Docredstein/TIPE_TMD/DM.pdf

# DM TIPE

BOCQUILLON No´e,FRAMBOURT Mate¨ıs

27 septembre 2022

Titre du TIPE : Mod´elisation et Simulation d’un amortisseur harmonique dans le cadre de la pr´evention sismique

## 1 Objectif du TIPE

Le but de ce TIPE est de mod´eliser un immeuble puis de concevoir un amortisseur harmonique pour limiter

1
