Docredstein/TIPE_TMD/Analyse finale basse amplitude/Image/coup_de_vent.pdf

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

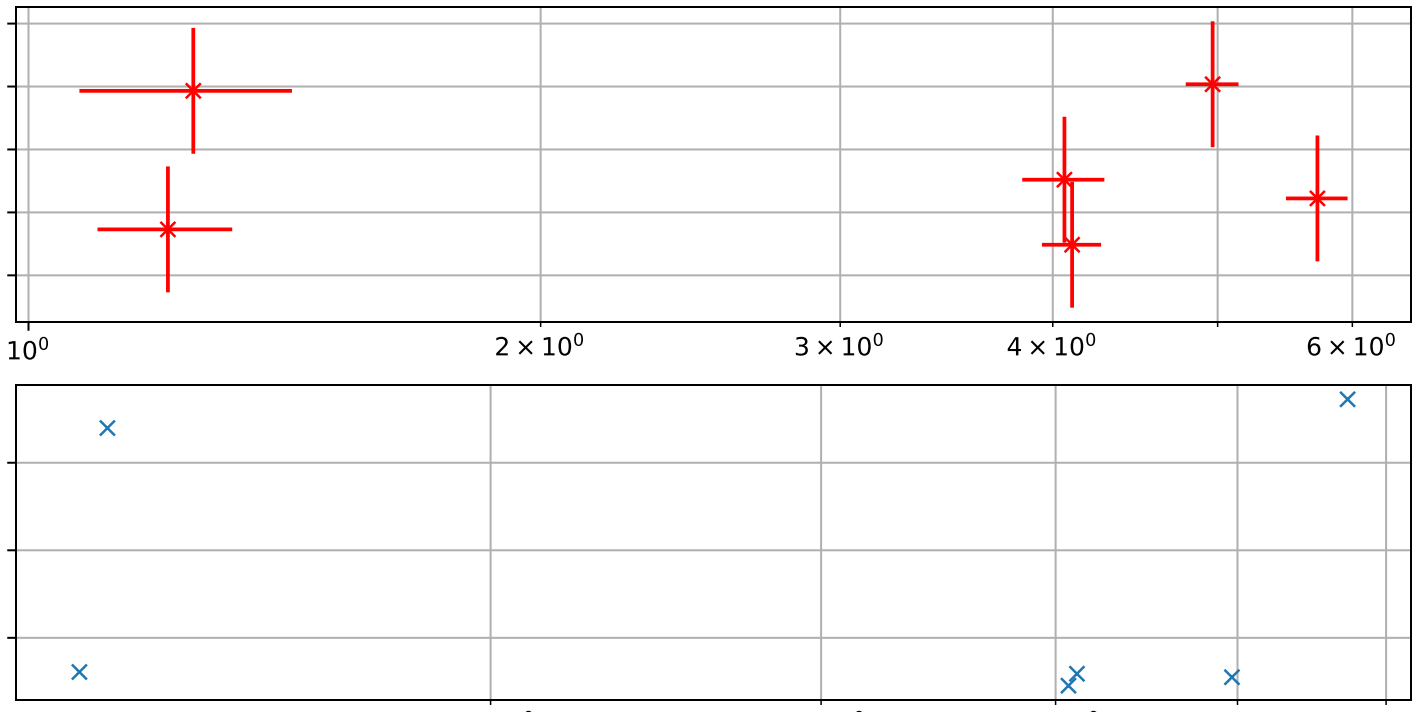
[picture p38: figure]
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
