Docredstein/TIPE_TMD/Analyse finale basse amplitude/Image/masse_en_bas_(9.4gcm)_de__100g.pdf

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

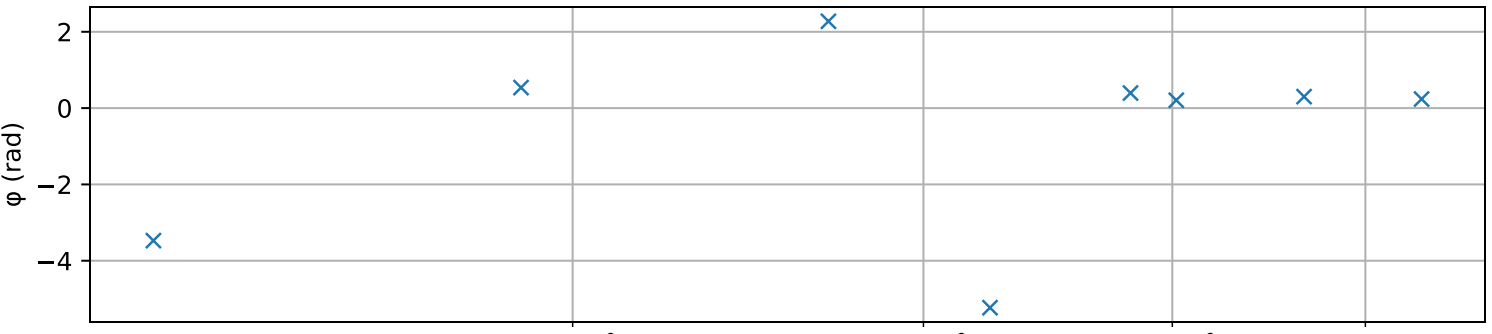
[picture p39: figure]
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
