Docredstein/TIPE_TMD/Analyse finale basse amplitude/Image/masse_à_3_cm_de_l'axe_de_100g.pdf

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

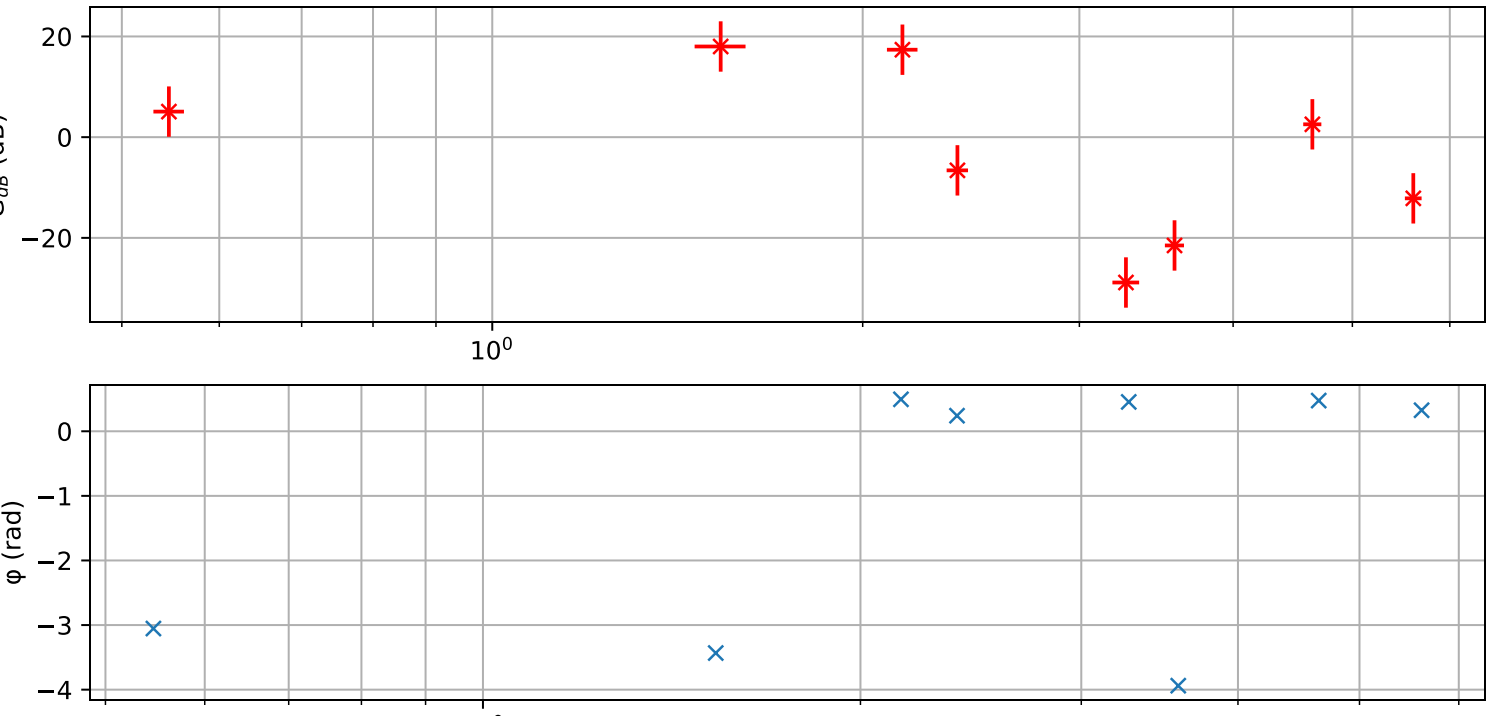
[picture p40: figure]
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
