Docredstein/TIPE_TMD/Analyse finale basse amplitude/Image/masse_à_5,5_cm_de_l'axe_de_73,3_g.pdf

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

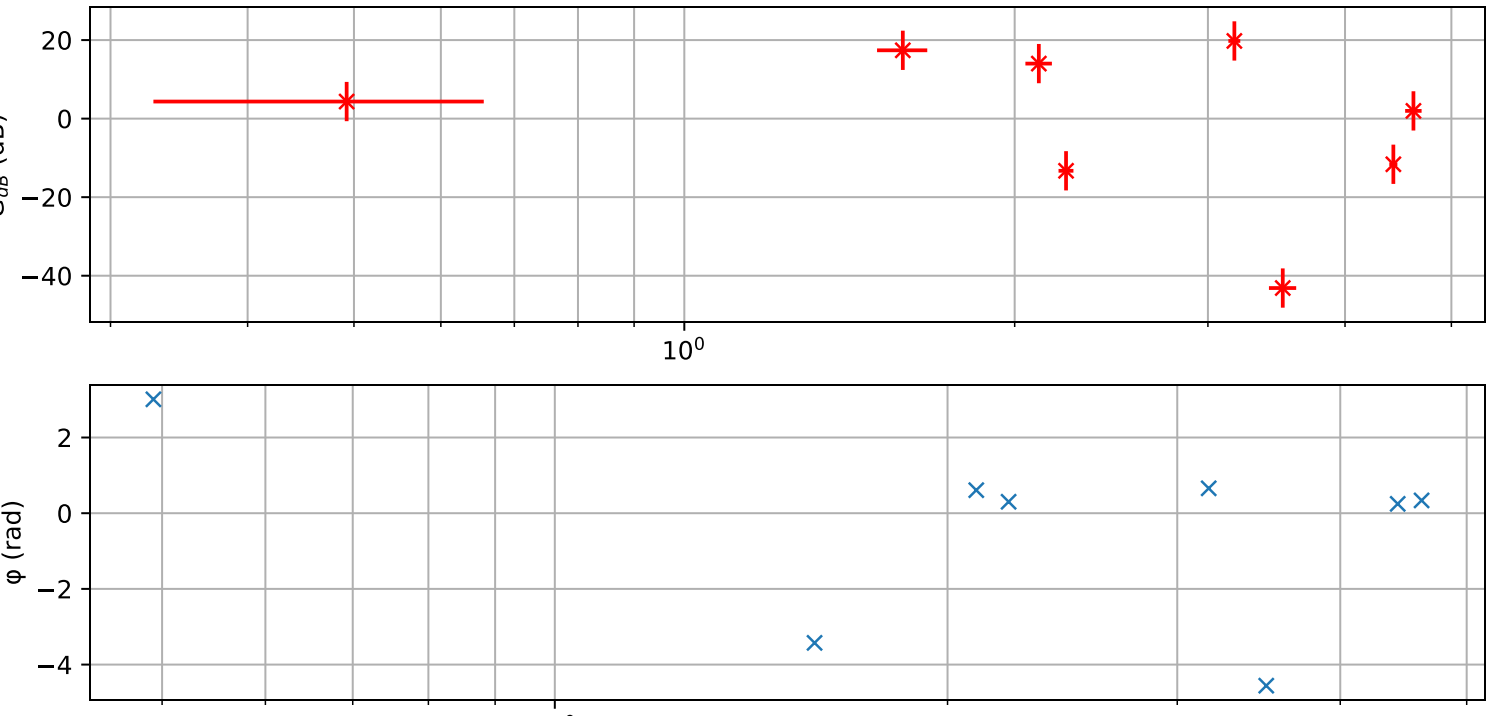
[picture p41: figure]
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
