Docredstein/TIPE_TMD/Analyse finale basse amplitude/Image/masse_à_8cm_de_73,3_g.pdf

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

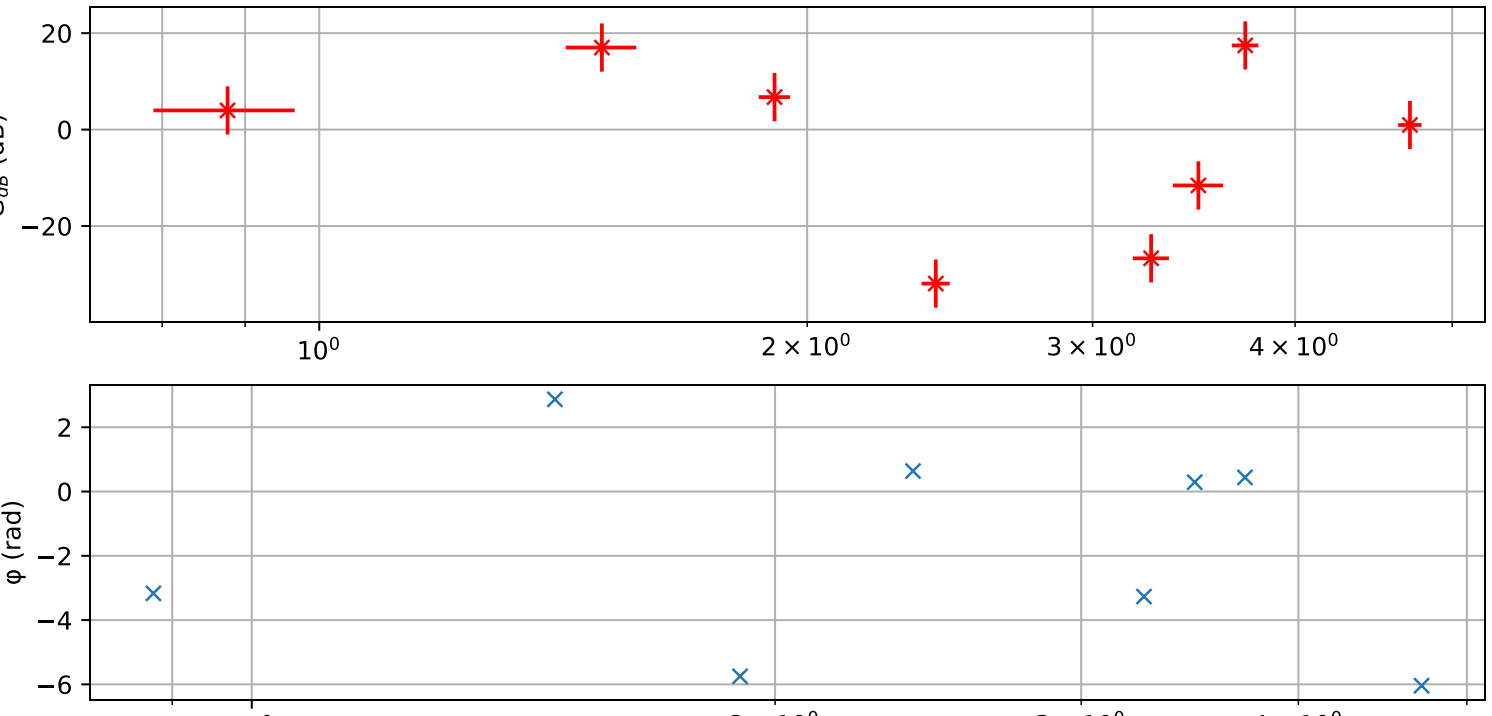
[picture p42: figure]
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
