Docredstein/TIPE_TMD/Analyse finale basse amplitude/Image/masse_à_9.4_cm_de_73,3g_de_l'axe.pdf

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

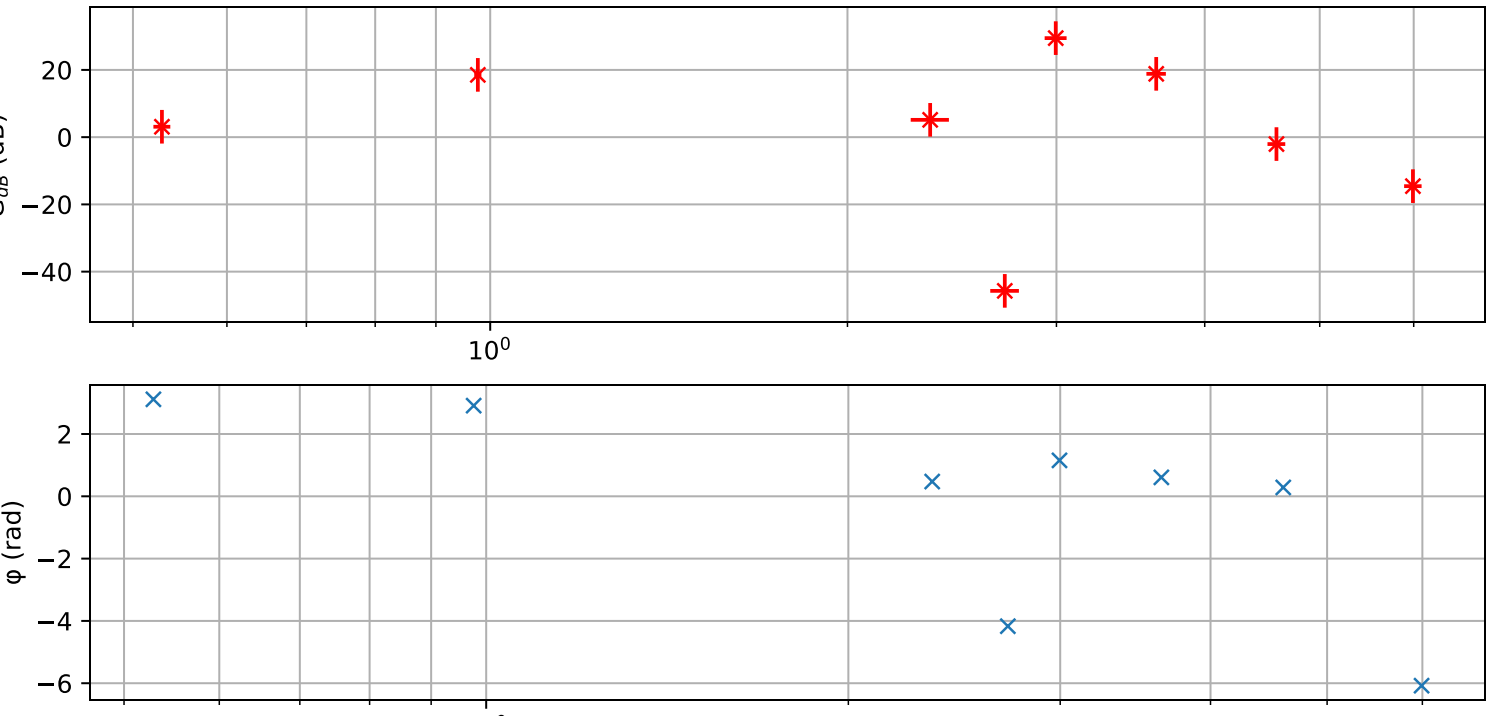
[picture p43: figure]
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
