Docredstein/TIPE_TMD/Analyse finale basse amplitude/Image/sans_pendule.pdf

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

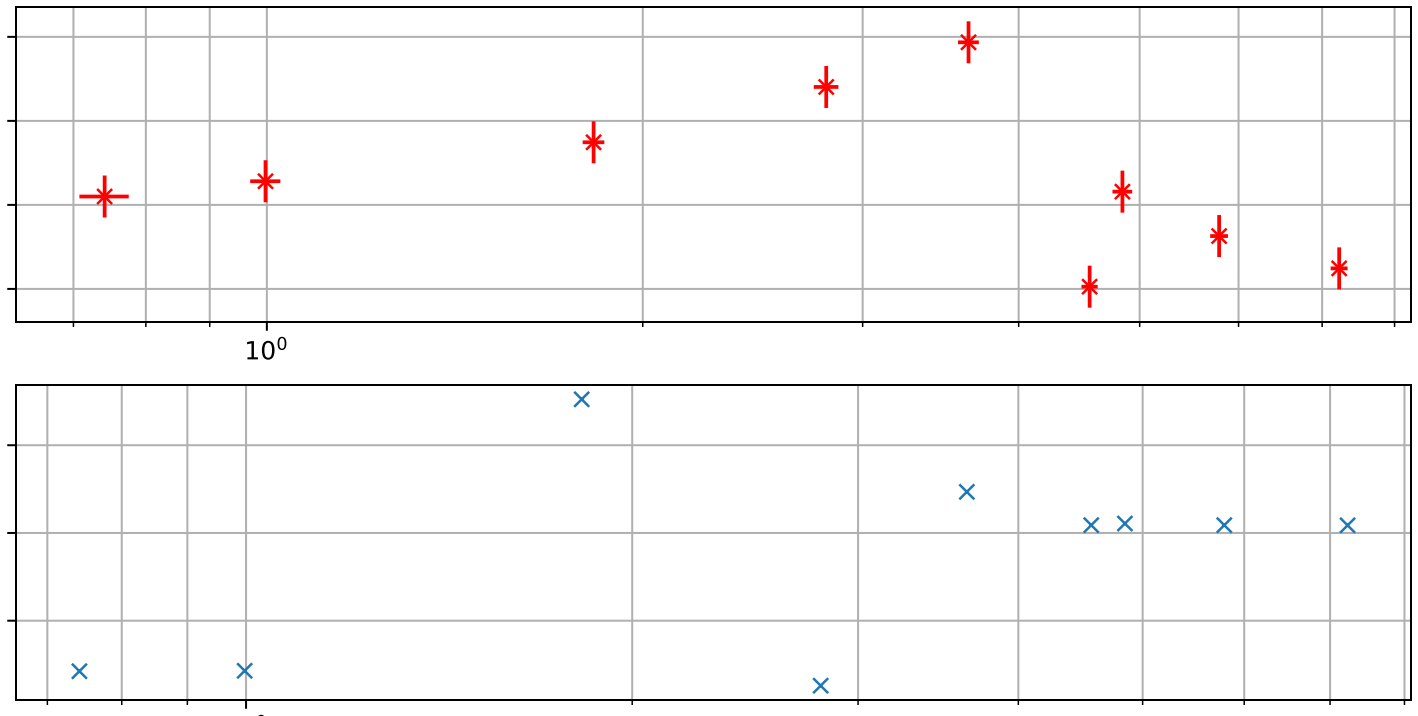
[picture p45: figure]
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
