Docredstein/TIPE_TMD/Beamer/Image/masse_à_8cm_de_73,3_g.pdf

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

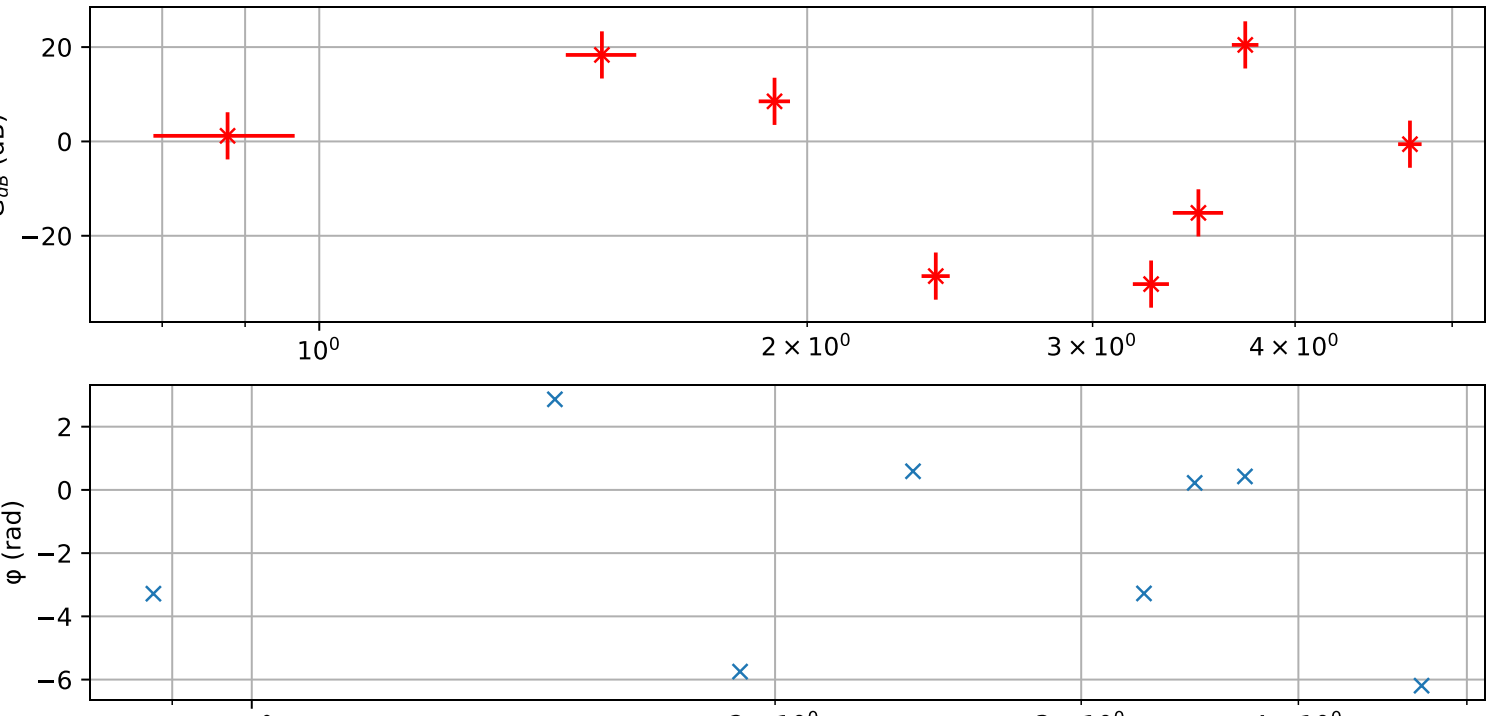
[picture p47: figure]
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
