Docredstein/TIPE_TMD/Beamer/Image/pendule_à_5_cm_de_l'axe_,_100g.pdf

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

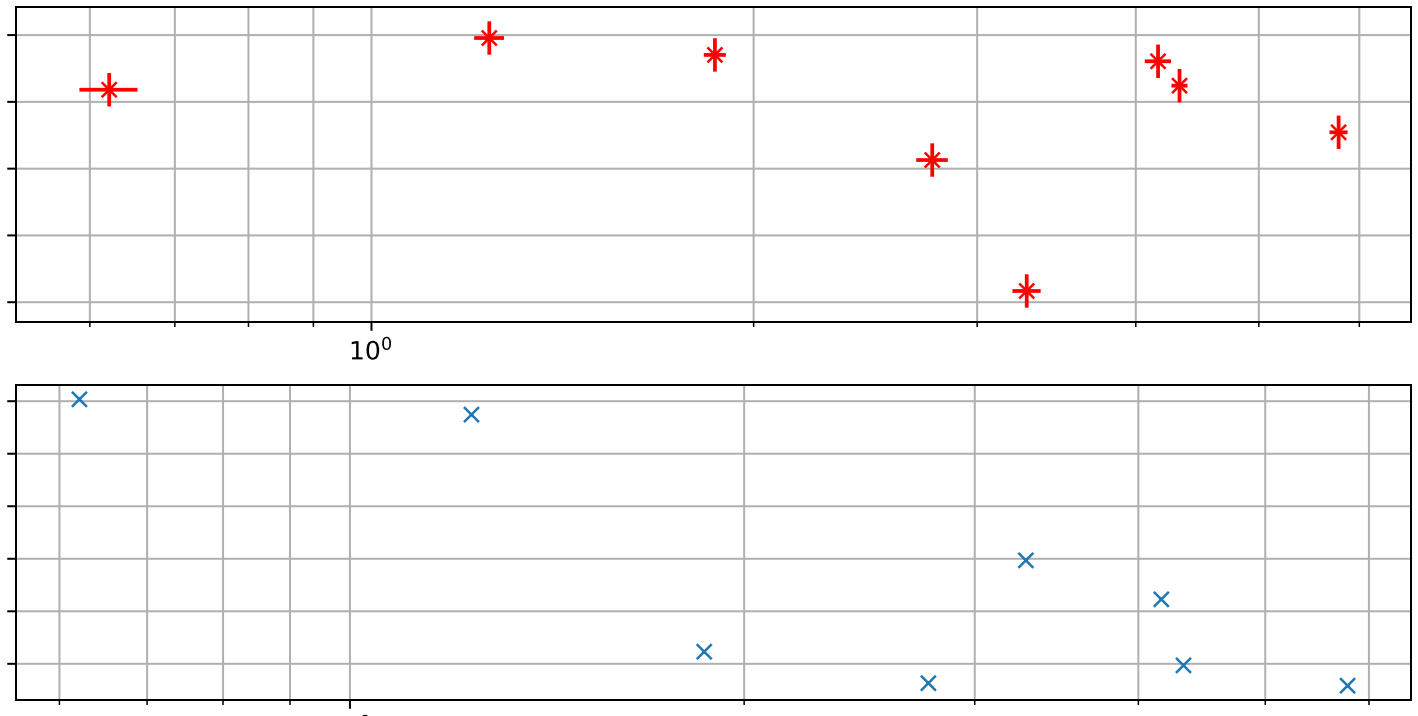
[picture p48: figure]
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
