Docredstein/TIPE_TMD/Analyse/Image/pendule_1_masse_au_plus_bas.pdf

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

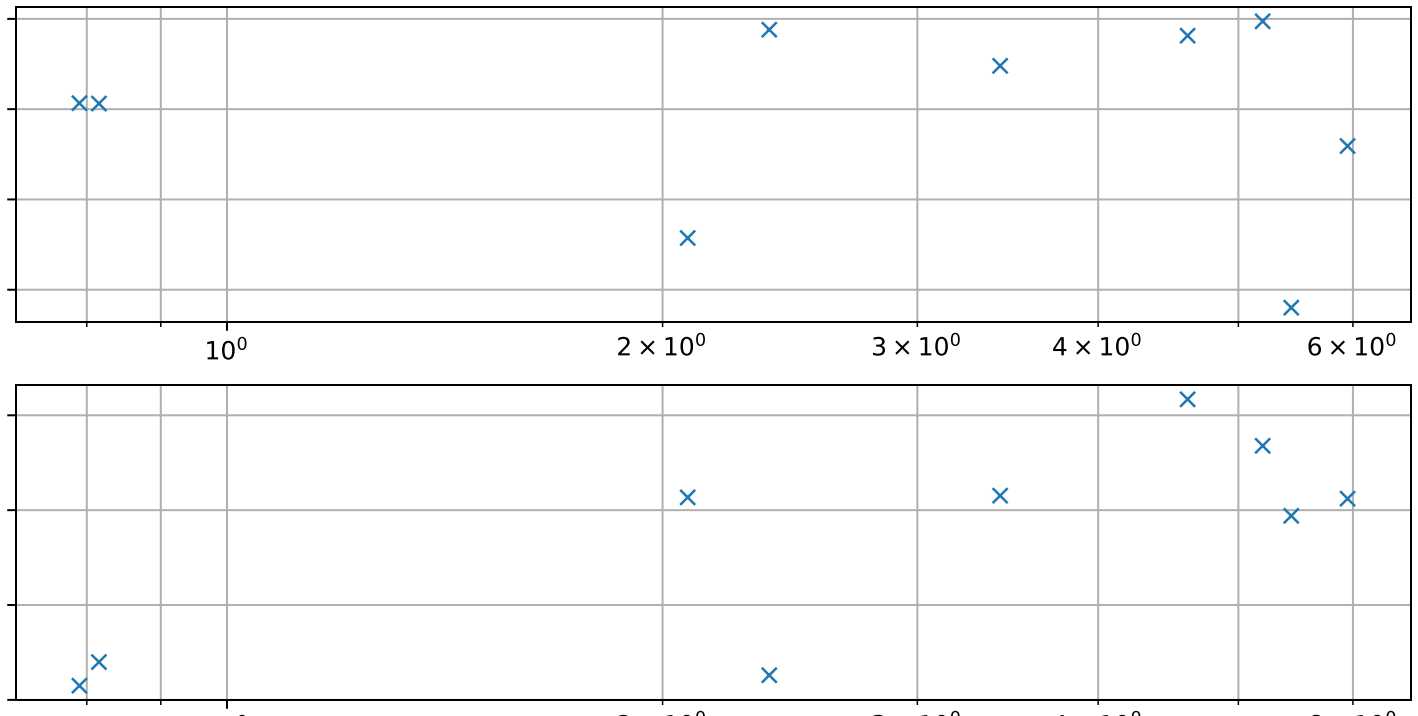
[picture p50: figure]
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
