Docredstein/TIPE_TMD/Analyse/Image/pendule_7_mm_faible_amplitude.pdf

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

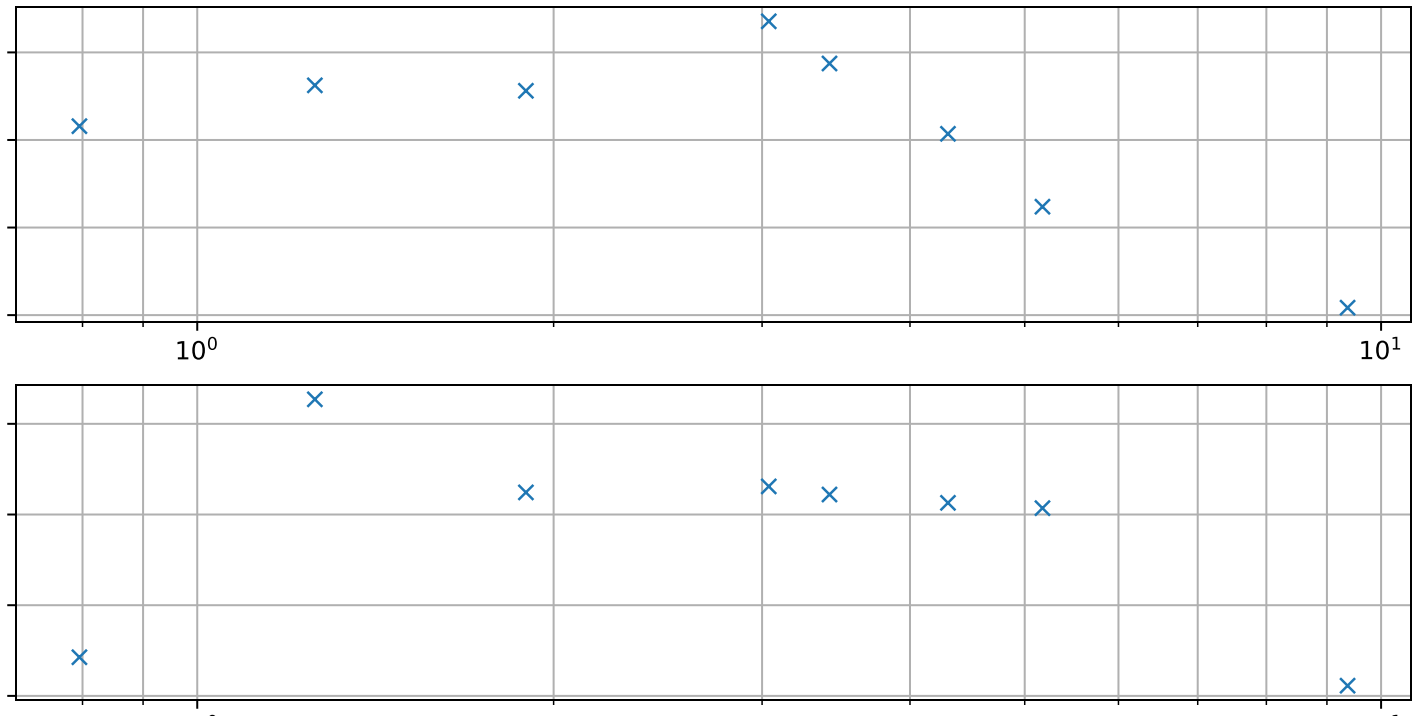
[picture p52: figure]
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
