Docredstein/TIPE_TMD/Analyse/Image/pendule_au_plus_bas_faible_amplitude.pdf

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

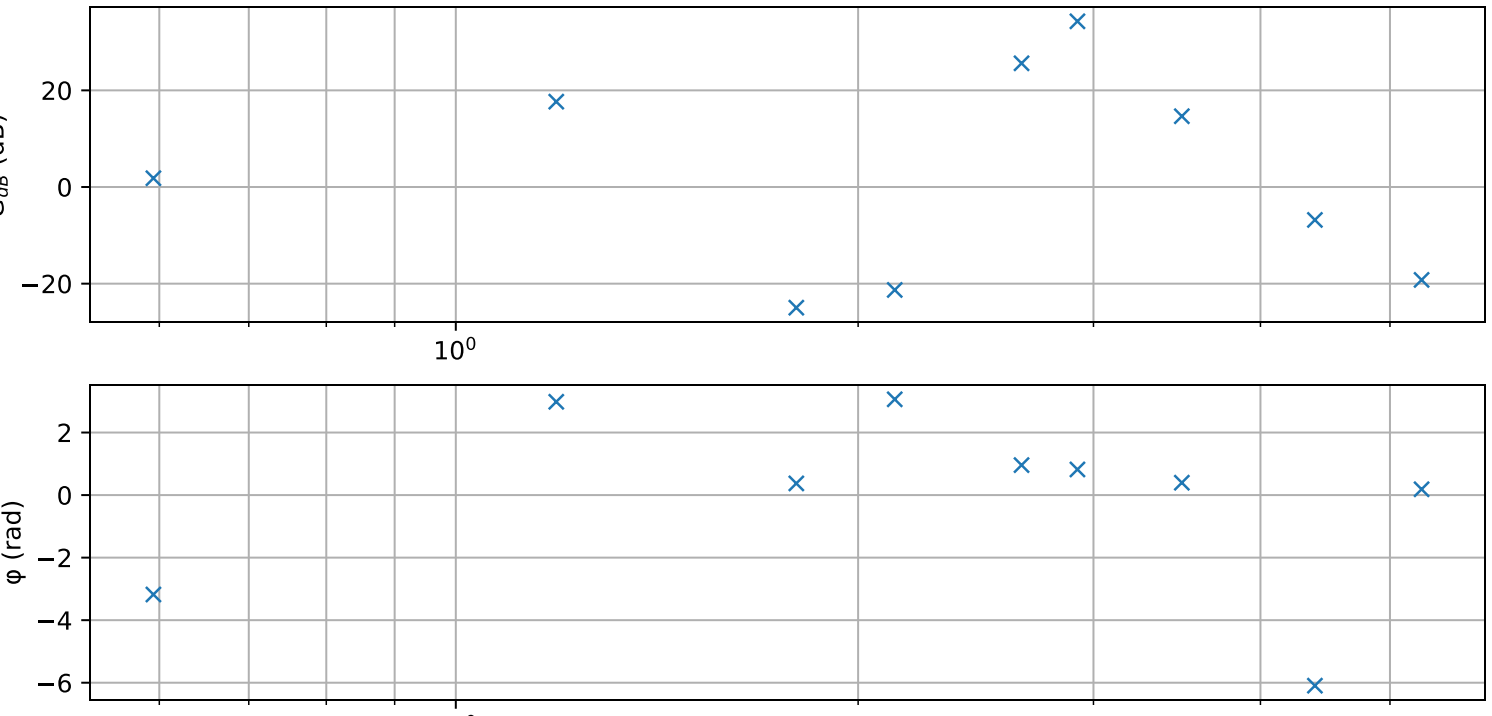
[picture p53: figure]
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
