Docredstein/TIPE_TMD/Analyse/Image/penduleb_7mm_sans_pendule_faible_amplitude.pdf

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

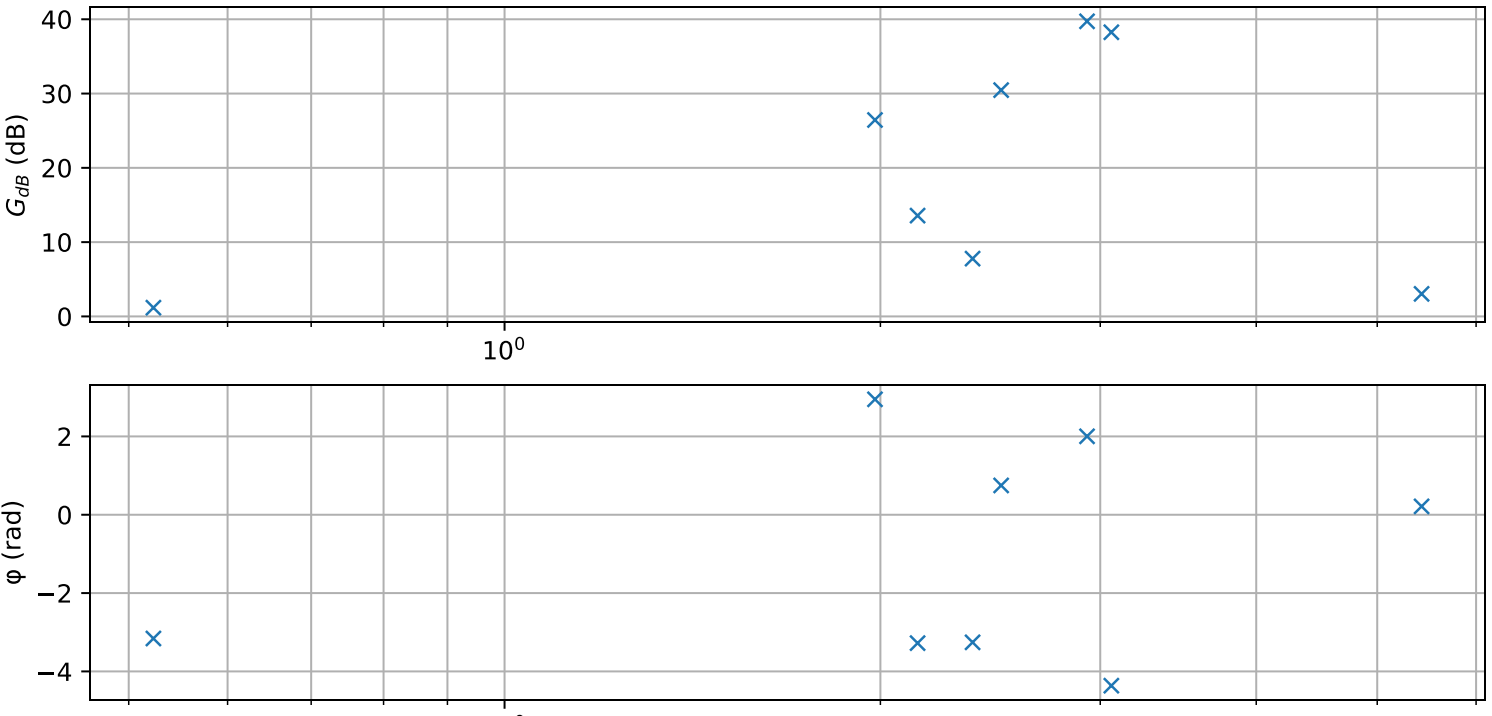
[picture p54: figure]
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
