Docredstein/TIPE_TMD/Analyse/Image/Sans_masse,_tige_seule_faible_amplitude.pdf

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

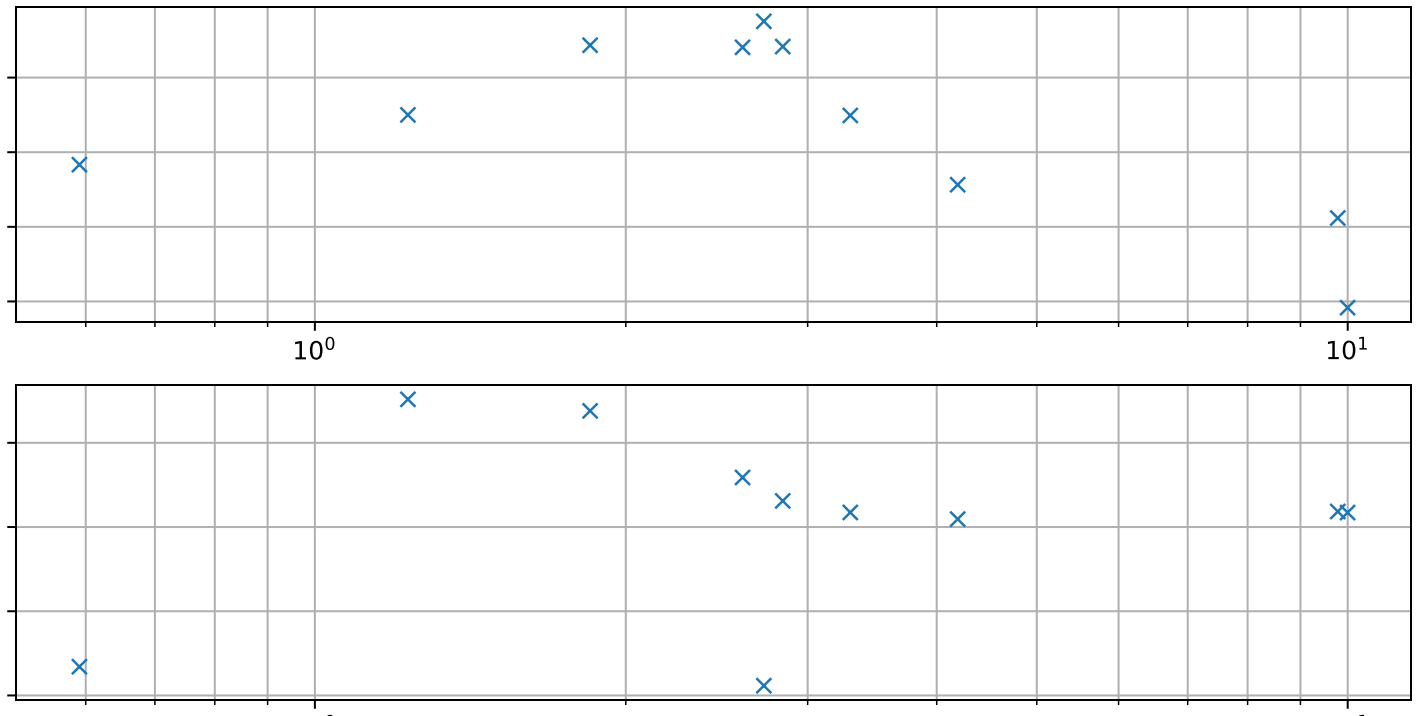
[picture p55: figure]
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
