Docredstein/TIPE_TMD/Analyse/Image/masse_en_haut_faible_amplitude_norme.pdf

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

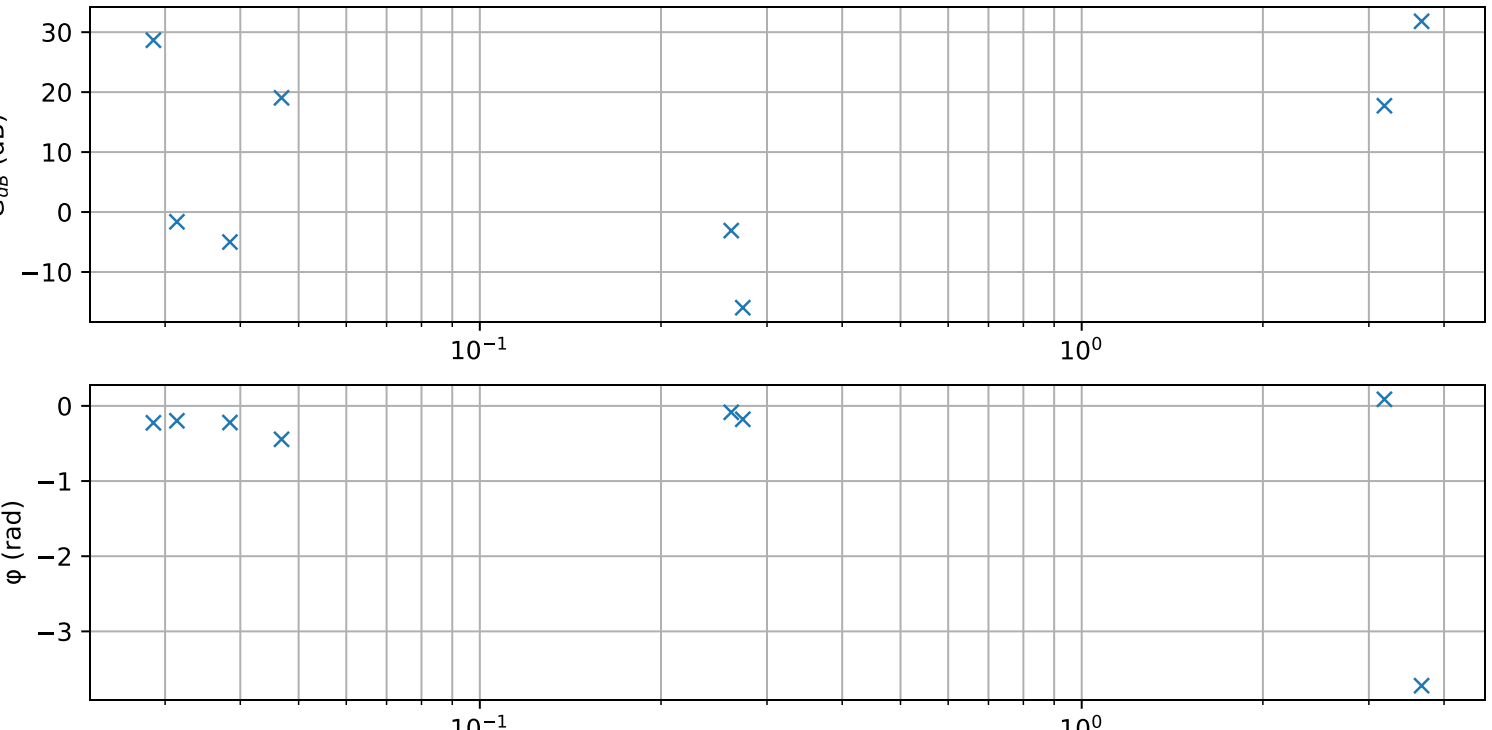
[picture p56: figure]
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
