Docredstein/TIPE_TMD/Analyse/Image/pendule_7_cm_du_haut_pendule_fixe_axe_norme.pdf

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

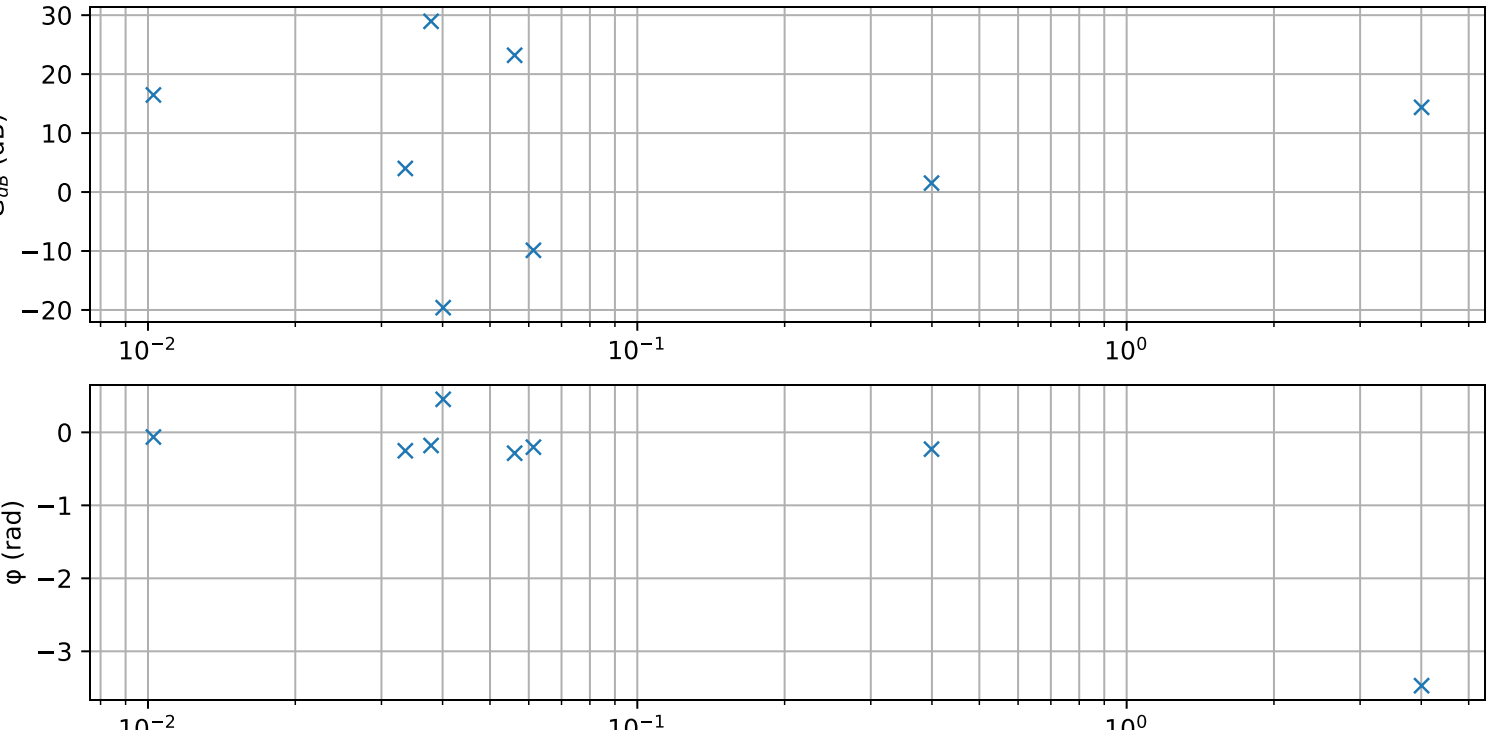
[picture p58: figure]
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
