Docredstein/TIPE_TMD/Analyse/Image/pendule_au_plus_bas_faible_amplitude_norme.pdf

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

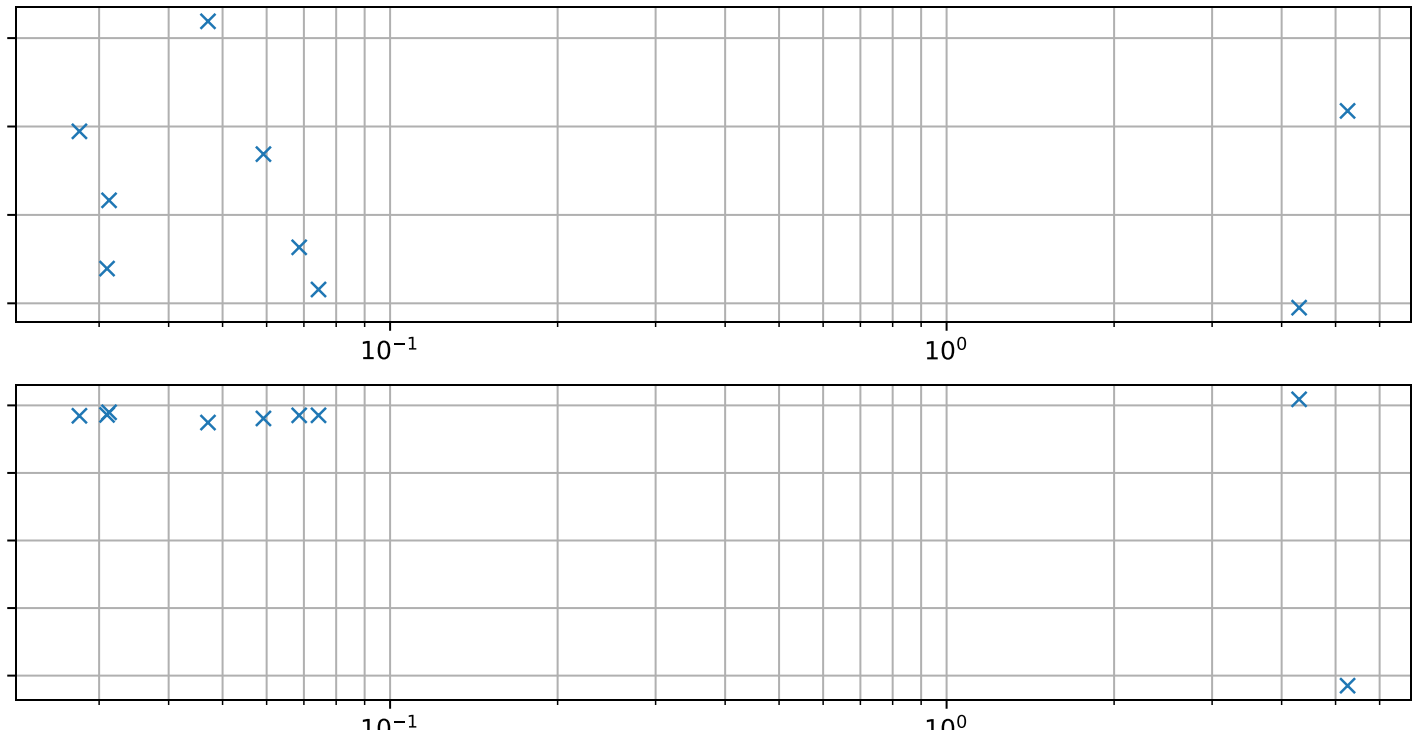
[picture p60: figure]
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
