Docredstein/TIPE_TMD/Analyse/Image/penduleb_7mm_sans_pendule_faible_amplitude_norme.pdf

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

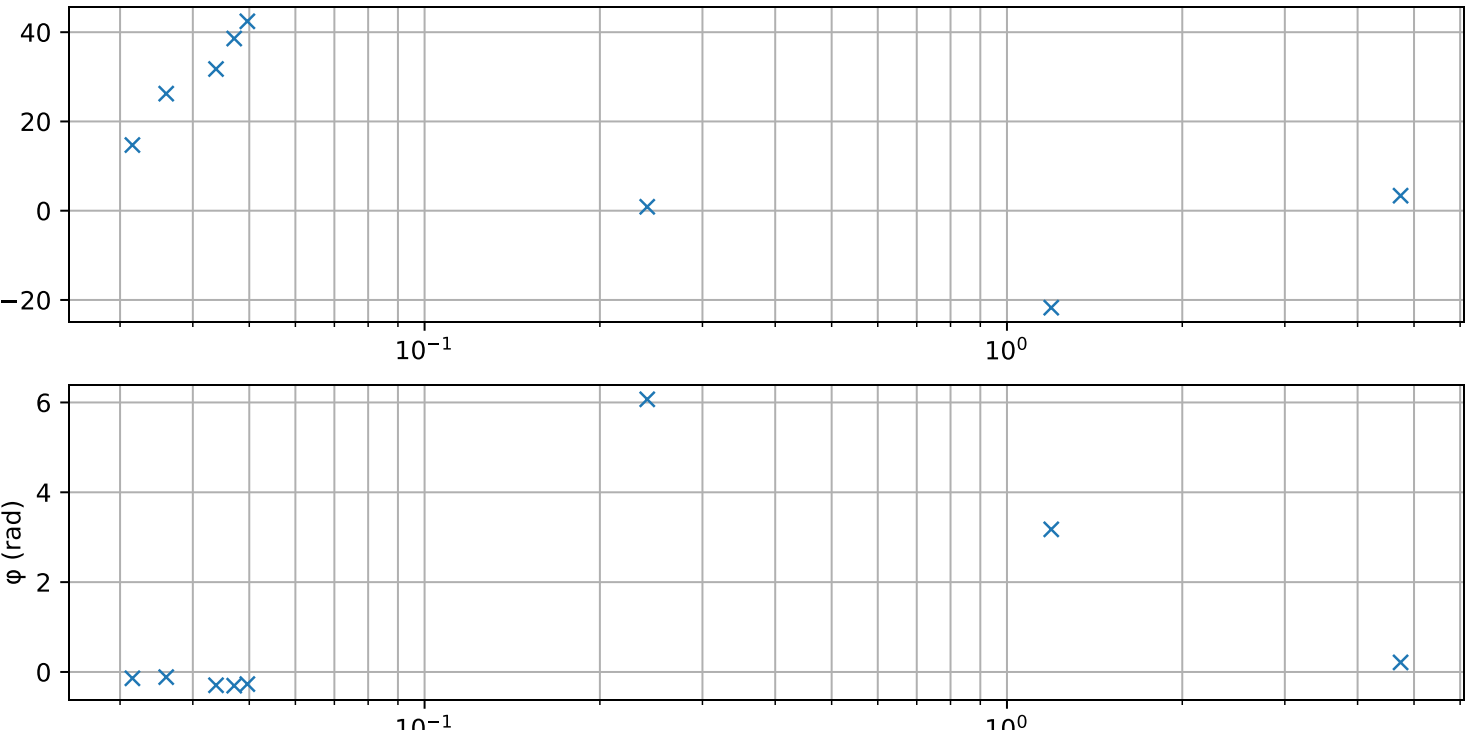
[picture p61: figure]
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
