Docredstein/TIPE_TMD/Analyse/Image/Sans_masse,_tige_seule_faible_amplitude_norme.pdf

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

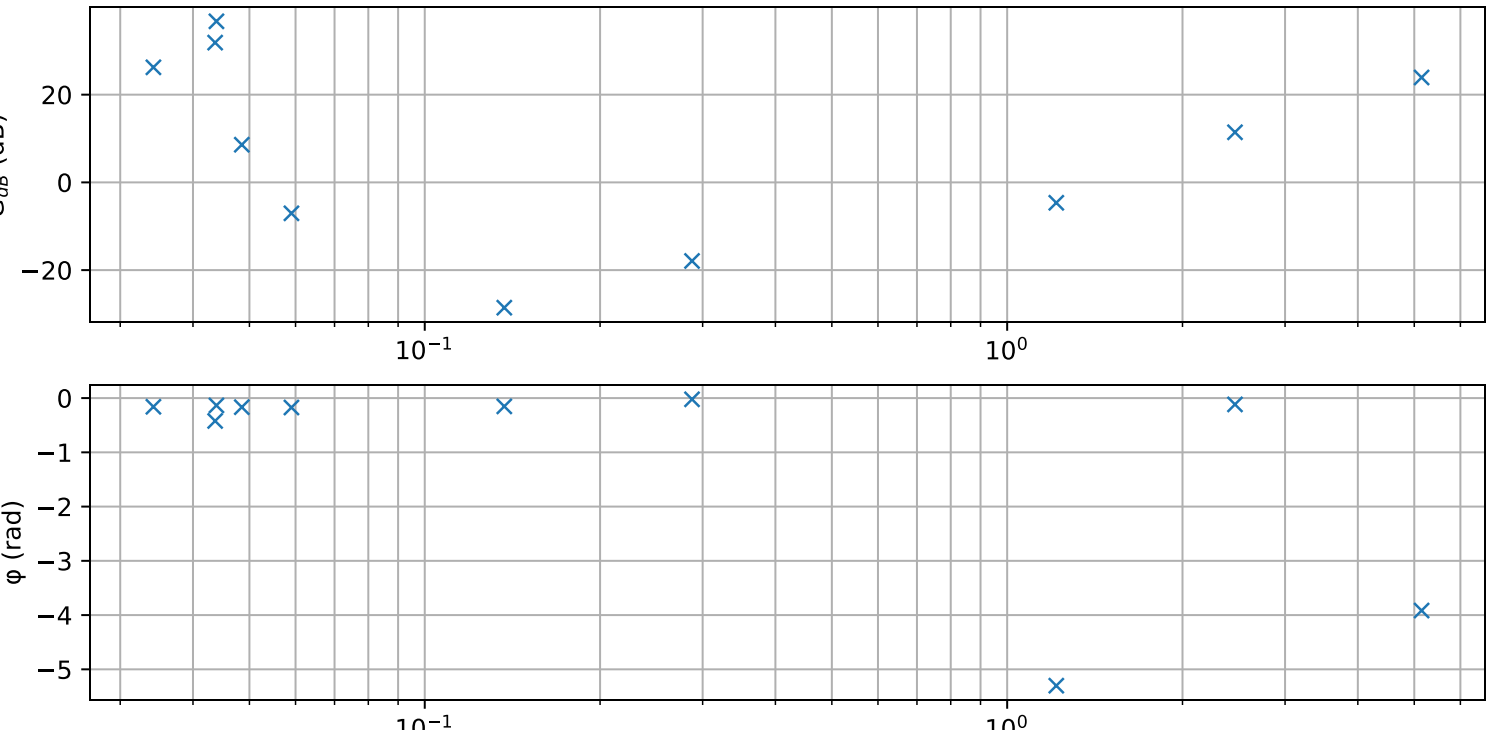
[picture p62: figure]
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
