Docredstein/TIPE_TMD/Analyse/Image/Bode a Vide/0.3Hz.png

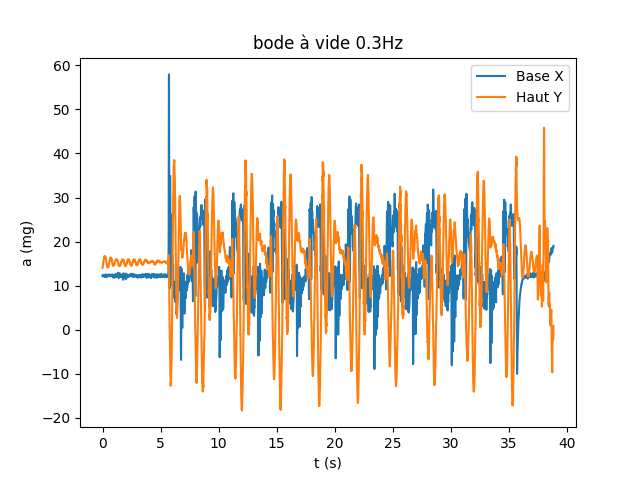
Analyse/Image/Bode a Vide/0.3Hz.png
