Docredstein/TIPE_TMD/Analyse/Image/Bode a Vide/0.5Hz.png

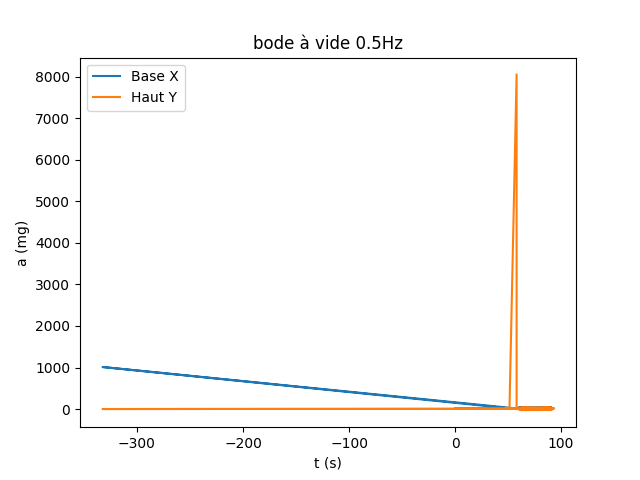
Analyse/Image/Bode a Vide/0.5Hz.png
