Docredstein/TIPE_TMD/Analyse/Image/Bode a Vide/1.5Hz.png

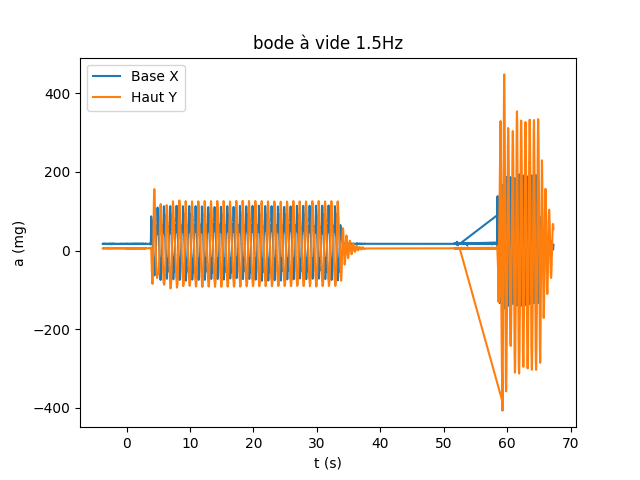
Analyse/Image/Bode a Vide/1.5Hz.png
