Docredstein/TIPE_TMD/Analyse/Image/Bode a Vide/1.6Hz.png

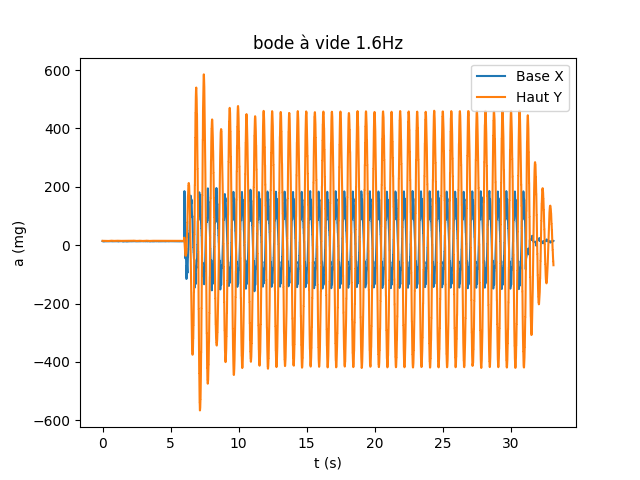
Analyse/Image/Bode a Vide/1.6Hz.png
