Docredstein/TIPE_TMD/Analyse/Image/Bode a Vide/1.7Hz.png

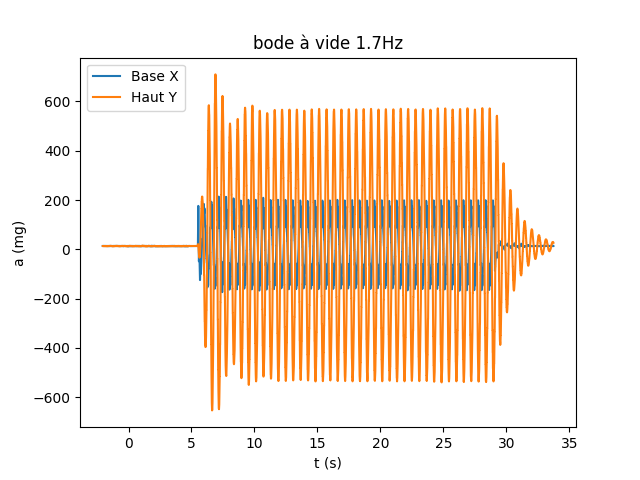
Analyse/Image/Bode a Vide/1.7Hz.png
