Docredstein/TIPE_TMD/Analyse/Image/Bode a Vide/2.5Hz.png

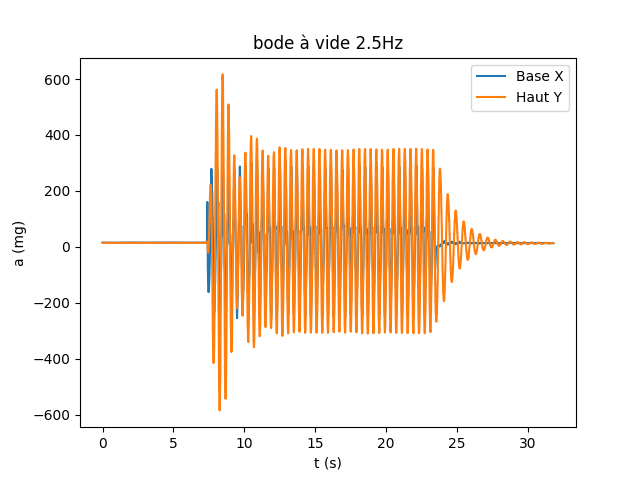
Analyse/Image/Bode a Vide/2.5Hz.png
