Docredstein/TIPE_TMD/Analyse/Image/Bode a Vide/3.5Hz.png

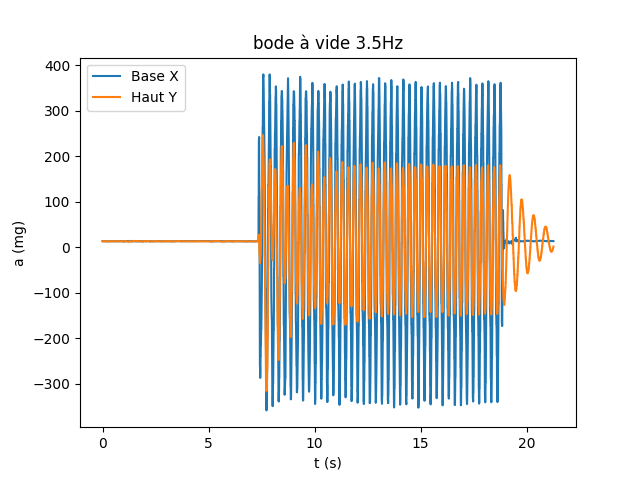
Analyse/Image/Bode a Vide/3.5Hz.png
