Docredstein/TIPE_TMD/Analyse/Image/Bode a Vide/4Hz.png

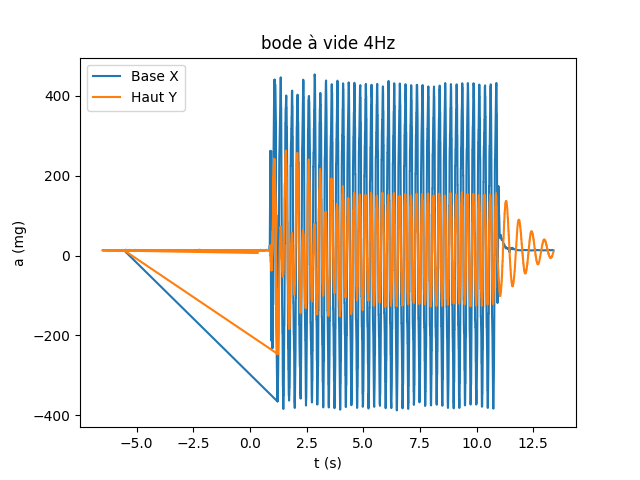
Analyse/Image/Bode a Vide/4Hz.png
