Docredstein/TIPE_TMD/Analyse/Image/Bode_a_vide.png

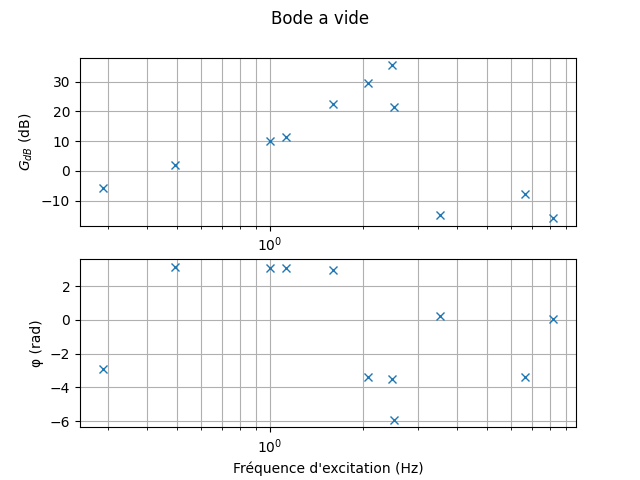
Analyse/Image/Bode_a_vide.png
