Docredstein/TIPE_TMD/Analyse/Image/masse en haut faible amplitude/0.5Hz.png

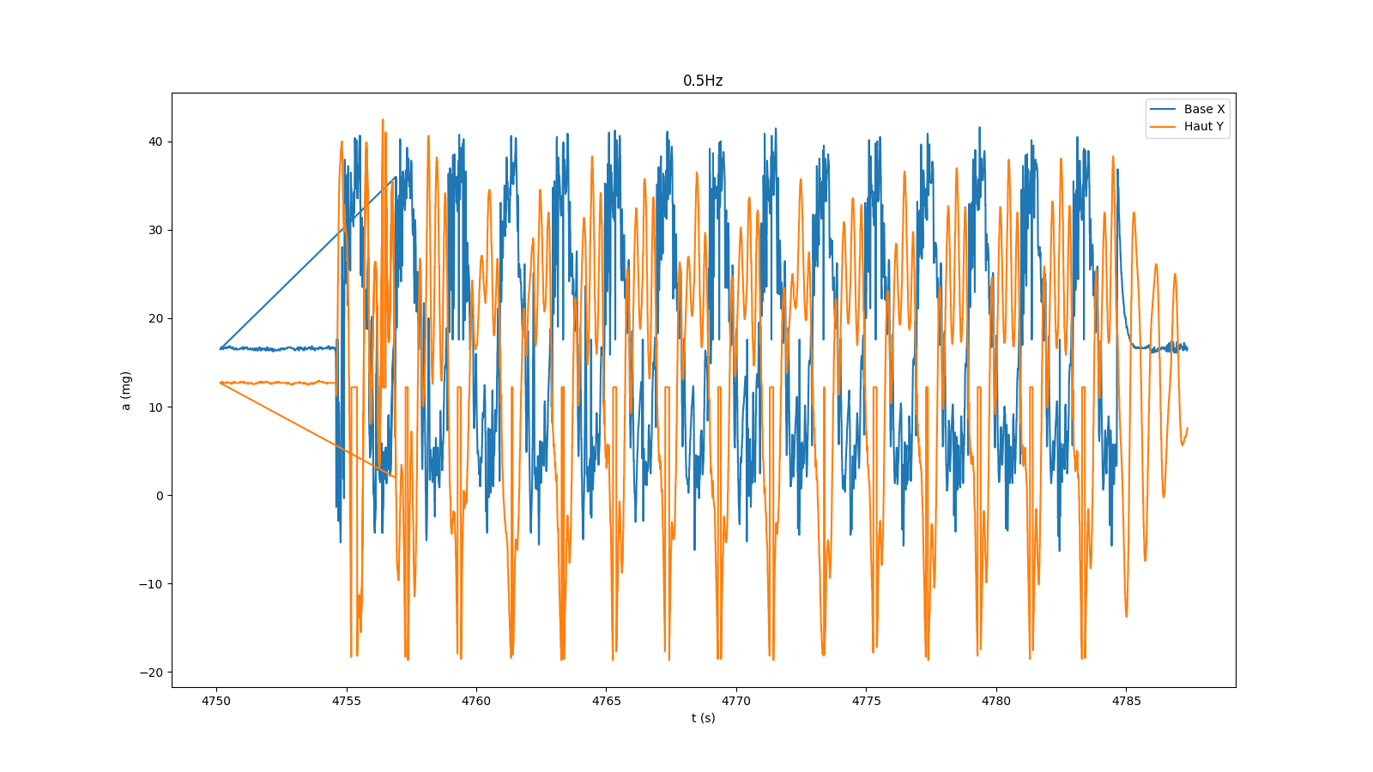
Analyse/Image/masse en haut faible amplitude/0.5Hz.png
