Docredstein/TIPE_TMD/Analyse/Image/masse en haut faible amplitude/1 hz.png

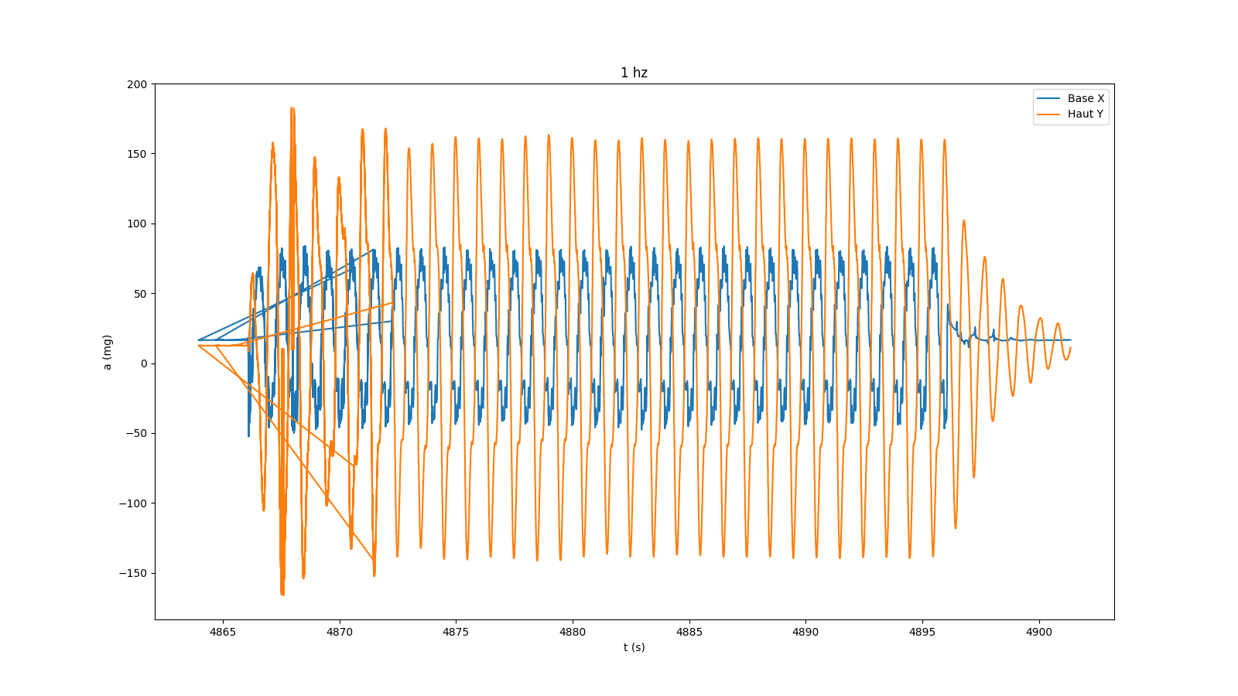
Analyse/Image/masse en haut faible amplitude/1 hz.png
