Docredstein/TIPE_TMD/Analyse/Image/masse en haut faible amplitude/1.3 hz.png

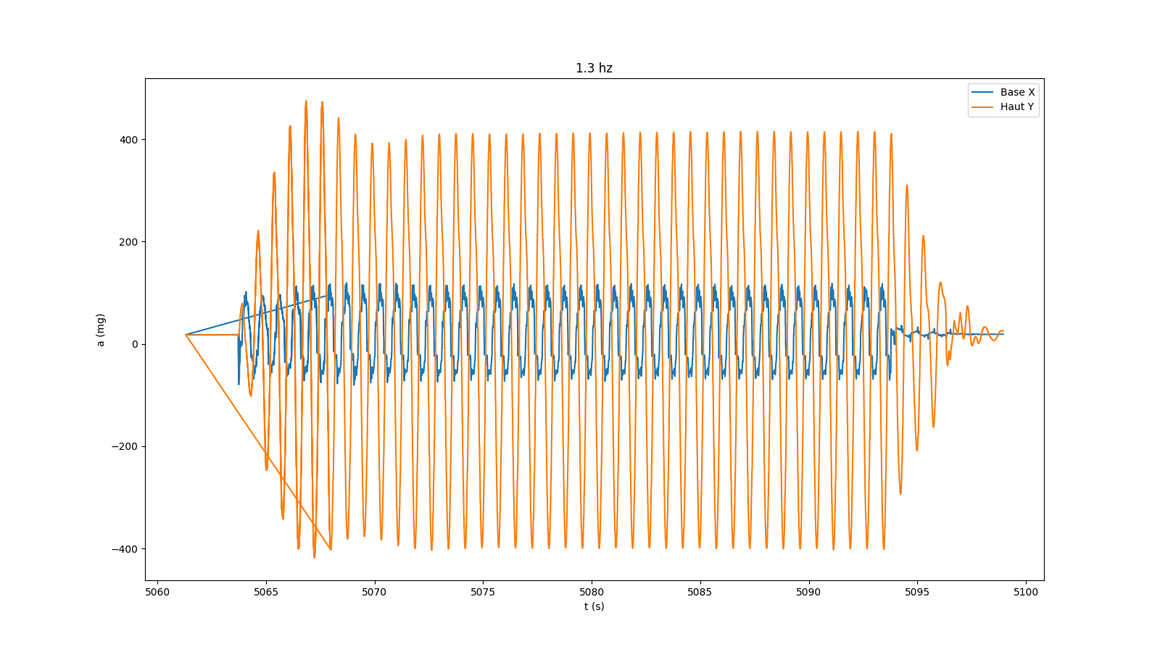
Analyse/Image/masse en haut faible amplitude/1.3 hz.png
