Docredstein/TIPE_TMD/Analyse/Image/masse en haut faible amplitude/1.5 hz (décalage).png

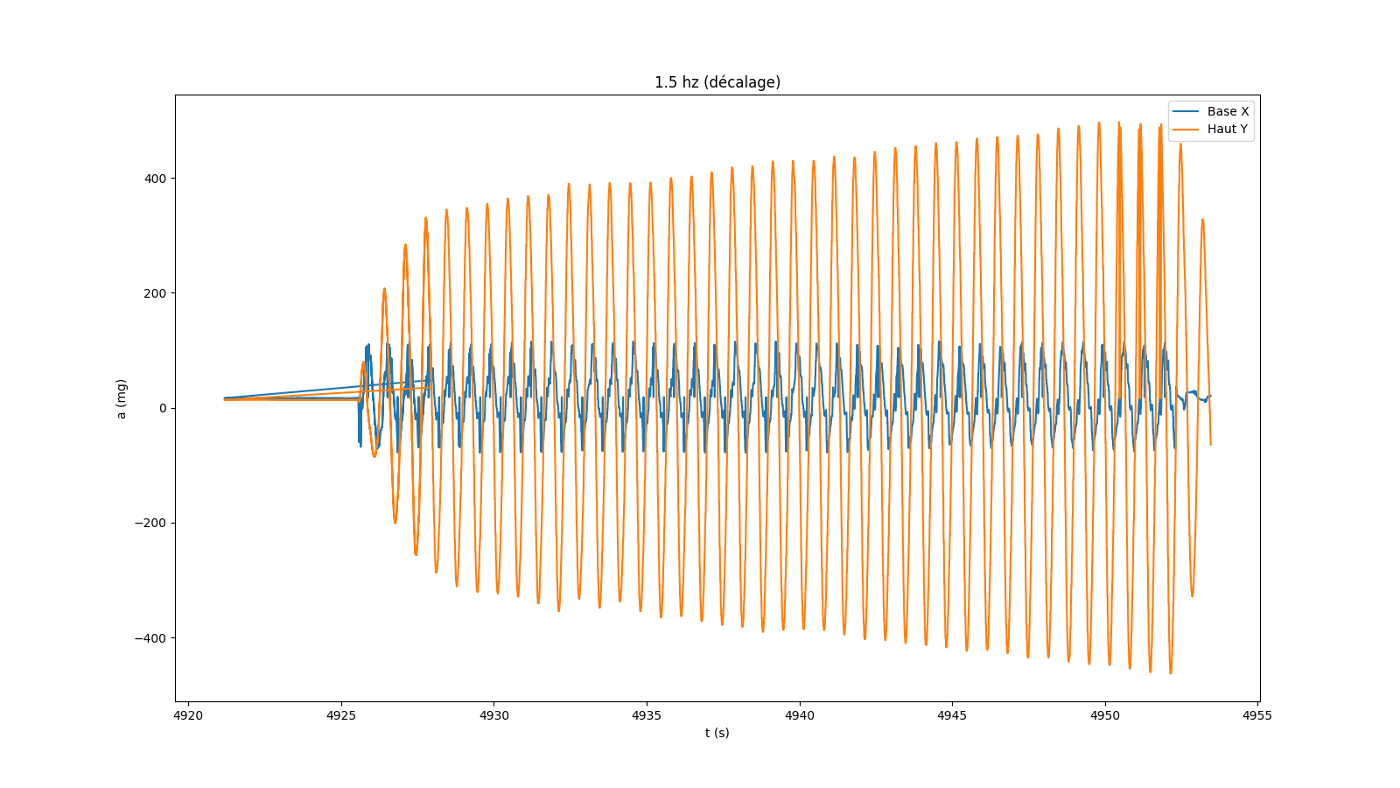
Analyse/Image/masse en haut faible amplitude/1.5 hz (décalage).png
