Docredstein/TIPE_TMD/Analyse/Image/masse en haut faible amplitude/2.5 hz.png

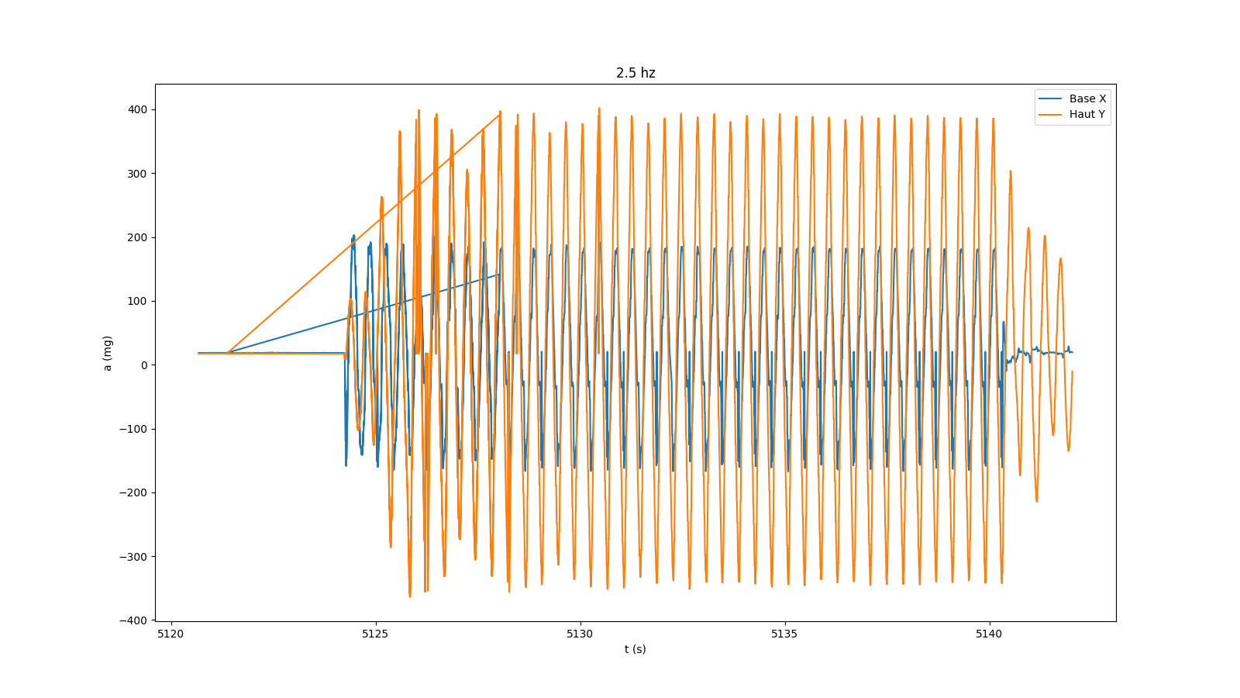
Analyse/Image/masse en haut faible amplitude/2.5 hz.png
