Docredstein/TIPE_TMD/Analyse/Image/masse en haut faible amplitude/3.5 hz.png

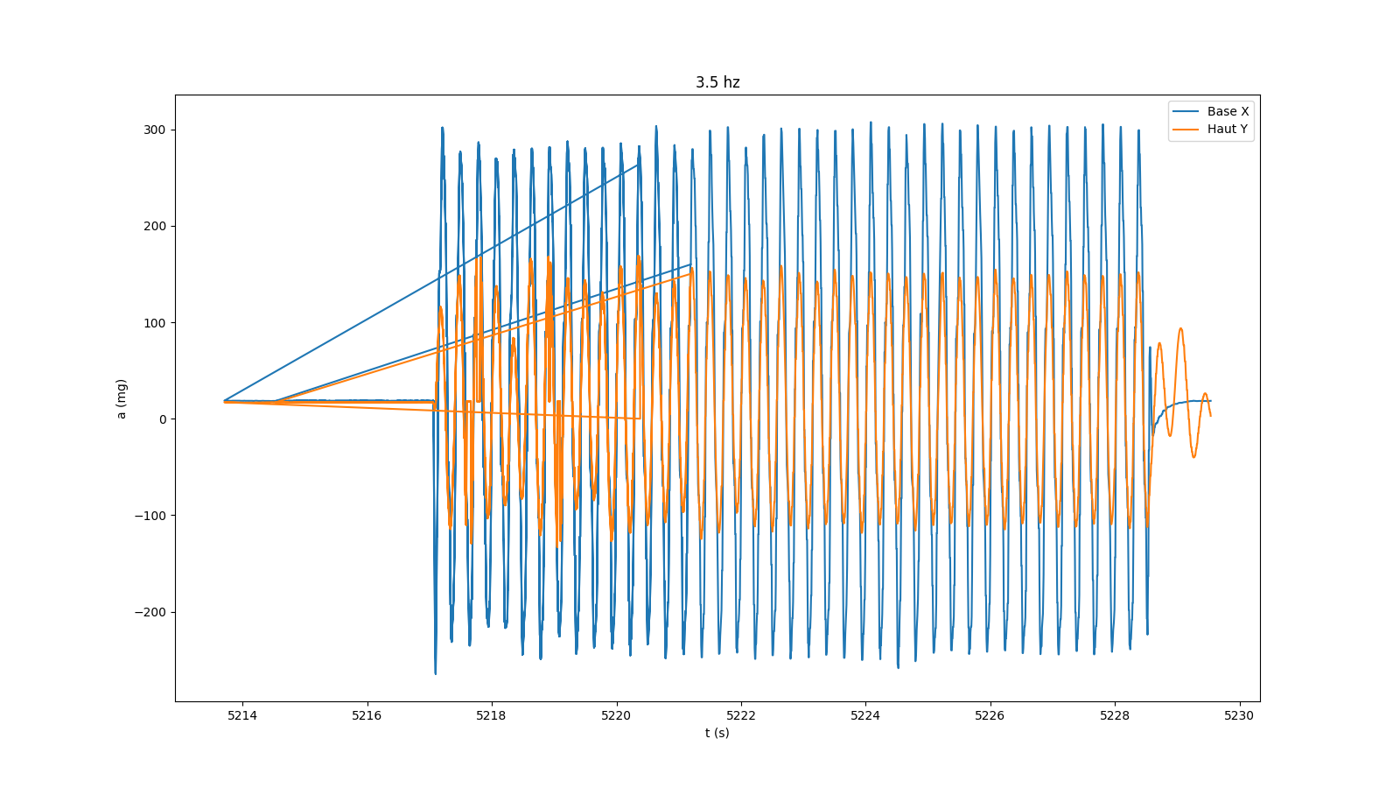
Analyse/Image/masse en haut faible amplitude/3.5 hz.png
