Docredstein/TIPE_TMD/Analyse/Image/masse_en_haut_faible_amplitude.png

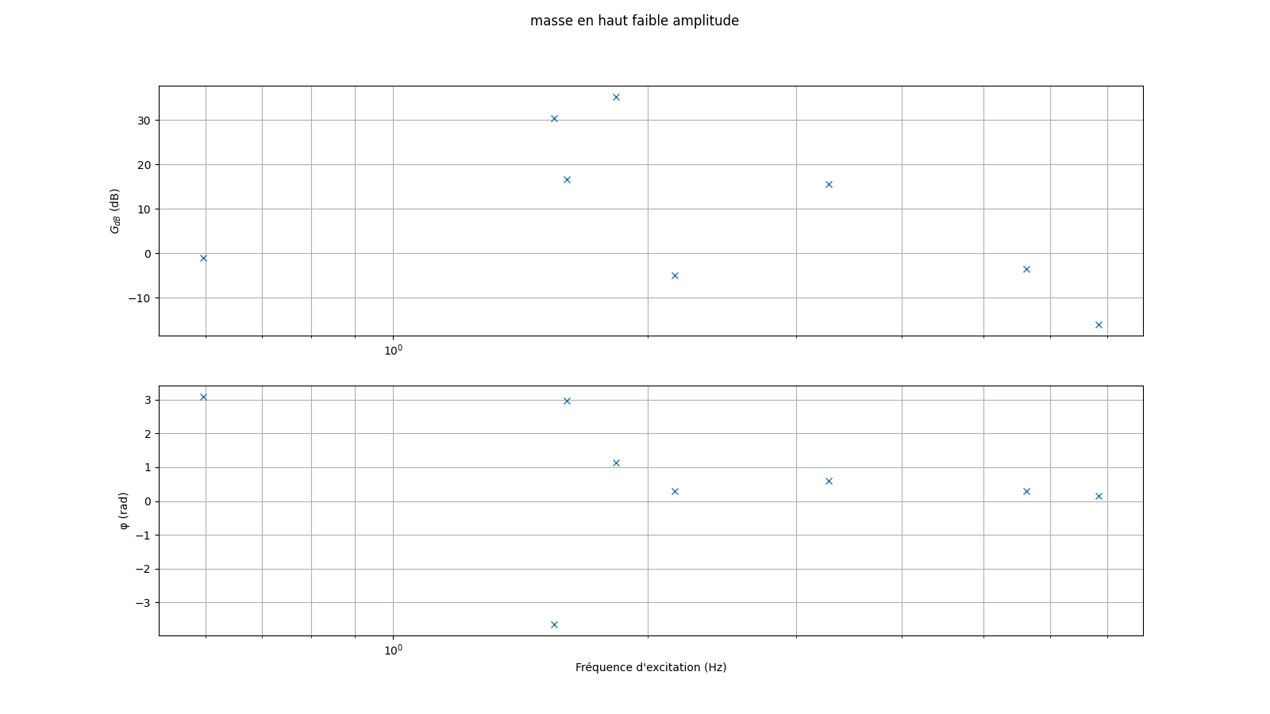
Analyse/Image/masse_en_haut_faible_amplitude.png
