Docredstein/TIPE_TMD/Analyse/Image/pendule 1 masse au plus bas/0.5 hz.png

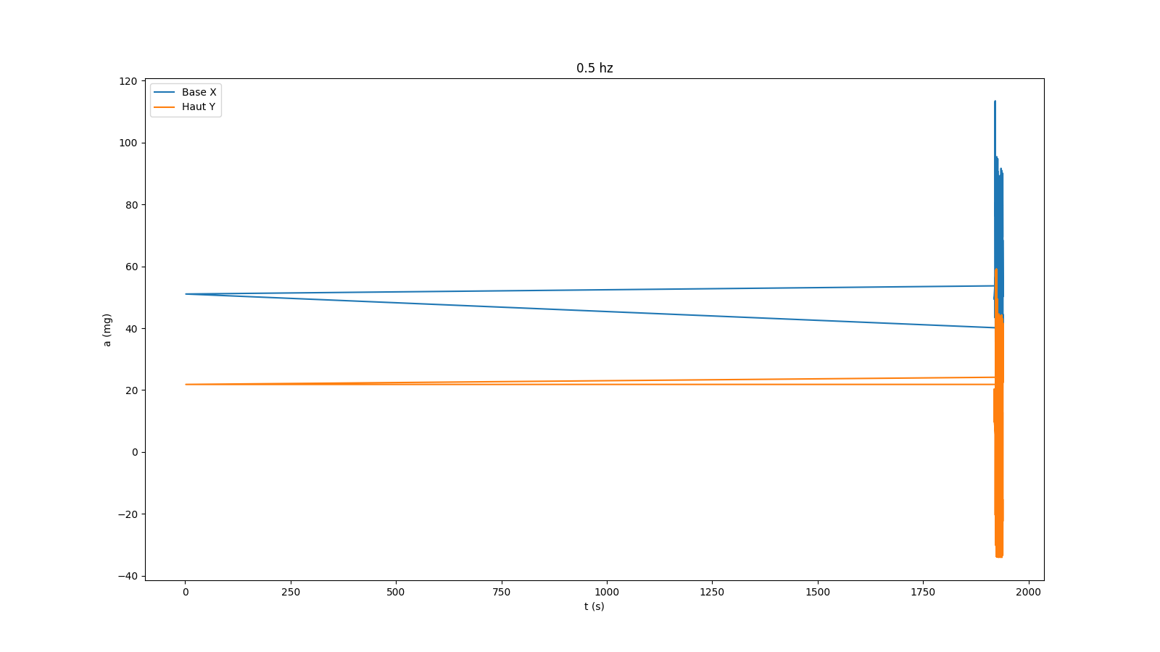
Analyse/Image/pendule 1 masse au plus bas/0.5 hz.png
