Docredstein/TIPE_TMD/Analyse/Image/pendule 1 masse au plus bas/1.5Hz.png

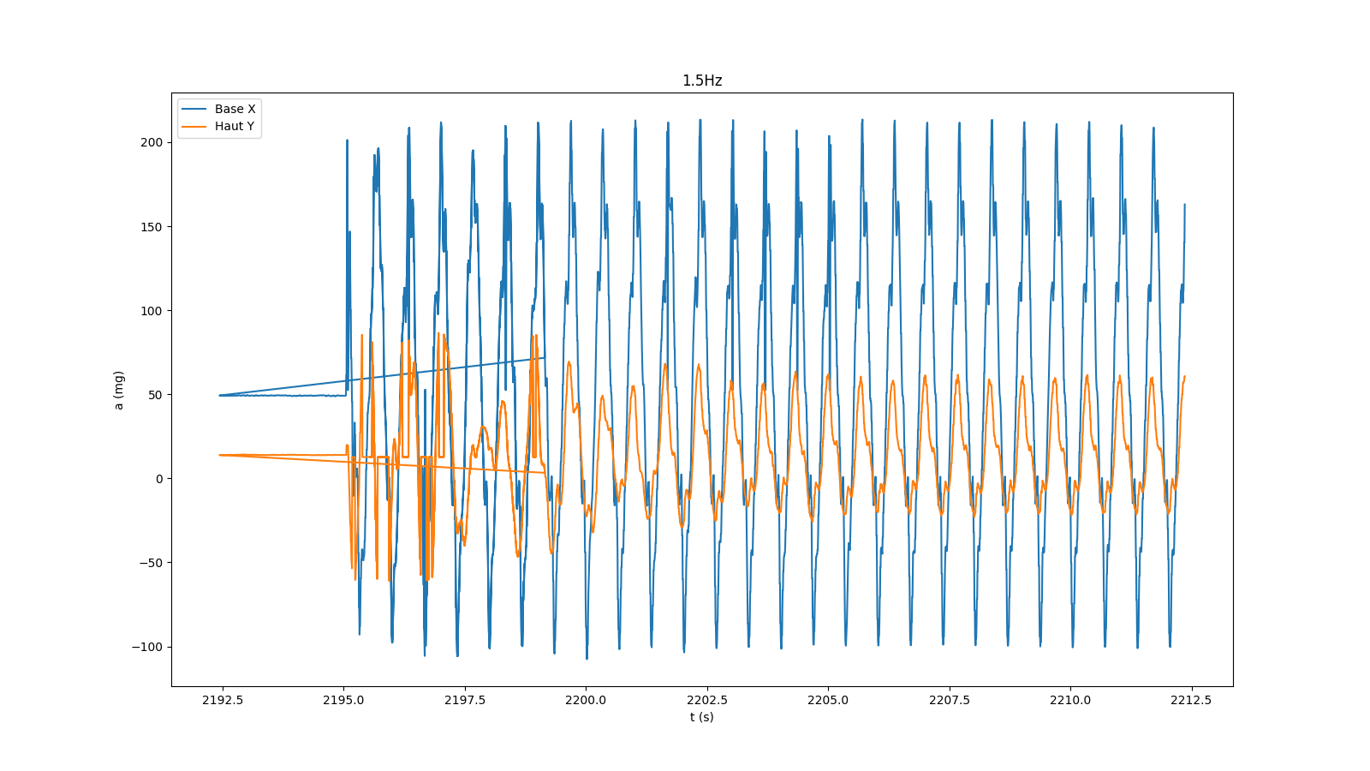
Analyse/Image/pendule 1 masse au plus bas/1.5Hz.png
