Docredstein/TIPE_TMD/Analyse/Image/pendule 1 masse au plus bas/1.7 hz.png

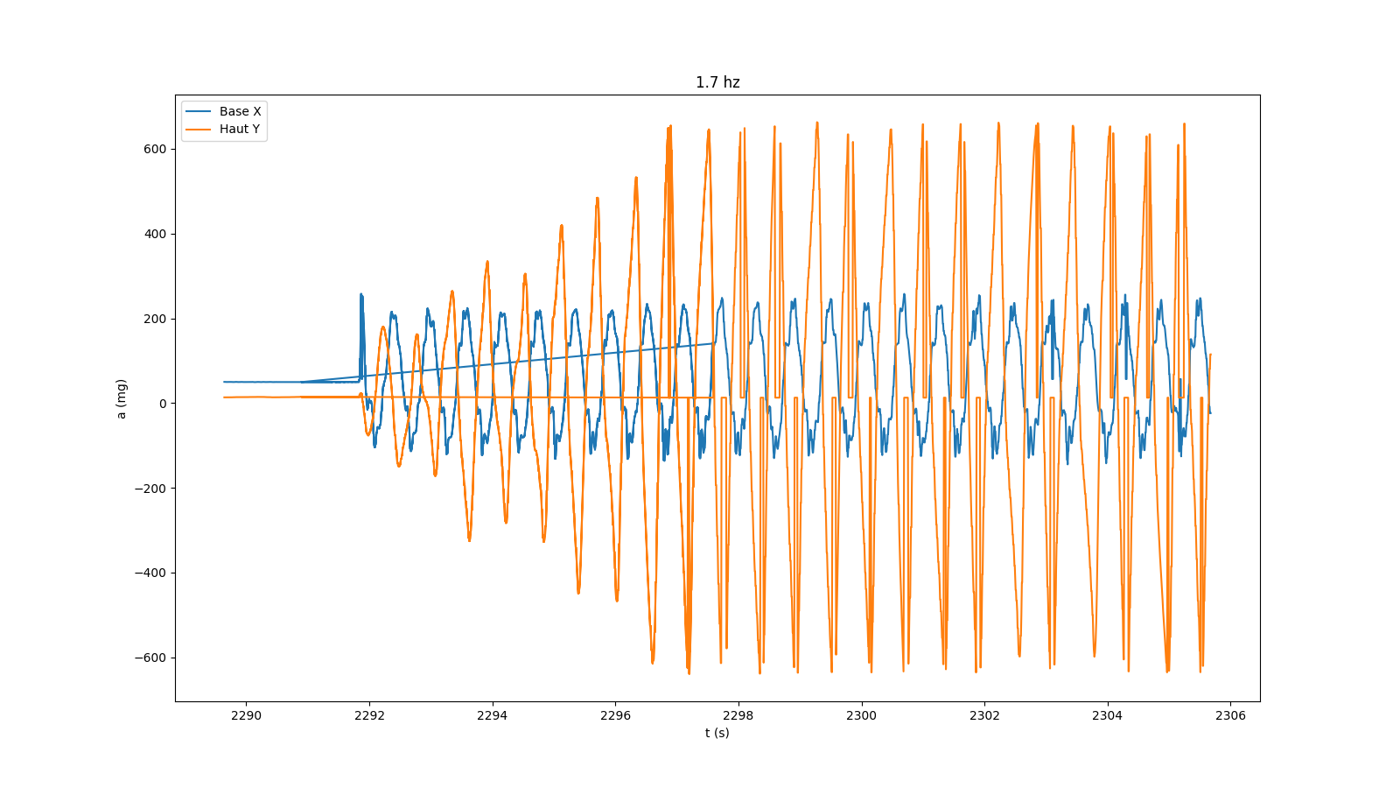
Analyse/Image/pendule 1 masse au plus bas/1.7 hz.png
