Docredstein/TIPE_TMD/Analyse/Image/pendule 1 masse au plus bas/2hz.png

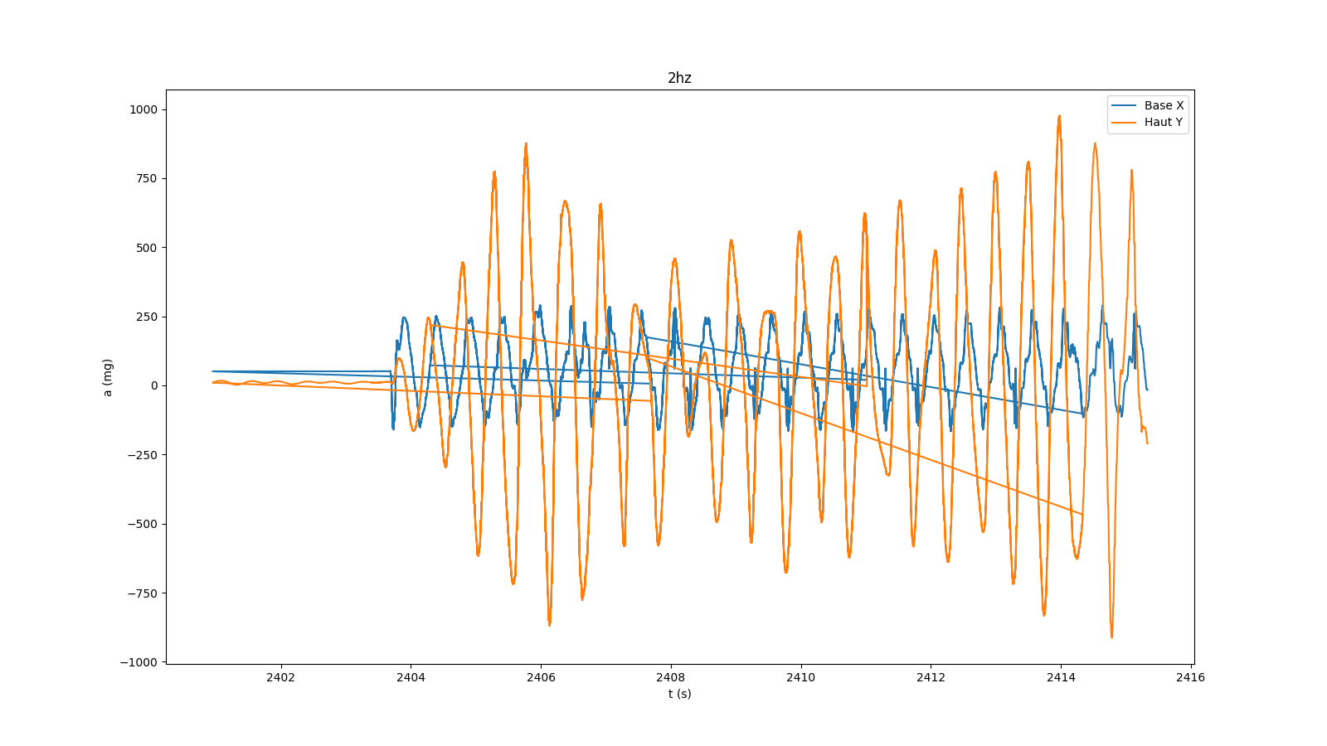
Analyse/Image/pendule 1 masse au plus bas/2hz.png
