Docredstein/TIPE_TMD/Analyse/Image/pendule 1 masse au plus bas/3.5hz.png

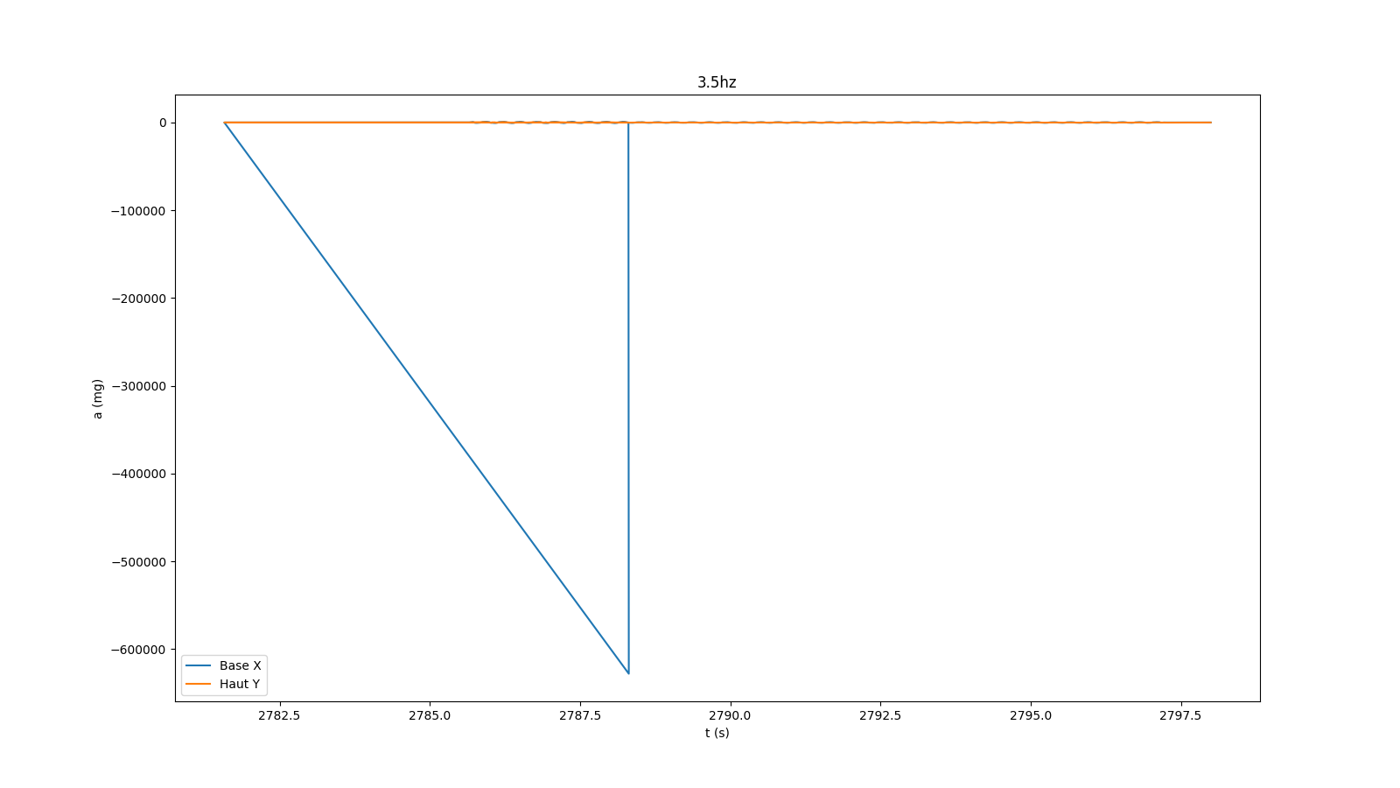
Analyse/Image/pendule 1 masse au plus bas/3.5hz.png
