Docredstein/TIPE_TMD/Analyse/Image/pendule 1 masse au plus bas/3hz.png

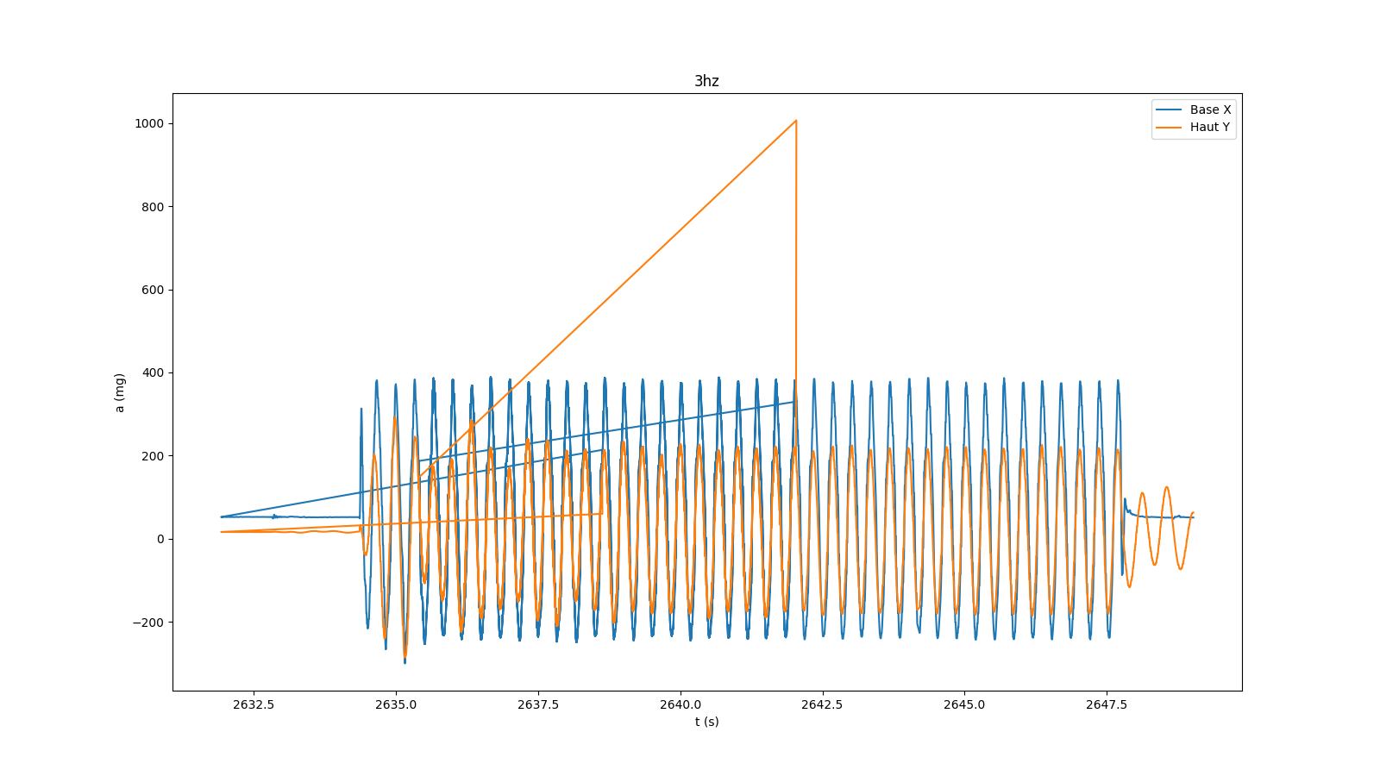
Analyse/Image/pendule 1 masse au plus bas/3hz.png
