Docredstein/TIPE_TMD/Analyse/Image/Pendule 1 masse à 3cm de la barre/0.5 hz.png

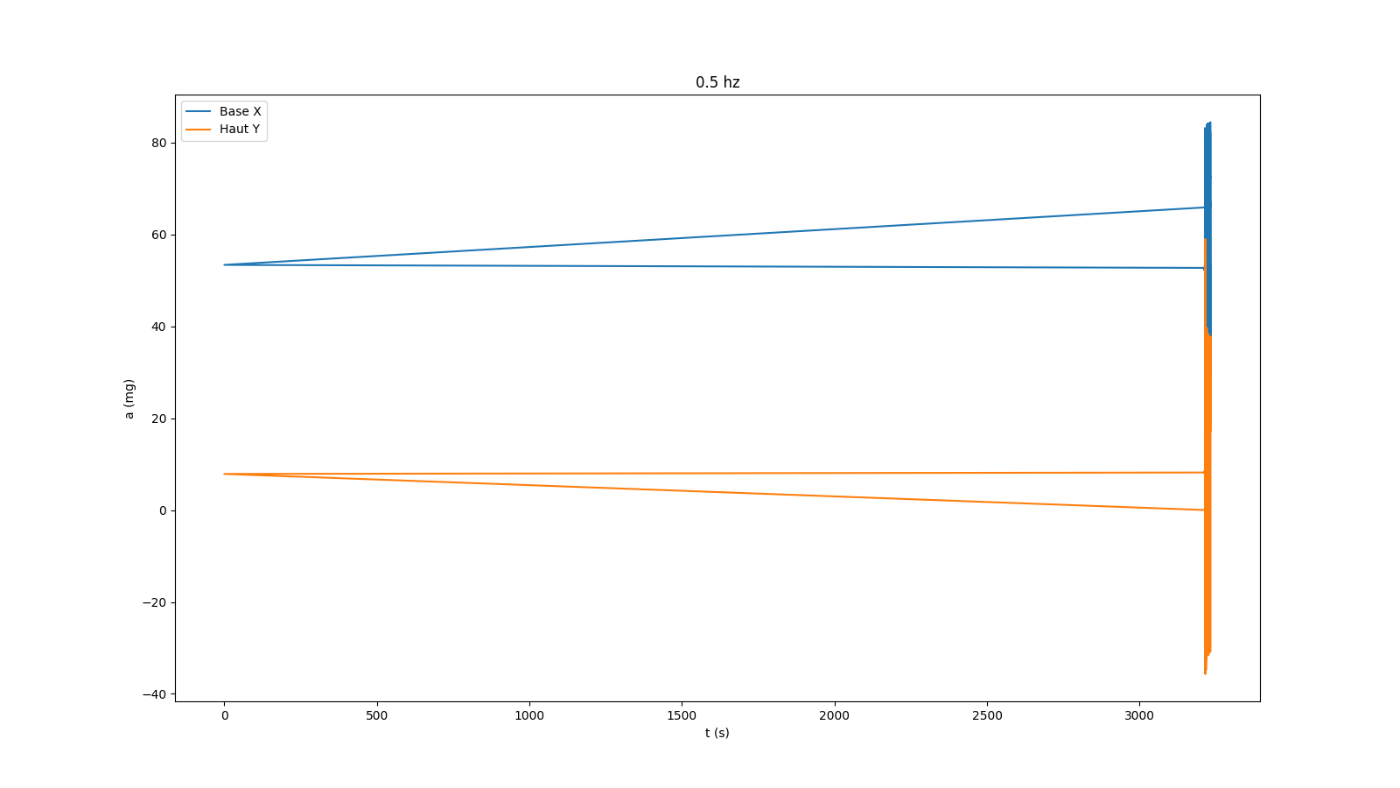
Analyse/Image/Pendule 1 masse à 3cm de la barre/0.5 hz.png
