Docredstein/TIPE_TMD/Analyse/Image/pendule 7 cm du haut pendule fixe axe/0.5Hz.png

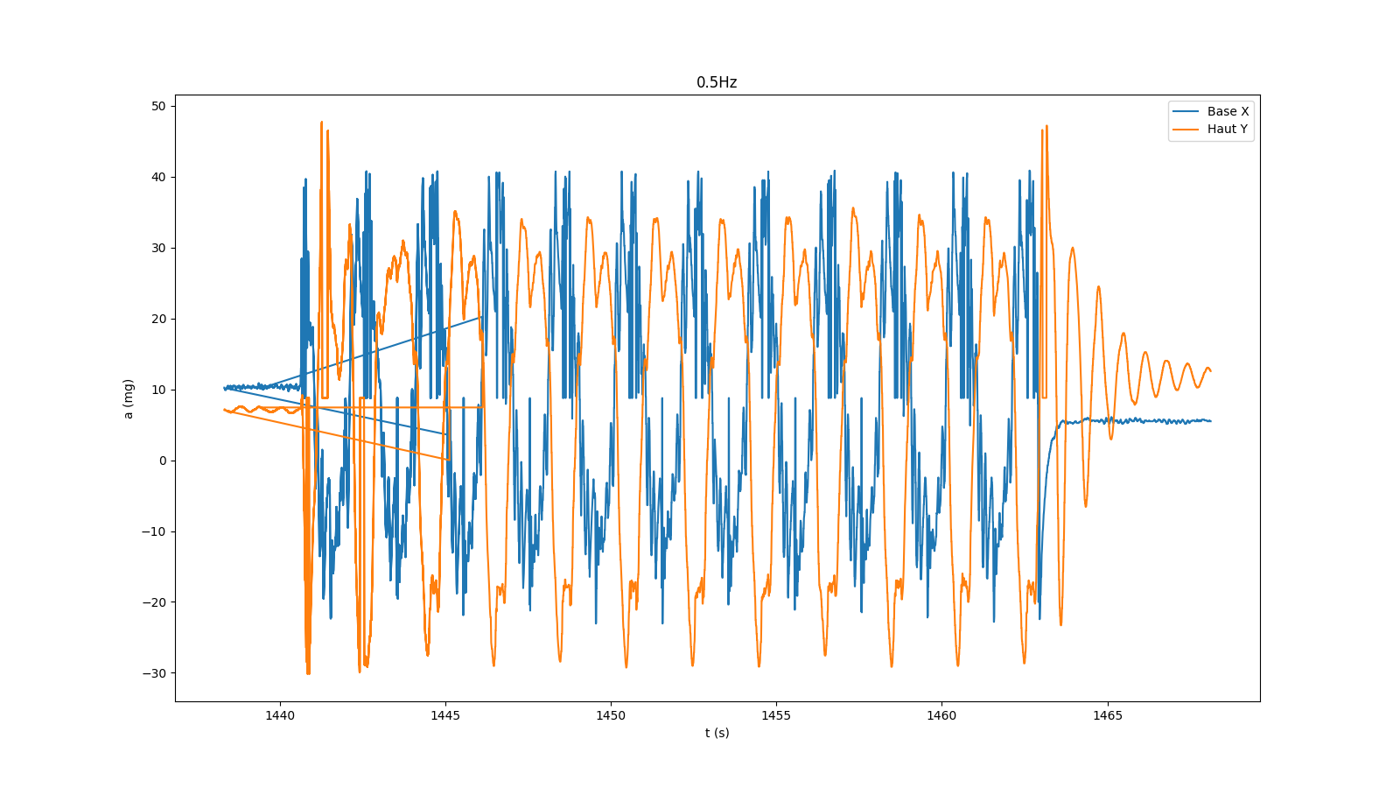
Analyse/Image/pendule 7 cm du haut pendule fixe axe/0.5Hz.png
