Docredstein/TIPE_TMD/Analyse/Image/pendule 7 cm du haut pendule fixe axe/1.5Hz.png

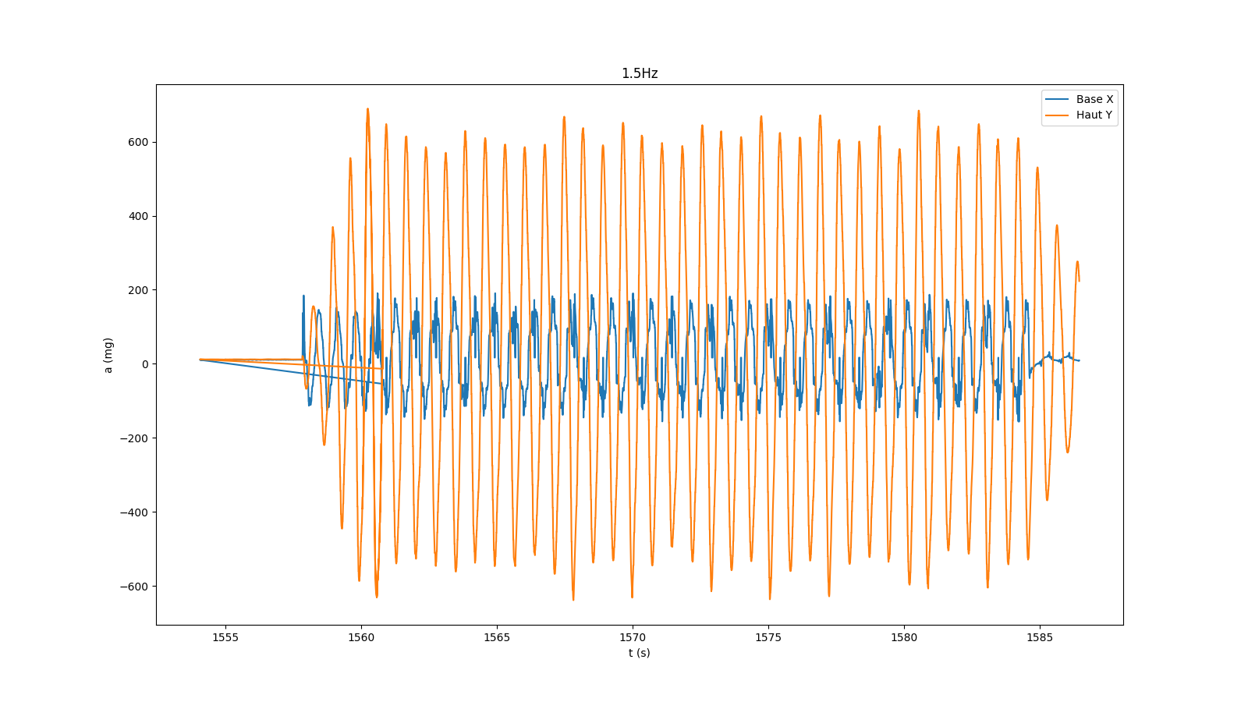
Analyse/Image/pendule 7 cm du haut pendule fixe axe/1.5Hz.png
