Docredstein/TIPE_TMD/Analyse/Image/pendule 7 cm du haut pendule fixe axe/2 HZ.png

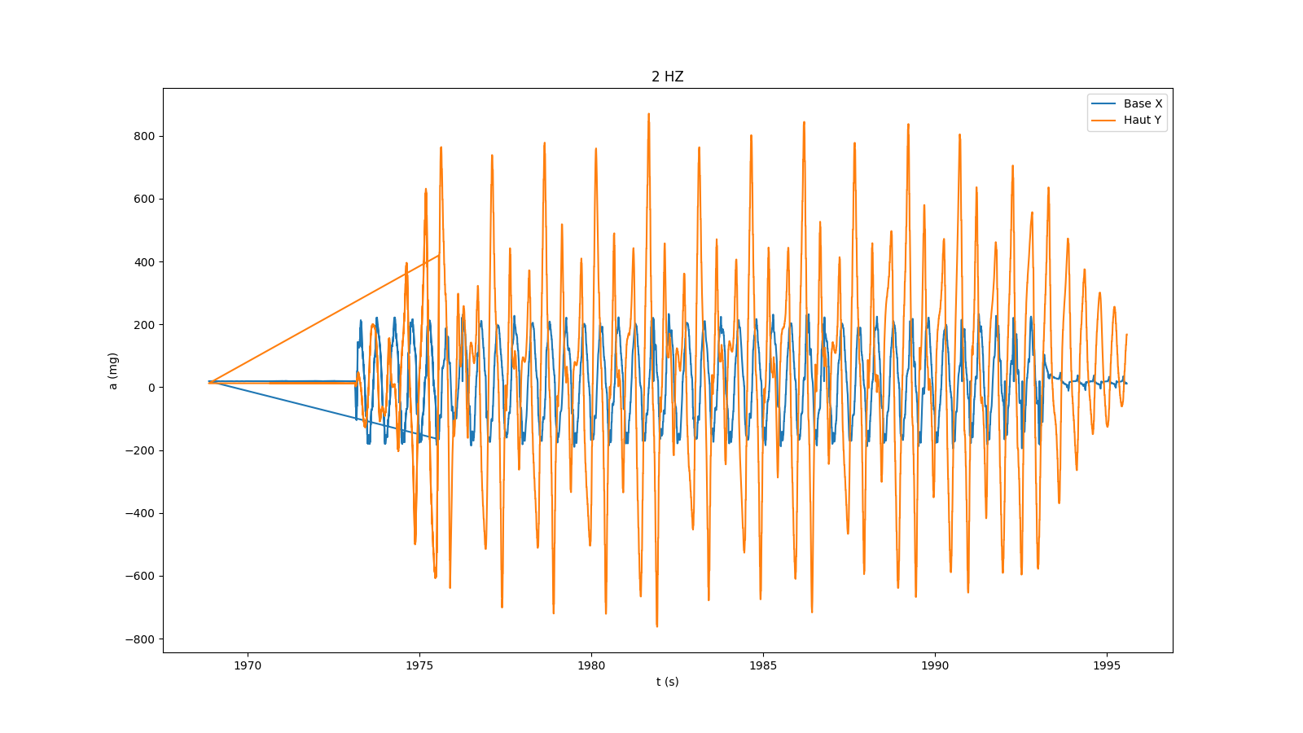
Analyse/Image/pendule 7 cm du haut pendule fixe axe/2 HZ.png
