Docredstein/TIPE_TMD/Analyse/Image/pendule 7 cm du haut pendule fixe axe/2hz vdirty.png

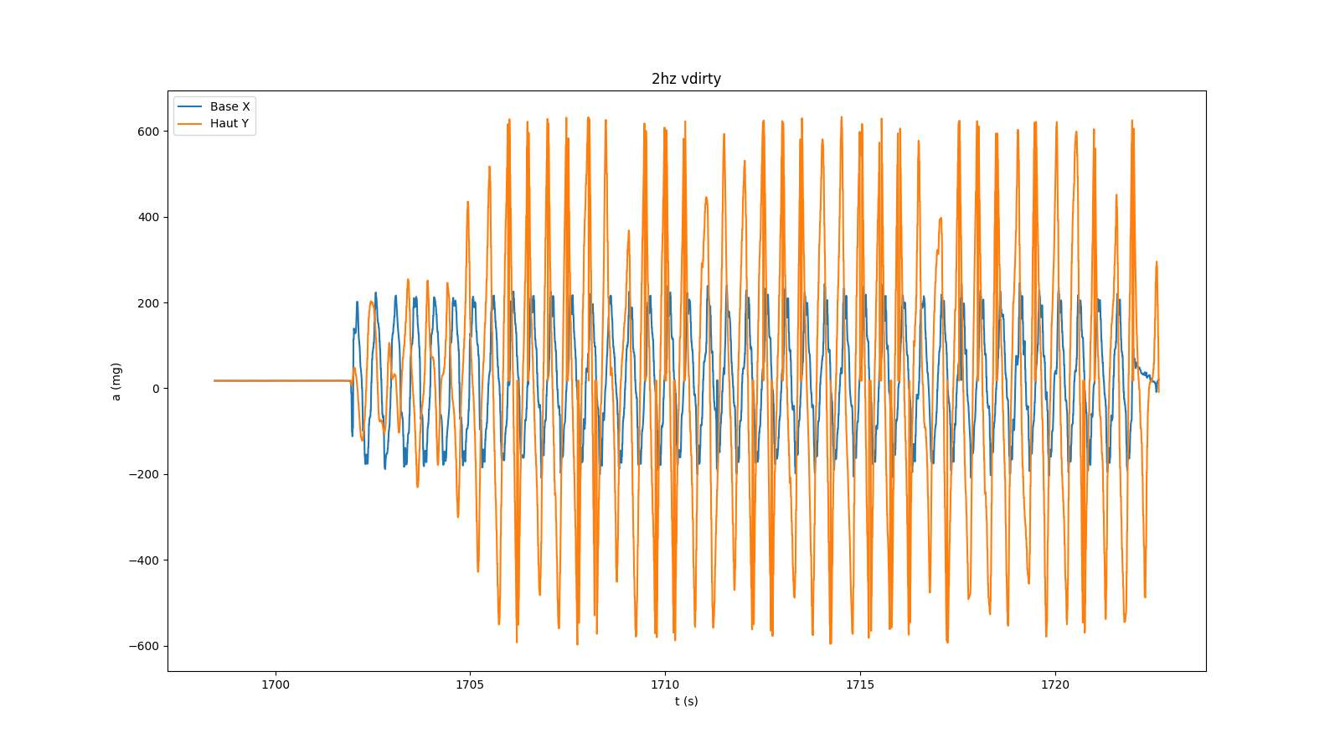
Analyse/Image/pendule 7 cm du haut pendule fixe axe/2hz vdirty.png
