Docredstein/TIPE_TMD/Analyse/Image/pendule 7 cm du haut pendule fixe axe/3.5 hz.png

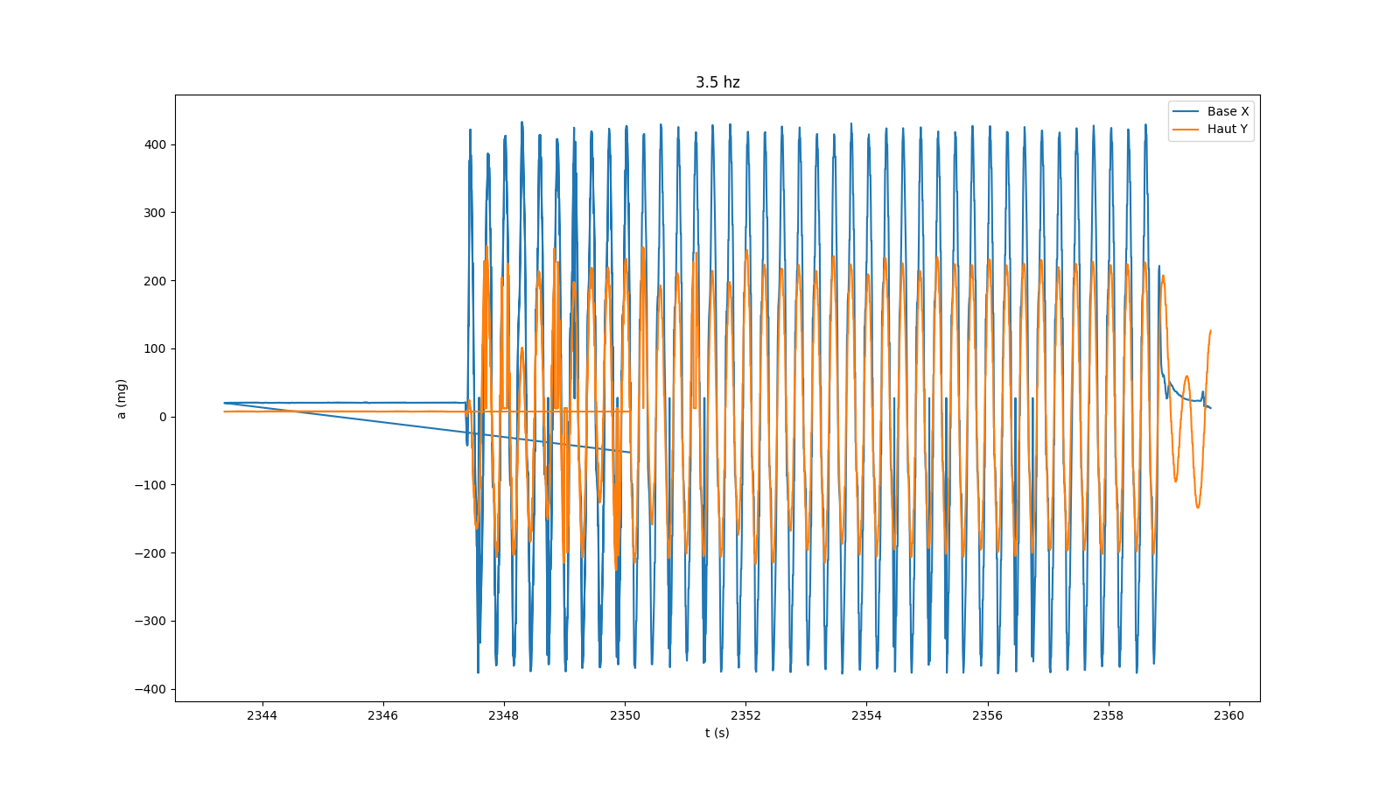
Analyse/Image/pendule 7 cm du haut pendule fixe axe/3.5 hz.png
