Docredstein/TIPE_TMD/Analyse/Image/pendule 7 mm faible amplitude/0.5Hz.png

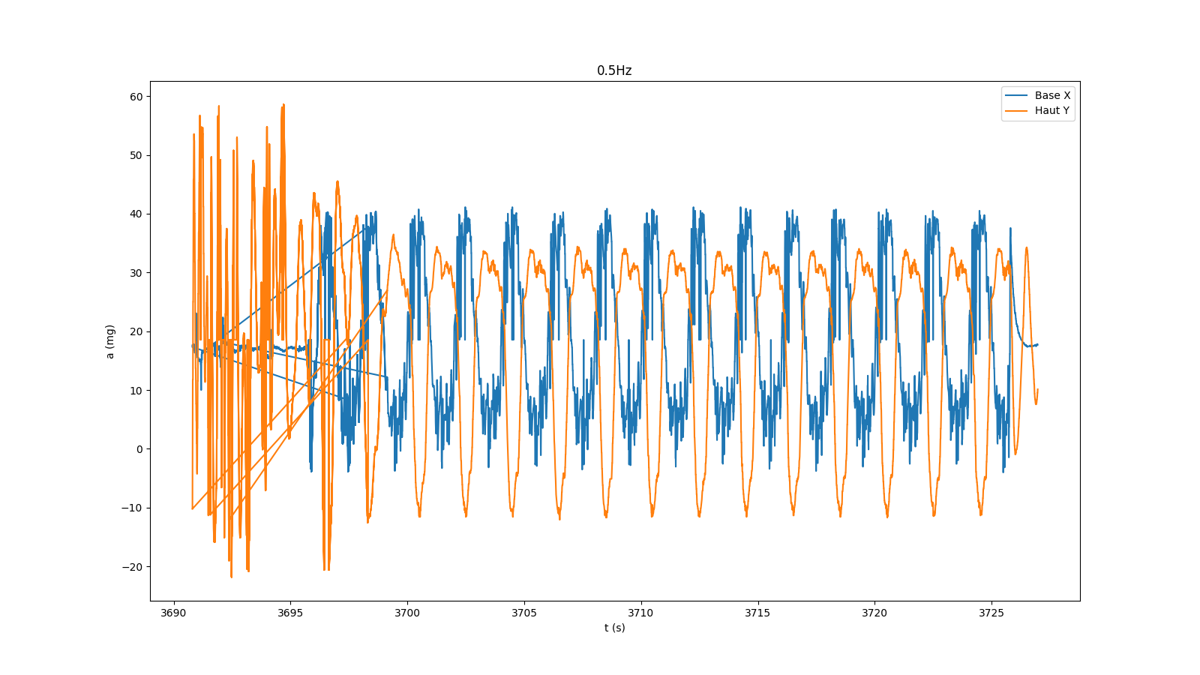
Analyse/Image/pendule 7 mm faible amplitude/0.5Hz.png
