Docredstein/TIPE_TMD/Analyse/Image/pendule 7 mm faible amplitude/1.5Hz.png

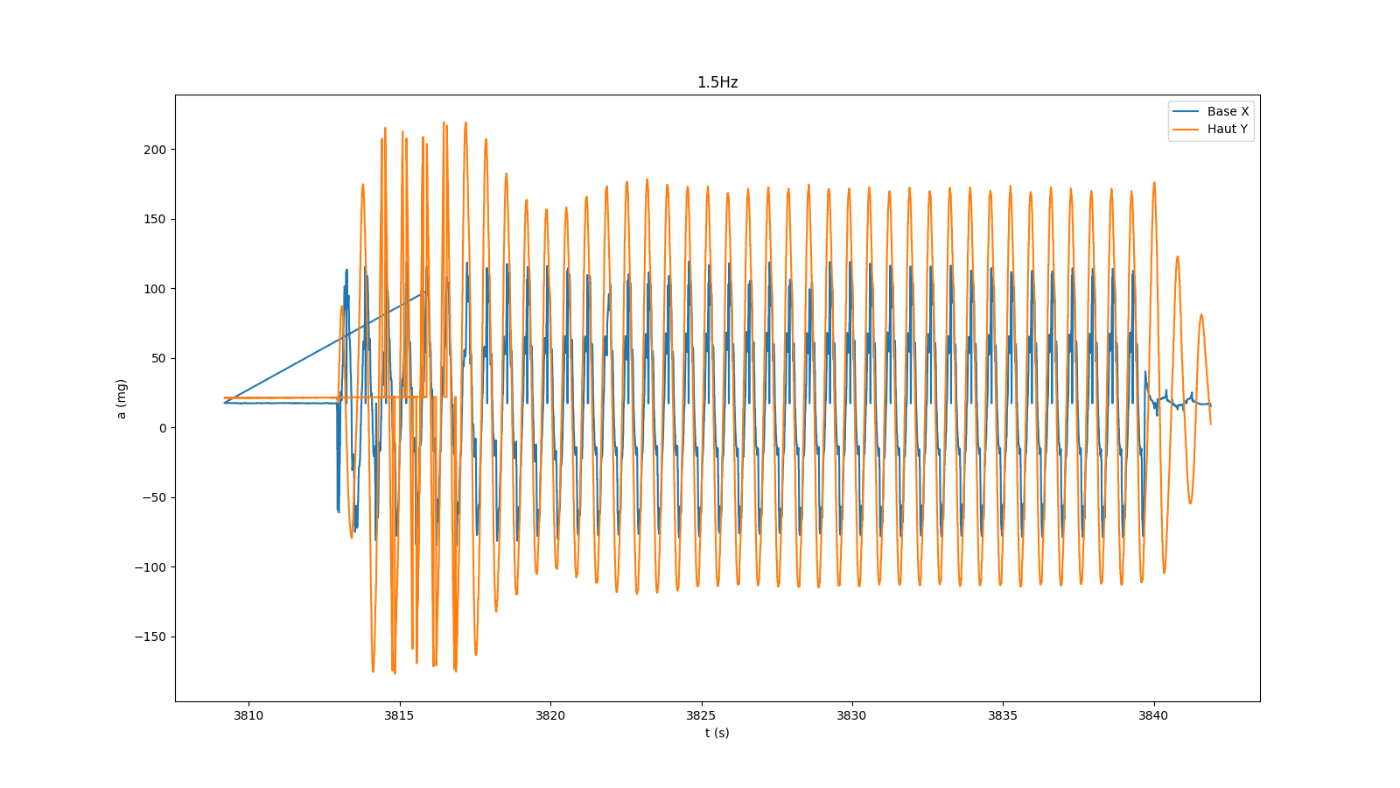
Analyse/Image/pendule 7 mm faible amplitude/1.5Hz.png
