Docredstein/TIPE_TMD/Analyse/Image/pendule 7 mm faible amplitude/2Hz.png

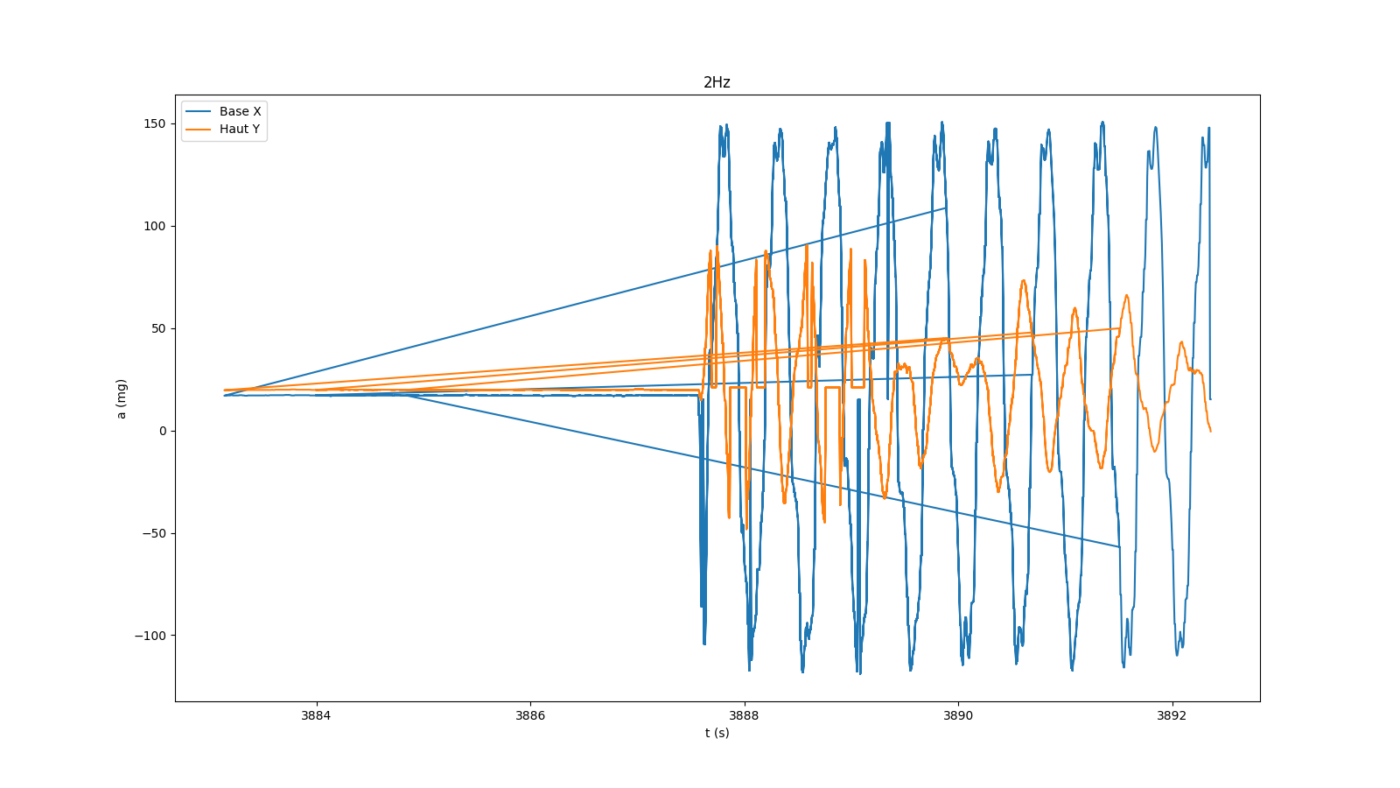
Analyse/Image/pendule 7 mm faible amplitude/2Hz.png
