Docredstein/TIPE_TMD/Analyse/Image/pendule 7 mm faible amplitude/3.5hz.png

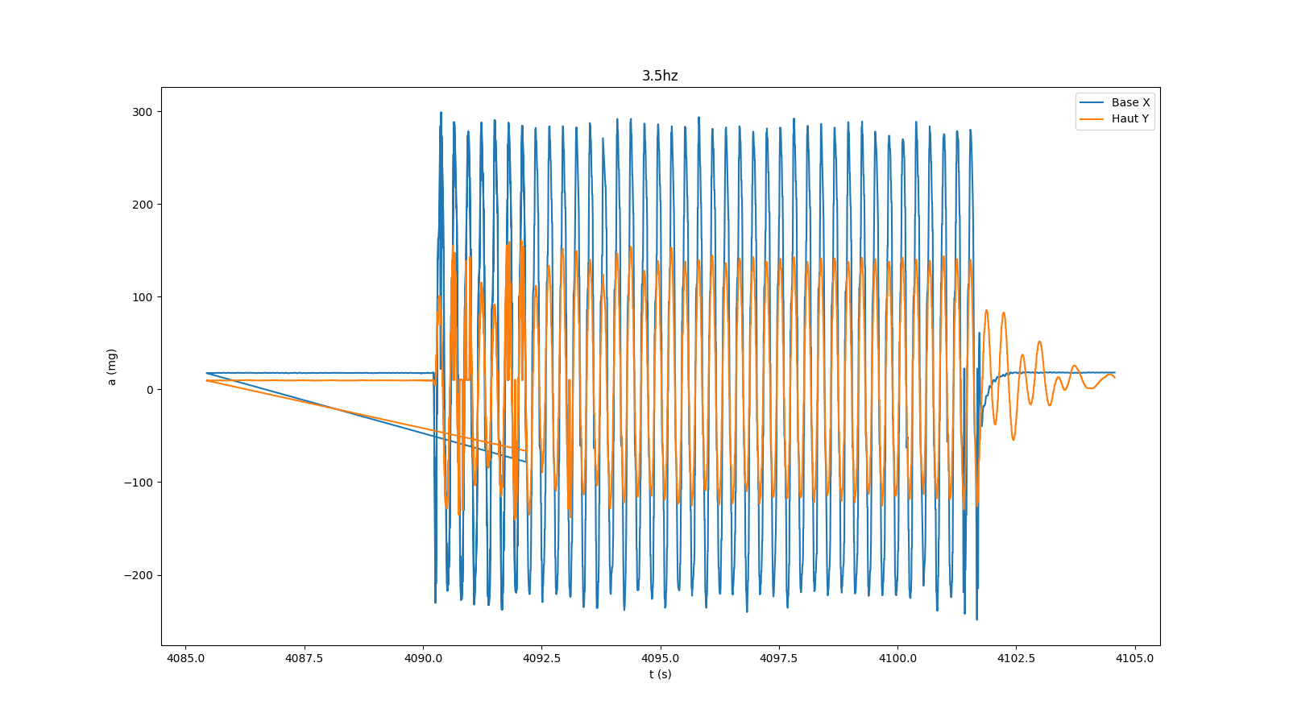
Analyse/Image/pendule 7 mm faible amplitude/3.5hz.png
