Docredstein/TIPE_TMD/Analyse/Image/pendule 7 mm faible amplitude/3Hz.png

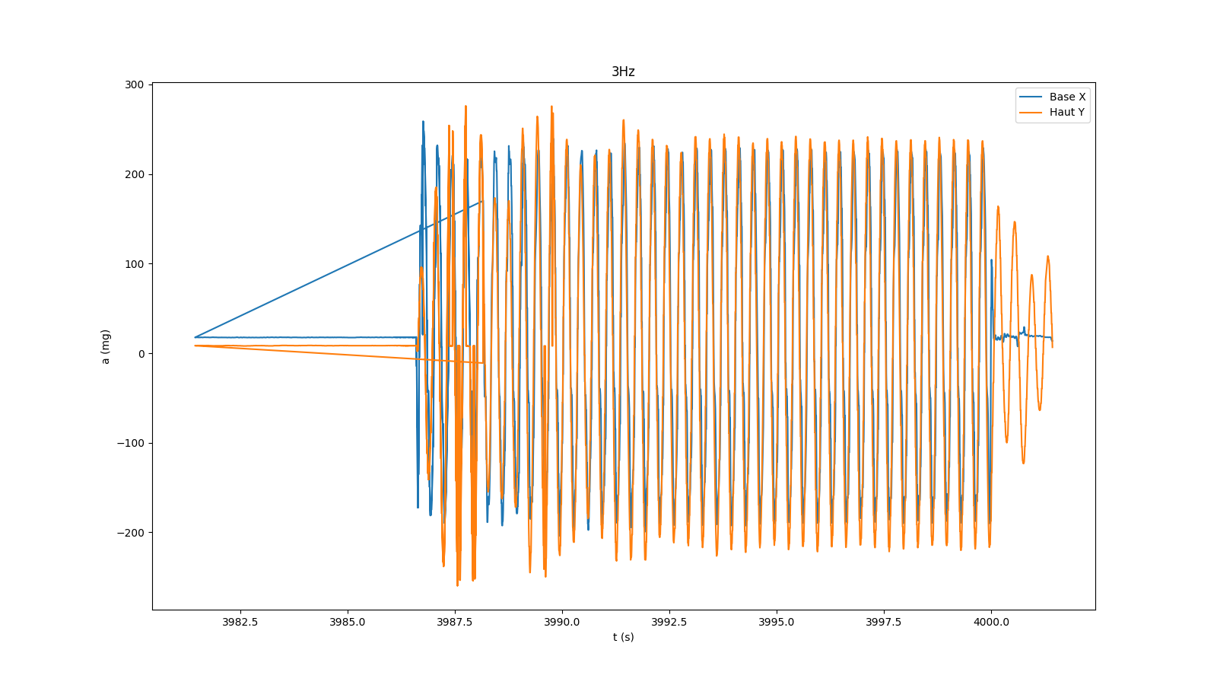
Analyse/Image/pendule 7 mm faible amplitude/3Hz.png
