Docredstein/TIPE_TMD/Analyse/Image/pendule au plus bas faible amplitude/0.5Hz.png

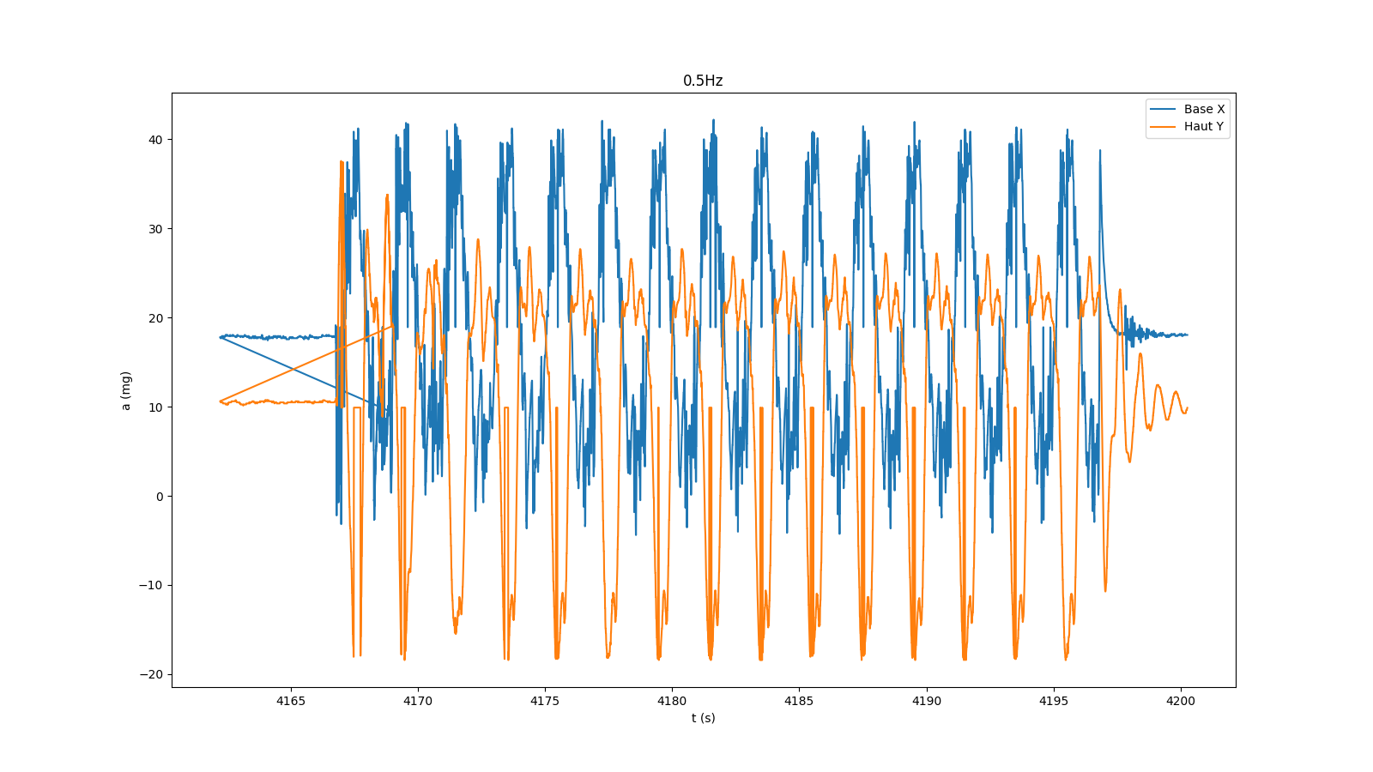
Analyse/Image/pendule au plus bas faible amplitude/0.5Hz.png
