Docredstein/TIPE_TMD/Analyse/Image/pendule au plus bas faible amplitude/1.7 hz.png

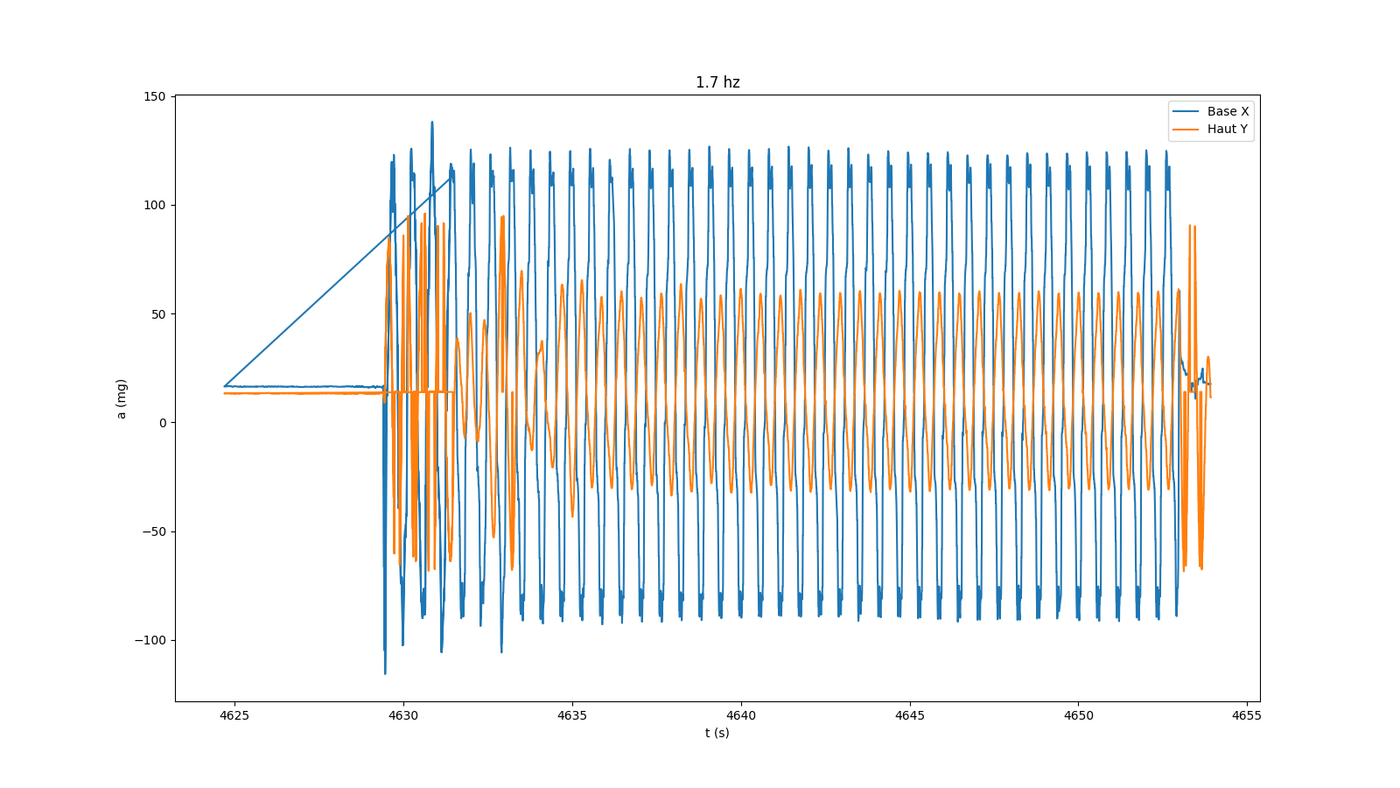
Analyse/Image/pendule au plus bas faible amplitude/1.7 hz.png
