Docredstein/TIPE_TMD/Analyse/Image/pendule au plus bas faible amplitude/2.2 hz.png

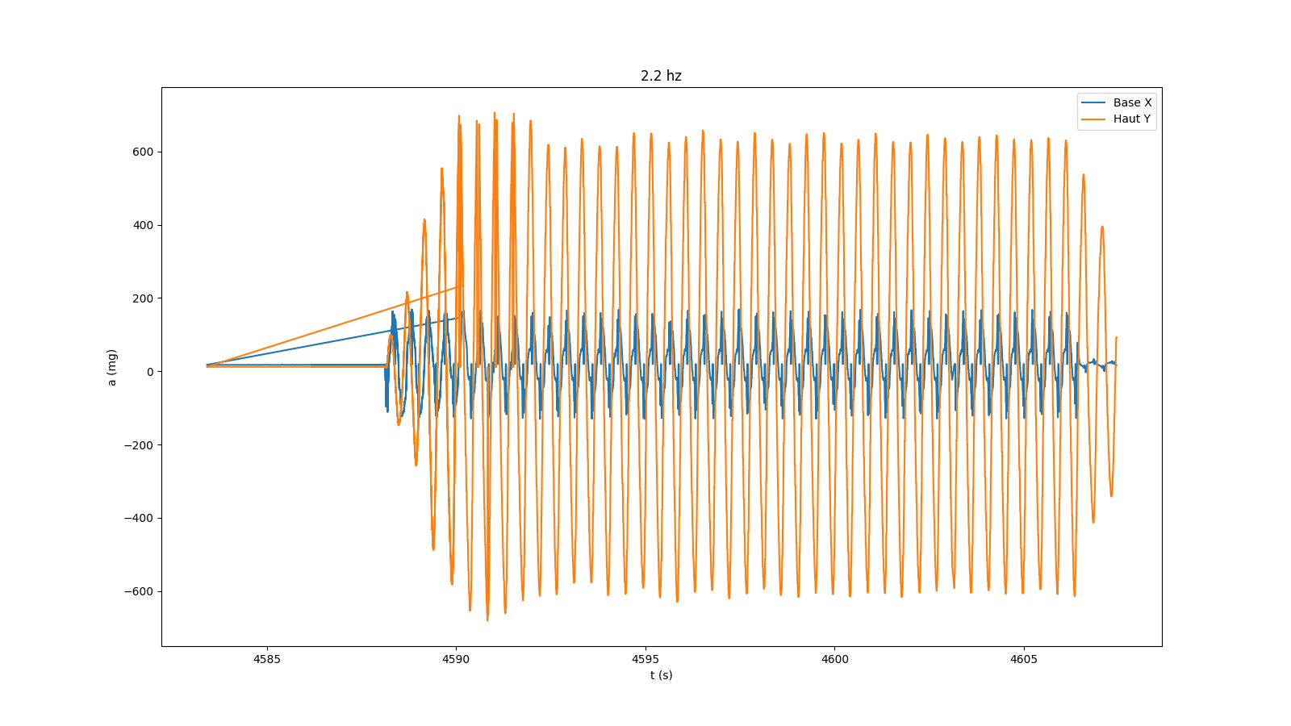
Analyse/Image/pendule au plus bas faible amplitude/2.2 hz.png
