Docredstein/TIPE_TMD/Analyse/Image/pendule au plus bas faible amplitude/3 hz.png

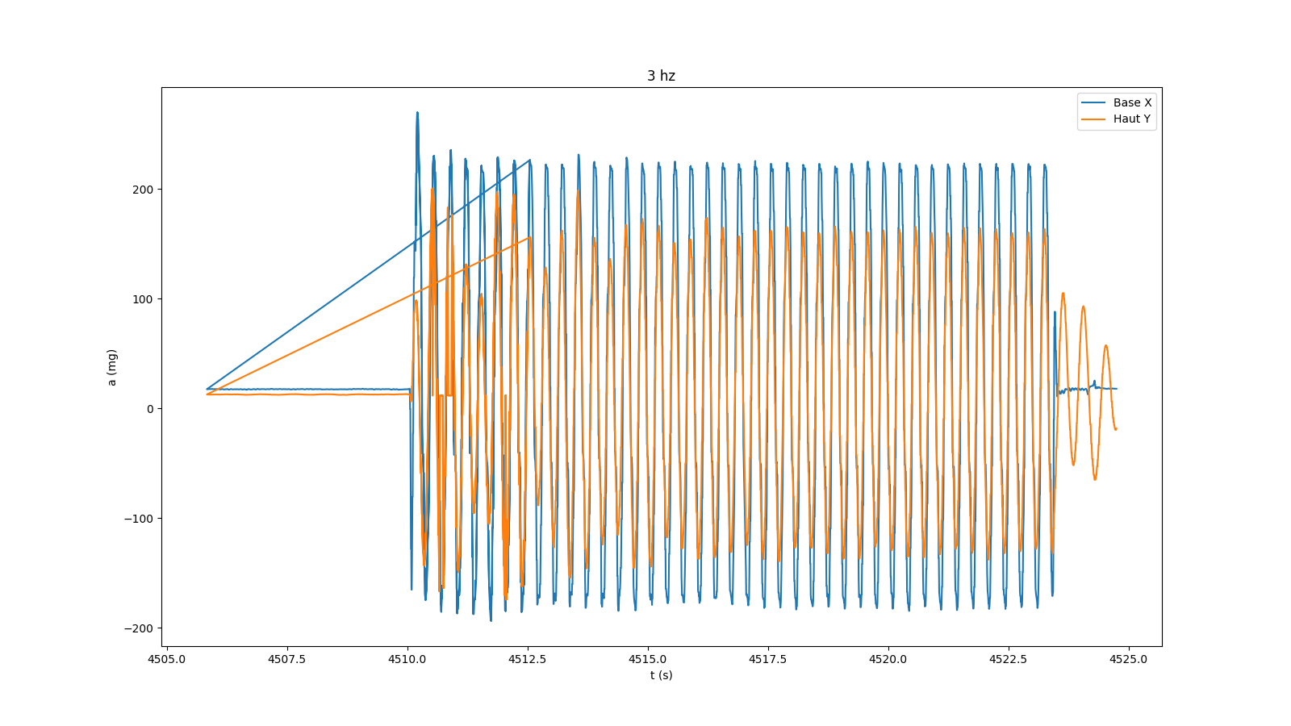
Analyse/Image/pendule au plus bas faible amplitude/3 hz.png
