Docredstein/TIPE_TMD/Analyse/Image/pendule_1_masse_au_plus_bas.png

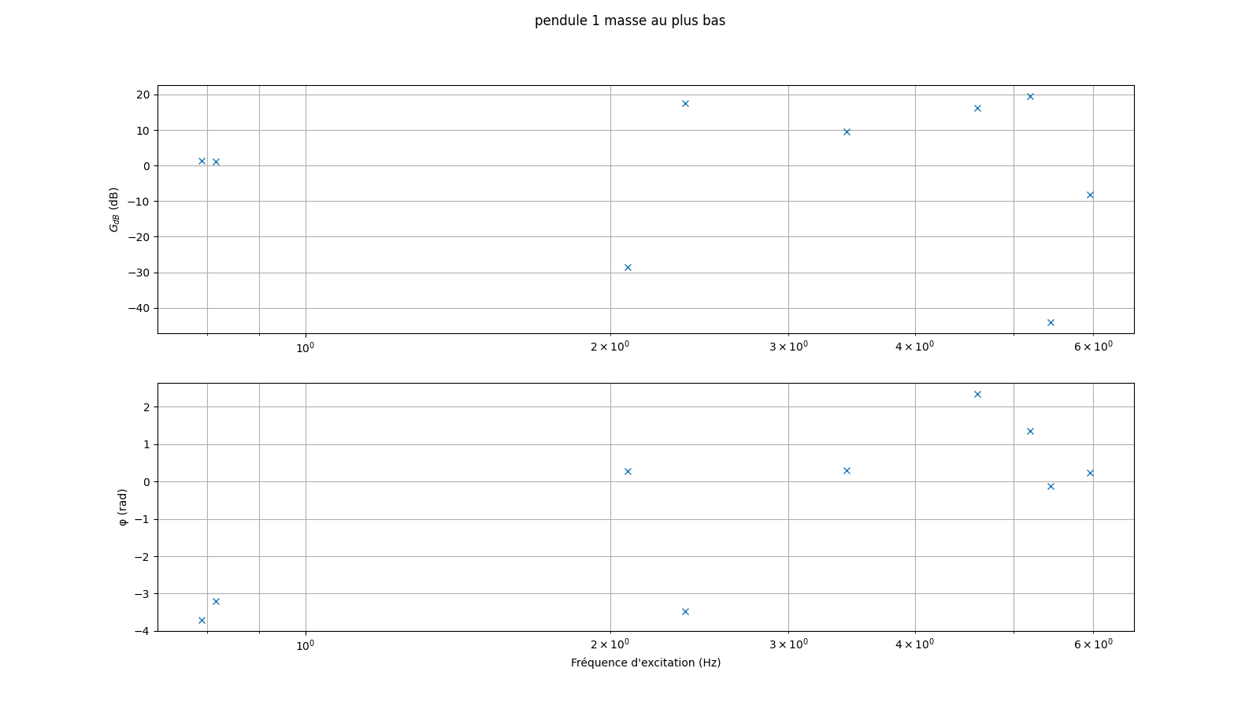
Analyse/Image/pendule_1_masse_au_plus_bas.png
