Docredstein/TIPE_TMD/Analyse/Image/Pendule_1_masse_à_3cm_de_la_barre.png

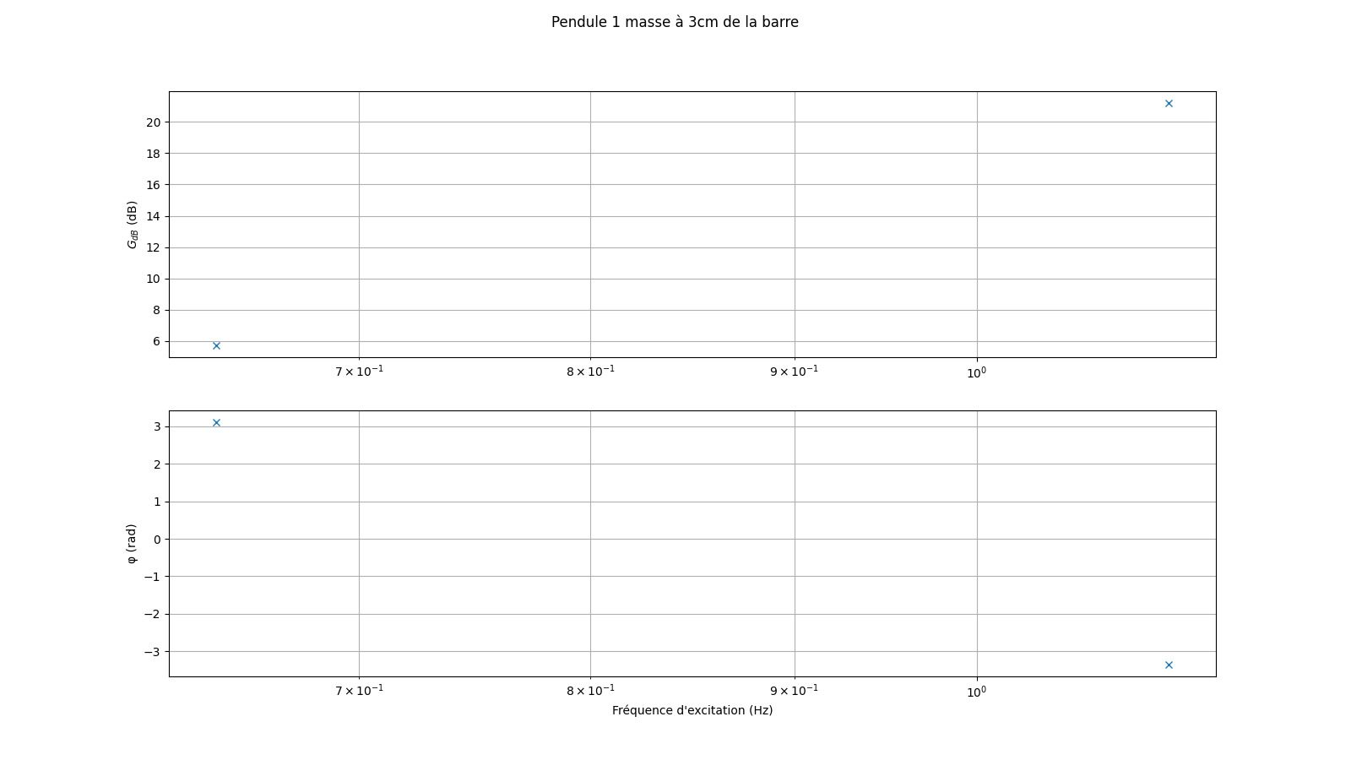
Analyse/Image/Pendule_1_masse_à_3cm_de_la_barre.png
