Docredstein/TIPE_TMD/Analyse/Image/pendule_7_mm_faible_amplitude.png

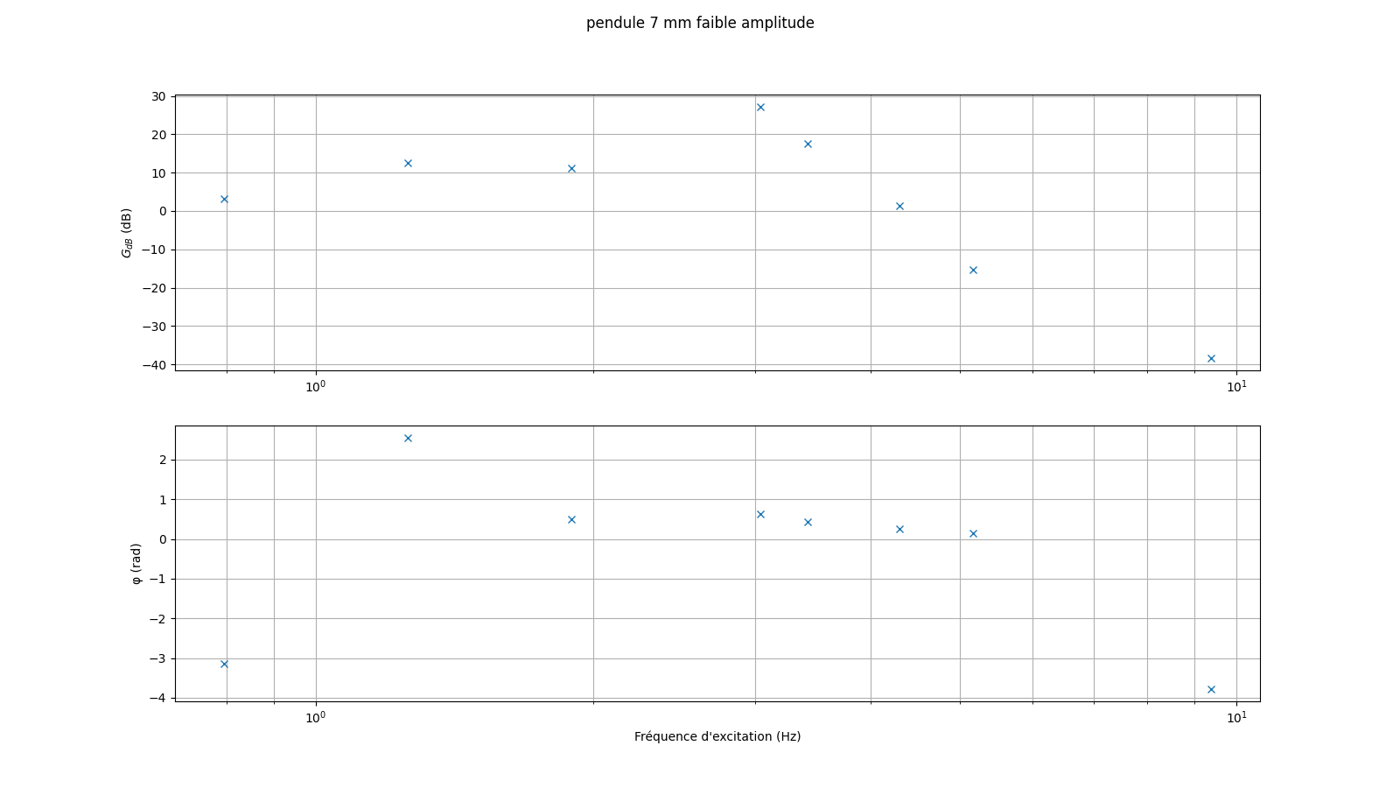
Analyse/Image/pendule_7_mm_faible_amplitude.png
