Docredstein/TIPE_TMD/Analyse/Image/pendule_au_plus_bas_faible_amplitude.png

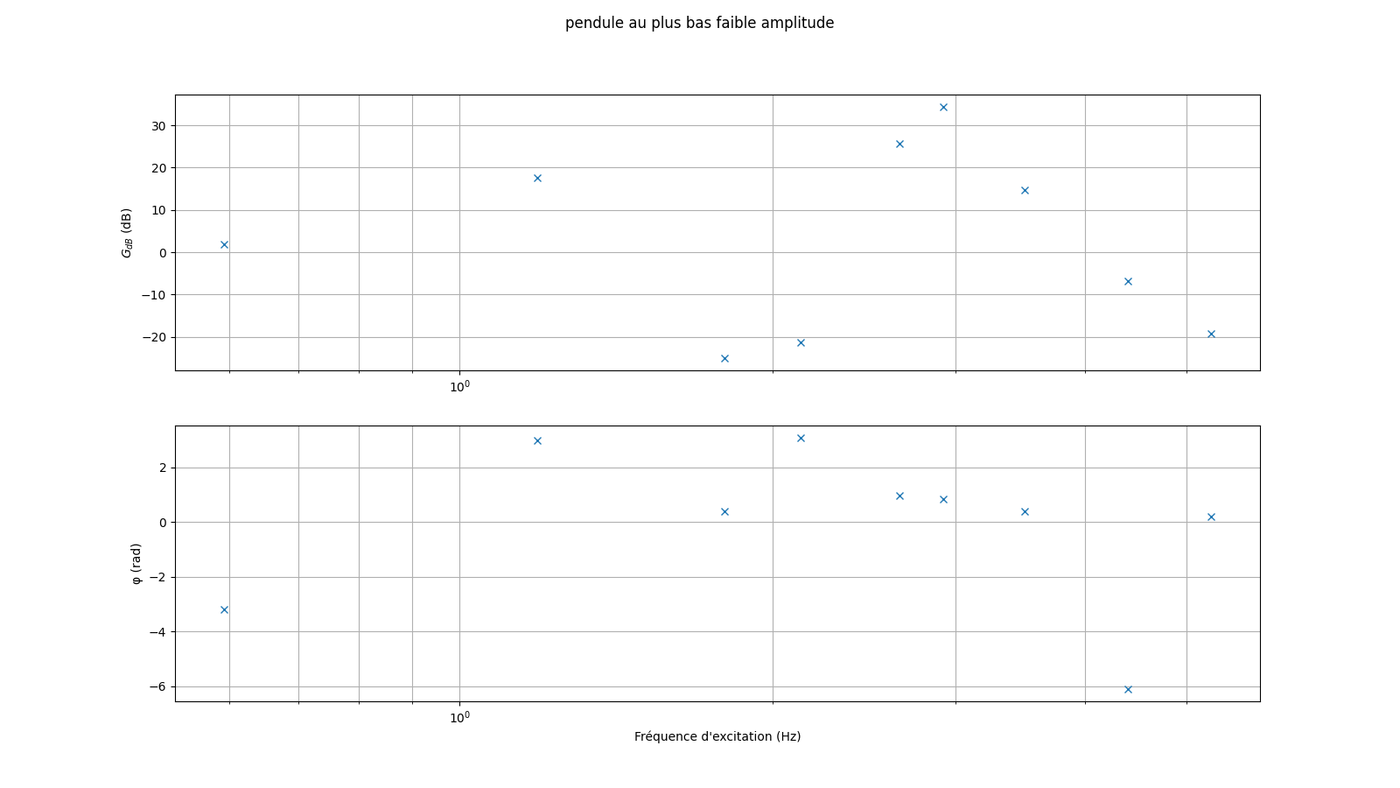
Analyse/Image/pendule_au_plus_bas_faible_amplitude.png
