Docredstein/TIPE_TMD/Analyse/Image/penduleb 7mm sans pendule faible amplitude/0.5 Hz.png

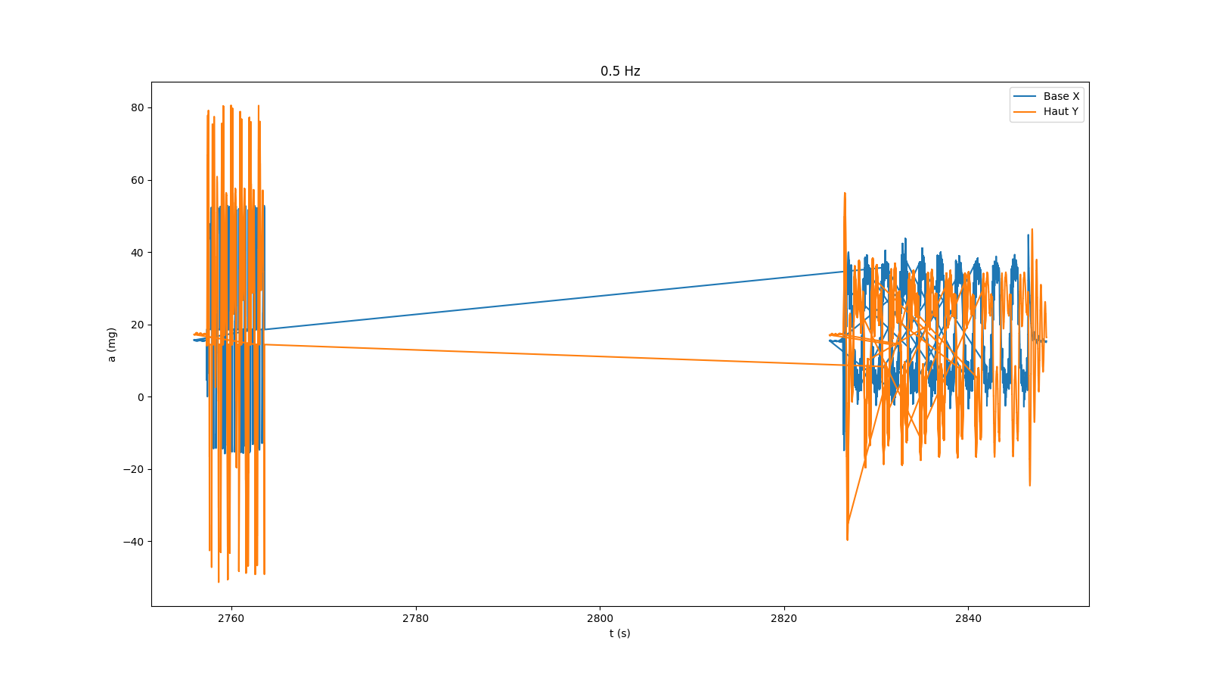
Analyse/Image/penduleb 7mm sans pendule faible amplitude/0.5 Hz.png
