Docredstein/TIPE_TMD/Analyse/Image/penduleb 7mm sans pendule faible amplitude/2.2 hz.png

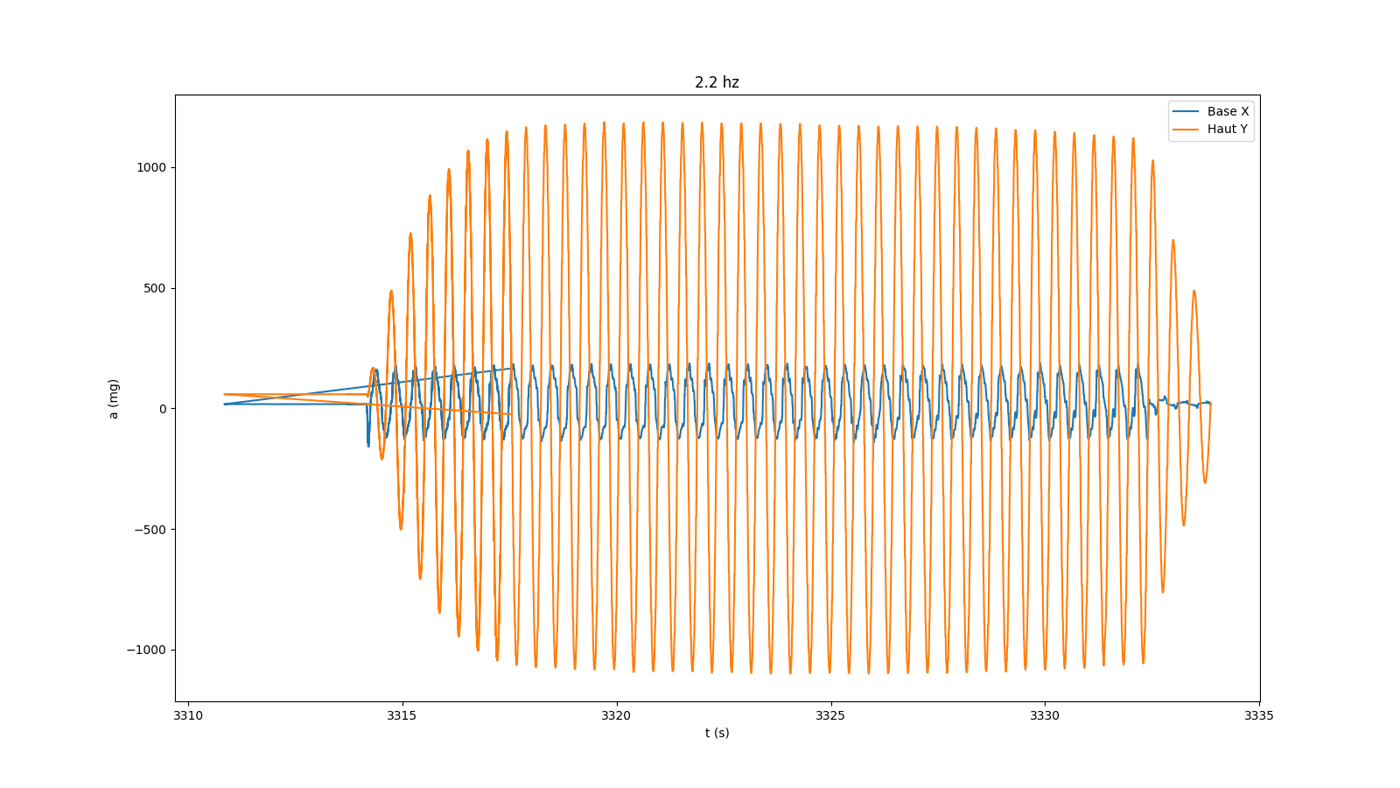
Analyse/Image/penduleb 7mm sans pendule faible amplitude/2.2 hz.png
