Docredstein/TIPE_TMD/Analyse/Image/penduleb 7mm sans pendule faible amplitude/2.5Hz.png

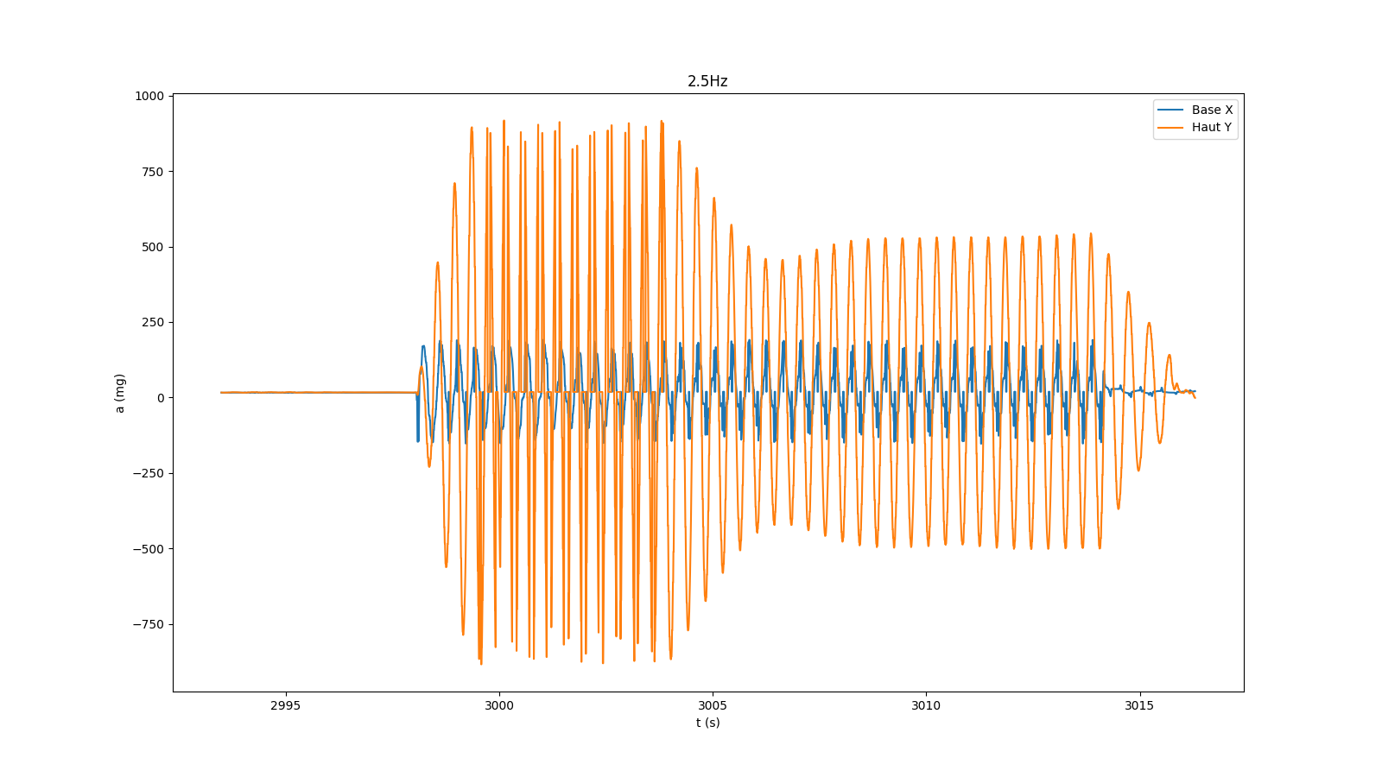
Analyse/Image/penduleb 7mm sans pendule faible amplitude/2.5Hz.png
