Docredstein/TIPE_TMD/Analyse/Image/penduleb_7mm_sans_pendule_faible_amplitude.png

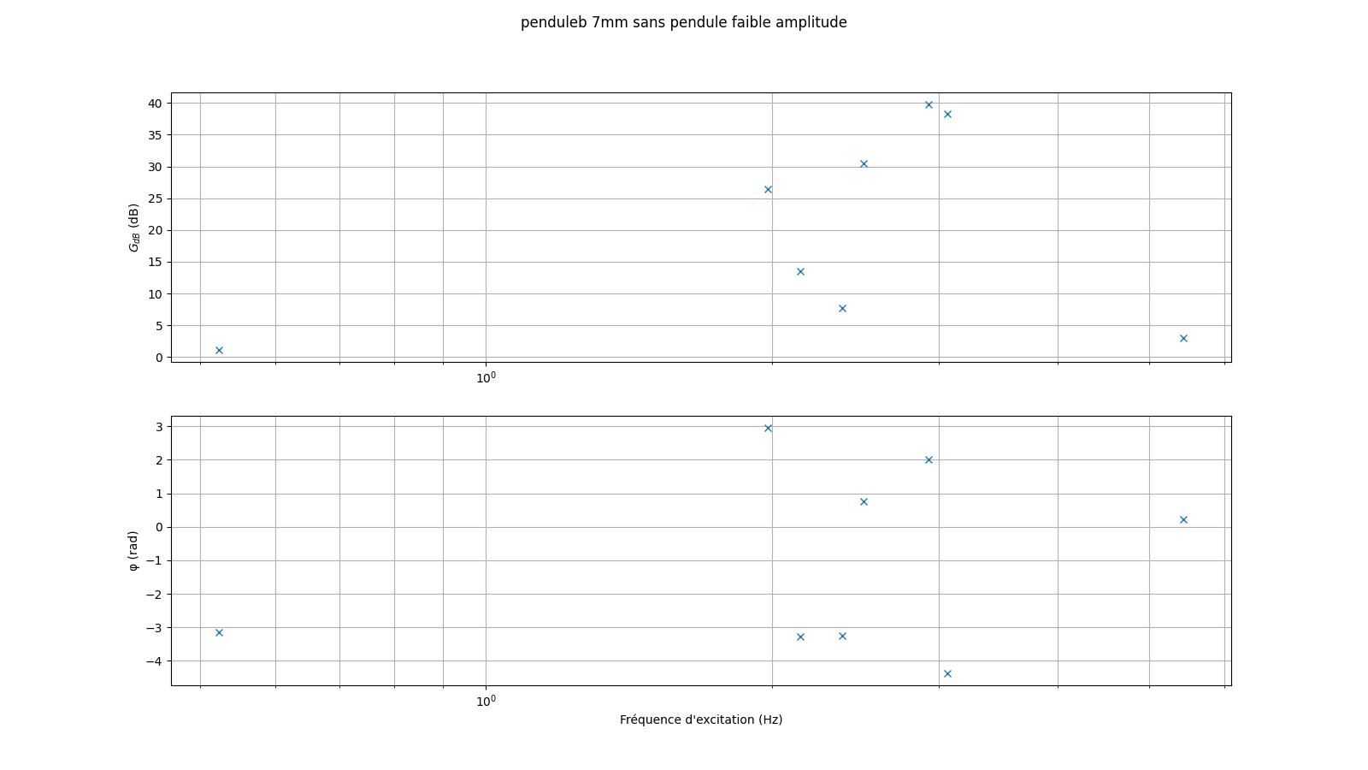
Analyse/Image/penduleb_7mm_sans_pendule_faible_amplitude.png
