Docredstein/TIPE_TMD/Analyse/Image/Sans masse, tige seule faible amplitude/0.5 hz.png

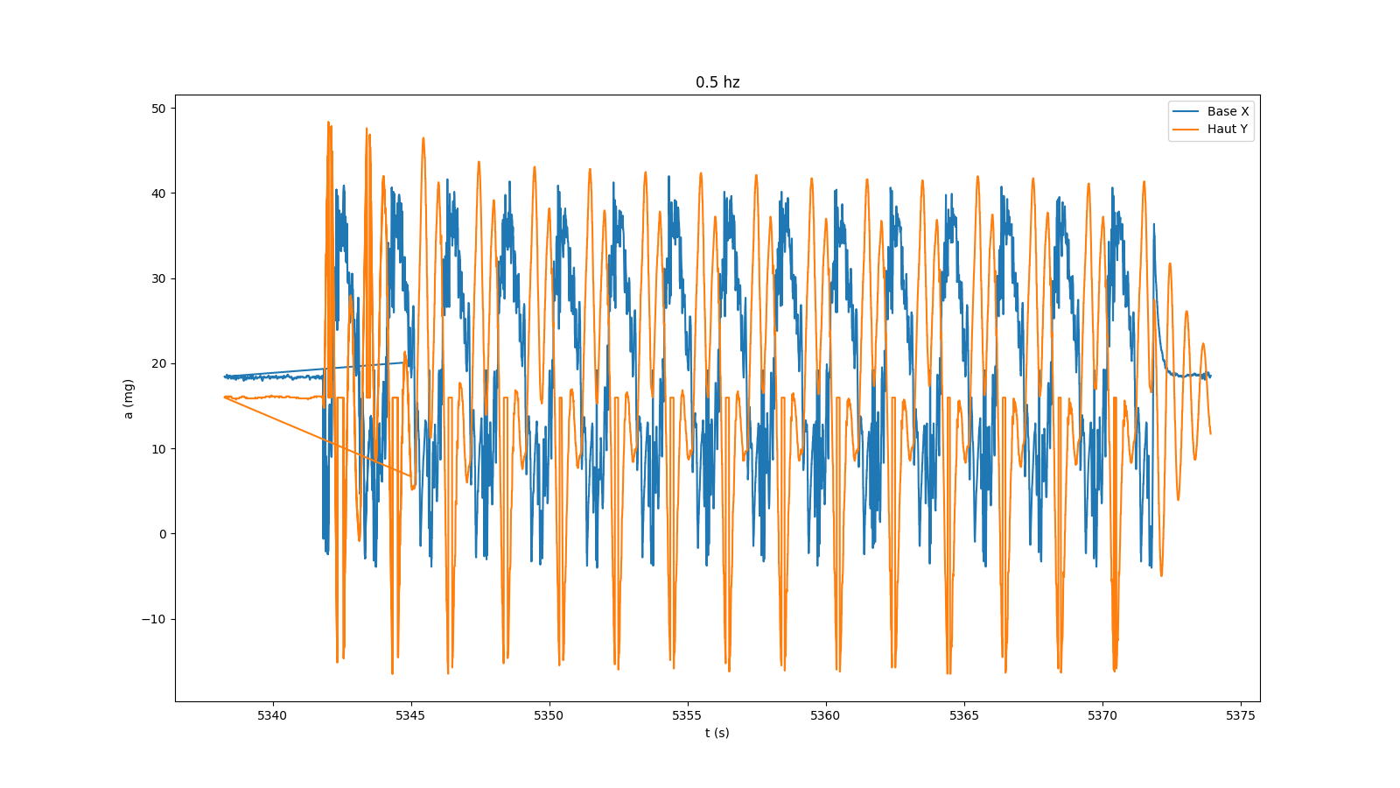
Analyse/Image/Sans masse, tige seule faible amplitude/0.5 hz.png
