Docredstein/TIPE_TMD/Analyse/Image/Sans masse, tige seule faible amplitude/1 hz.png

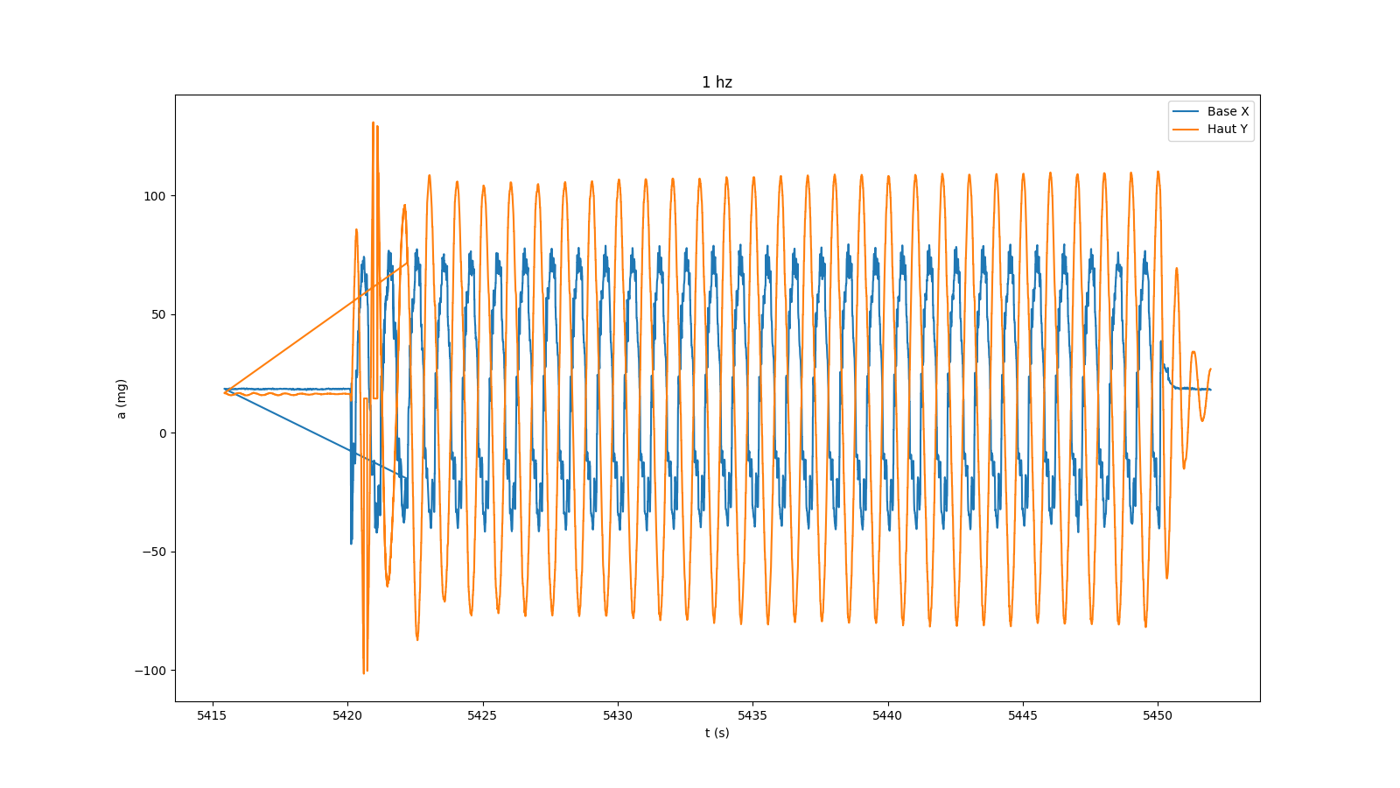
Analyse/Image/Sans masse, tige seule faible amplitude/1 hz.png
