Docredstein/TIPE_TMD/Analyse/Image/Sans masse, tige seule faible amplitude/1.5 HZ.png

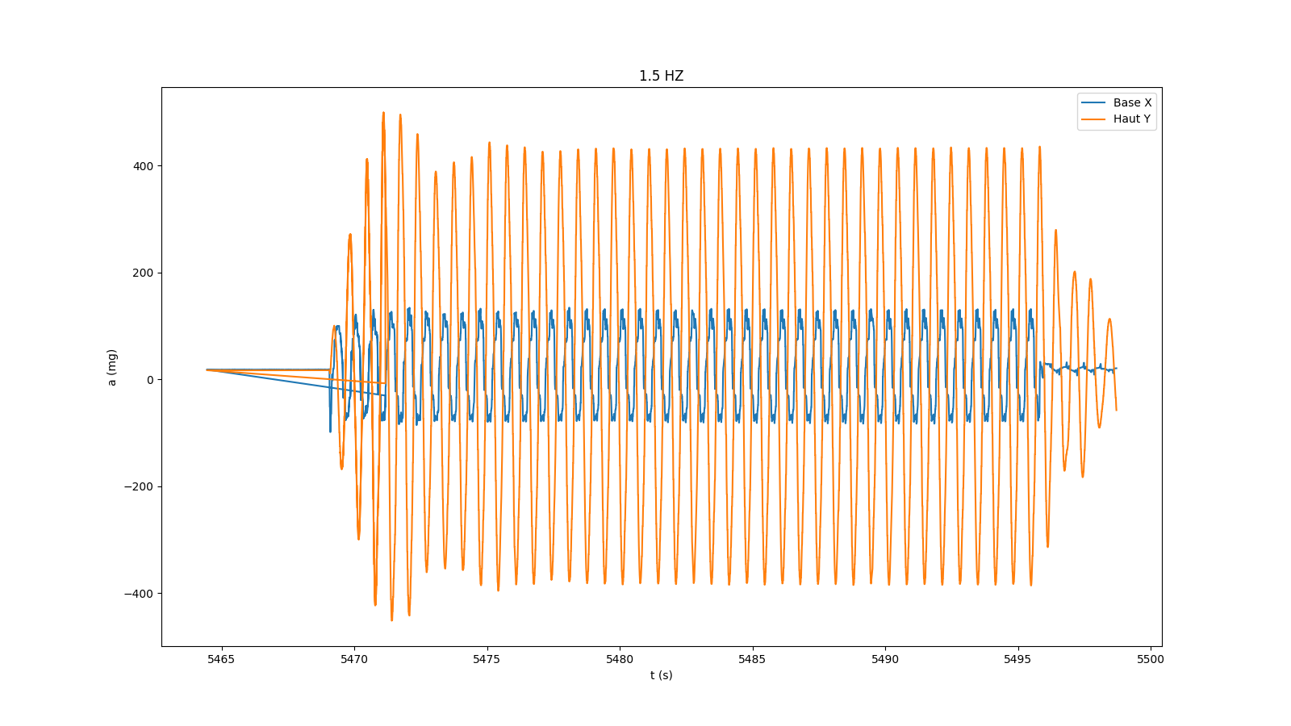
Analyse/Image/Sans masse, tige seule faible amplitude/1.5 HZ.png
