Docredstein/TIPE_TMD/Analyse/Image/Sans masse, tige seule faible amplitude/3 hz.png

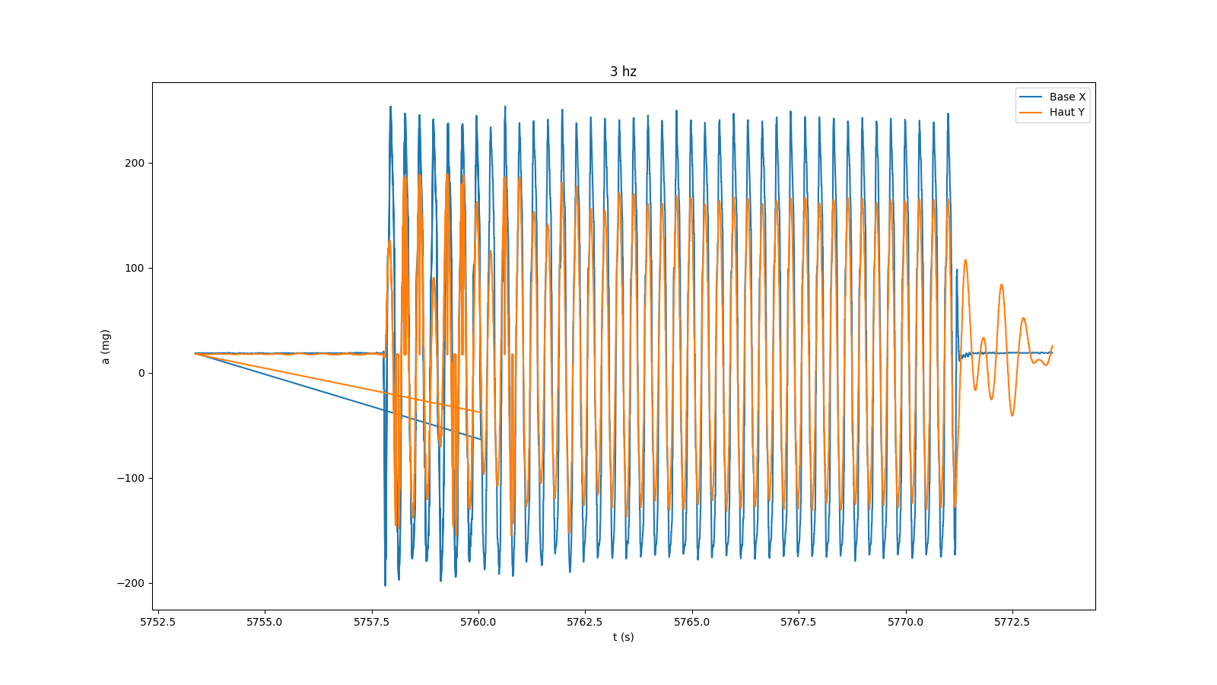
Analyse/Image/Sans masse, tige seule faible amplitude/3 hz.png
