Docredstein/TIPE_TMD/Analyse/Image/Sans masse, tige seule faible amplitude/8Hz.png

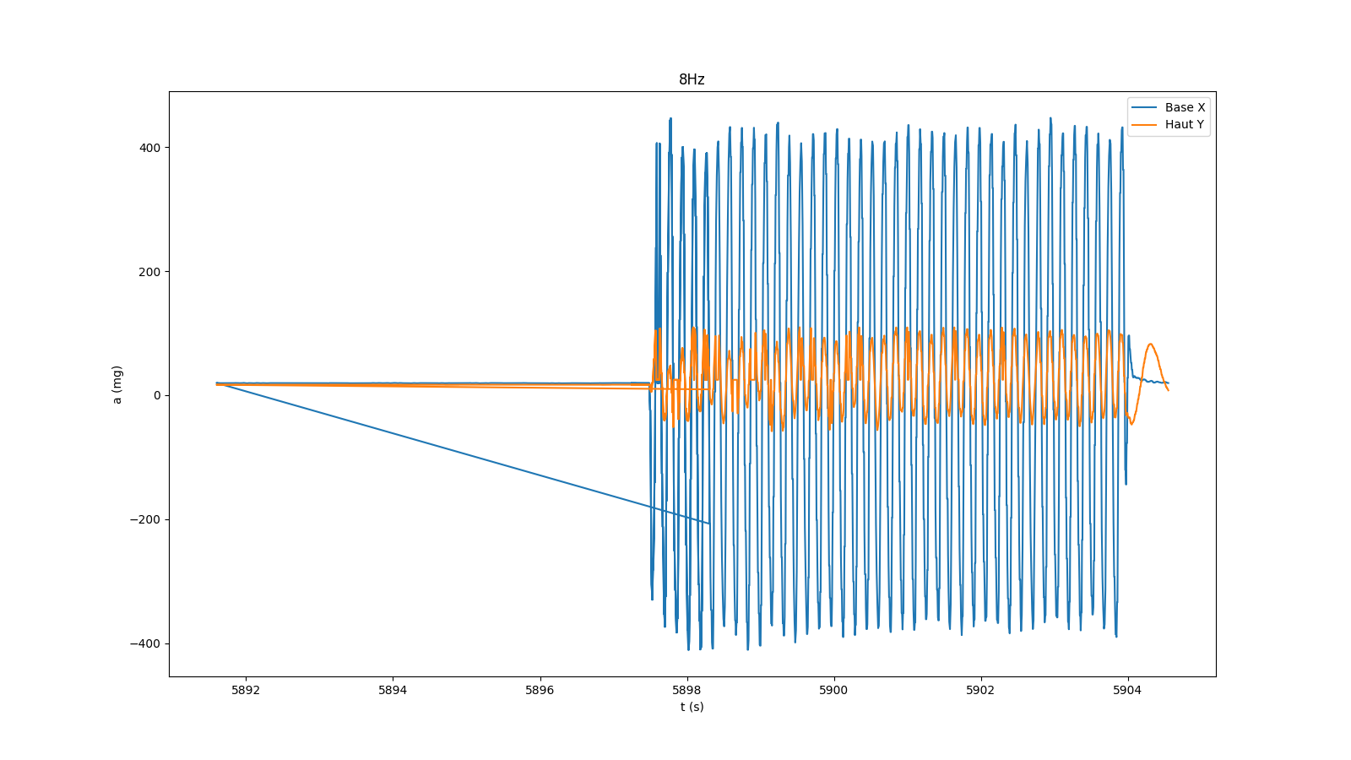
Analyse/Image/Sans masse, tige seule faible amplitude/8Hz.png
