Docredstein/TIPE_TMD/Beamer/Image Noé/Données avec comparaison V2 bonne freq/Pendule 73.3g à 9,4 cm.png

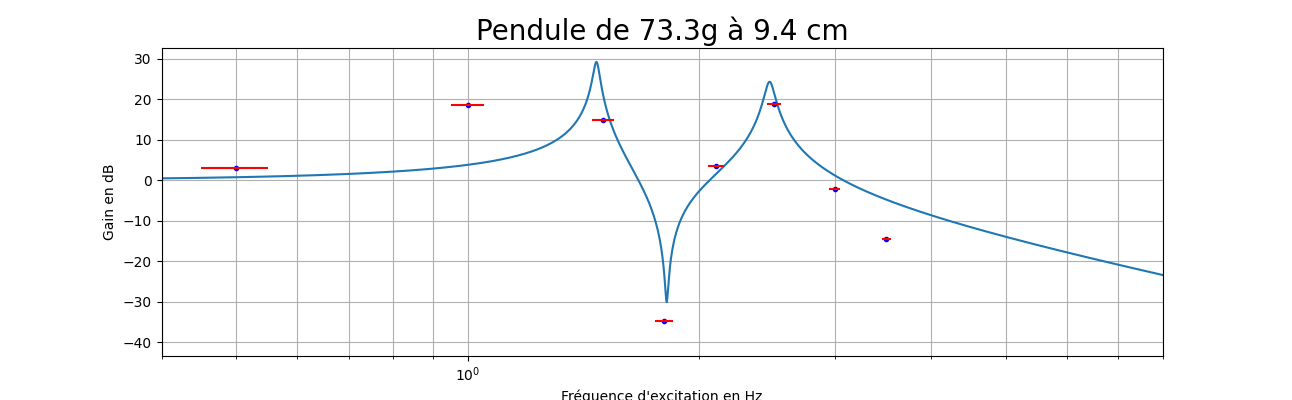
Beamer/Image Noé/Données avec comparaison V2 bonne freq/Pendule 73.3g à 9,4 cm.png
