Docredstein/TIPE_TMD/Beamer/Image Noé/Données avec comparaison V2 bonne freq/Pendule 100g à 5 cm.png

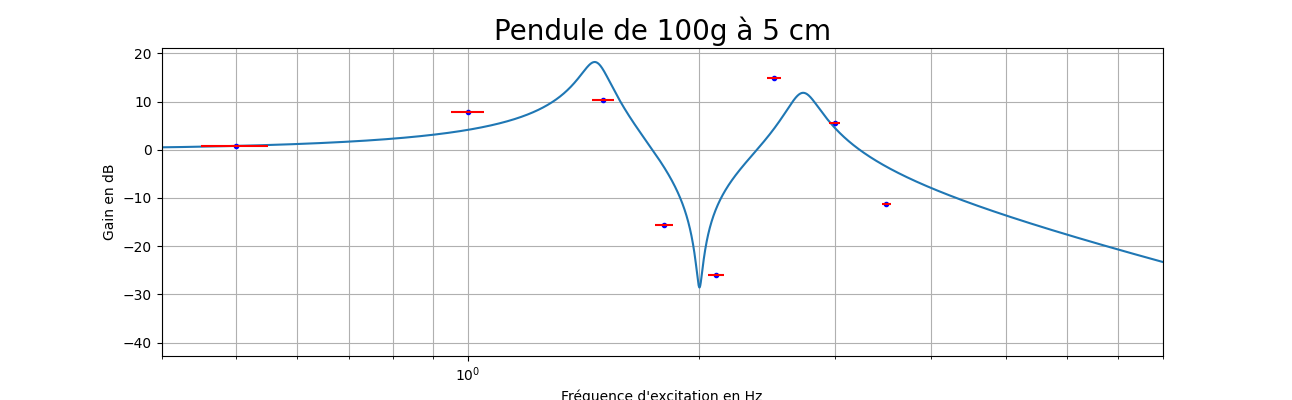
Beamer/Image Noé/Données avec comparaison V2 bonne freq/Pendule 100g à 5 cm.png
