Docredstein/TIPE_TMD/Beamer/Image Noé/Données avec comparaison V2 bonne freq/Sans pendule.png

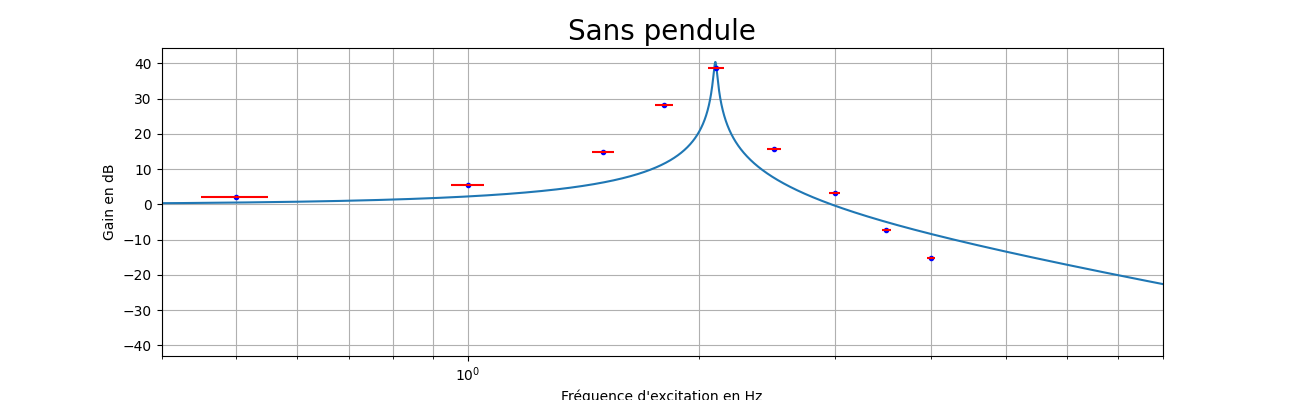
Beamer/Image Noé/Données avec comparaison V2 bonne freq/Sans pendule.png
