Docredstein/TIPE_TMD/Beamer/Image Noé/Modélisation sans frottement.png

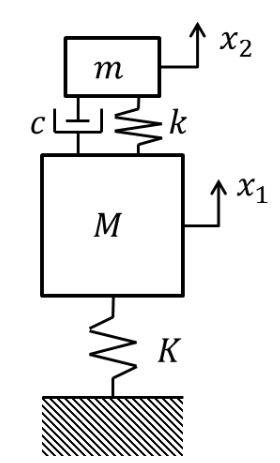
Beamer/Image Noé/Modélisation sans frottement.png
