Docredstein/TIPE_TMD/Beamer/Image Noé/Modélisation sans pendule.png

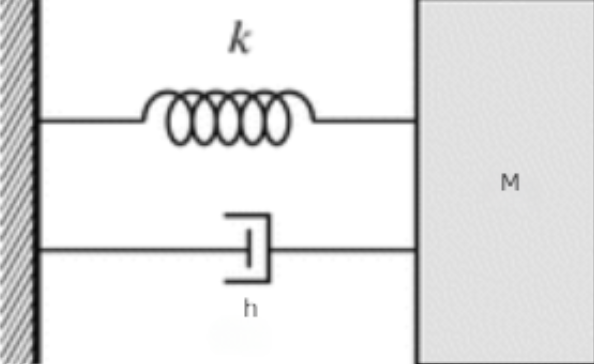
Beamer/Image Noé/Modélisation sans pendule.png
