Docredstein/TIPE_TMD/Beamer/Image Noé/Photos comp/coef raideur-min.png

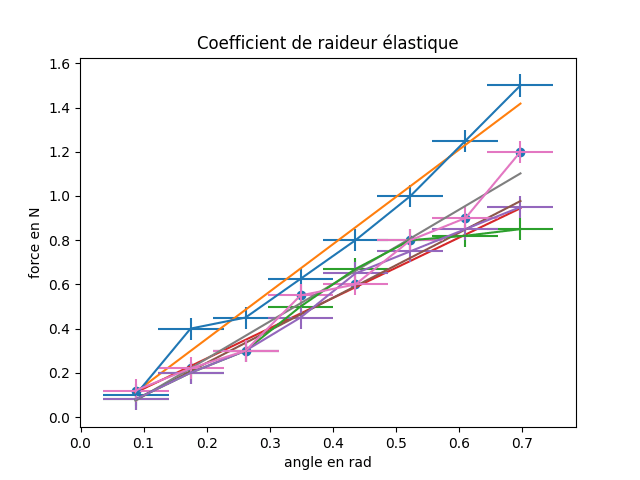
Beamer/Image Noé/Photos comp/coef raideur-min.png
