Docredstein/TIPE_TMD/Beamer/Image Noé/Photos comp/image tmd pont-min.jpg

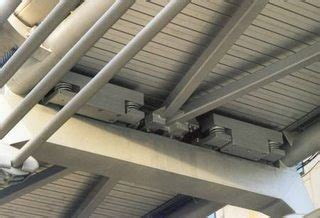
Beamer/Image Noé/Photos comp/image tmd pont-min.jpg
