Docredstein/TIPE_TMD/Beamer/Image Noé/Photos comp/image tour tawai pendule-min.jpg

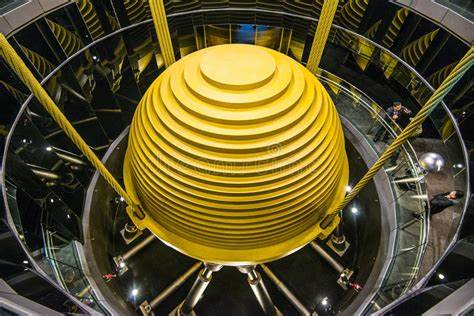
Beamer/Image Noé/Photos comp/image tour tawai pendule-min.jpg
