Docredstein/TIPE_TMD/Beamer/Image Noé/Photos comp/IMG_2609-min.JPG

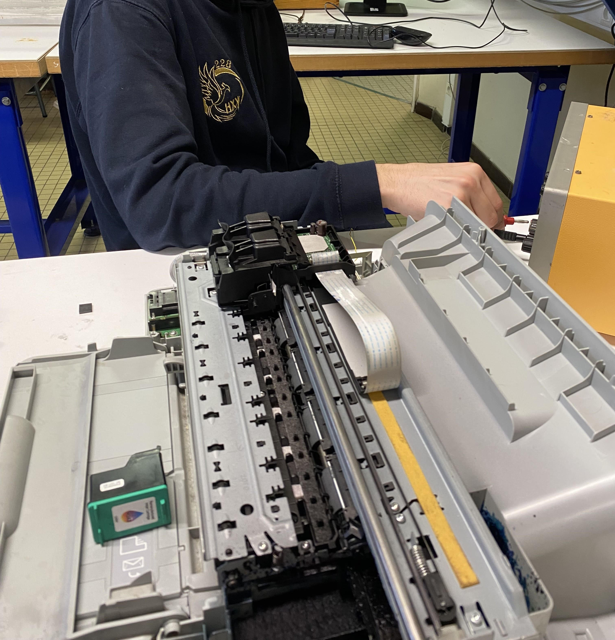
Beamer/Image Noé/Photos comp/IMG_2609-min.JPG
