Docredstein/TIPE_TMD/Beamer/Image Noé/Photos comp/IMG_3367b-min.JPG

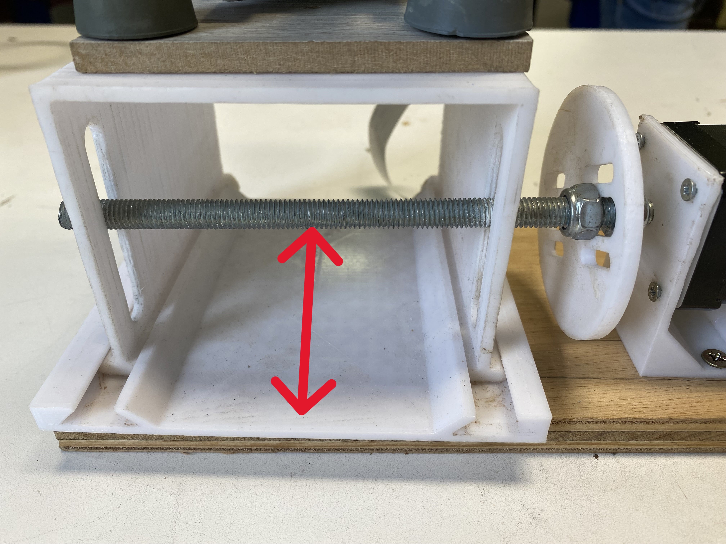
Beamer/Image Noé/Photos comp/IMG_3367b-min.JPG
