Docredstein/TIPE_TMD/Beamer/Image Noé/Photos comp/IMG_3378-min.JPG

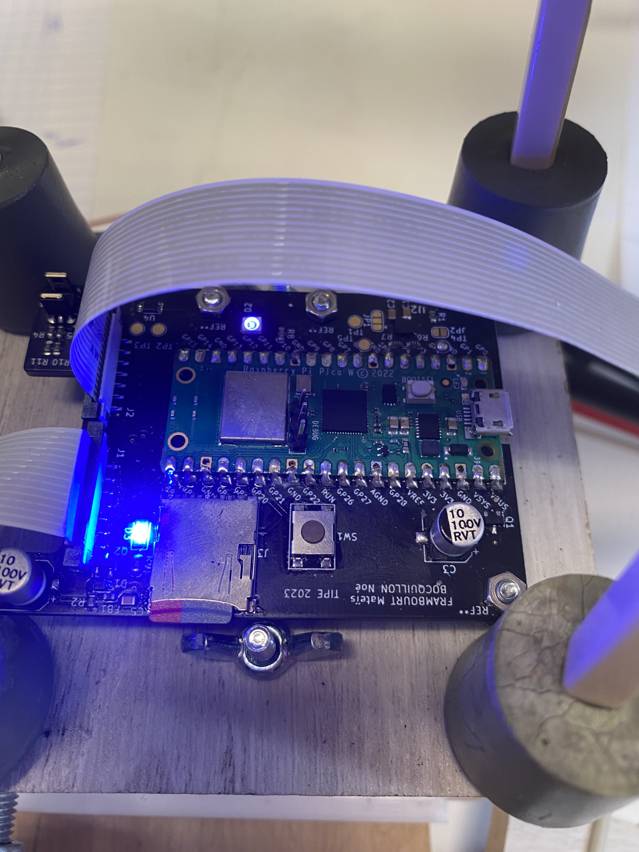
Beamer/Image Noé/Photos comp/IMG_3378-min.JPG
