Docredstein/TIPE_TMD/Beamer/Image Noé/Photos comp/IMG_3380-min.JPG

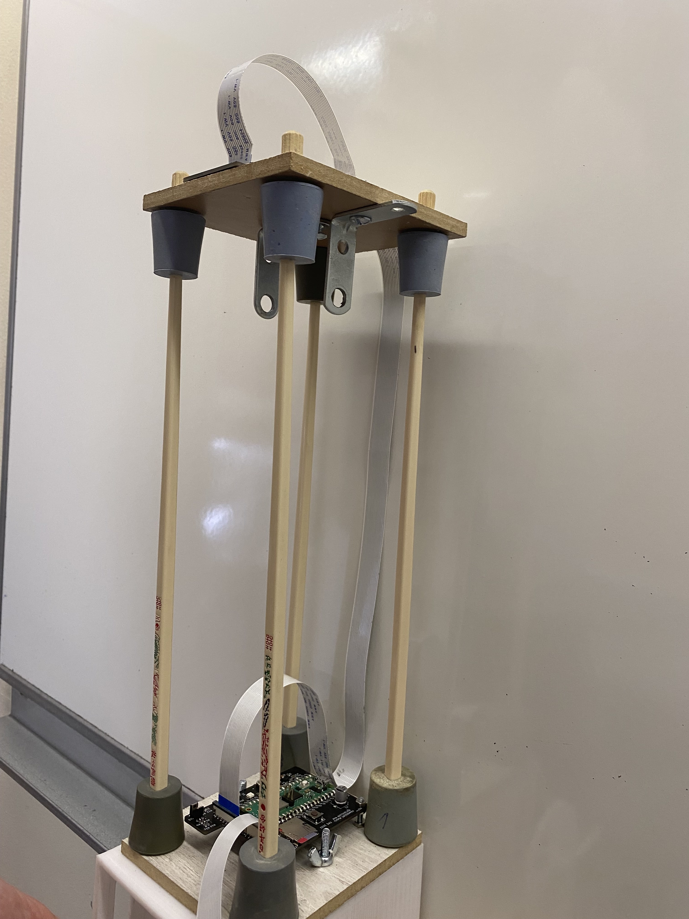
Beamer/Image Noé/Photos comp/IMG_3380-min.JPG
