Docredstein/TIPE_TMD/Beamer/Image Noé/Photos comp/IMG_3412-min.JPG

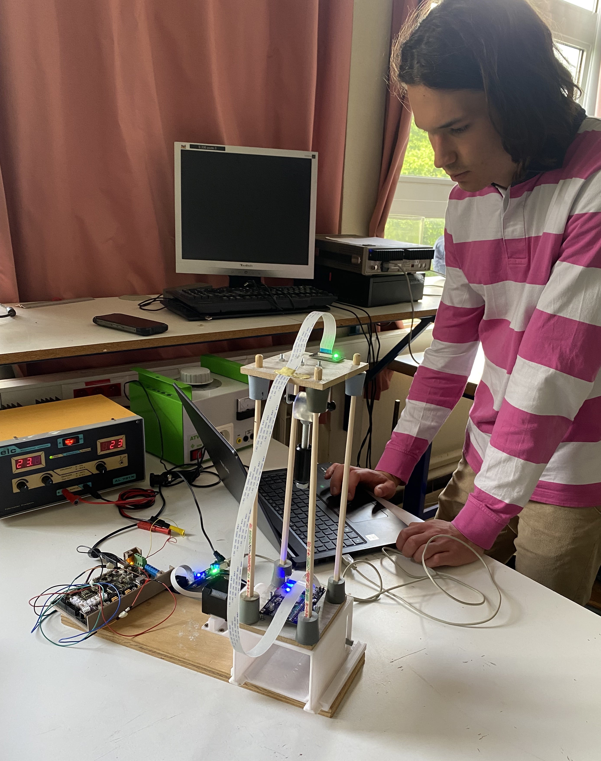
Beamer/Image Noé/Photos comp/IMG_3412-min.JPG
