Docredstein/TIPE_TMD/Beamer/Image Noé/Photos comp/IMG_E3392-min.JPG

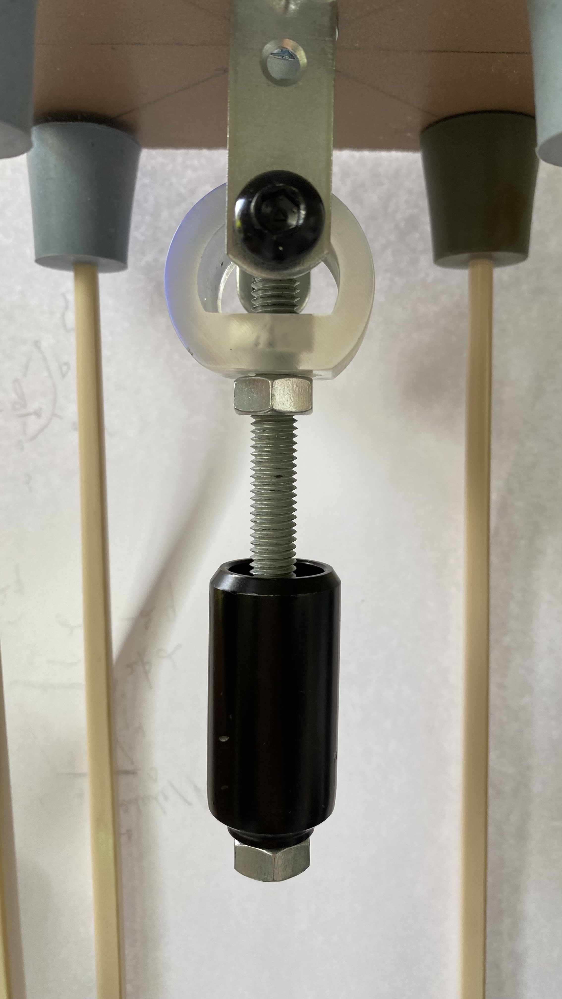
Beamer/Image Noé/Photos comp/IMG_E3392-min.JPG
