Docredstein/TIPE_TMD/Beamer/Image Noé/Photos comp/IMG_E3393-min.JPG

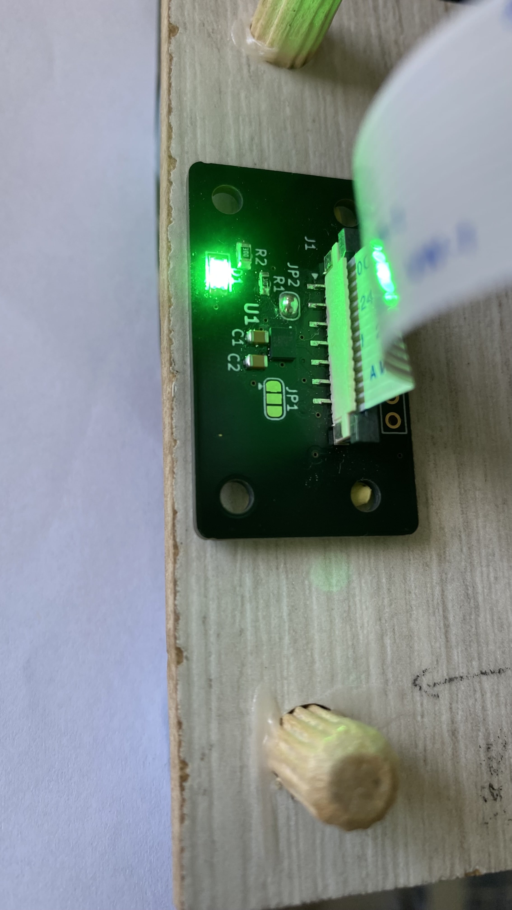
Beamer/Image Noé/Photos comp/IMG_E3393-min.JPG
