Docredstein/TIPE_TMD/Beamer/Image Noé/Photos comp/schéma axe lineaire-min.png

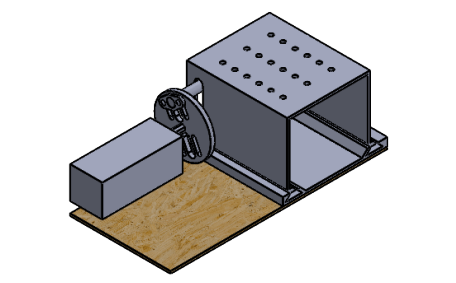
Beamer/Image Noé/Photos comp/schéma axe lineaire-min.png
