Docredstein/TIPE_TMD/Beamer/Image Noé/Photos comp/sw axe linéaire-min.png

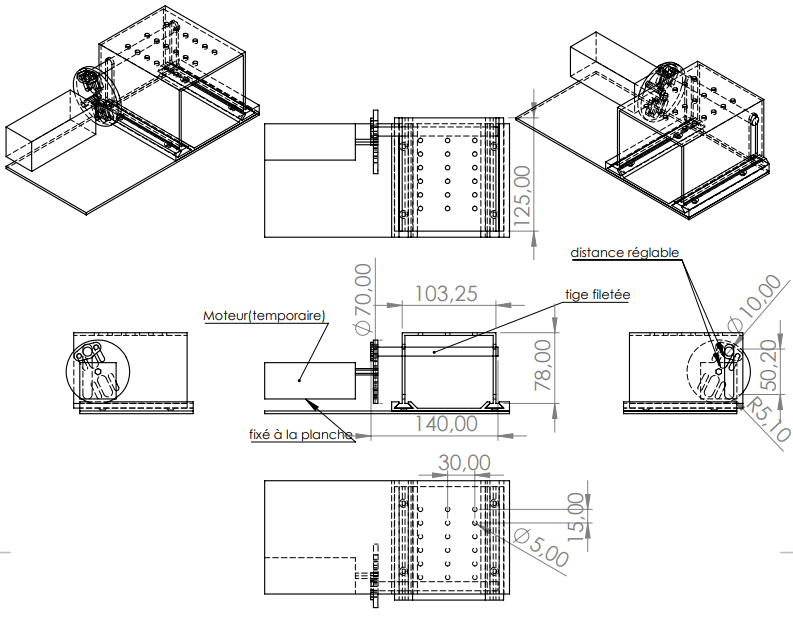
Beamer/Image Noé/Photos comp/sw axe linéaire-min.png
