Docredstein/TIPE_TMD/Beamer/Image Noé/Photos comp/valeur coef raideur-min.png

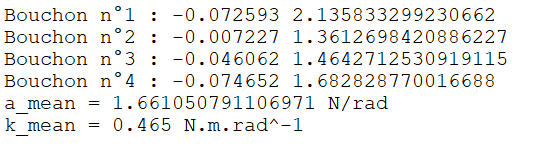
Beamer/Image Noé/Photos comp/valeur coef raideur-min.png
