Docredstein/TIPE_TMD/Beamer/Image/Axe en 1-4 bas.jpg

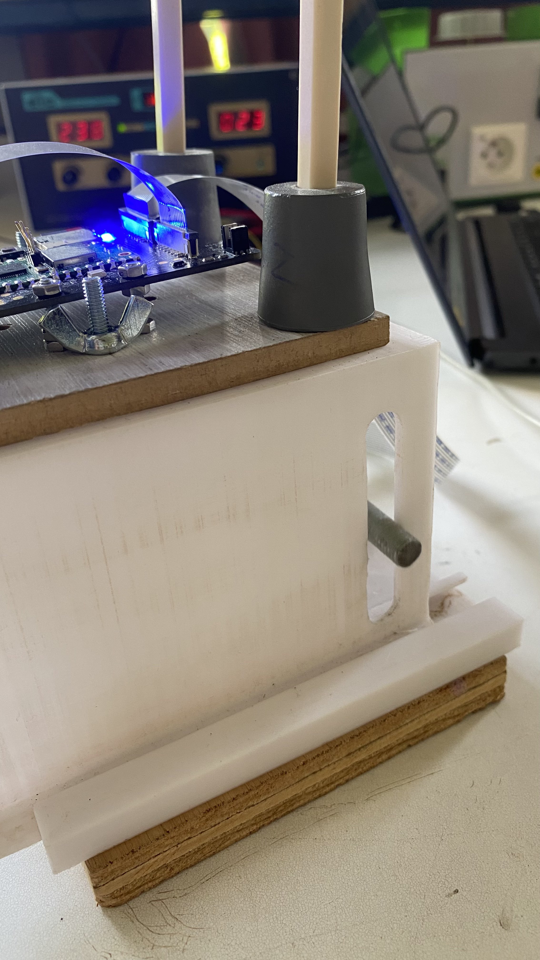
Beamer/Image/Axe en 1-4 bas.jpg
