Docredstein/TIPE_TMD/Beamer/Image/Axe en bas.jpg

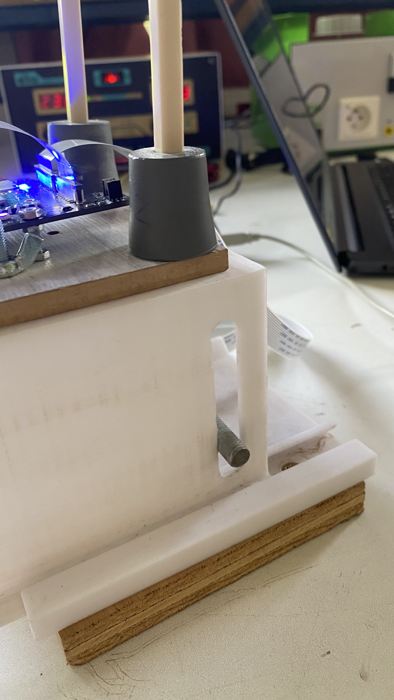
Beamer/Image/Axe en bas.jpg
