Docredstein/TIPE_TMD/Beamer/Image/Axe moitié bas.jpg

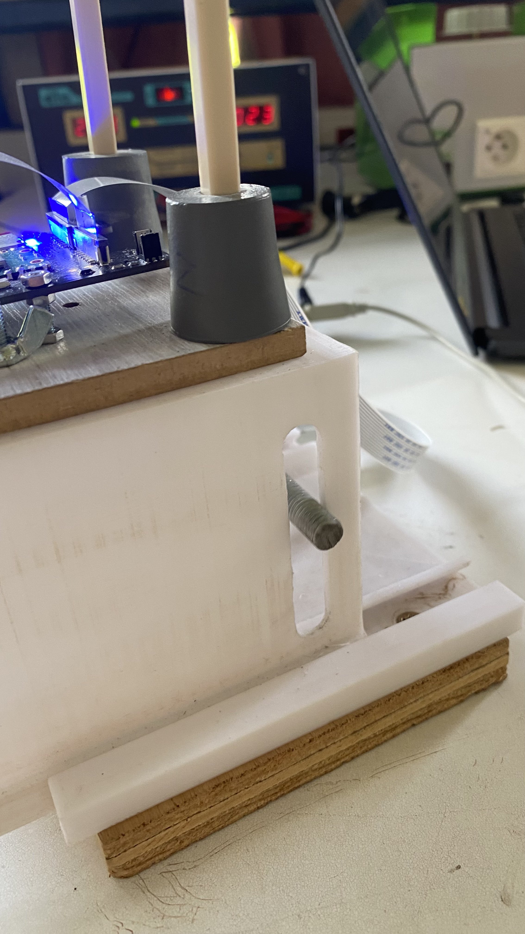
Beamer/Image/Axe moitié bas.jpg
