Docredstein/TIPE_TMD/Beamer/Image/Branchement carte.JPG

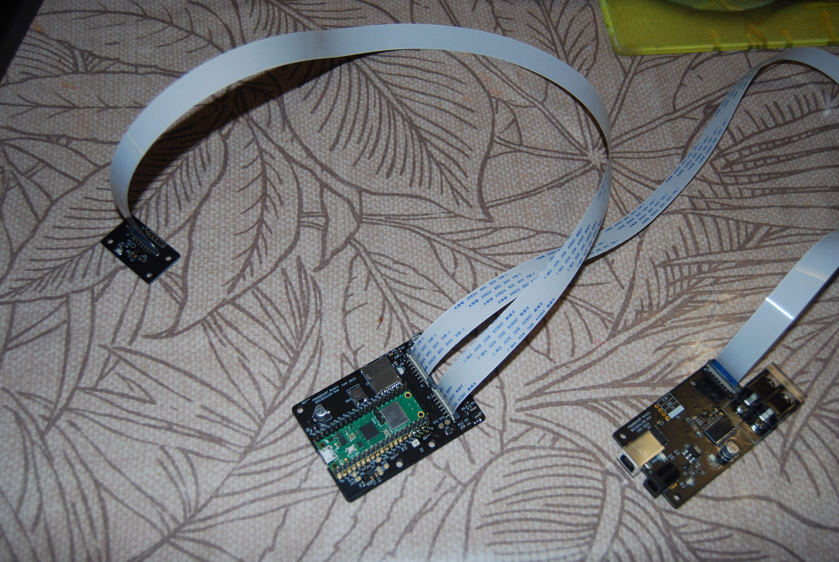
Beamer/Image/Branchement carte.JPG
