Docredstein/TIPE_TMD/Beamer/Image/Carte fixe.jpg

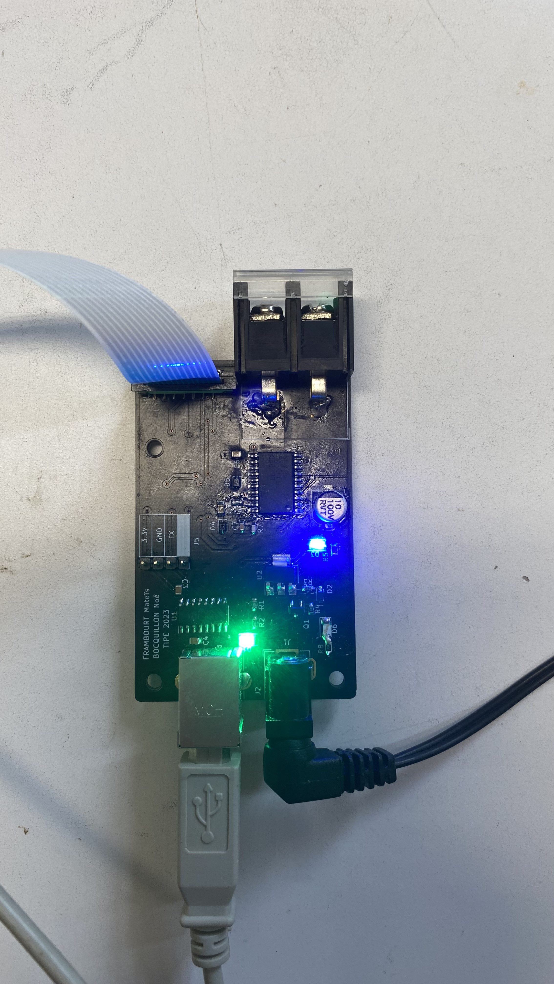
Beamer/Image/Carte fixe.jpg
