Docredstein/TIPE_TMD/Beamer/Image/Carte Imprimante.jpg

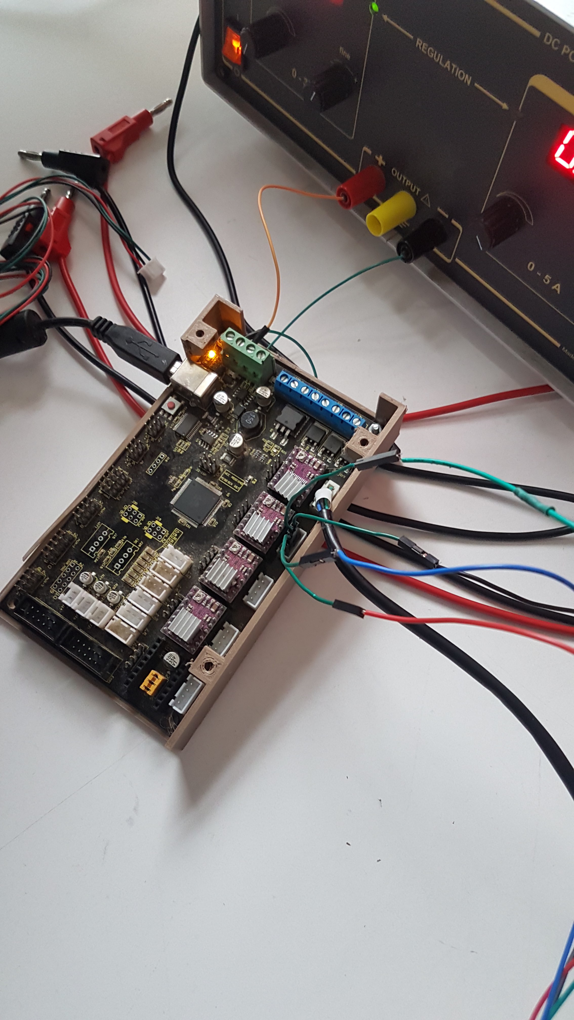
Beamer/Image/Carte Imprimante.jpg
