Docredstein/TIPE_TMD/Beamer/Image/Carte principale.jpg

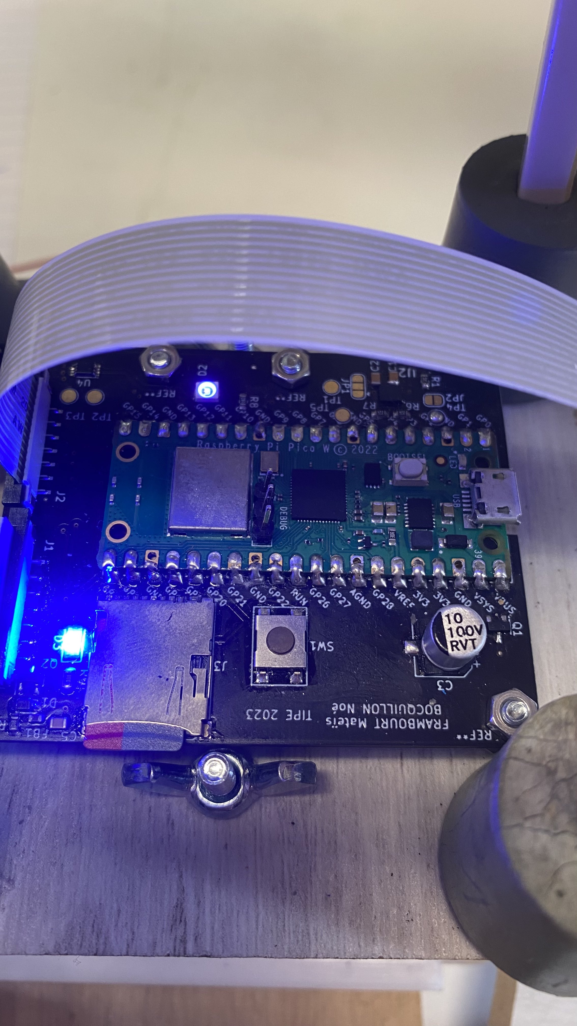
Beamer/Image/Carte principale.jpg
