Docredstein/TIPE_TMD/Beamer/Image/Excentrique arrière.jpg

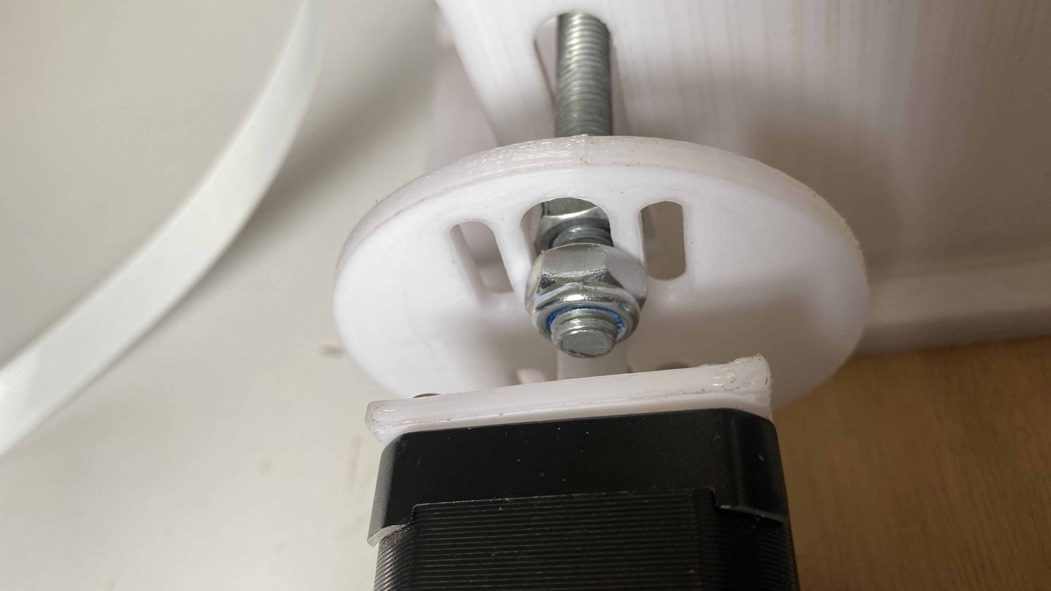
Beamer/Image/Excentrique arrière.jpg
