Docredstein/TIPE_TMD/Beamer/Image/Fixation accéléromètre profil 2.jpg

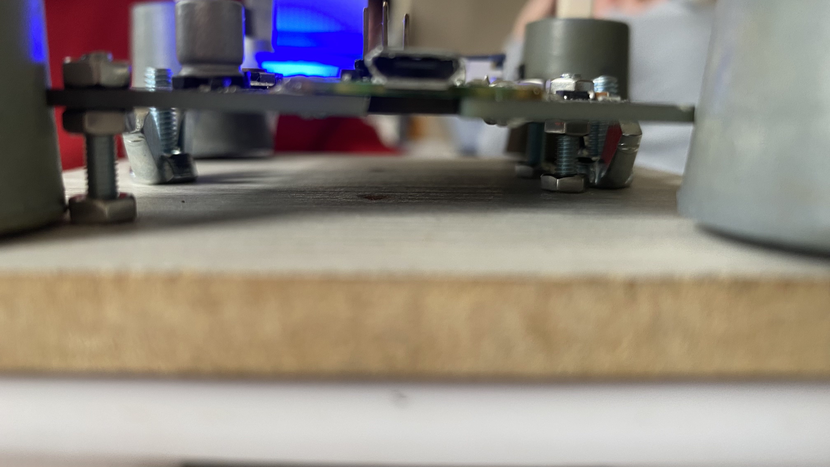
Beamer/Image/Fixation accéléromètre profil 2.jpg
