Docredstein/TIPE_TMD/Beamer/Image/Fixation accéléromètre profil 3.jpg

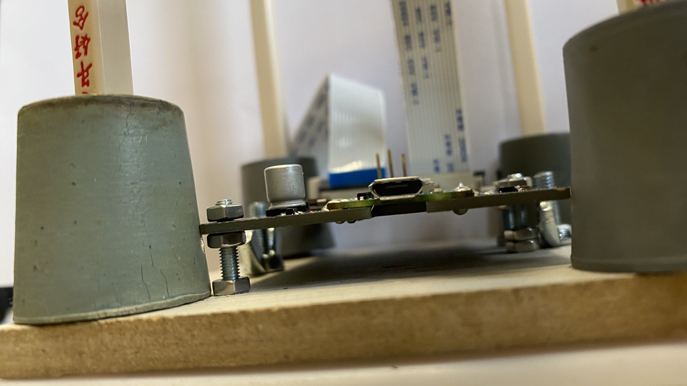
Beamer/Image/Fixation accéléromètre profil 3.jpg
