Docredstein/TIPE_TMD/Beamer/Image/Fixation accéléromètre profil.jpg

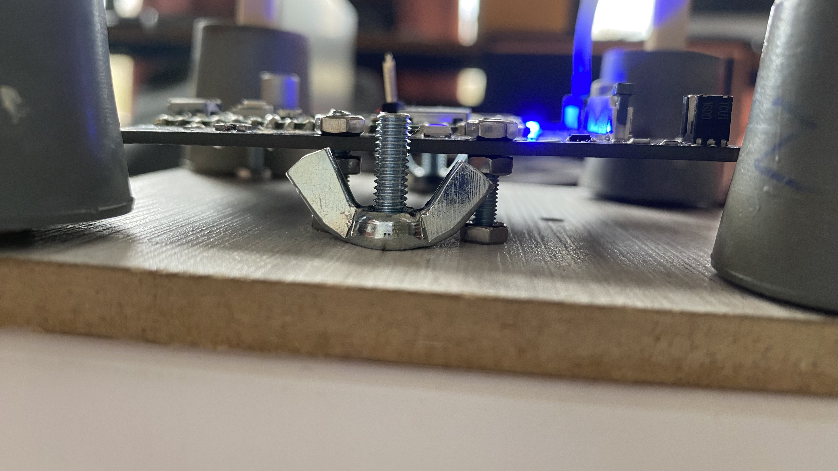
Beamer/Image/Fixation accéléromètre profil.jpg
