Docredstein/TIPE_TMD/Beamer/Image/Fixation excentrique.jpg

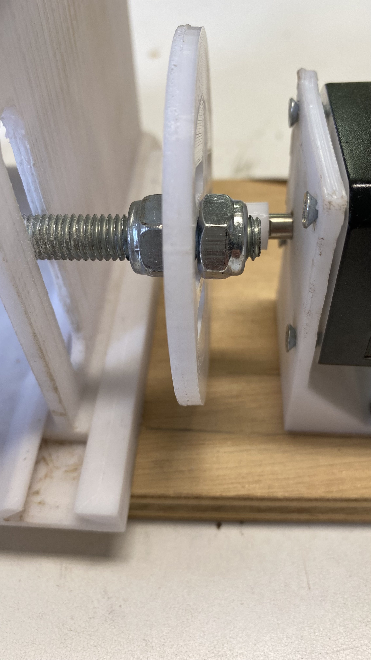
Beamer/Image/Fixation excentrique.jpg
