Docredstein/TIPE_TMD/Beamer/Image/Fixation modèle flexible.jpg

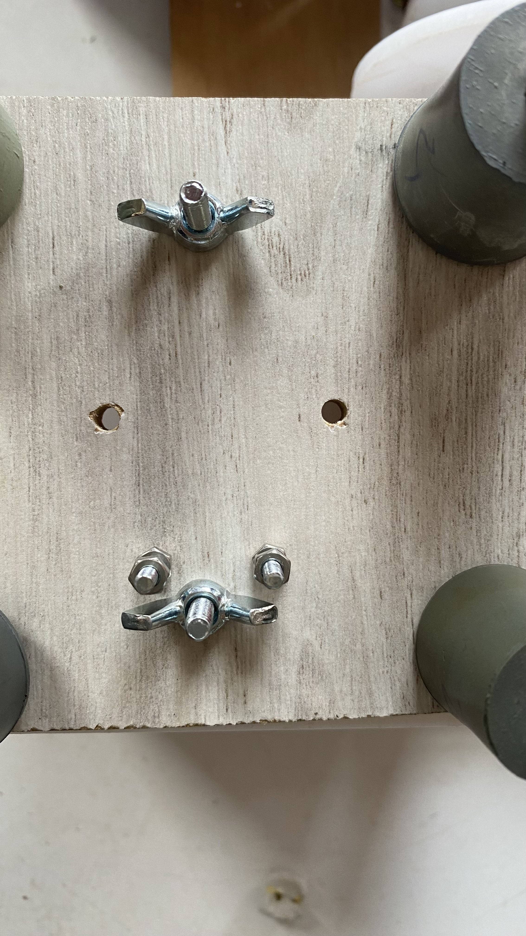
Beamer/Image/Fixation modèle flexible.jpg
