Docredstein/TIPE_TMD/Beamer/Image/Fixation profil modèle flexible.jpg

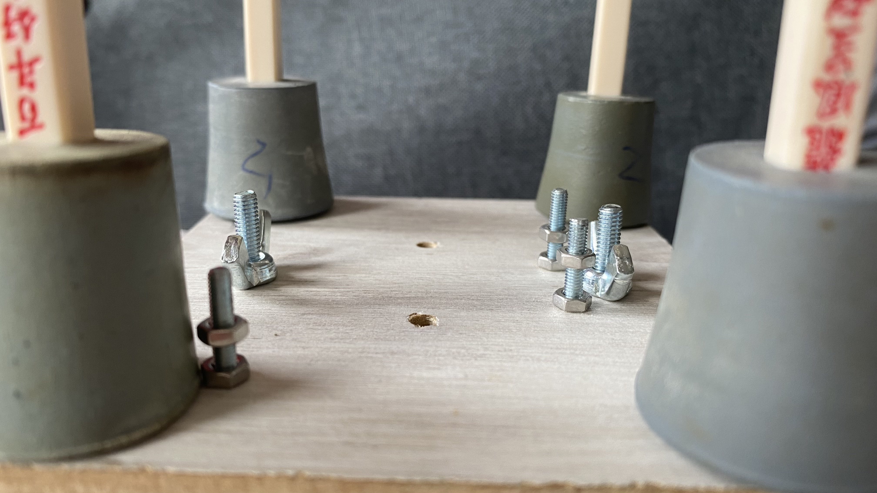
Beamer/Image/Fixation profil modèle flexible.jpg
