Docredstein/TIPE_TMD/Beamer/Image/Glissière.jpg

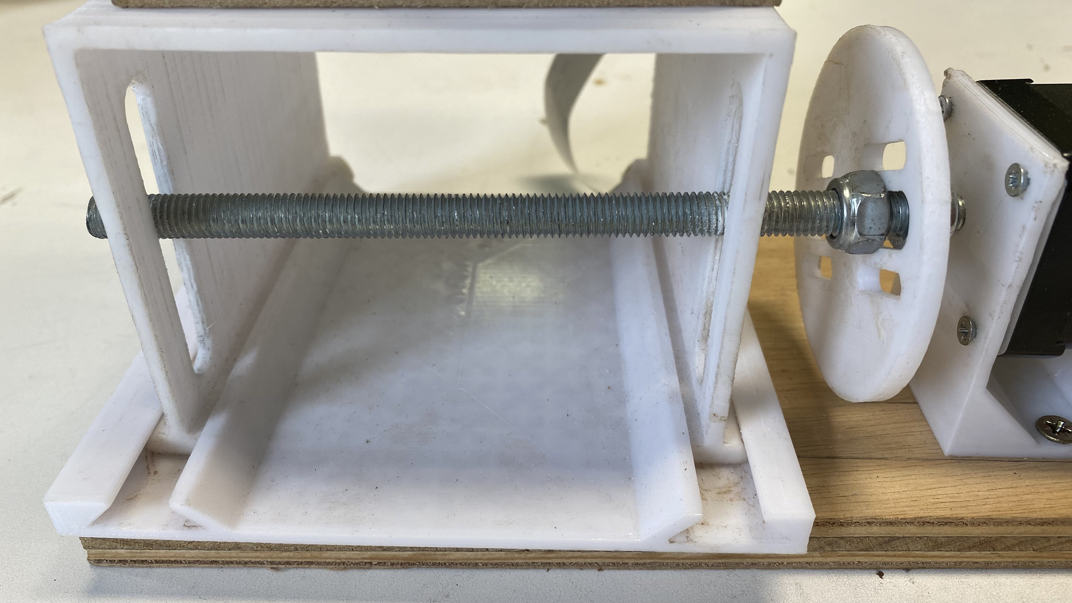
Beamer/Image/Glissière.jpg
