Docredstein/TIPE_TMD/Beamer/Image/Imprimante Mateïs.jpg

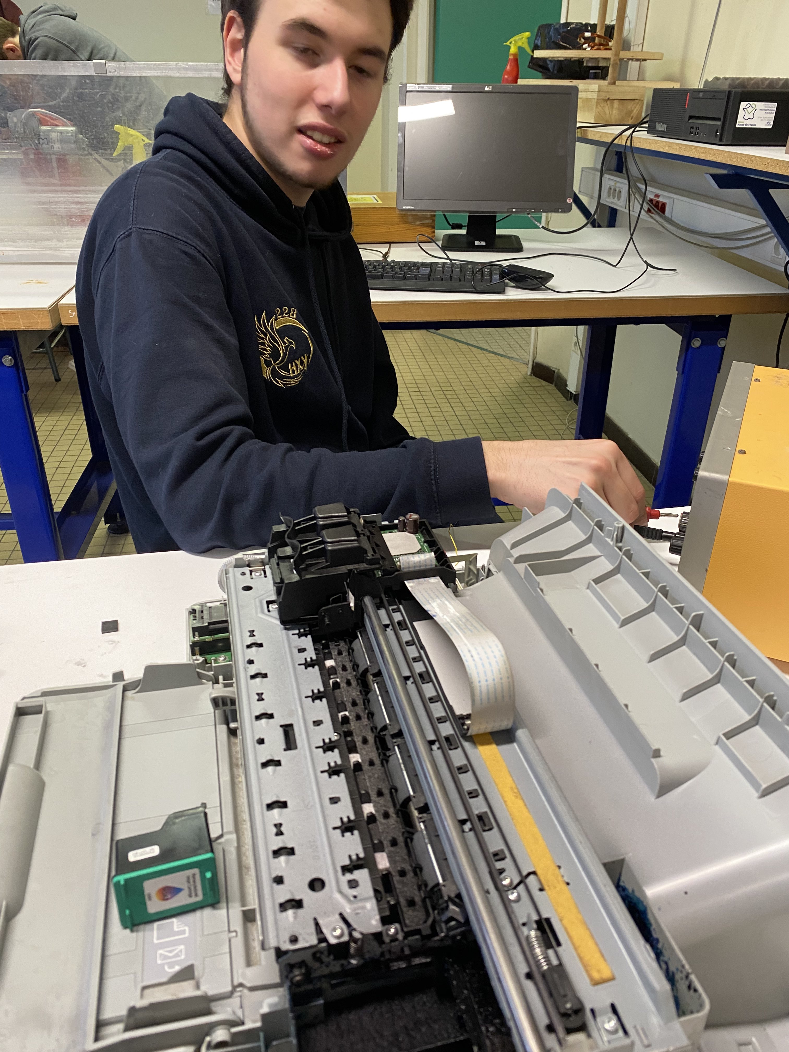
Beamer/Image/Imprimante Mateïs.jpg
