Docredstein/TIPE_TMD/Beamer/Image/Lecture Accéléromètre.jpg

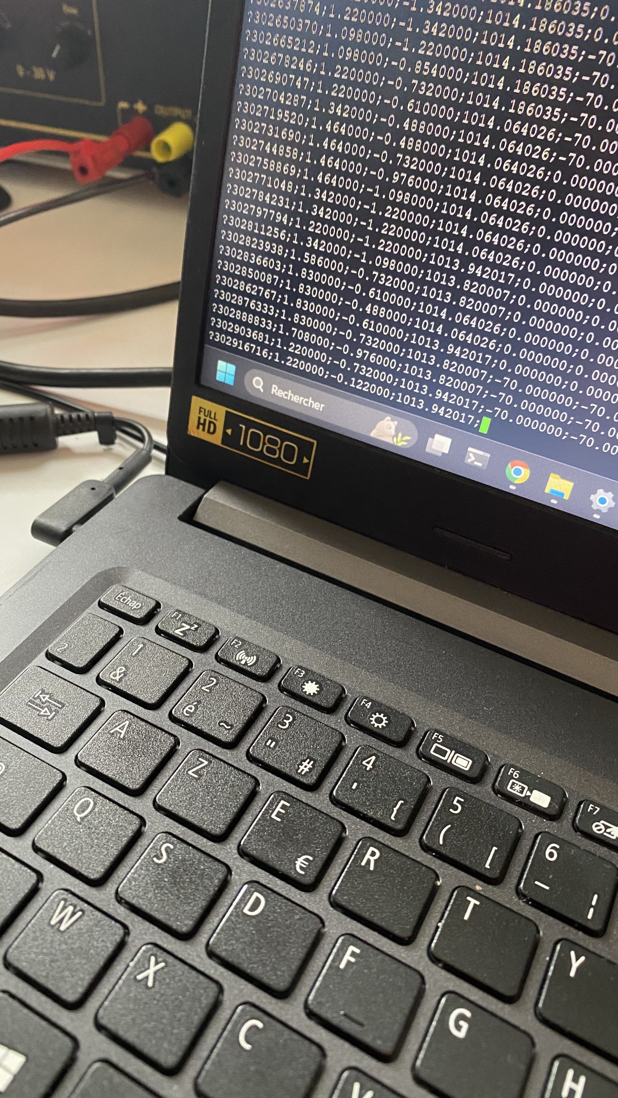
Beamer/Image/Lecture Accéléromètre.jpg
