Docredstein/TIPE_TMD/Beamer/Image/Mateïs Règle alimentation.jpg

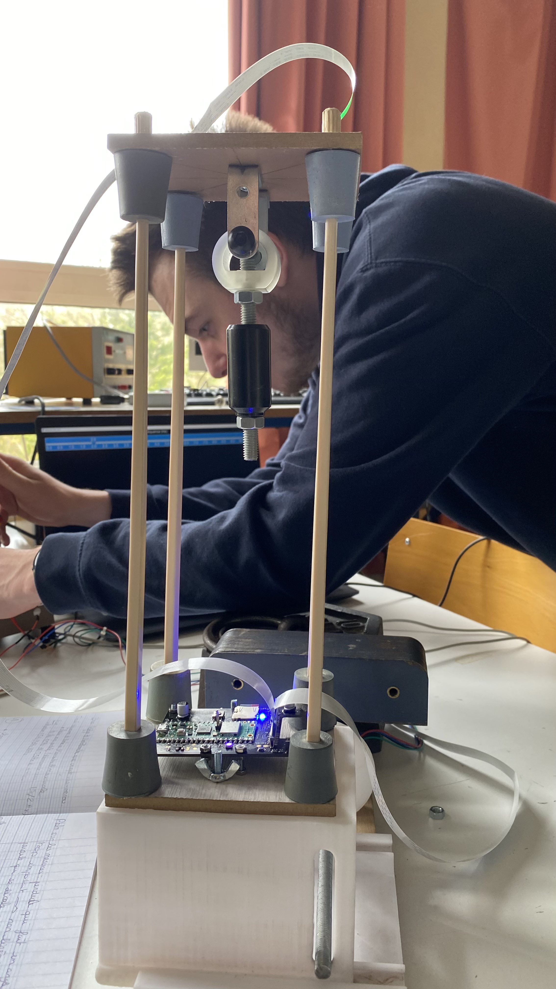
Beamer/Image/Mateïs Règle alimentation.jpg
