Docredstein/TIPE_TMD/Beamer/Image/Mateïs Travail final.jpg

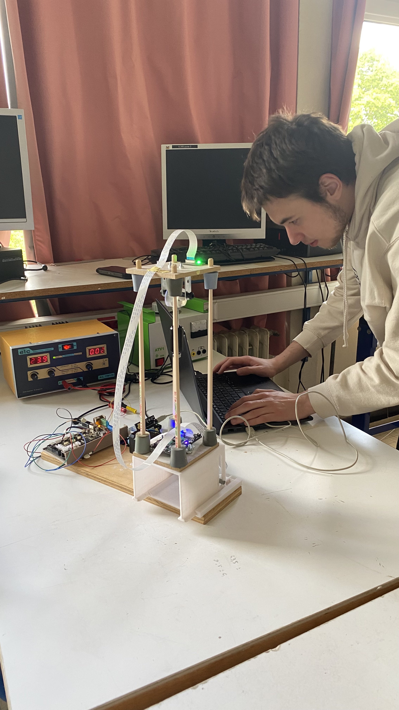
Beamer/Image/Mateïs Travail final.jpg
