Docredstein/TIPE_TMD/Beamer/Image/Modèle solide Face.jpg

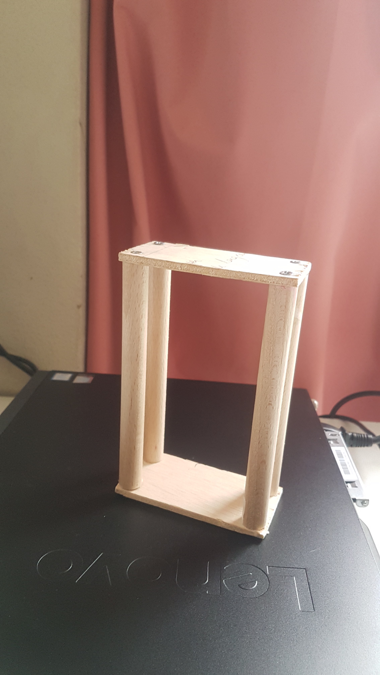
Beamer/Image/Modèle solide Face.jpg
