Docredstein/TIPE_TMD/Beamer/Image/Noé roation axe 2.jpg

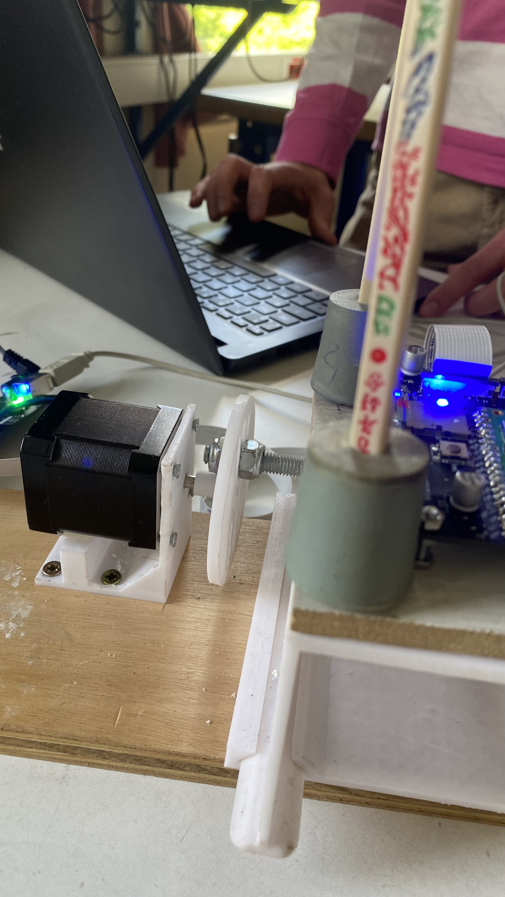
Beamer/Image/Noé roation axe 2.jpg
