Docredstein/TIPE_TMD/Beamer/Image/Noé roation axe 3.jpg

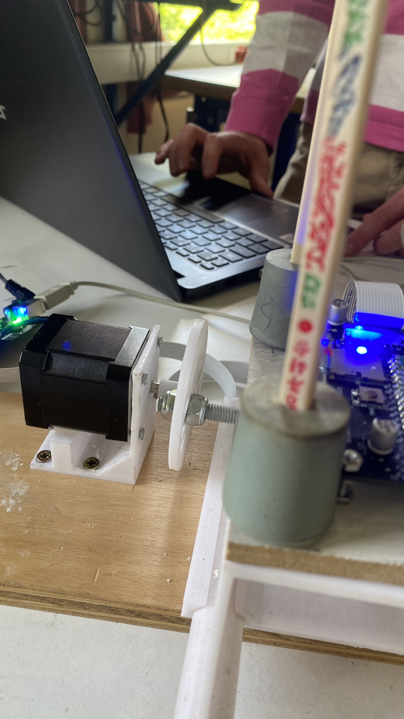
Beamer/Image/Noé roation axe 3.jpg
