Docredstein/TIPE_TMD/Beamer/Image/Noé roation axe .jpg

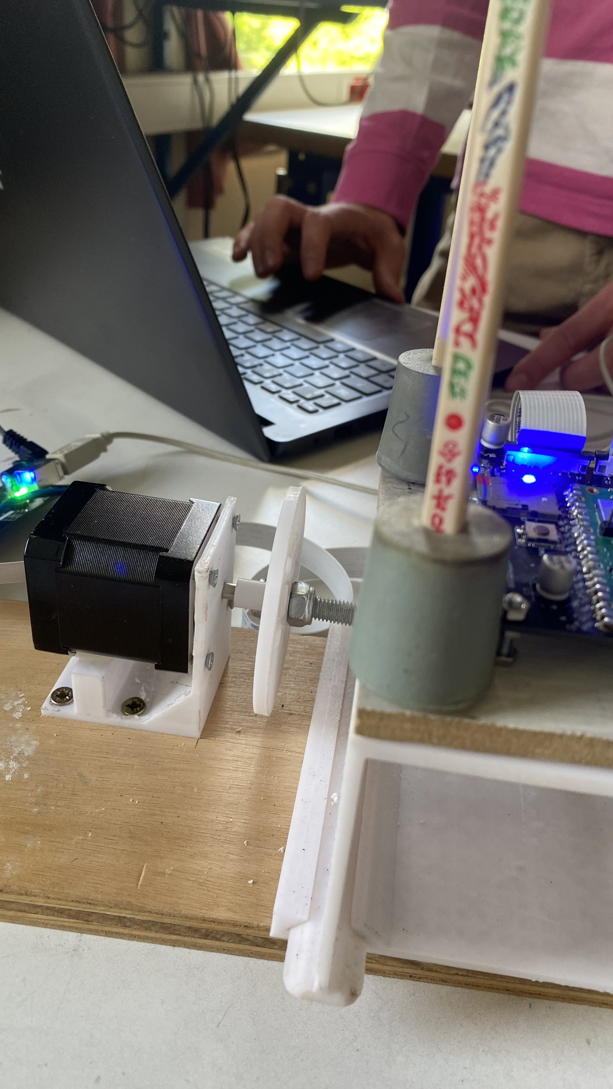
Beamer/Image/Noé roation axe .jpg
