Docredstein/TIPE_TMD/Beamer/Image/Pendule réglable 3.jpg

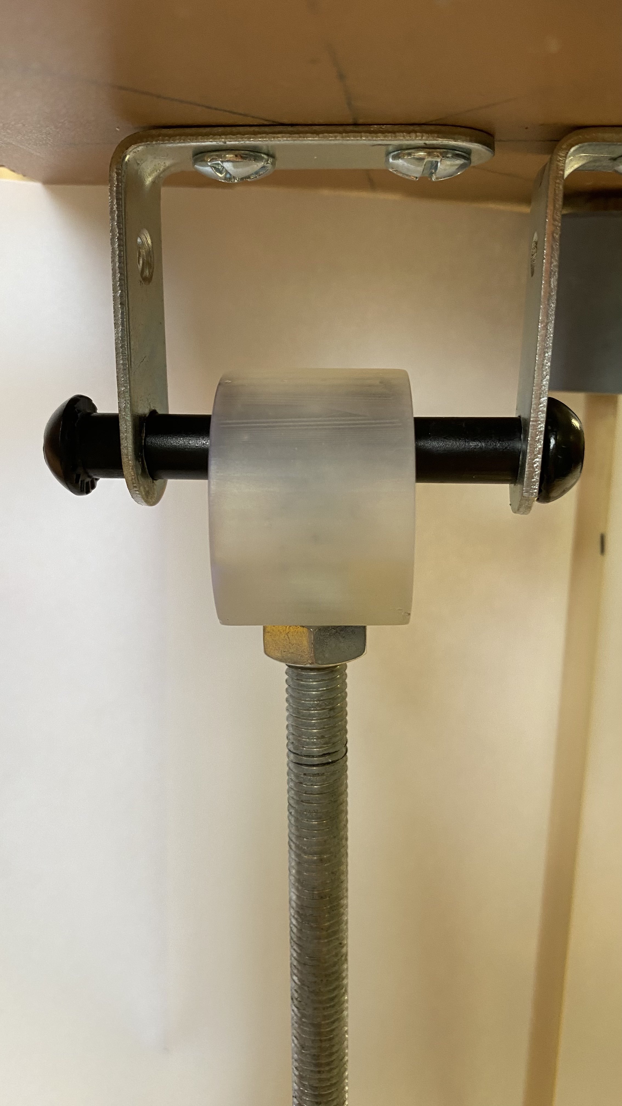
Beamer/Image/Pendule réglable 3.jpg
