Docredstein/TIPE_TMD/Beamer/Image/Tour déformé Mateïs.jpg

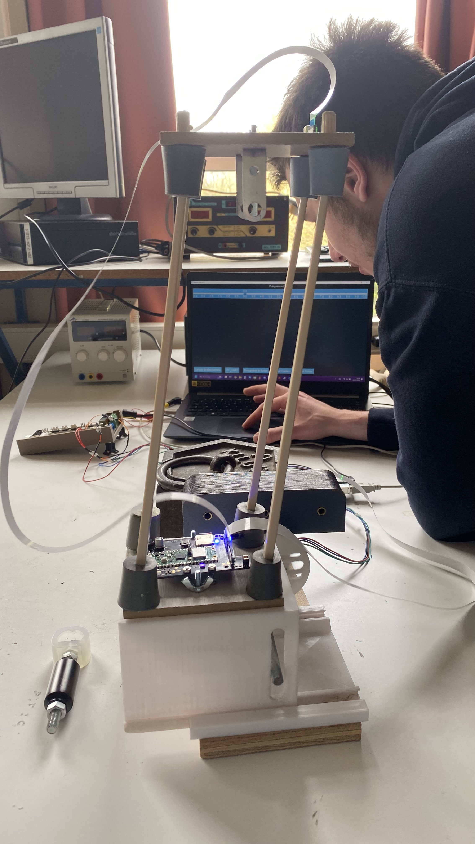
Beamer/Image/Tour déformé Mateïs.jpg
