Docredstein/TIPE_TMD/Beamer/Image/Tour flexible sur tableau blanc profil.jpg

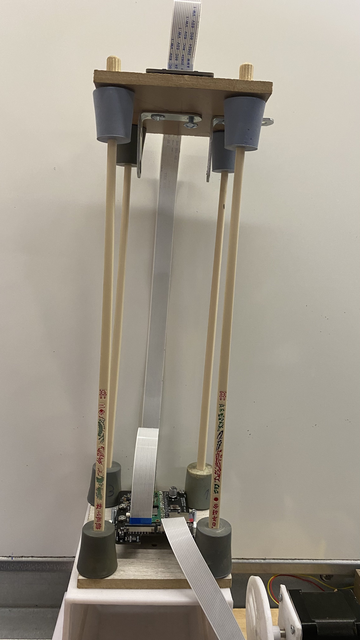
Beamer/Image/Tour flexible sur tableau blanc profil.jpg
