Docredstein/TIPE_TMD/Beamer/Image/Tour masse en bas profil.jpg

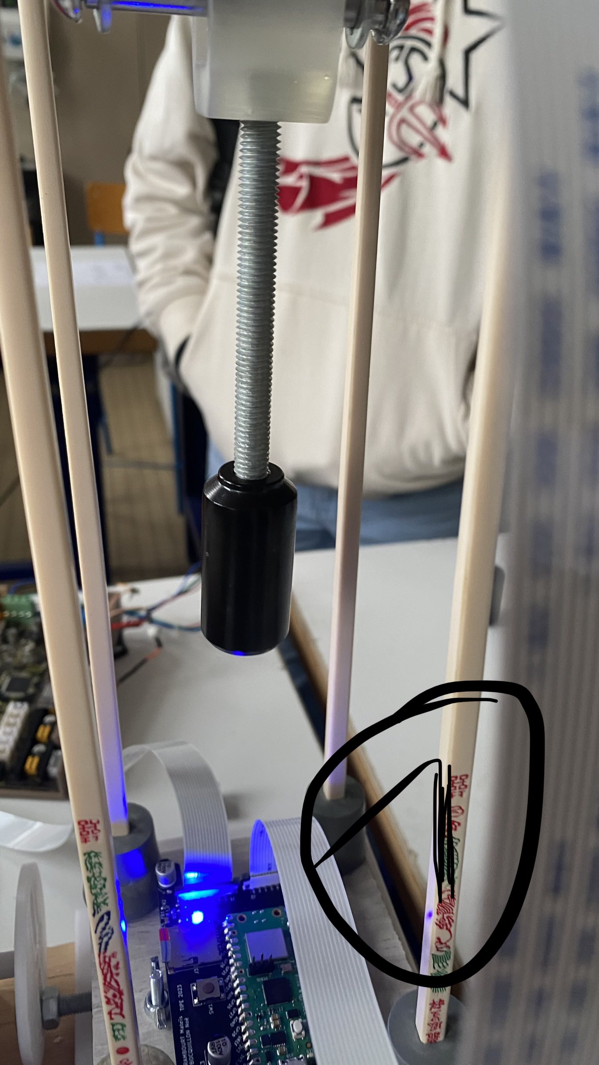
Beamer/Image/Tour masse en bas profil.jpg
