Docredstein/TIPE_TMD/Beamer/Image/tour masse milieu profil.jpg

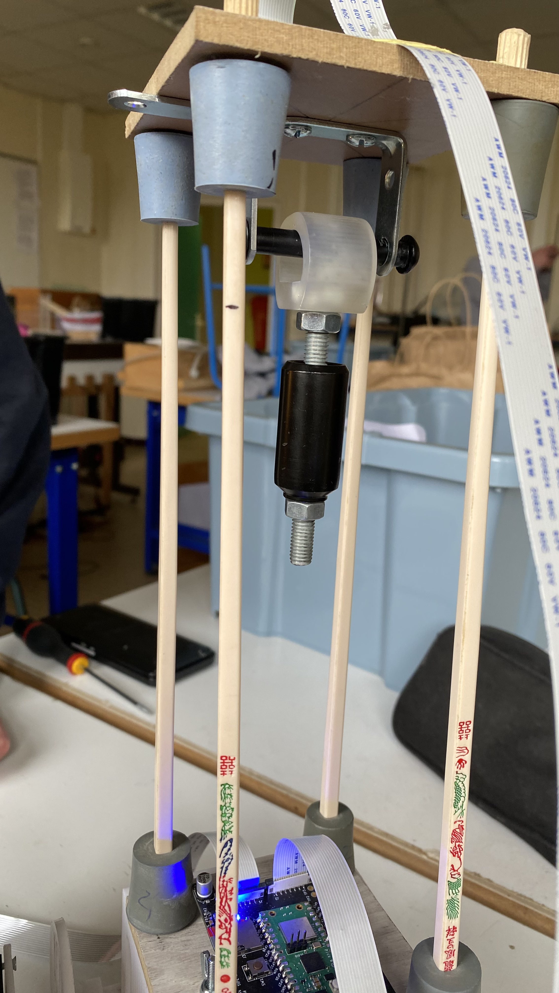
Beamer/Image/tour masse milieu profil.jpg
