Docredstein/TIPE_TMD/Beamer/Image/Tour Mateïs.jpg

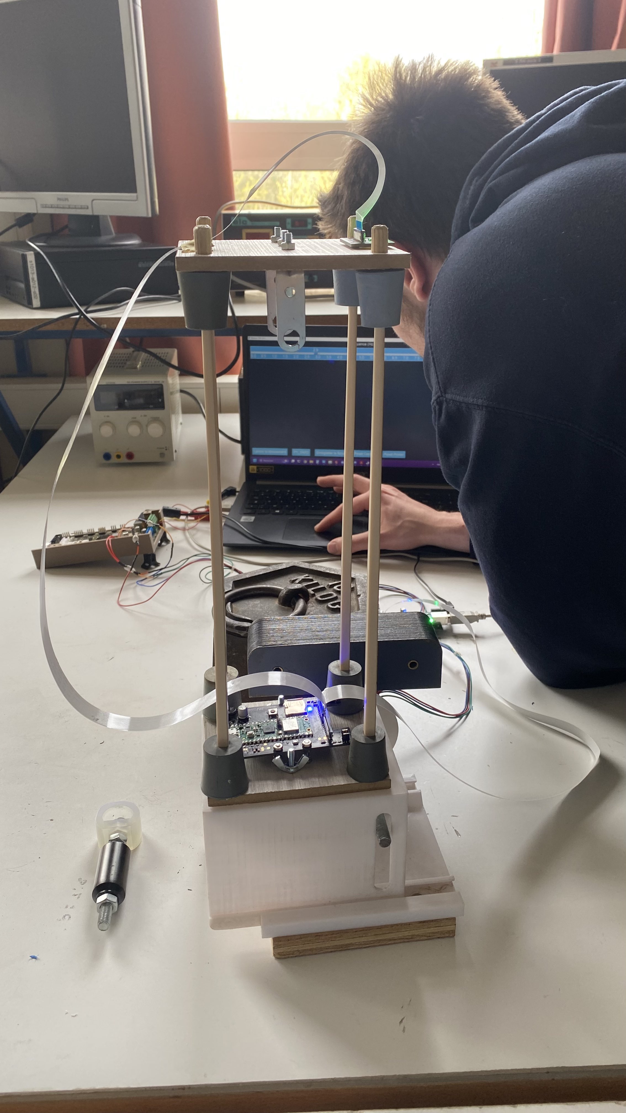
Beamer/Image/Tour Mateïs.jpg
