Docredstein/TIPE_TMD/Beamer/Image/Tour à vide profil.jpg

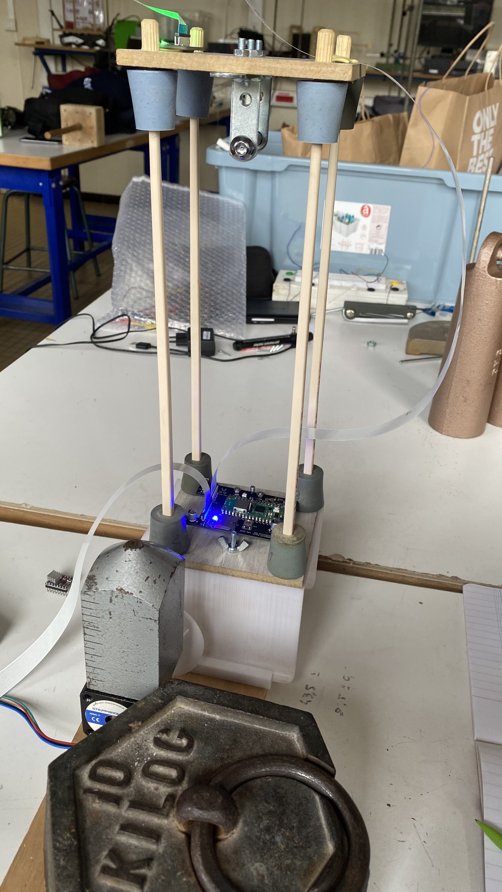
Beamer/Image/Tour à vide profil.jpg
