Docredstein/TIPE_TMD/Beamer/Image/Travail noé final.jpg

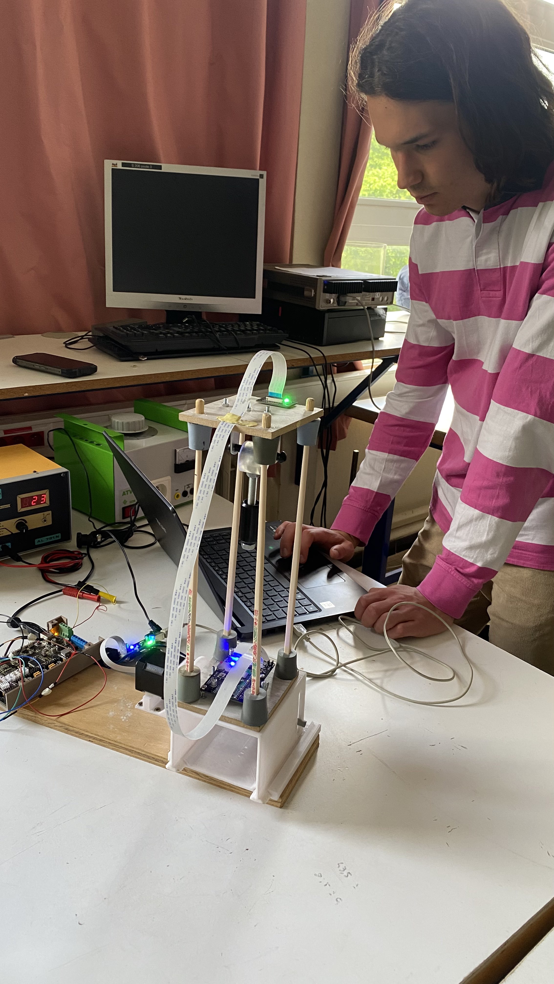
Beamer/Image/Travail noé final.jpg
