Docredstein/TIPE_TMD/Circuit imprimé/Axe_linéaire/base.png

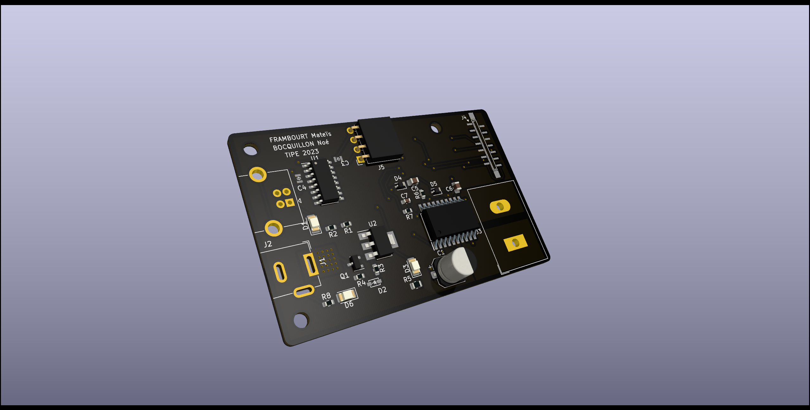
Circuit imprimé/Axe_linéaire/base.png
