Docredstein/TIPE_TMD/Circuit imprimé/Axe_linéaire/c1af472d44001d6aa08ace14bd3ddd9724c6c9ce_hq.jpg

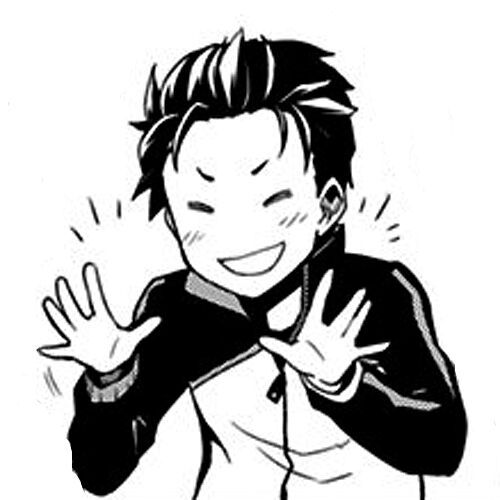
Circuit imprimé/Axe_linéaire/c1af472d44001d6aa08ace14bd3ddd9724c6c9ce_hq.jpg
