Docredstein/TIPE_TMD/Circuit imprimé/Axe_linéaire/Capture d’écran 2023-02-14 005251.png

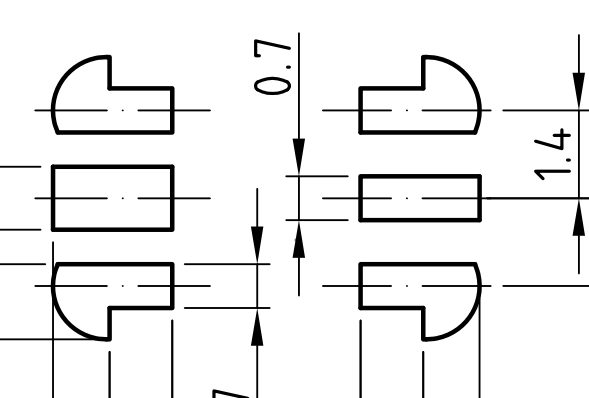
Circuit imprimé/Axe_linéaire/Capture d’écran 2023-02-14 005251.png
