Docredstein/TIPE_TMD/Circuit imprimé/Axe_linéaire/Capture d’écran 2023-02-16 172650.png

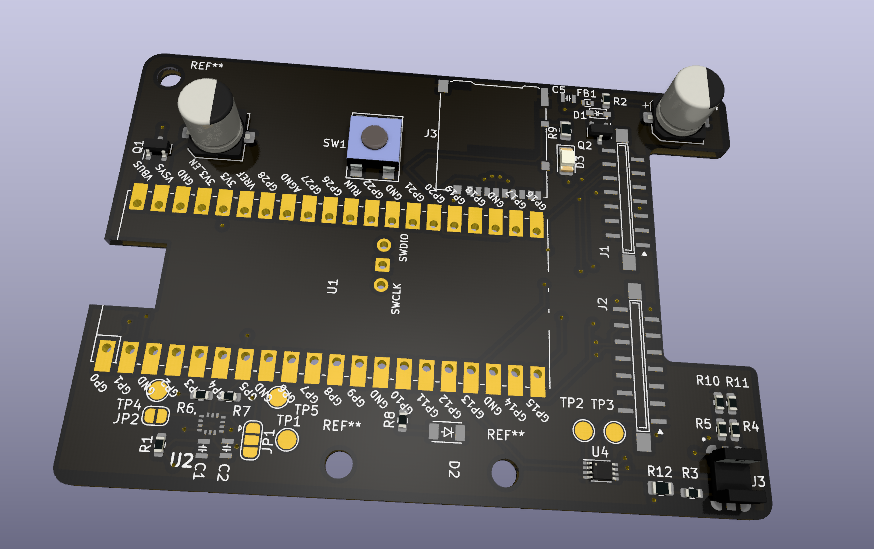
Circuit imprimé/Axe_linéaire/Capture d’écran 2023-02-16 172650.png
