Docredstein/TIPE_TMD/Circuit imprimé/github.png

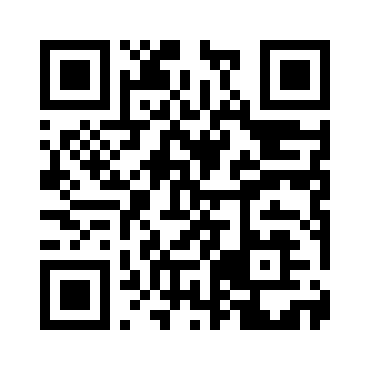
Circuit imprimé/github.png
