Docredstein/TIPE_TMD/Circuit imprimé/photo/DSC_4391.JPG

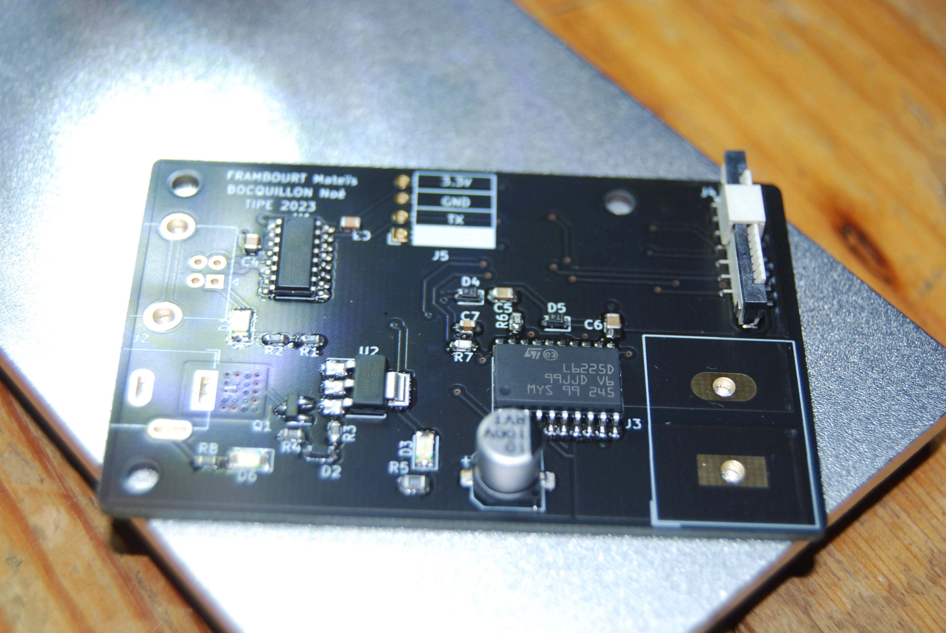
Circuit imprimé/photo/DSC_4391.JPG
