Docredstein/TIPE_TMD/Circuit imprimé/photo/DSC_4392.JPG

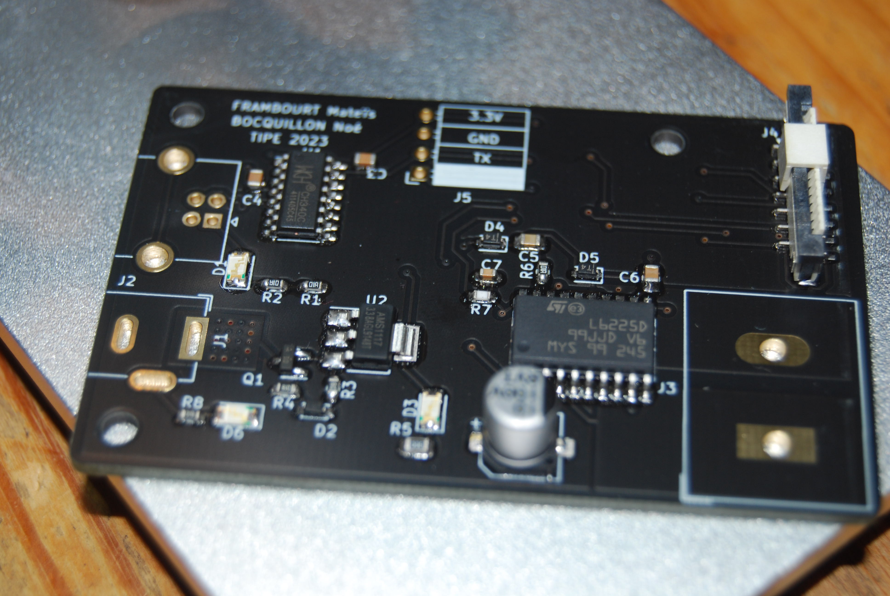
Circuit imprimé/photo/DSC_4392.JPG
