Docredstein/TIPE_TMD/Circuit imprimé/photo/DSC_4393.JPG

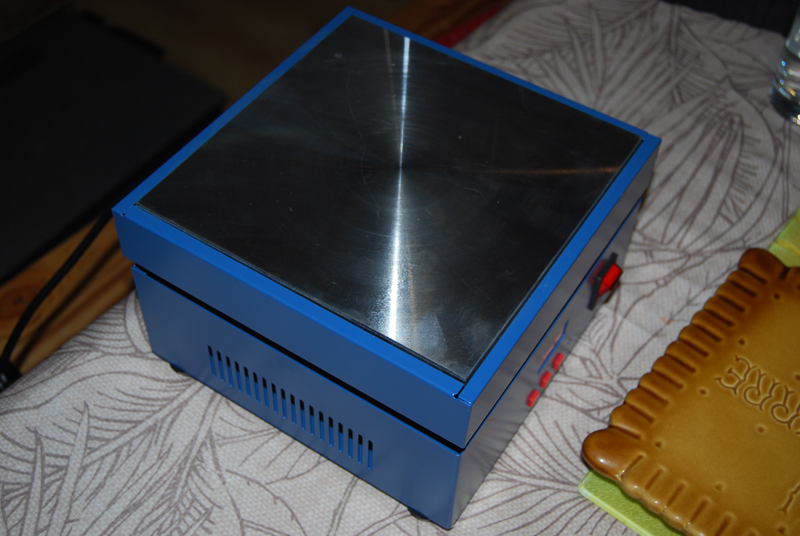
Circuit imprimé/photo/DSC_4393.JPG
