Docredstein/TIPE_TMD/Circuit imprimé/photo/DSC_4394.JPG

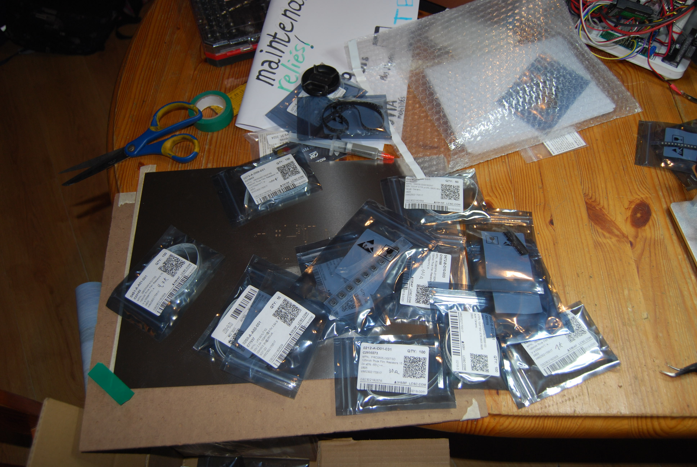
Circuit imprimé/photo/DSC_4394.JPG
