Docredstein/TIPE_TMD/Circuit imprimé/photo/DSC_4395.JPG

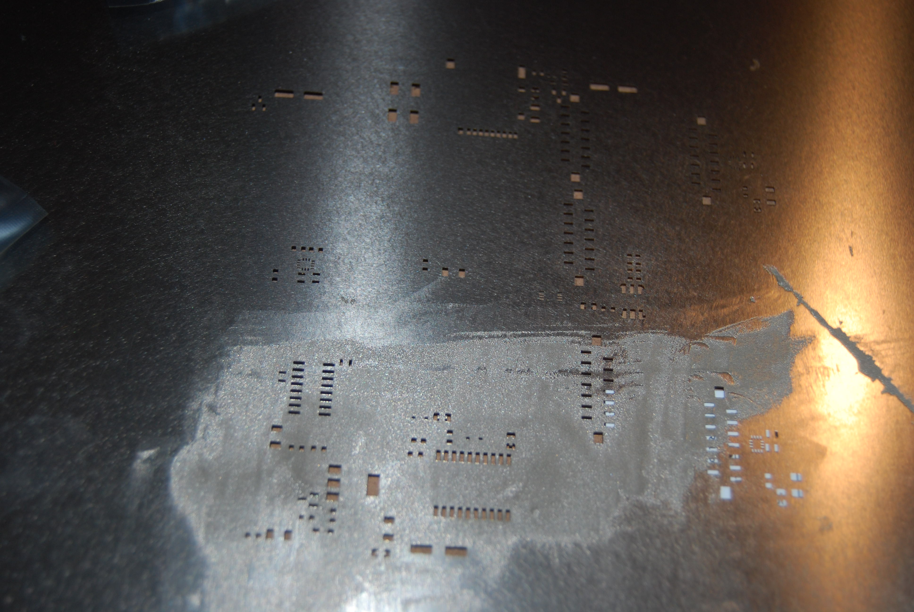
Circuit imprimé/photo/DSC_4395.JPG
