Docredstein/TIPE_TMD/Circuit imprimé/photo/DSC_4396.JPG

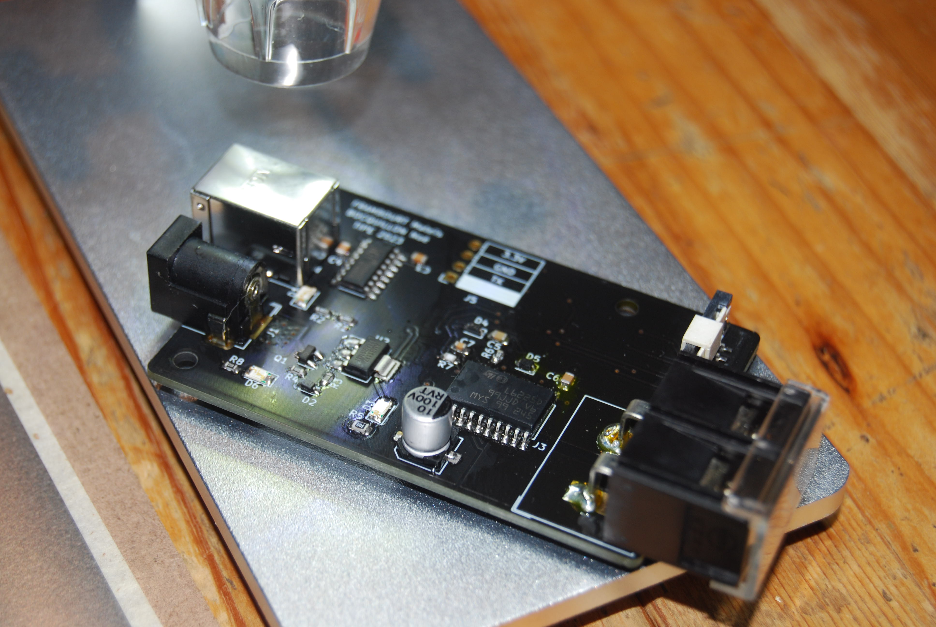
Circuit imprimé/photo/DSC_4396.JPG
