Docredstein/TIPE_TMD/Circuit imprimé/photo/DSC_4397.JPG

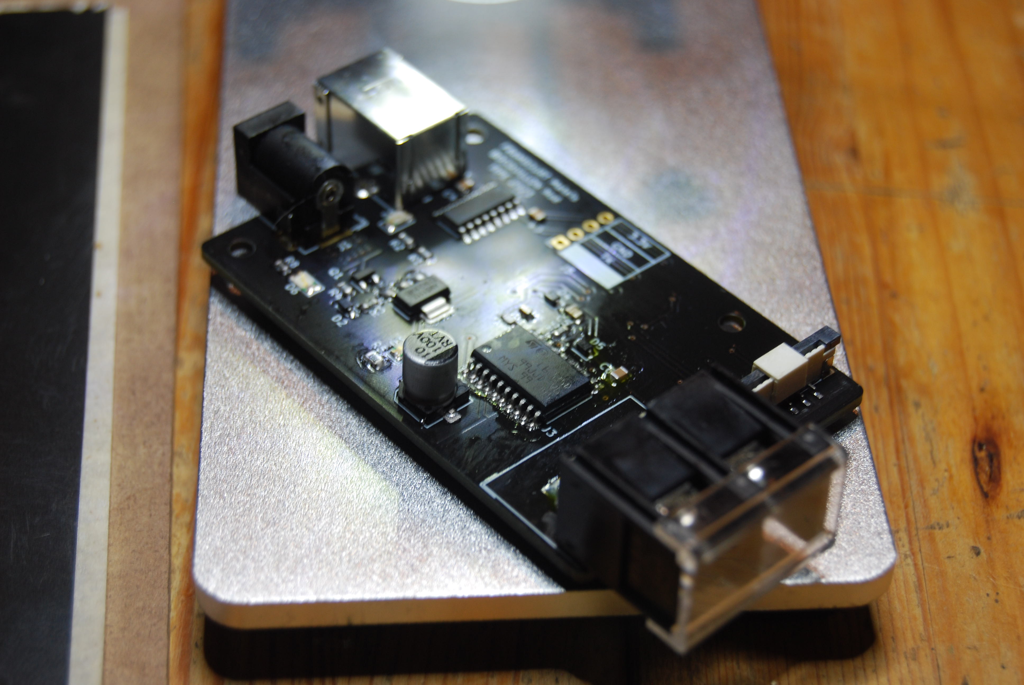
Circuit imprimé/photo/DSC_4397.JPG
