Docredstein/TIPE_TMD/Circuit imprimé/photo/DSC_4399.JPG

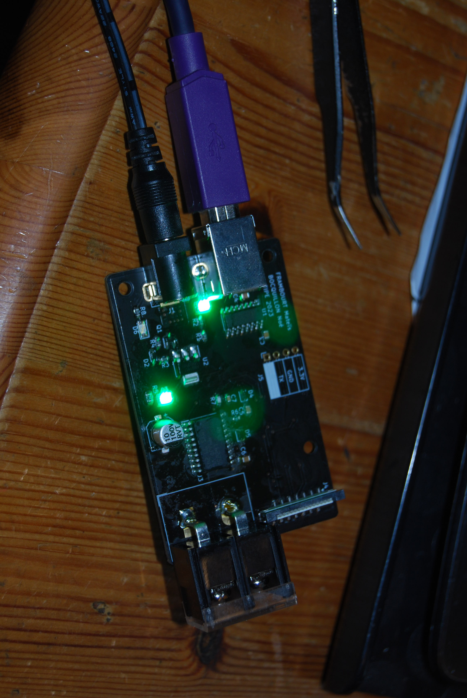
Circuit imprimé/photo/DSC_4399.JPG
