Docredstein/TIPE_TMD/Circuit imprimé/photo/DSC_4400.JPG

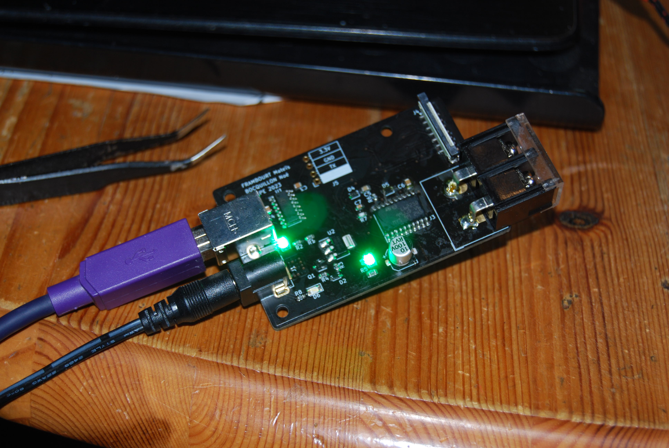
Circuit imprimé/photo/DSC_4400.JPG
