Docredstein/TIPE_TMD/Circuit imprimé/photo/DSC_4401.JPG

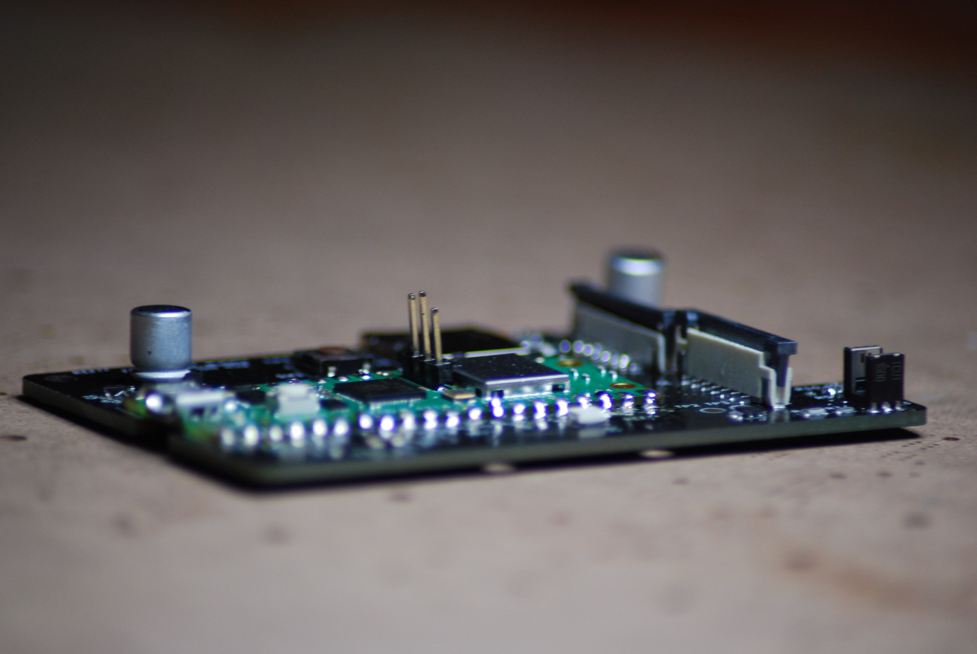
Circuit imprimé/photo/DSC_4401.JPG
