Docredstein/TIPE_TMD/Circuit imprimé/photo/DSC_4402.JPG

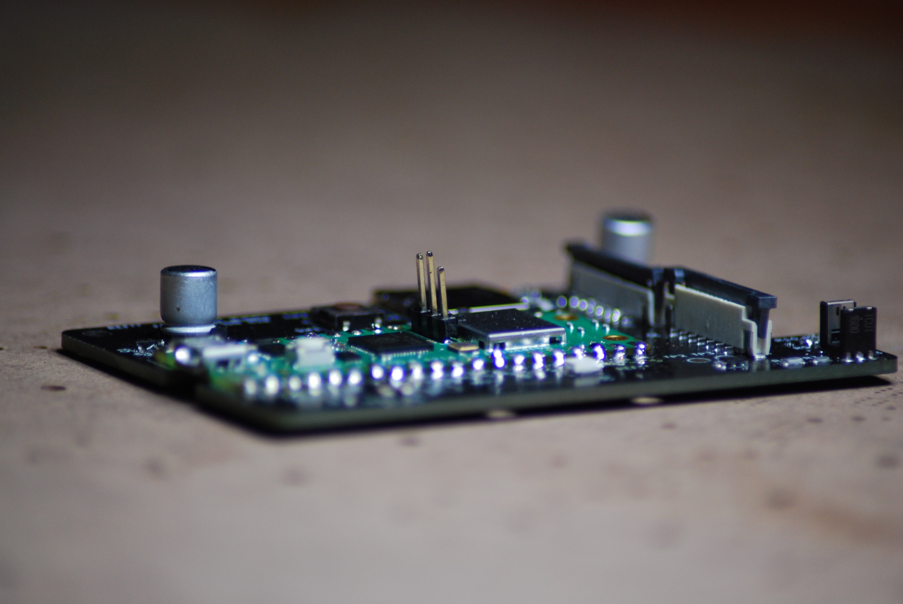
Circuit imprimé/photo/DSC_4402.JPG
