Docredstein/TIPE_TMD/Circuit imprimé/photo/DSC_4403.JPG

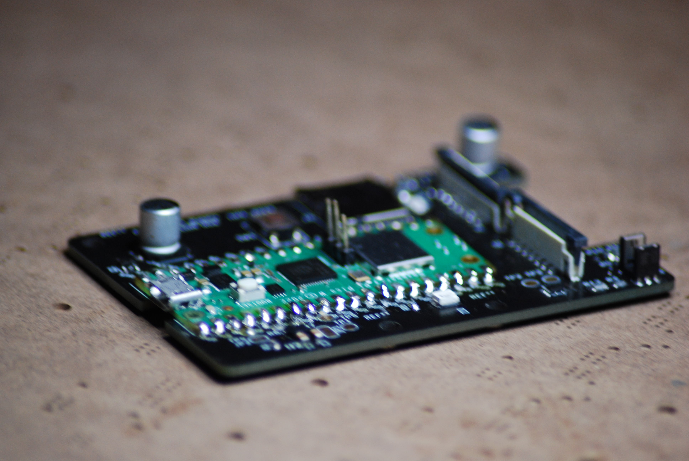
Circuit imprimé/photo/DSC_4403.JPG
