Docredstein/TIPE_TMD/Circuit imprimé/photo/DSC_4404.JPG

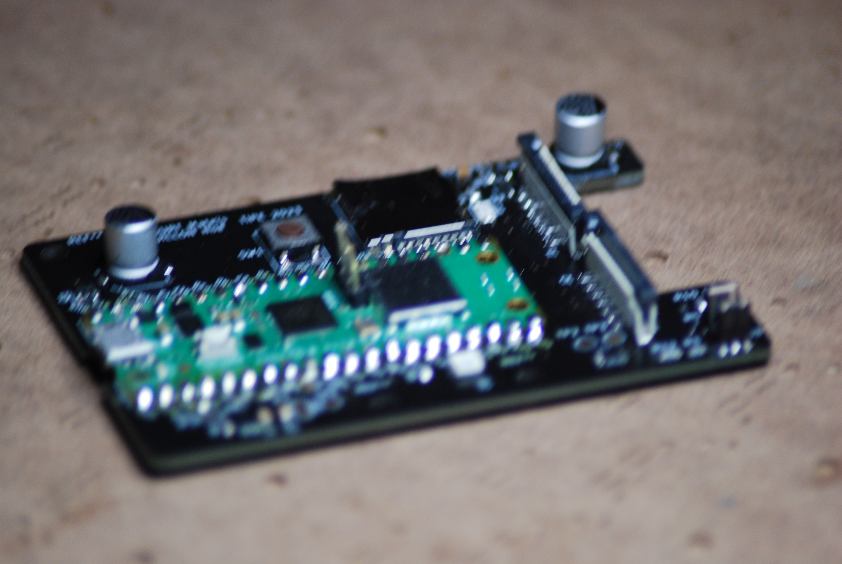
Circuit imprimé/photo/DSC_4404.JPG
