Docredstein/TIPE_TMD/Circuit imprimé/photo/DSC_4405.JPG

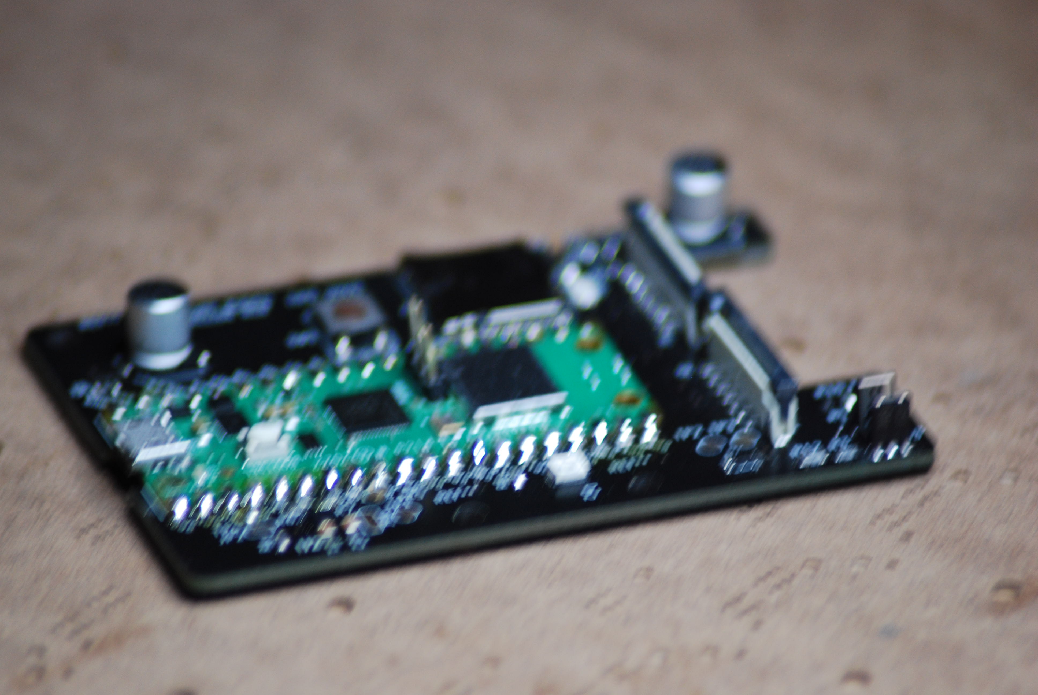
Circuit imprimé/photo/DSC_4405.JPG
