Docredstein/TIPE_TMD/Circuit imprimé/photo/DSC_4406.JPG

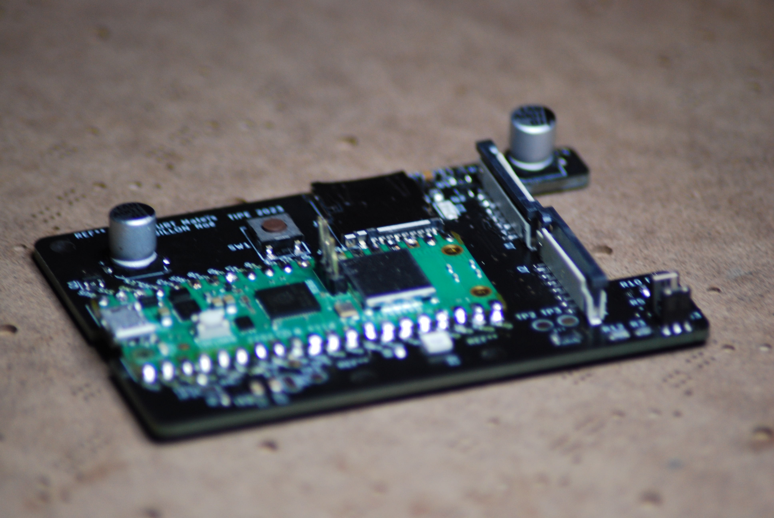
Circuit imprimé/photo/DSC_4406.JPG
