Docredstein/TIPE_TMD/Circuit imprimé/photo/DSC_4407.JPG

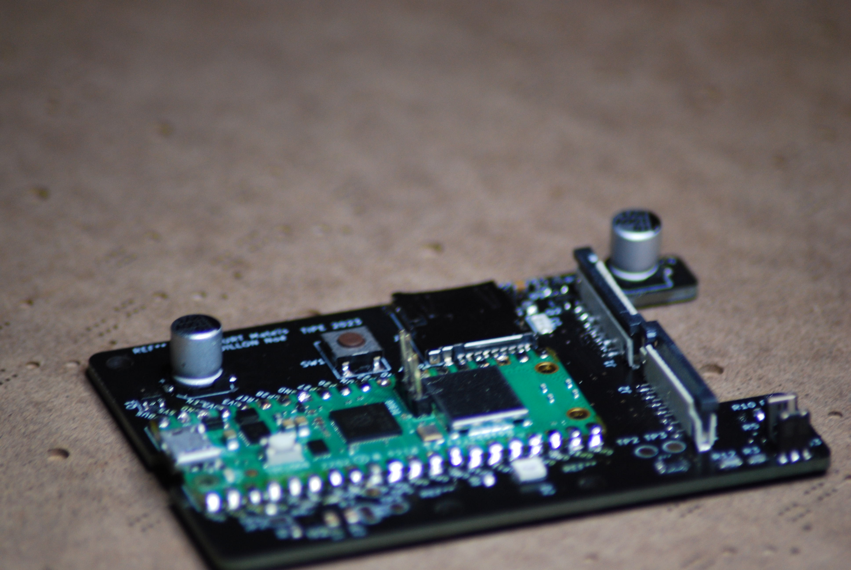
Circuit imprimé/photo/DSC_4407.JPG
