Docredstein/TIPE_TMD/Circuit imprimé/photo/DSC_4408.JPG

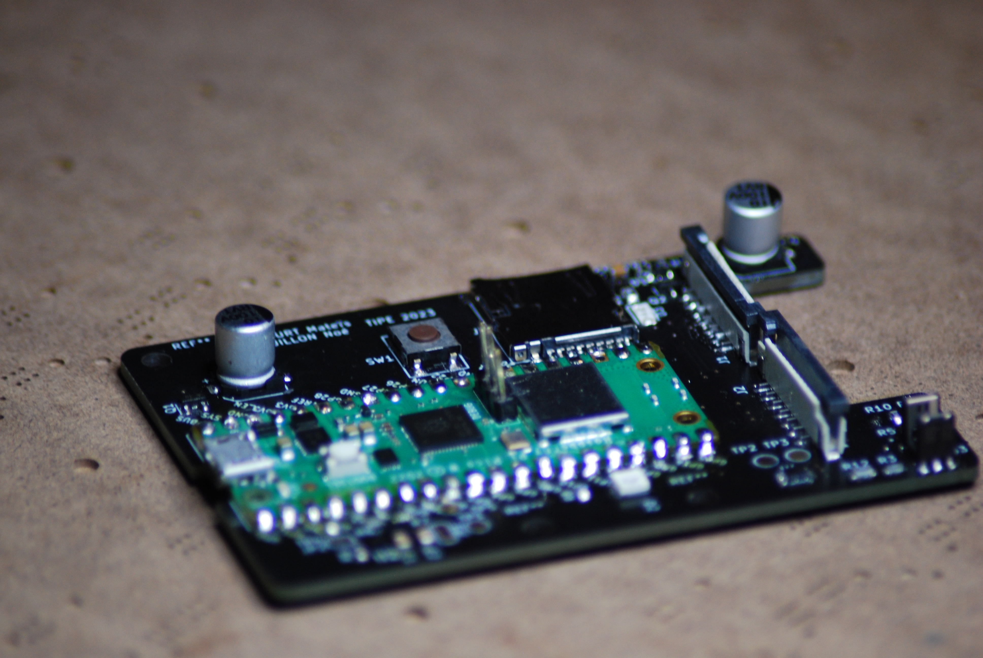
Circuit imprimé/photo/DSC_4408.JPG
