Docredstein/TIPE_TMD/Circuit imprimé/photo/DSC_4409.JPG

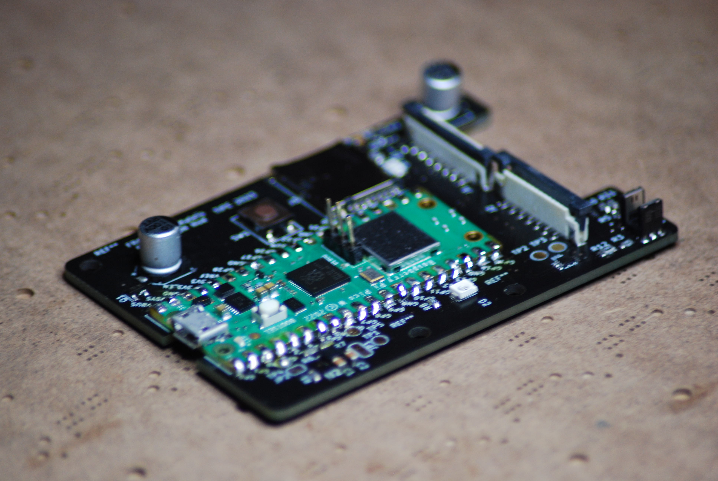
Circuit imprimé/photo/DSC_4409.JPG
