Docredstein/TIPE_TMD/Circuit imprimé/photo/DSC_4411.JPG

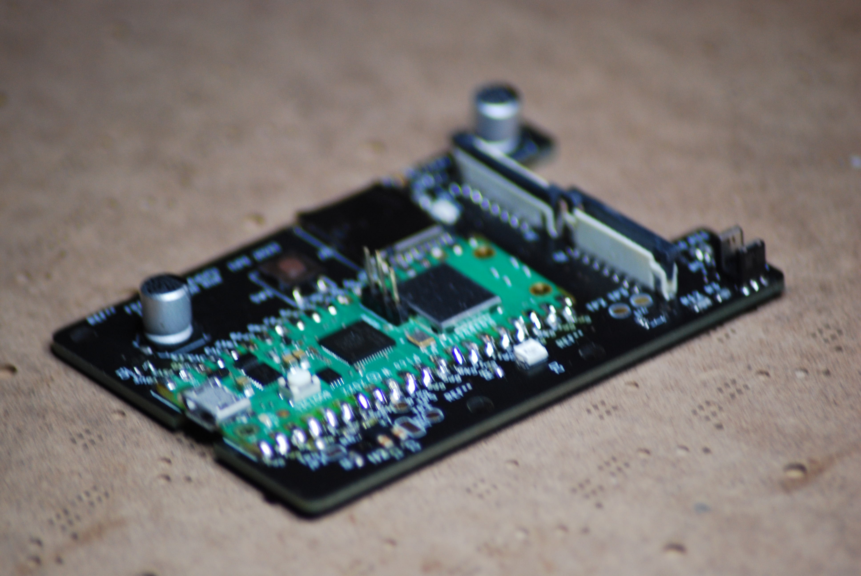
Circuit imprimé/photo/DSC_4411.JPG
