Docredstein/TIPE_TMD/Circuit imprimé/photo/DSC_4412.JPG

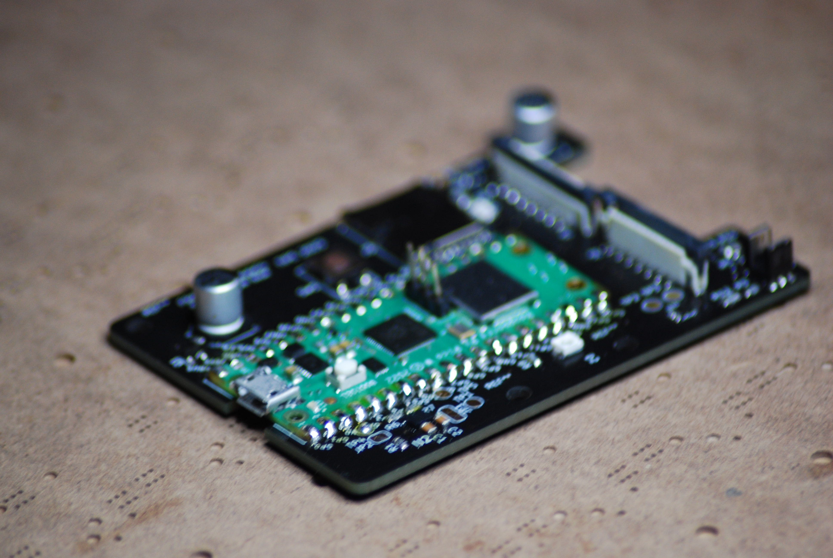
Circuit imprimé/photo/DSC_4412.JPG
