Docredstein/TIPE_TMD/Circuit imprimé/photo/DSC_4413.JPG

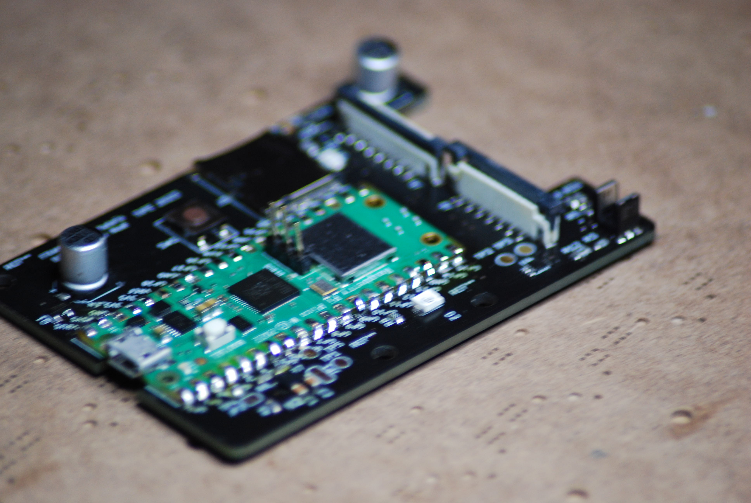
Circuit imprimé/photo/DSC_4413.JPG
