Docredstein/TIPE_TMD/Circuit imprimé/photo/DSC_4414.JPG

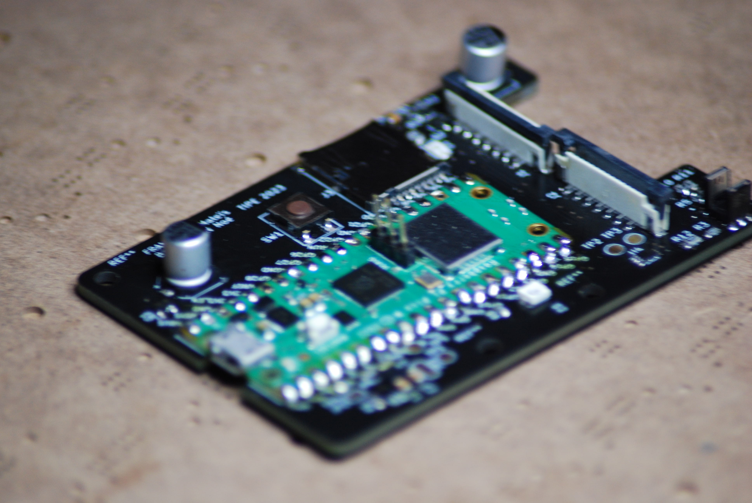
Circuit imprimé/photo/DSC_4414.JPG
