Docredstein/TIPE_TMD/Circuit imprimé/photo/DSC_4415.JPG

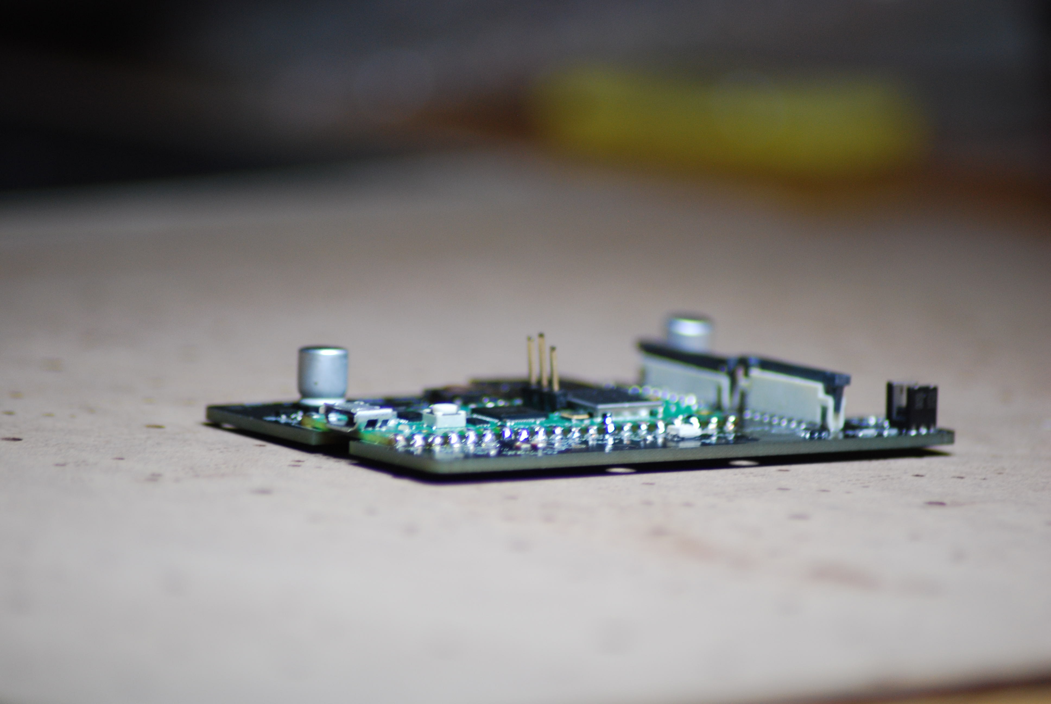
Circuit imprimé/photo/DSC_4415.JPG
