Docredstein/TIPE_TMD/Circuit imprimé/photo/DSC_4416.JPG

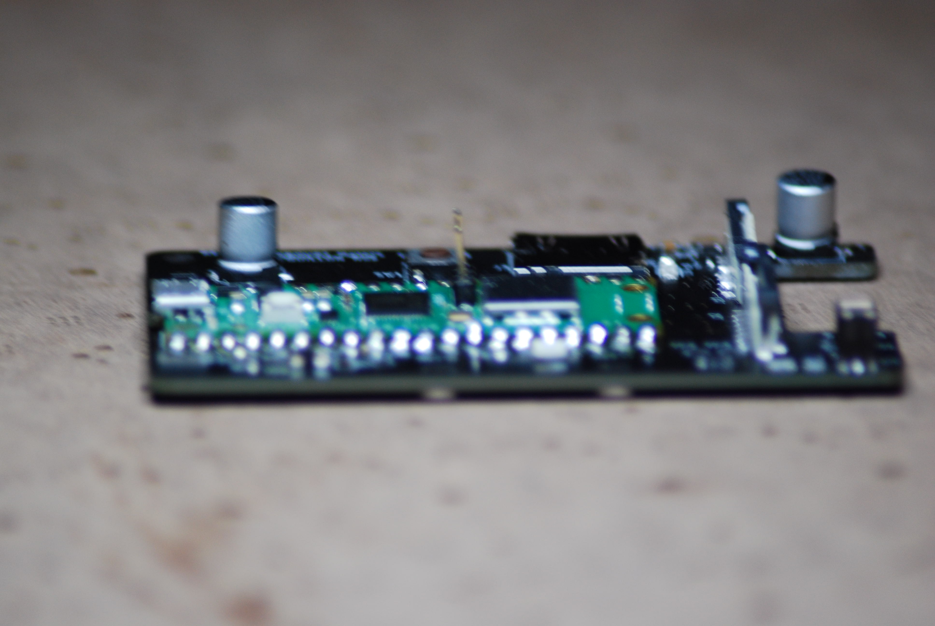
Circuit imprimé/photo/DSC_4416.JPG
