Docredstein/TIPE_TMD/Circuit imprimé/photo/DSC_4417.JPG

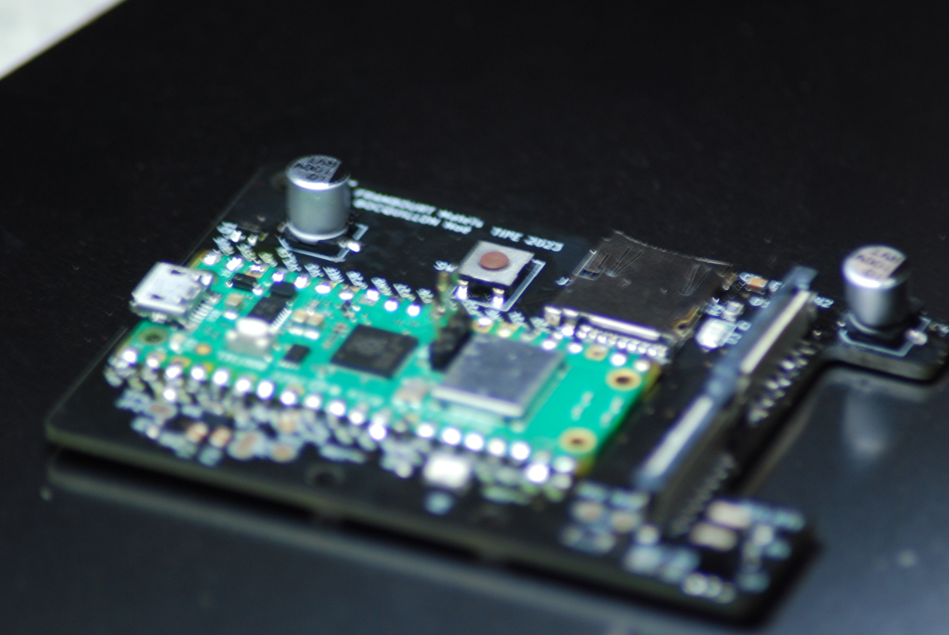
Circuit imprimé/photo/DSC_4417.JPG
