Docredstein/TIPE_TMD/Circuit imprimé/photo/DSC_4418.JPG

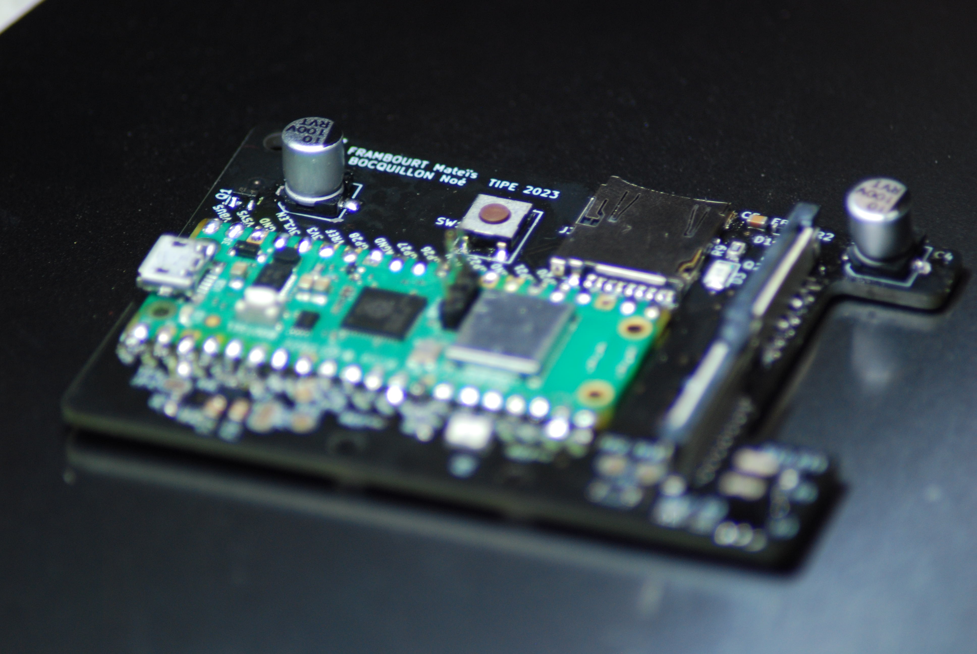
Circuit imprimé/photo/DSC_4418.JPG
