Docredstein/TIPE_TMD/Circuit imprimé/photo/DSC_4419.JPG

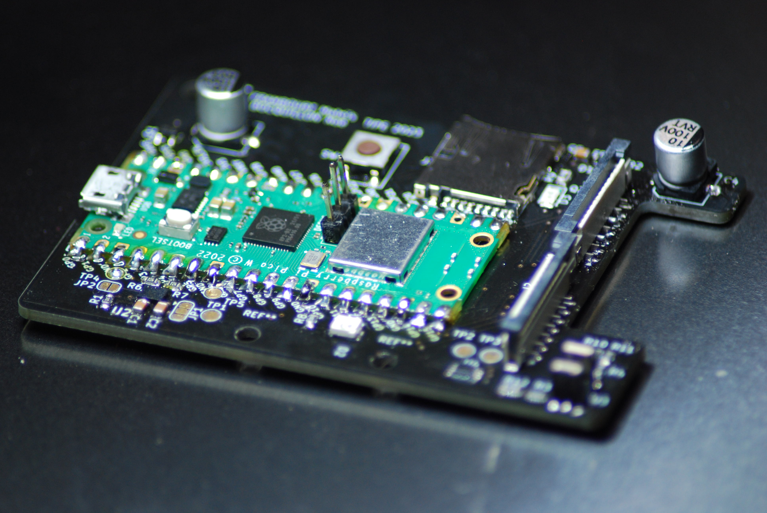
Circuit imprimé/photo/DSC_4419.JPG
