Docredstein/TIPE_TMD/Circuit imprimé/photo/DSC_4420.JPG

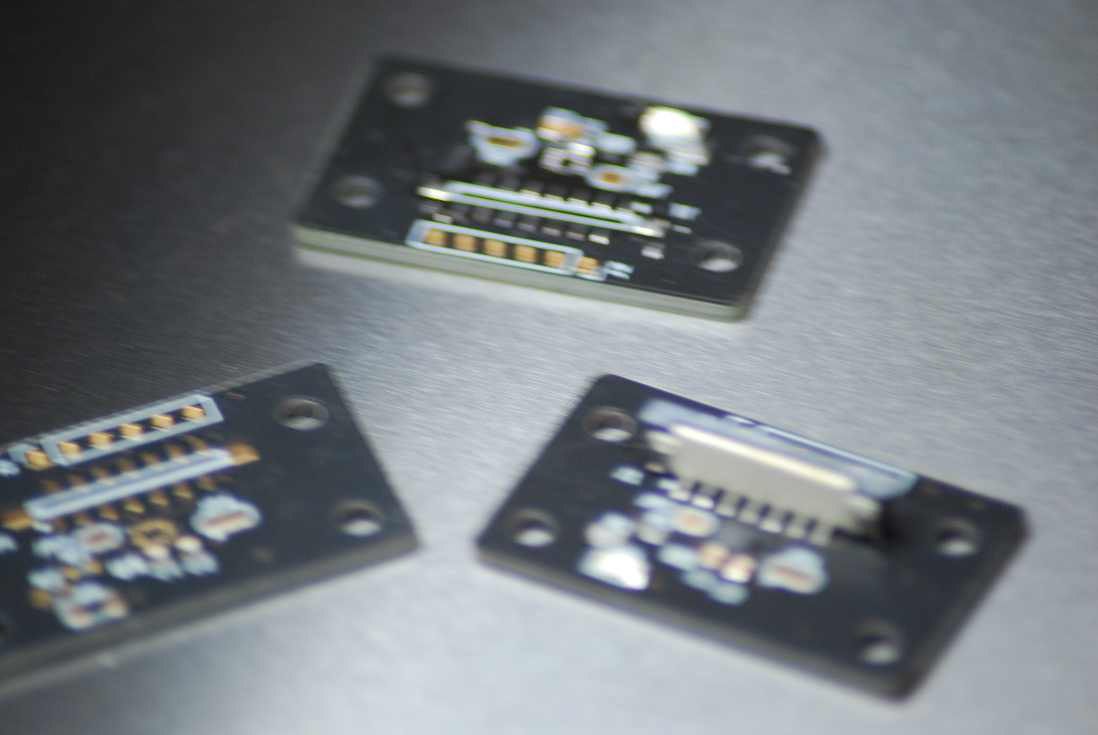
Circuit imprimé/photo/DSC_4420.JPG
