Docredstein/TIPE_TMD/Circuit imprimé/photo/DSC_4421.JPG

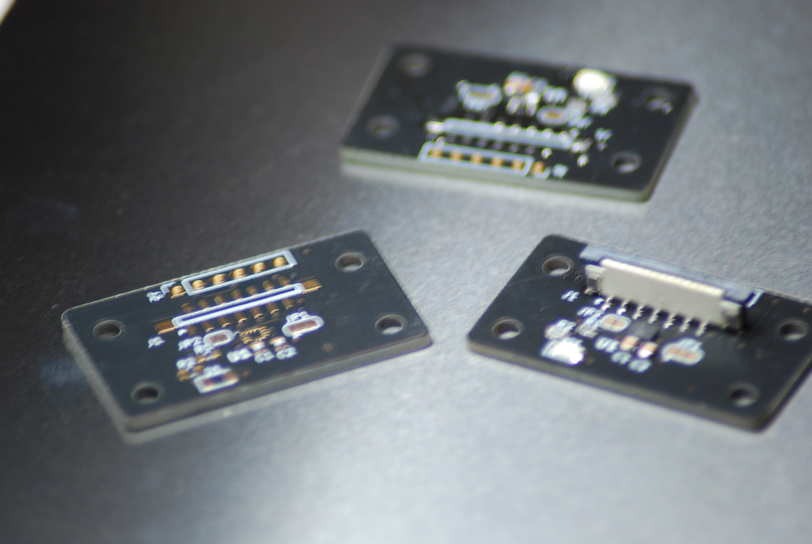
Circuit imprimé/photo/DSC_4421.JPG
