Docredstein/TIPE_TMD/Circuit imprimé/photo/DSC_4422.JPG

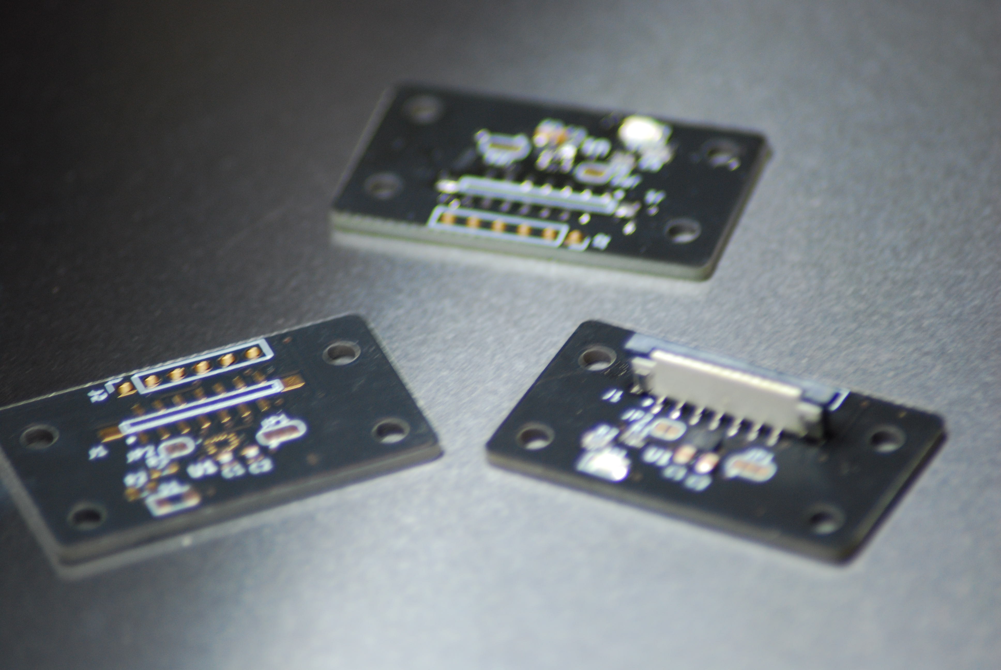
Circuit imprimé/photo/DSC_4422.JPG
