Docredstein/TIPE_TMD/Circuit imprimé/photo/DSC_4423.JPG

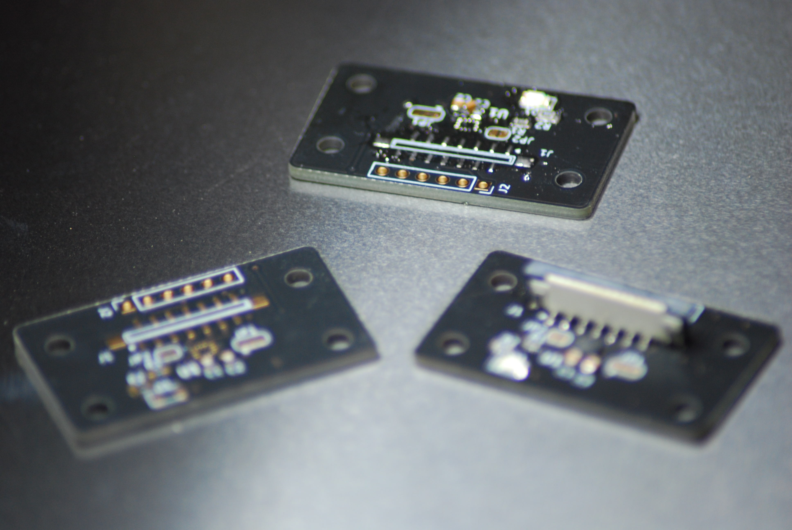
Circuit imprimé/photo/DSC_4423.JPG
