Docredstein/TIPE_TMD/Circuit imprimé/photo/DSC_4426.JPG

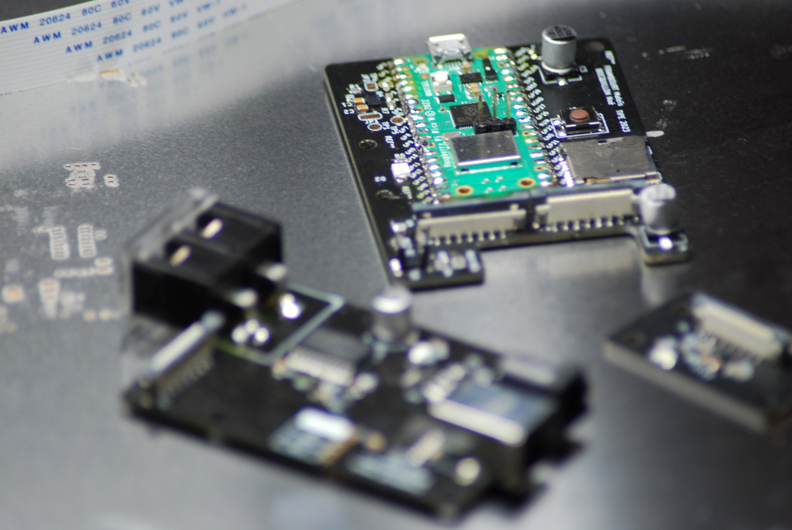
Circuit imprimé/photo/DSC_4426.JPG
