Docredstein/TIPE_TMD/Circuit imprimé/photo/DSC_4427.JPG

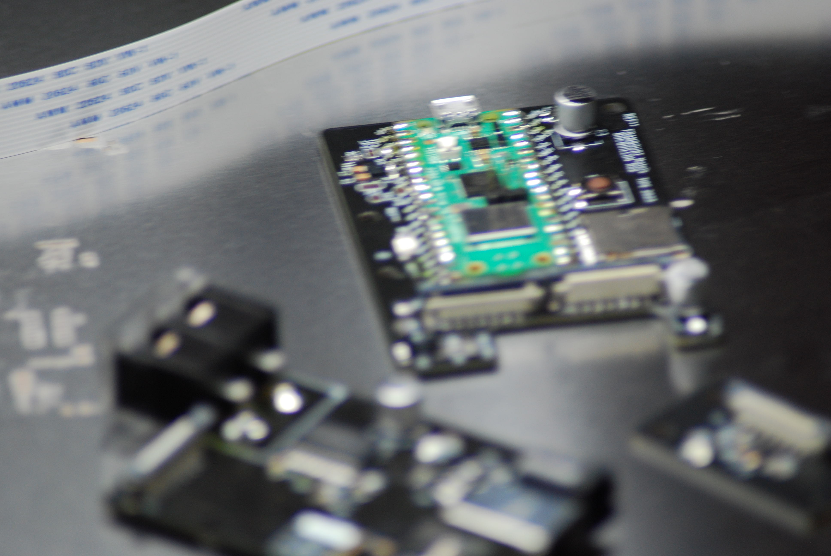
Circuit imprimé/photo/DSC_4427.JPG
