Docredstein/TIPE_TMD/Circuit imprimé/photo/DSC_4428.JPG

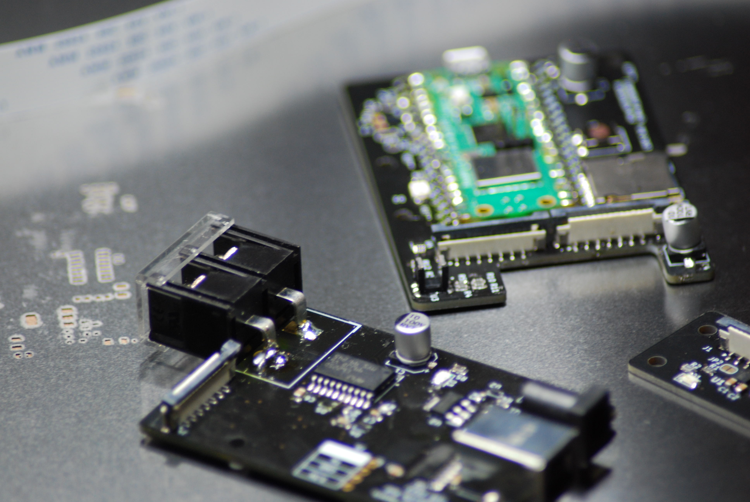
Circuit imprimé/photo/DSC_4428.JPG
