Docredstein/TIPE_TMD/Circuit imprimé/photo/DSC_4429.JPG

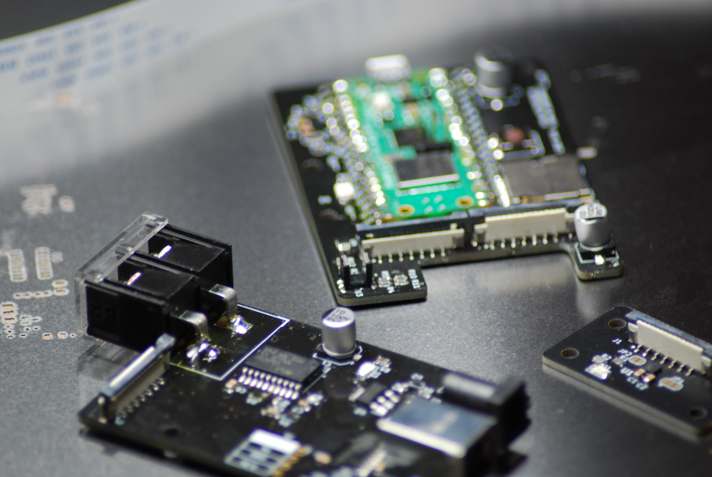
Circuit imprimé/photo/DSC_4429.JPG
