Docredstein/TIPE_TMD/Circuit imprimé/photo/DSC_4430.JPG

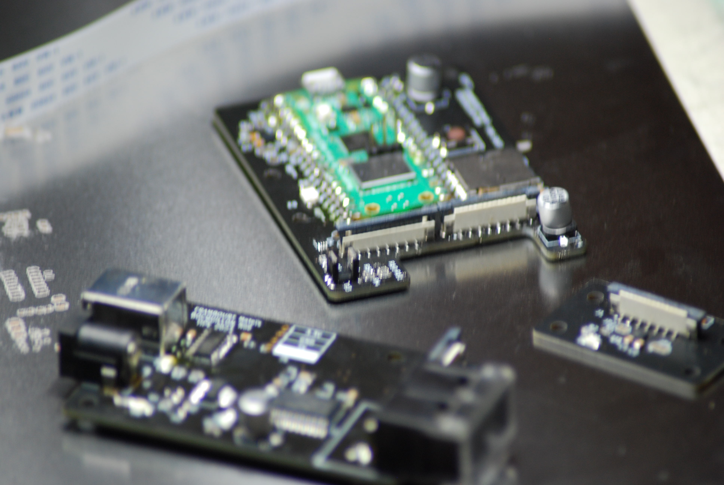
Circuit imprimé/photo/DSC_4430.JPG
