Docredstein/TIPE_TMD/Circuit imprimé/photo/DSC_4431.JPG

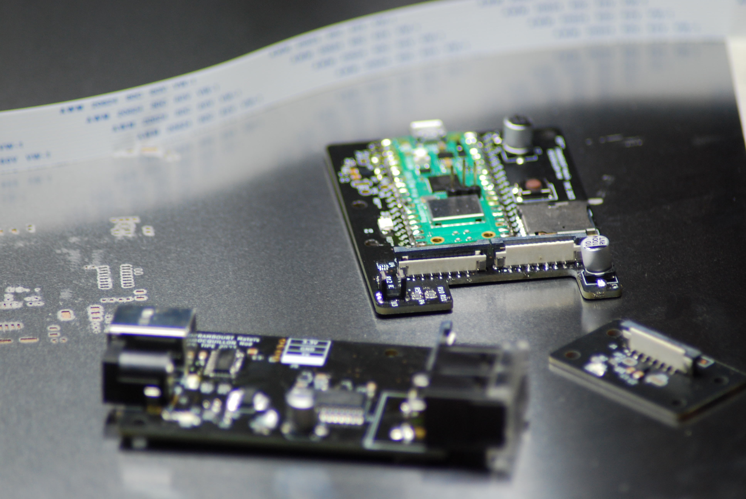
Circuit imprimé/photo/DSC_4431.JPG
