Docredstein/TIPE_TMD/Circuit imprimé/photo/DSC_4432.JPG

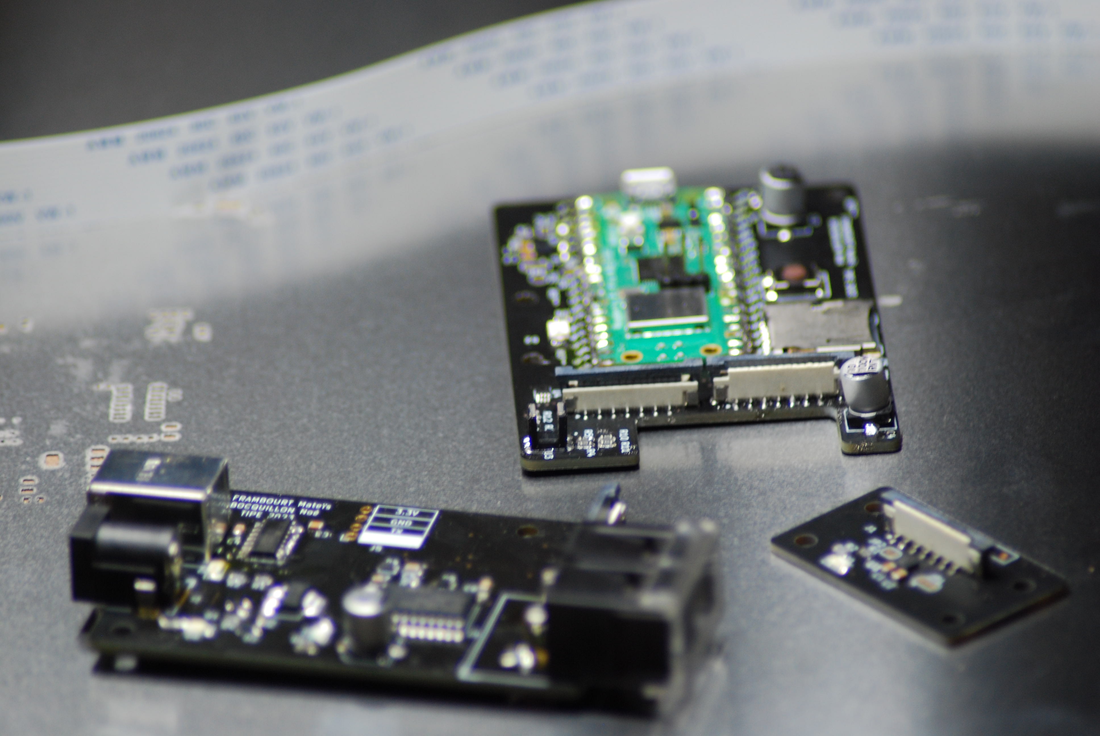
Circuit imprimé/photo/DSC_4432.JPG
