Docredstein/TIPE_TMD/Circuit imprimé/photo/DSC_4434.JPG

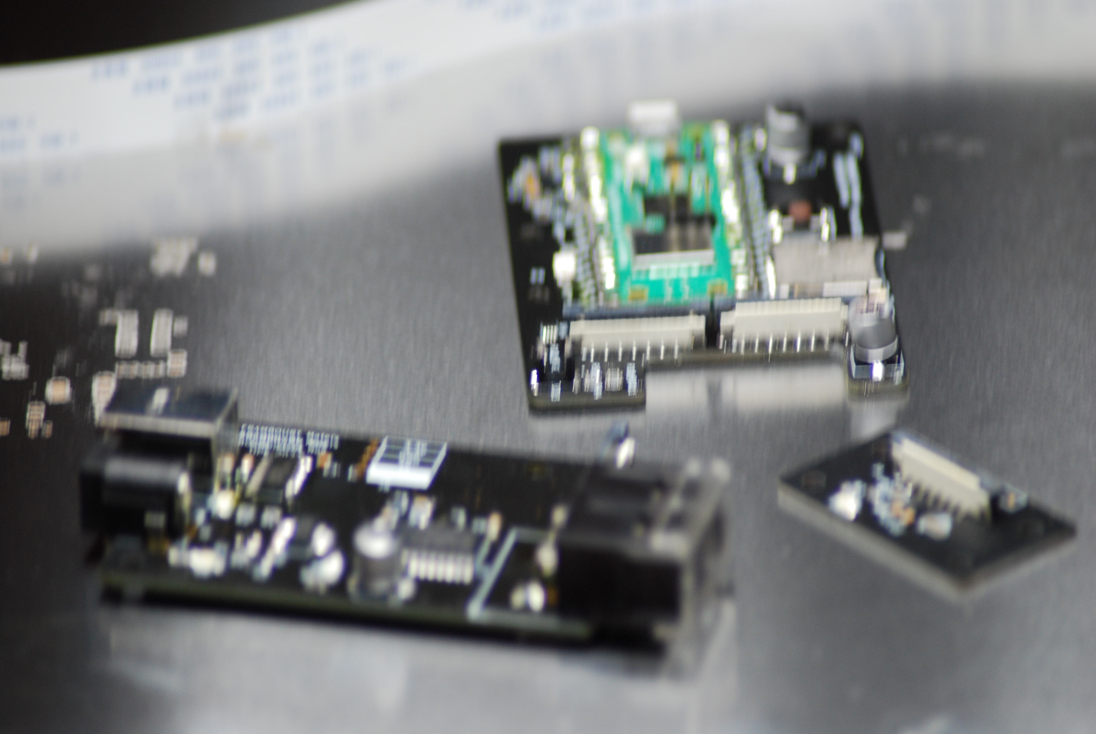
Circuit imprimé/photo/DSC_4434.JPG
