Docredstein/TIPE_TMD/Circuit imprimé/photo/DSC_4435.JPG

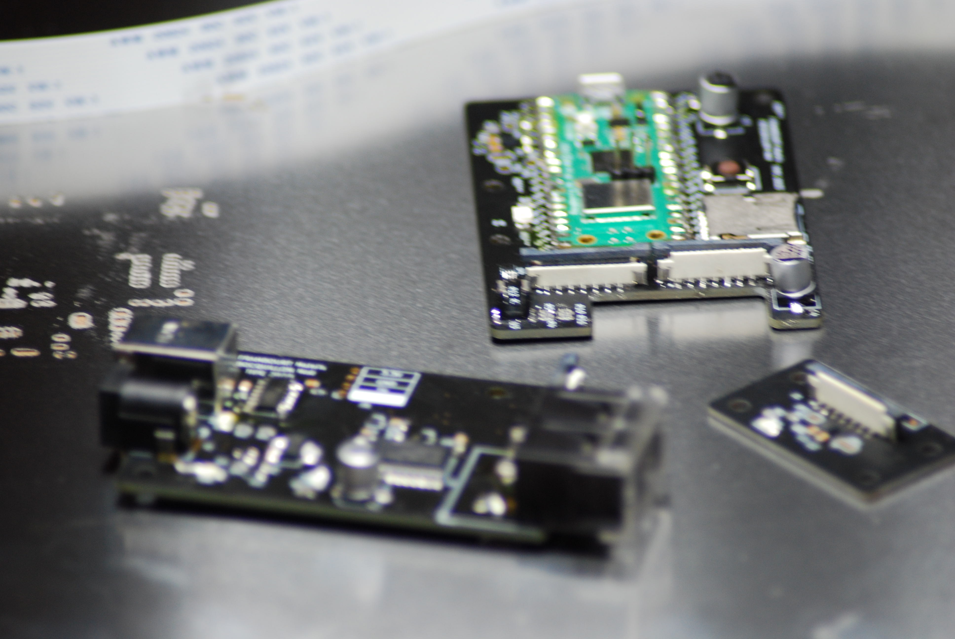
Circuit imprimé/photo/DSC_4435.JPG
