Docredstein/TIPE_TMD/Circuit imprimé/photo/DSC_4436.JPG

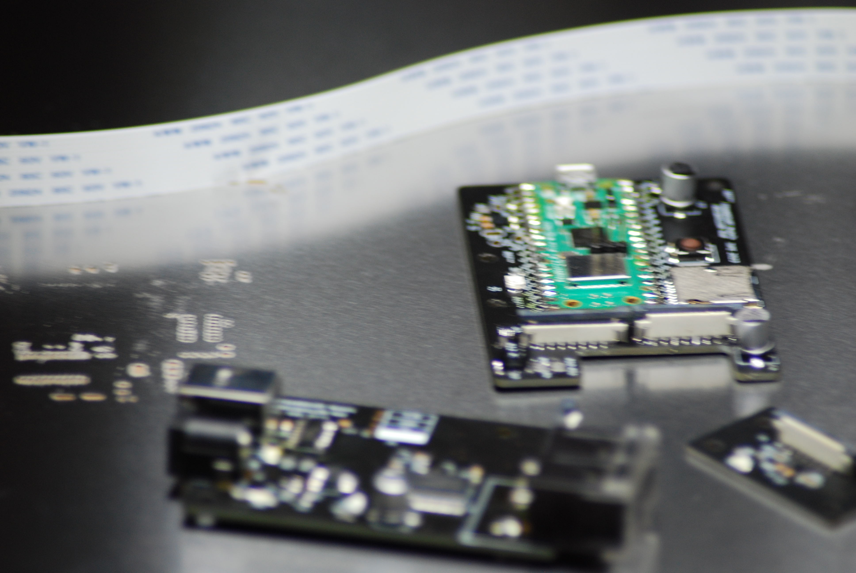
Circuit imprimé/photo/DSC_4436.JPG
