Docredstein/TIPE_TMD/Circuit imprimé/photo/DSC_4437.JPG

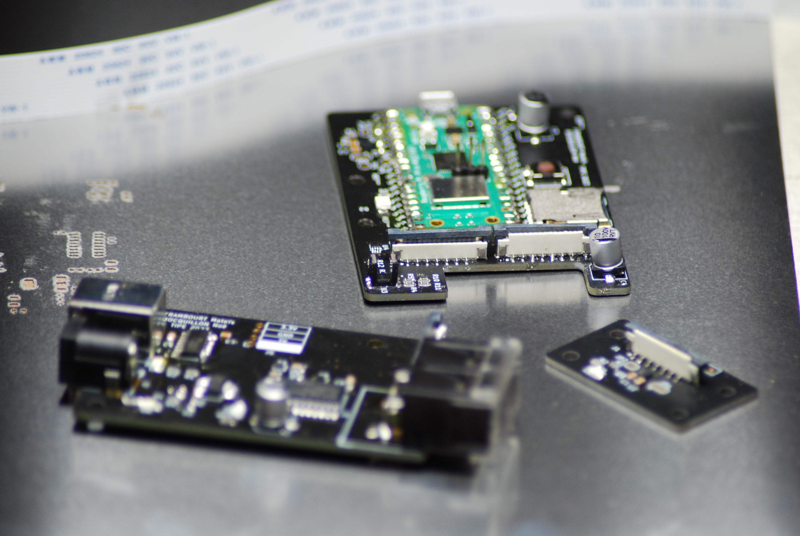
Circuit imprimé/photo/DSC_4437.JPG
