Docredstein/TIPE_TMD/Circuit imprimé/photo/DSC_4438.JPG

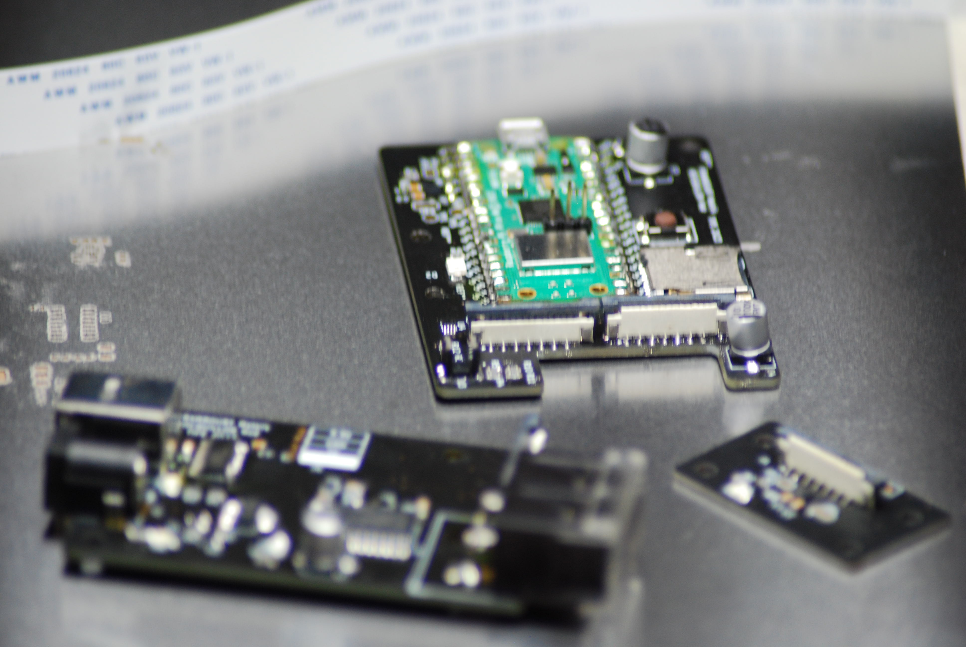
Circuit imprimé/photo/DSC_4438.JPG
