Docredstein/TIPE_TMD/Circuit imprimé/photo/DSC_4439.JPG

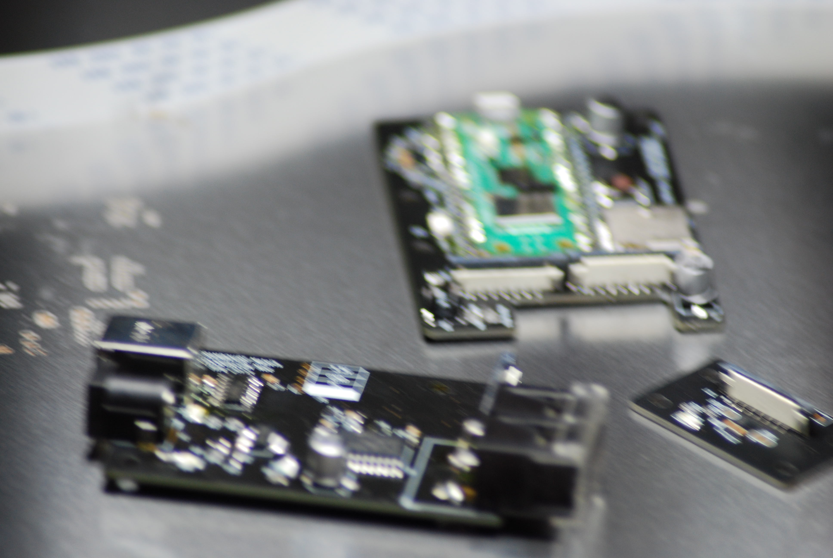
Circuit imprimé/photo/DSC_4439.JPG
