Docredstein/TIPE_TMD/Circuit imprimé/photo/DSC_4440.JPG

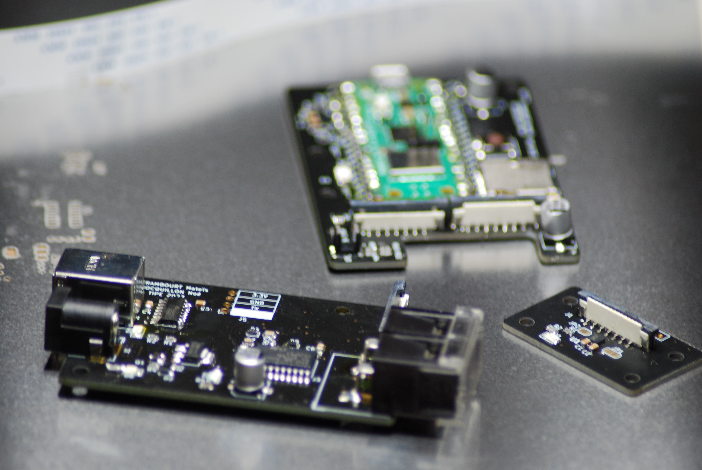
Circuit imprimé/photo/DSC_4440.JPG
