Docredstein/TIPE_TMD/Circuit imprimé/photo/DSC_4442.JPG

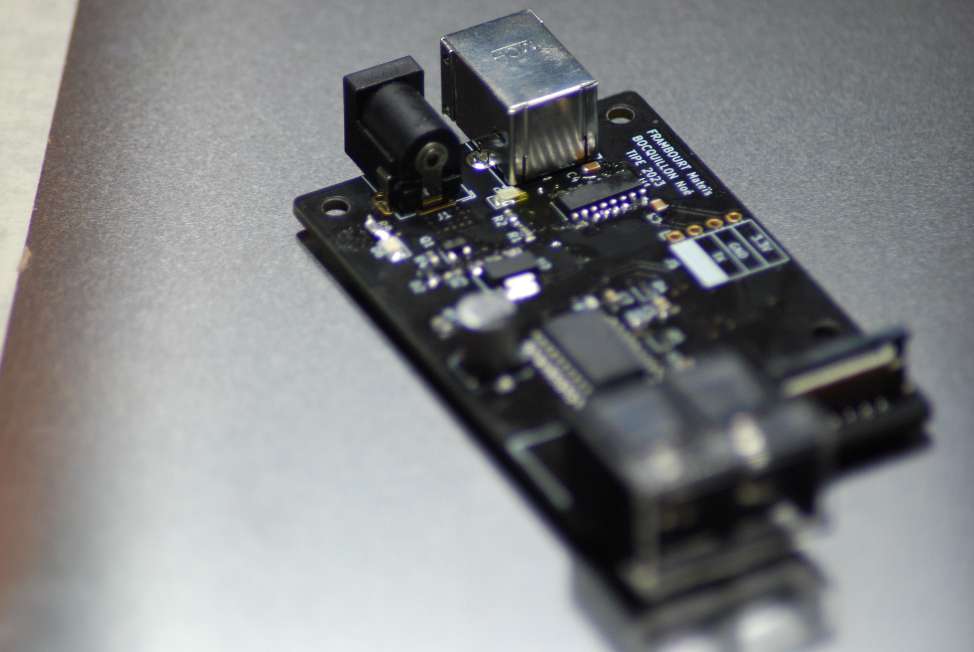
Circuit imprimé/photo/DSC_4442.JPG
