Docredstein/TIPE_TMD/Circuit imprimé/photo/DSC_4443.JPG

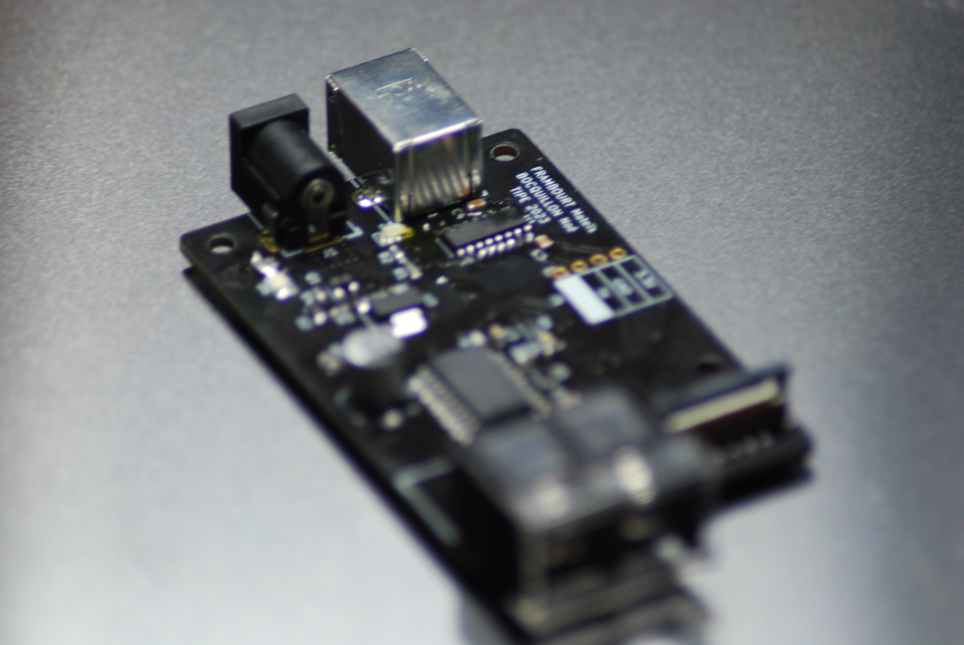
Circuit imprimé/photo/DSC_4443.JPG
