Docredstein/TIPE_TMD/Circuit imprimé/photo/DSC_4444.JPG

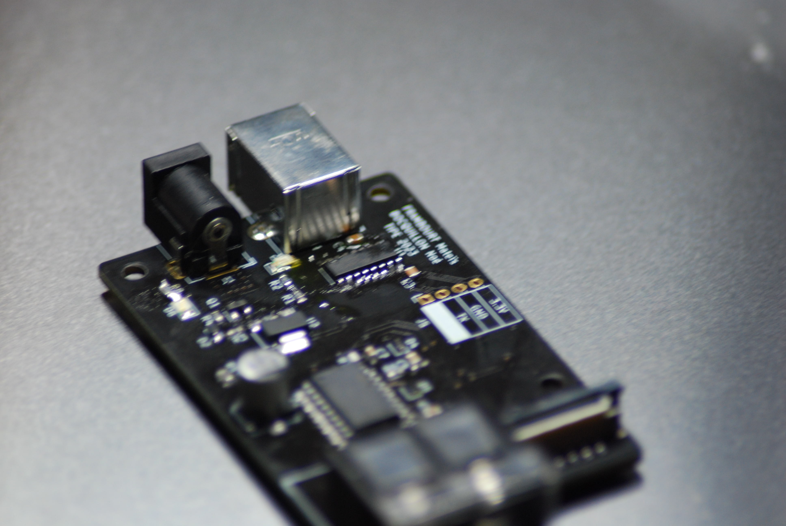
Circuit imprimé/photo/DSC_4444.JPG
