Docredstein/TIPE_TMD/Circuit imprimé/photo/DSC_4445.JPG

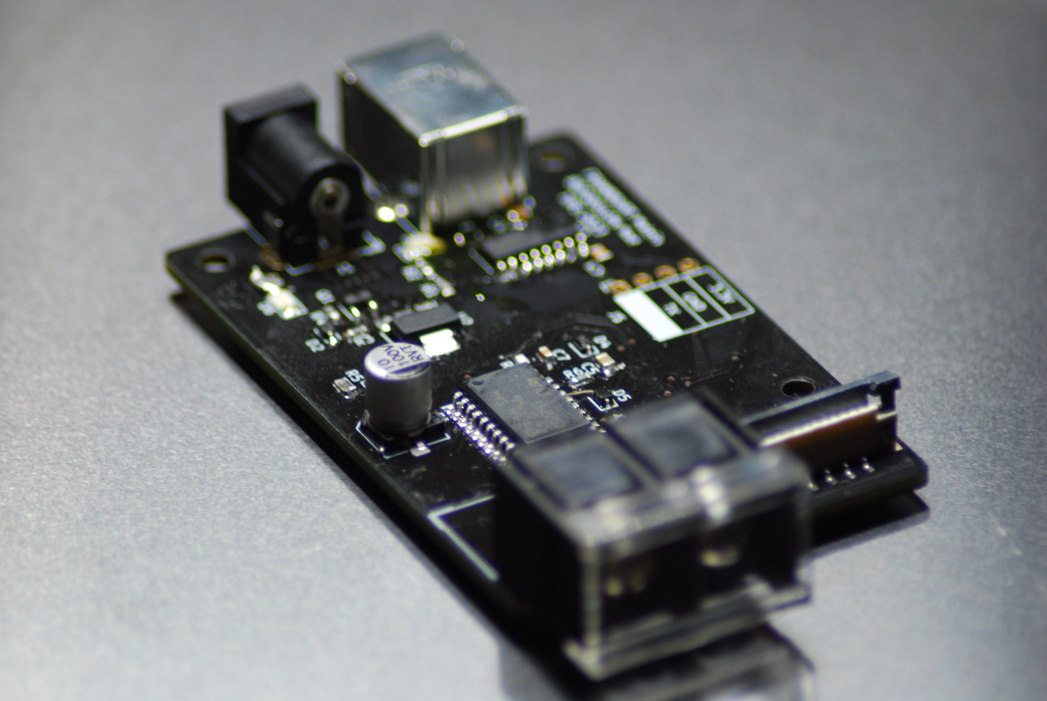
Circuit imprimé/photo/DSC_4445.JPG
