Docredstein/TIPE_TMD/Circuit imprimé/photo/DSC_4446.JPG

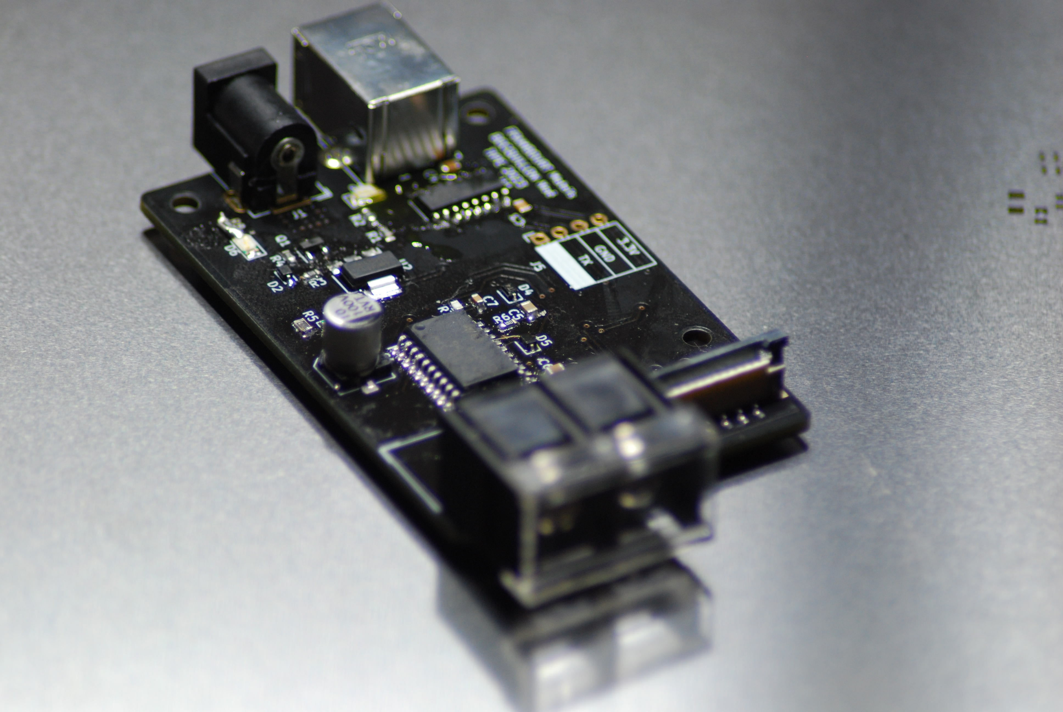
Circuit imprimé/photo/DSC_4446.JPG
