Docredstein/TIPE_TMD/Circuit imprimé/photo/DSC_4447.JPG

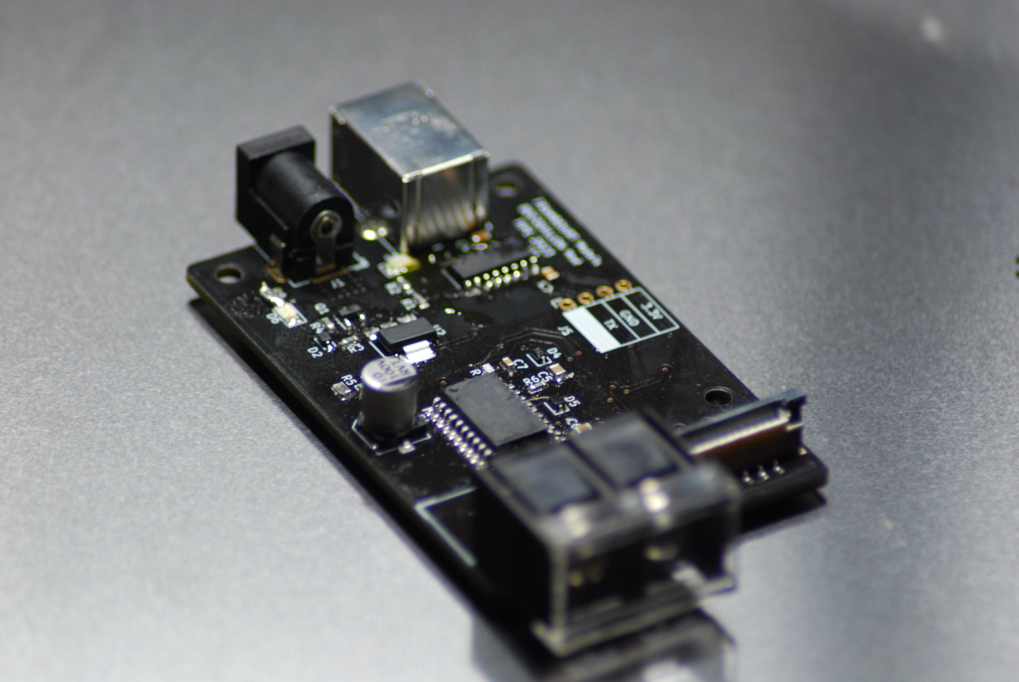
Circuit imprimé/photo/DSC_4447.JPG
