Docredstein/TIPE_TMD/Circuit imprimé/photo/DSC_4448.JPG

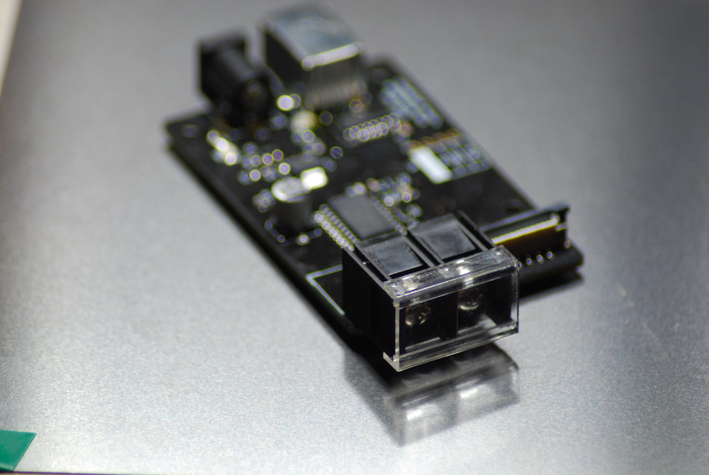
Circuit imprimé/photo/DSC_4448.JPG
