Docredstein/TIPE_TMD/Circuit imprimé/photo/DSC_4450.JPG

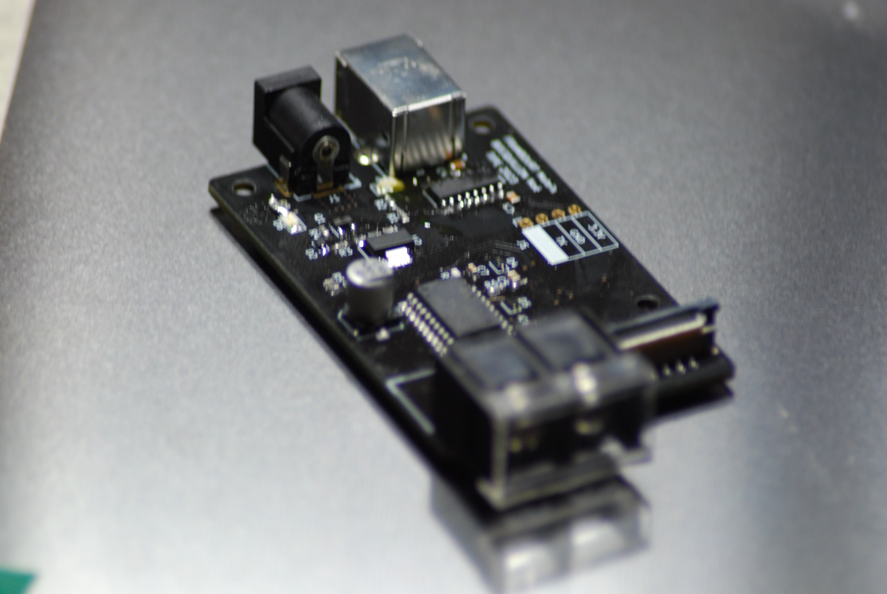
Circuit imprimé/photo/DSC_4450.JPG
