Docredstein/TIPE_TMD/expérience/immeuble/modèle flexible.png

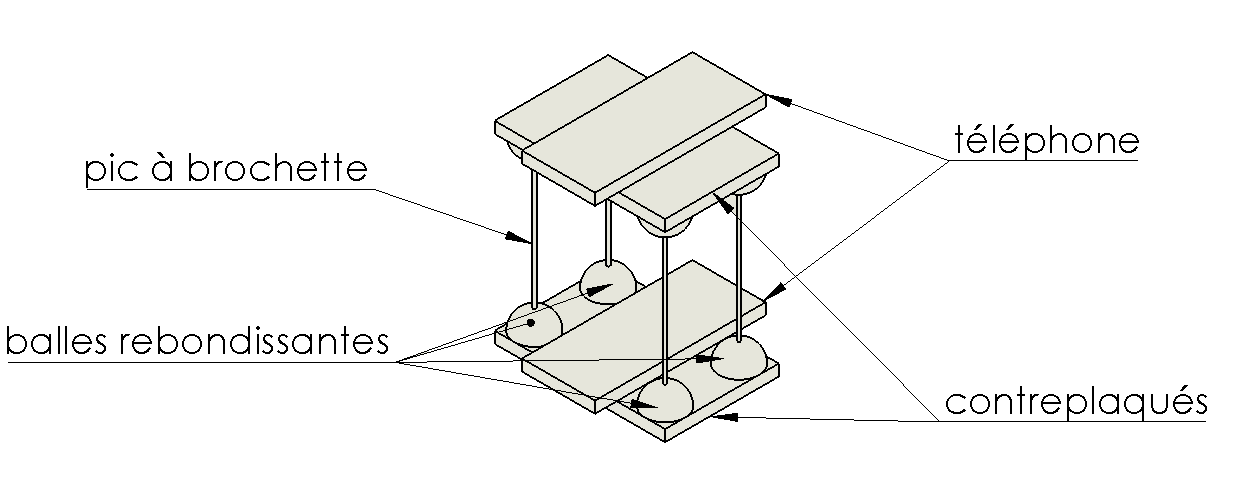
expérience/immeuble/modèle flexible.png
