Docredstein/TIPE_TMD/expérience/immeuble/modèle rebondissante.PNG

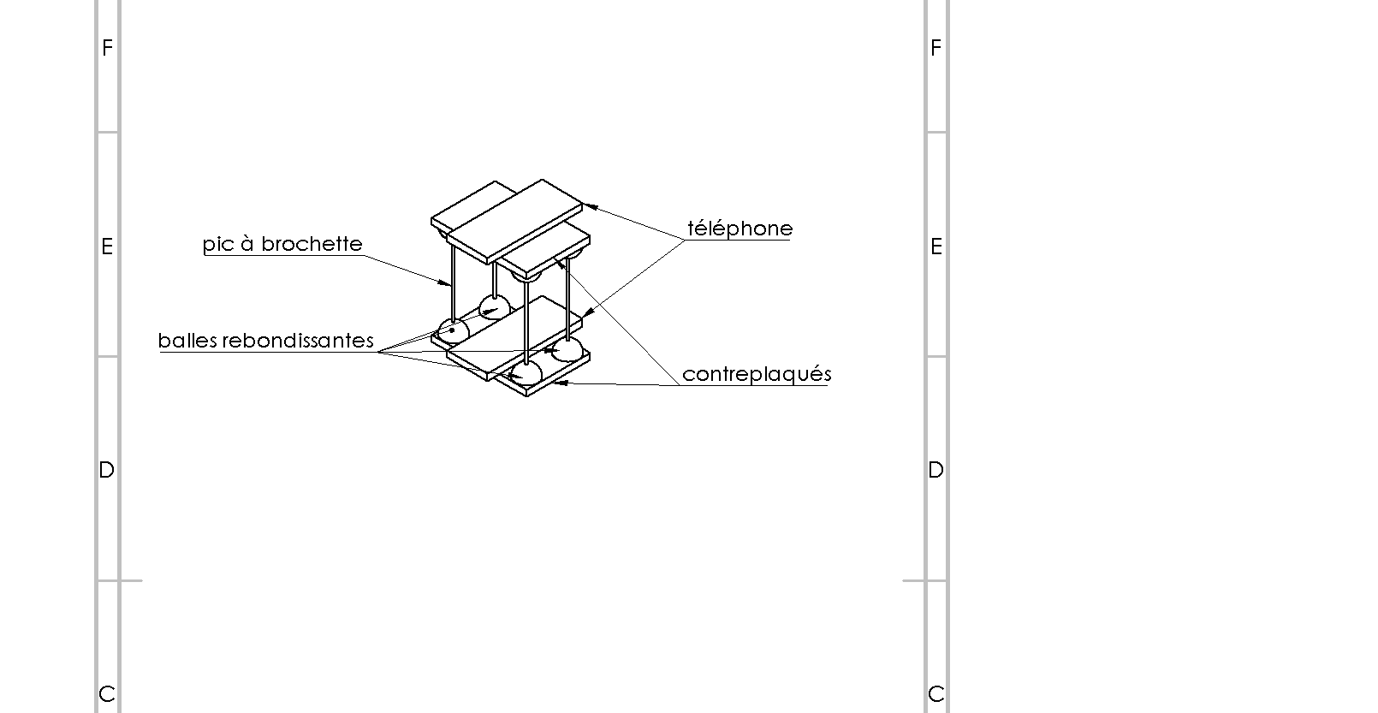
expérience/immeuble/modèle rebondissante.PNG
