Docredstein/TIPE_TMD/expérience/immeuble/modèle rigide.png

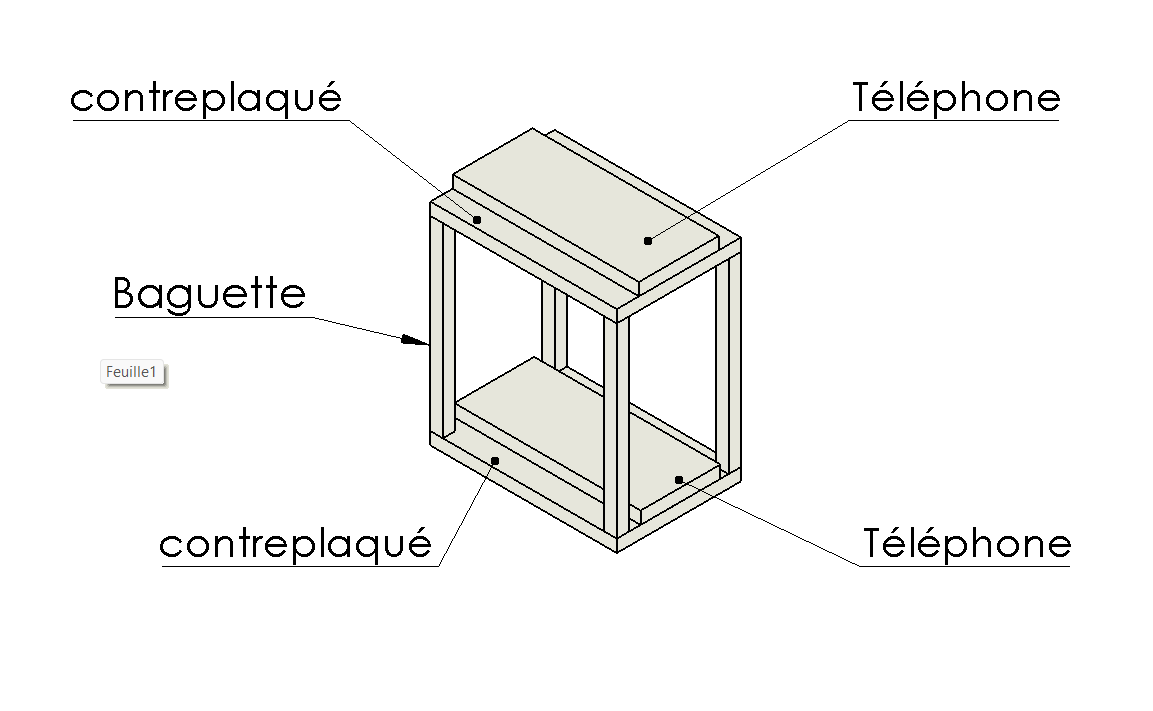
expérience/immeuble/modèle rigide.png
