Docredstein/TIPE_TMD/rendu/image/preview_hd.png

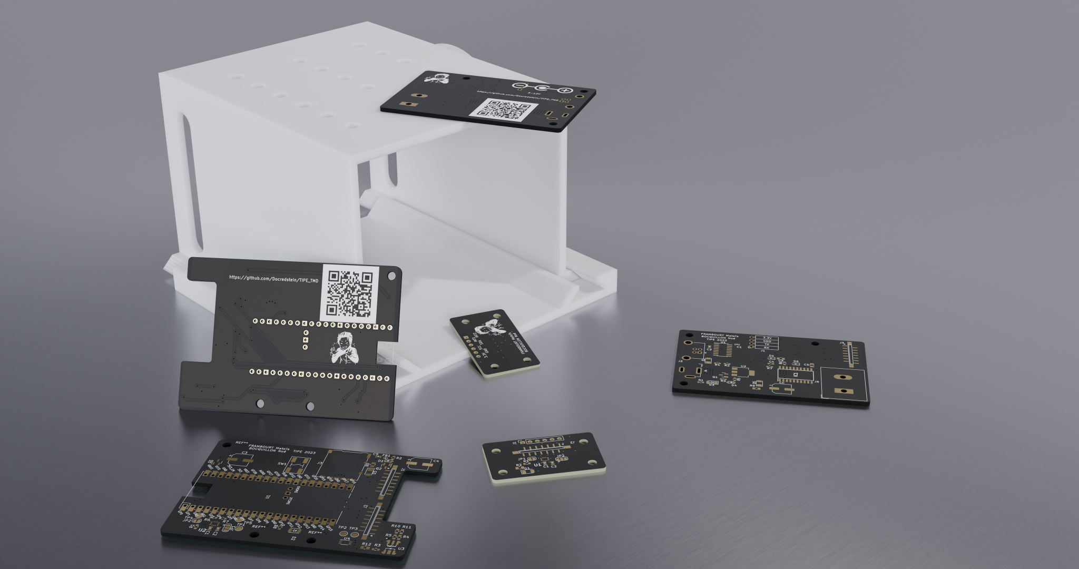
rendu/image/preview_hd.png
