Docredstein/TIPE_TMD/test axe linéaire/Pendule attache.SLDPRT

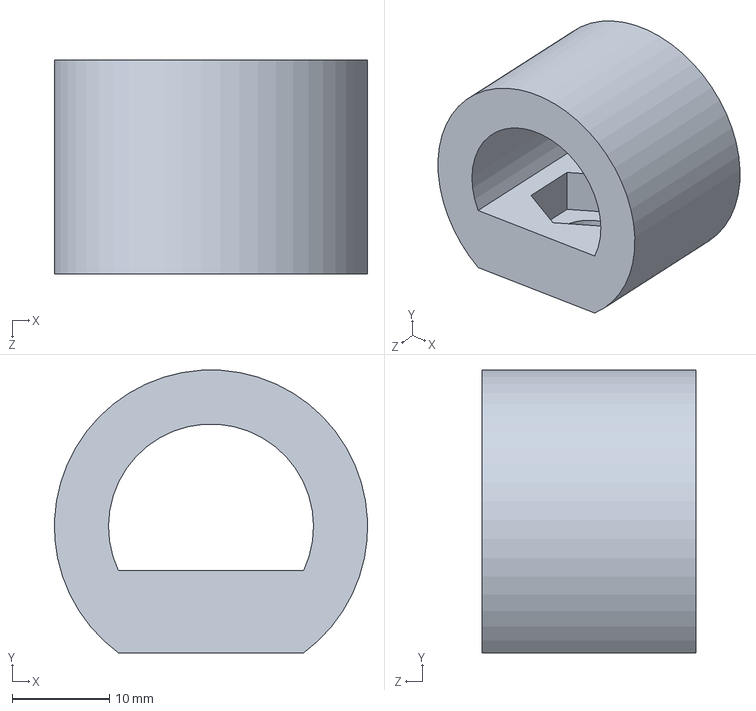
[picture p263: CAD file, 2023-01-23]
test axe linéaire/Pendule attache.SLDPRT
32.2 x 29.1 x 22.1 mm
