Docredstein/TIPE_TMD/expérience/immeuble/base.SLDPRT

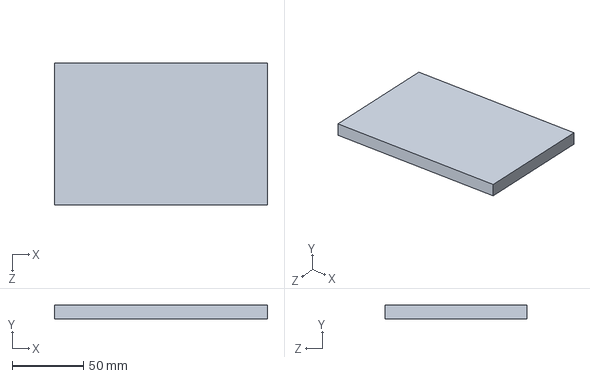
[picture p264: CAD file, 2022-10-06]
expérience/immeuble/base.SLDPRT
150.0 x 10.0 x 100.0 mm
