Docredstein/TIPE_TMD/Simulation/Matlab/base.SLDPRT

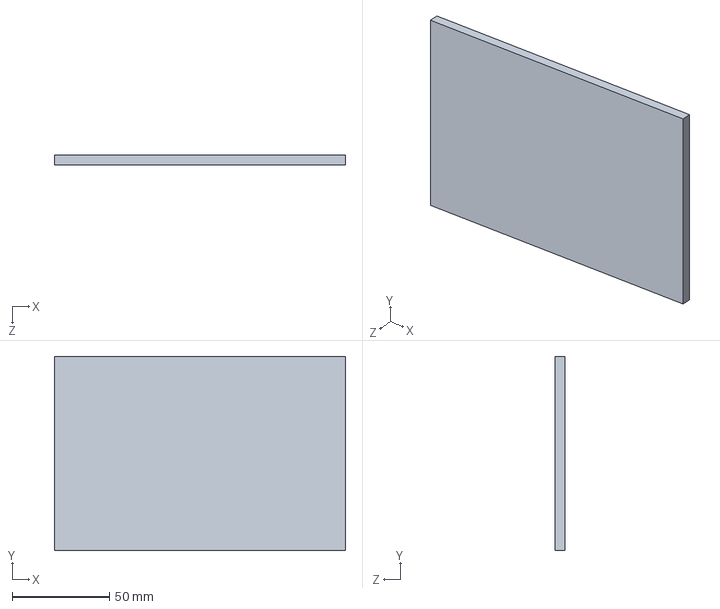
[picture p265: CAD file, 2023-04-06]
Simulation/Matlab/base.SLDPRT
150.0 x 100.0 x 5.00 mm
