Docredstein/TIPE_TMD/expérience/immeuble/baguette.SLDPRT

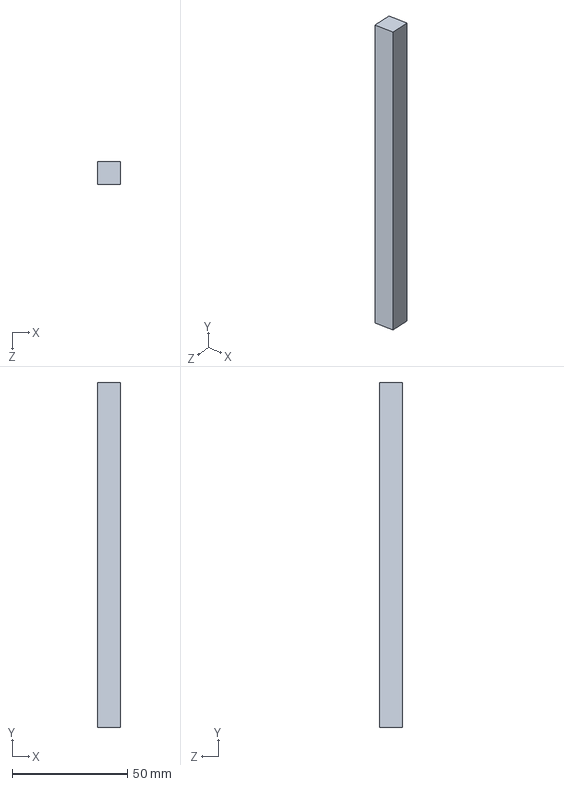
[picture p266: CAD file, 2022-10-06]
expérience/immeuble/baguette.SLDPRT
10.0 x 150.0 x 10.0 mm
