Docredstein/TIPE_TMD/Simulation/Matlab/bouchon.SLDPRT

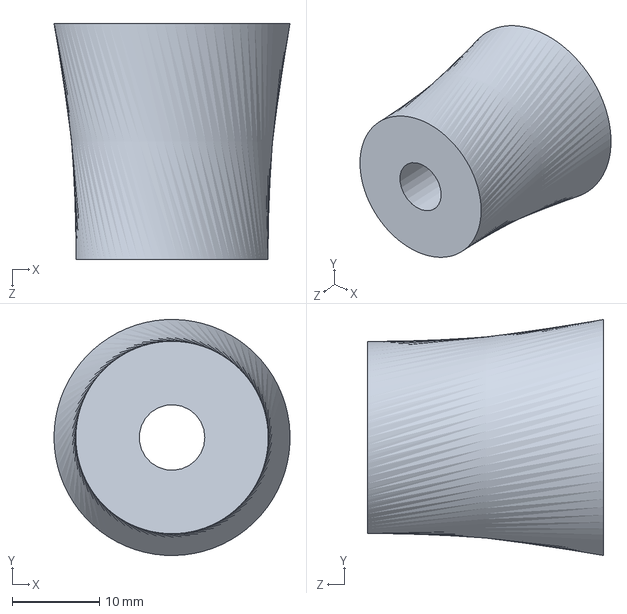
[picture p267: CAD file, 2023-04-06]
Simulation/Matlab/bouchon.SLDPRT
27.0 x 27.0 x 27.0 mm
