Docredstein/TIPE_TMD/test axe linéaire/oscillant.SLDPRT

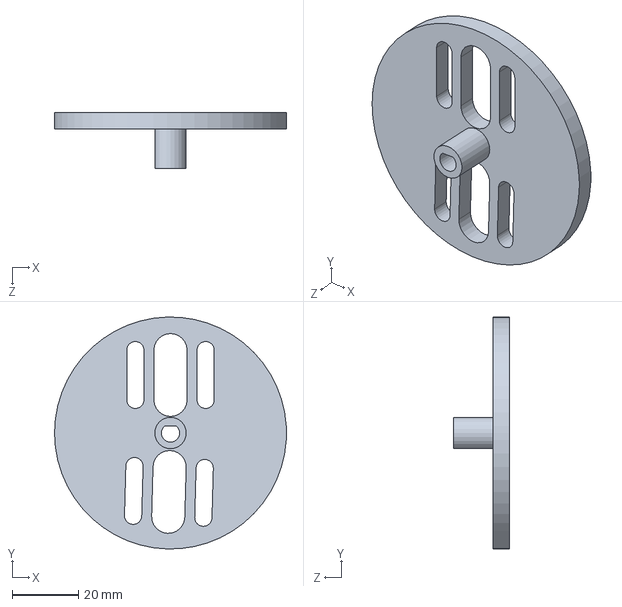
[picture p268: CAD file, 2023-01-23]
test axe linéaire/oscillant.SLDPRT
70.0 x 70.0 x 17.0 mm
