Docredstein/TIPE_TMD/Simulation/Matlab/baguette chinoise.SLDPRT

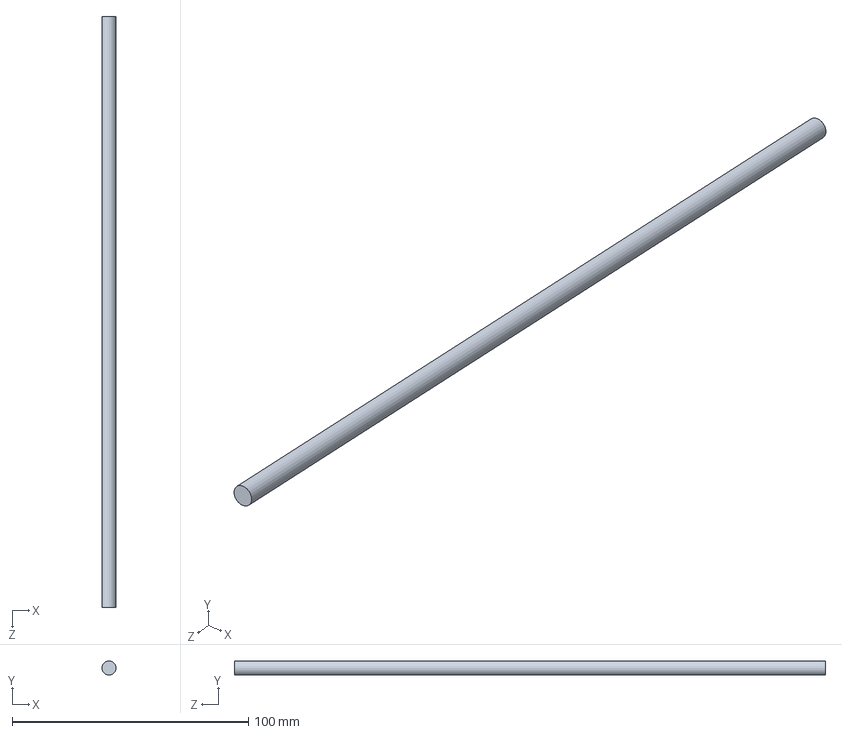
[picture p269: CAD file, 2023-04-06]
Simulation/Matlab/baguette chinoise.SLDPRT
6.00 x 6.00 x 250.0 mm
