Docredstein/TIPE_TMD/test axe linéaire/planche support.SLDPRT

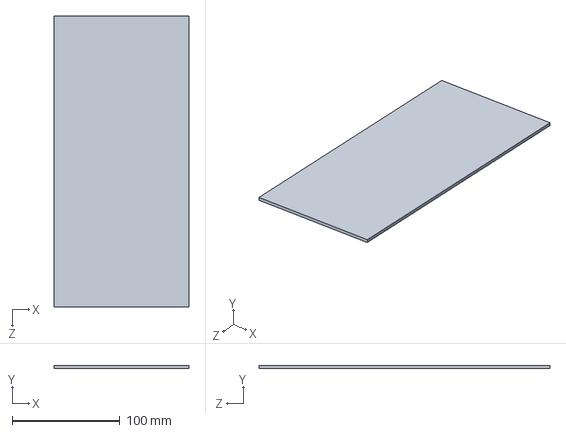
[picture p270: CAD file, 2022-10-06]
test axe linéaire/planche support.SLDPRT
125.0 x 3.00 x 270.0 mm
