Docredstein/TIPE_TMD/test axe linéaire/tige filetée.SLDPRT

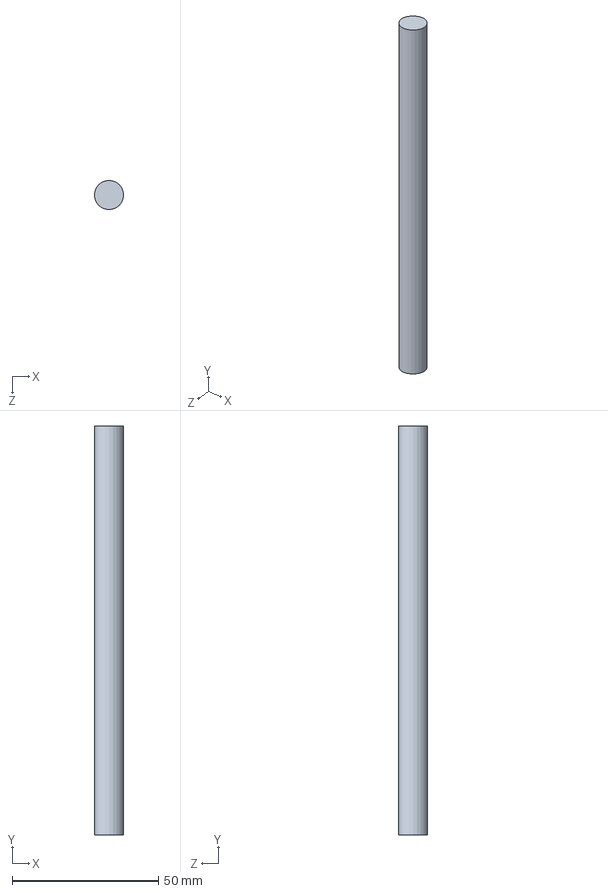
[picture p271: CAD file, 2022-10-06]
test axe linéaire/tige filetée.SLDPRT
10.0 x 140.0 x 10.0 mm
