Docredstein/TIPE_TMD/test axe linéaire/base.SLDPRT

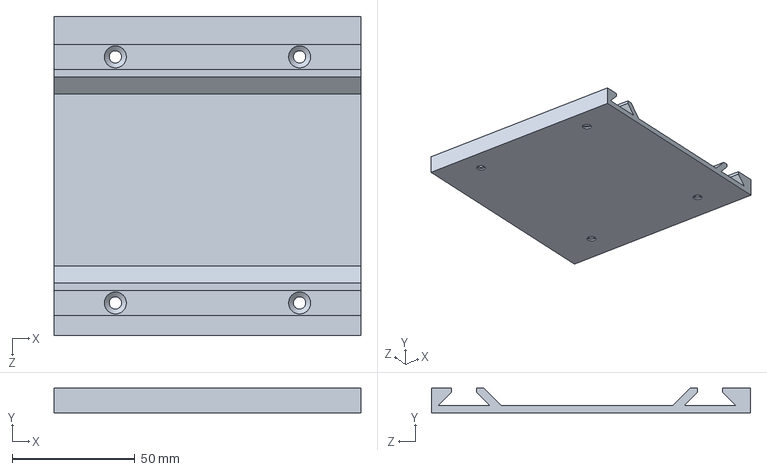
[picture p272: CAD file, 2022-10-06]
test axe linéaire/base.SLDPRT
125.0 x 10.0 x 130.0 mm
