Docredstein/TIPE_TMD/test axe linéaire/glissière.SLDPRT

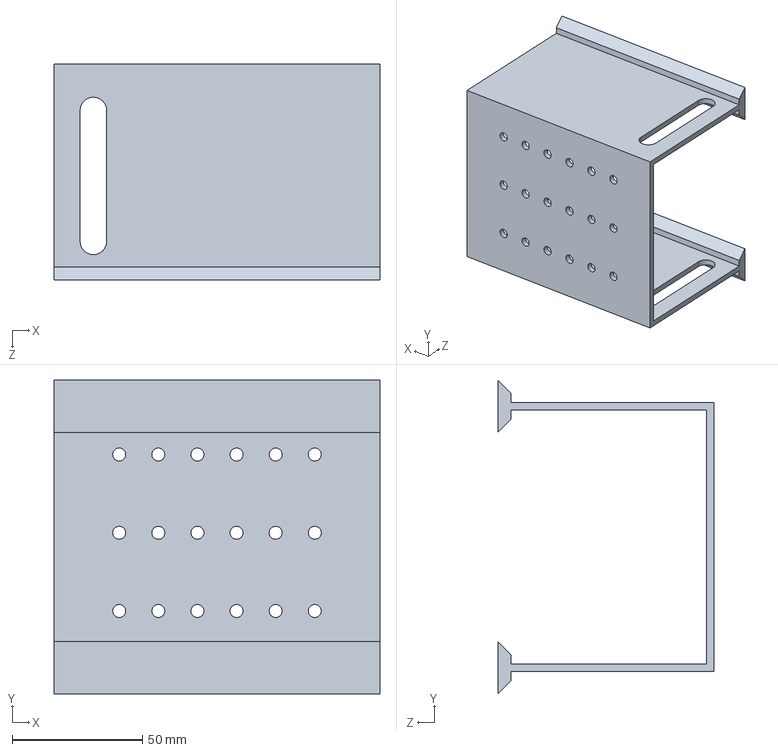
[picture p273: CAD file, 2022-10-06]
test axe linéaire/glissière.SLDPRT
125.0 x 120.2 x 83.0 mm
