Docredstein/TIPE_TMD/test axe linéaire/vérou d'axe.SLDPRT

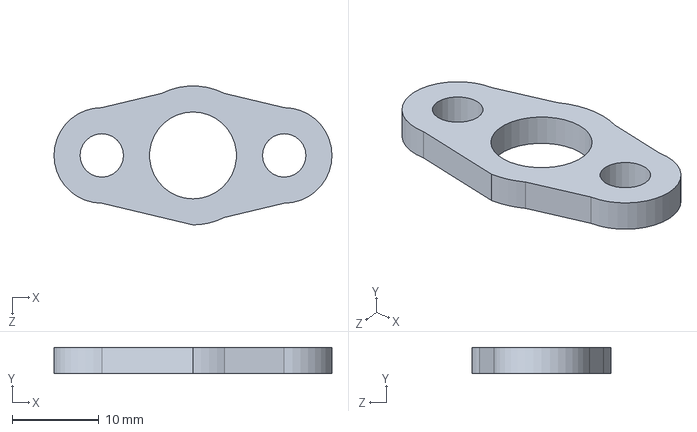
[picture p274: CAD file, 2022-10-06]
test axe linéaire/vérou d'axe.SLDPRT
32.0 x 3.00 x 16.0 mm
