Docredstein/TIPE_TMD/test axe linéaire/moteur simpliste.SLDPRT

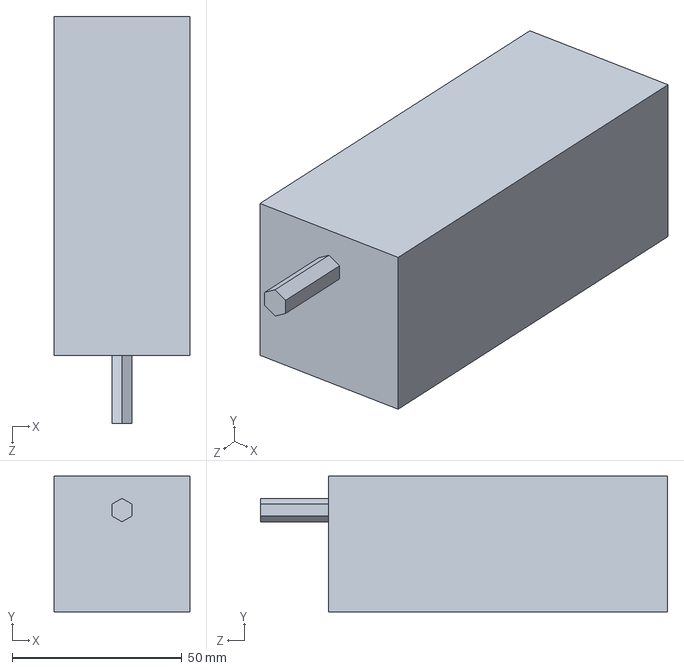
[picture p275: CAD file, 2022-10-06]
test axe linéaire/moteur simpliste.SLDPRT
40.0 x 40.0 x 120.0 mm
