Docredstein/TIPE_TMD/Beamer/Image/Montage complet du dessus.jpg

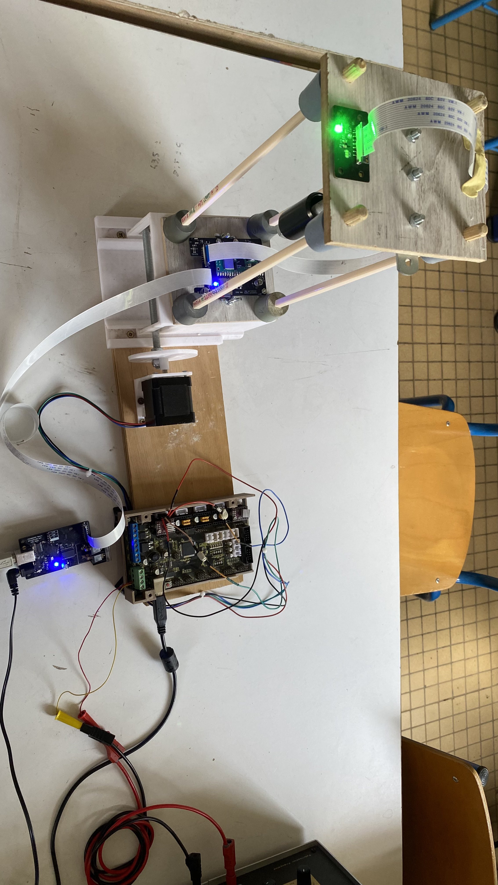
Beamer/Image/Montage complet du dessus.jpg
