Docredstein/TIPE_TMD/Beamer/Image/Montage complet profil peu lisible masse en bas.jpg

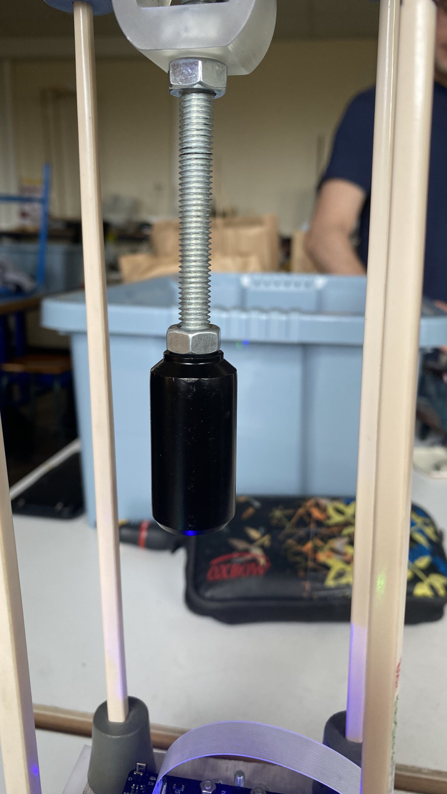
Beamer/Image/Montage complet profil peu lisible masse en bas.jpg
