Docredstein/TIPE_TMD/Beamer/Image/Montage complet profil peu lisible.jpg

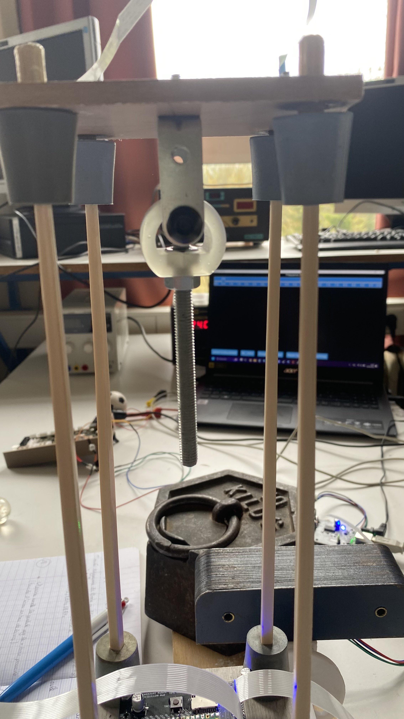
Beamer/Image/Montage complet profil peu lisible.jpg
