Docredstein/TIPE_TMD/Beamer/Image/Montage complet propre 2.jpg

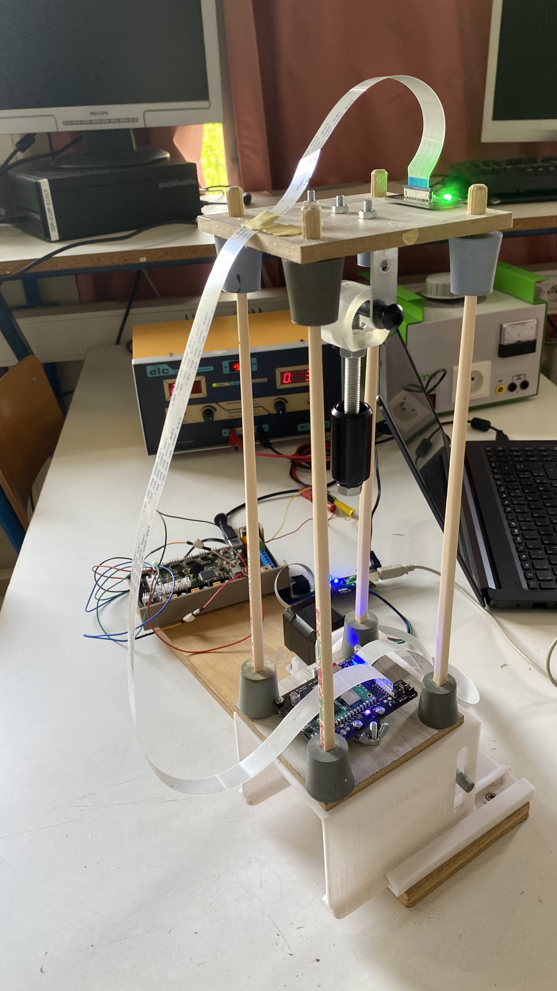
Beamer/Image/Montage complet propre 2.jpg
