Docredstein/TIPE_TMD/Beamer/Image/Montage complet propre 7.jpg

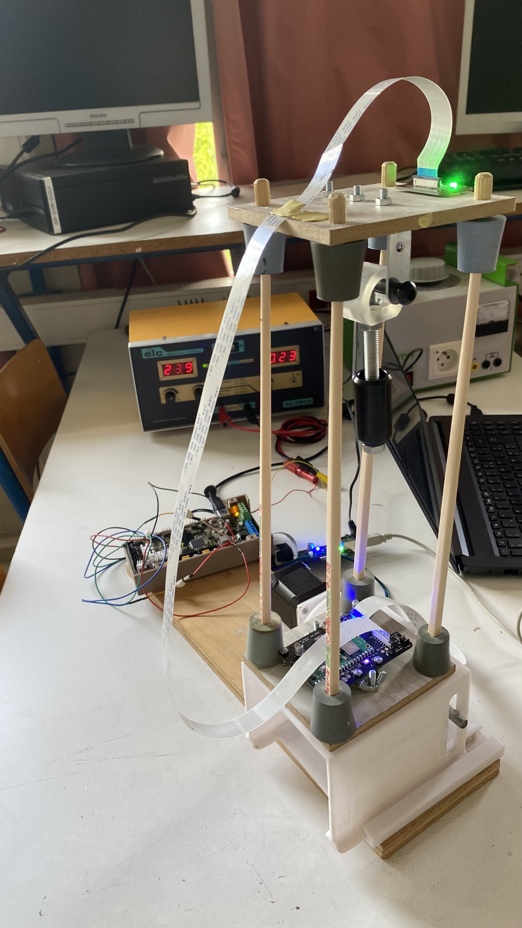
Beamer/Image/Montage complet propre 7.jpg
