Docredstein/TIPE_TMD/Beamer/Image/Montage complet propre 8.jpg

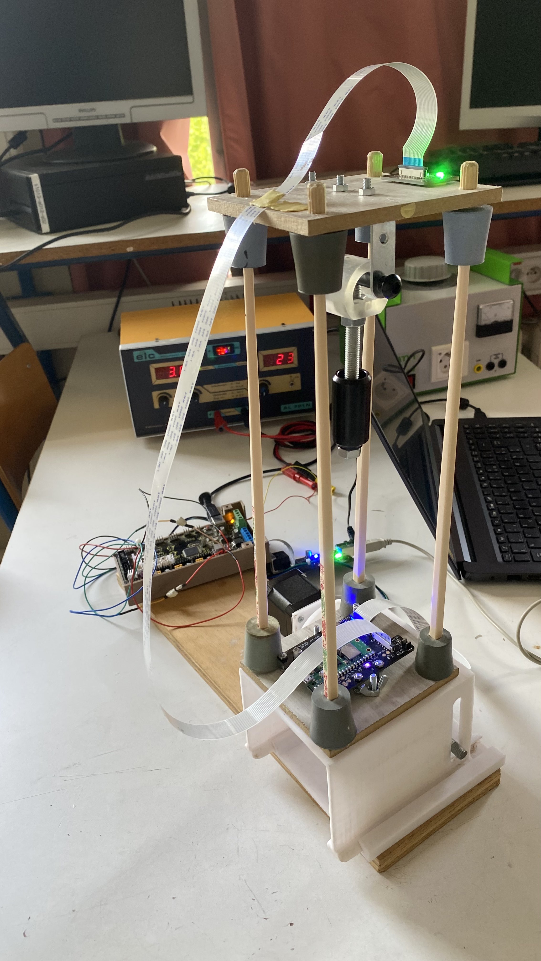
Beamer/Image/Montage complet propre 8.jpg
