Docredstein/TIPE_TMD/Beamer/Image/Montage complet propre.jpg

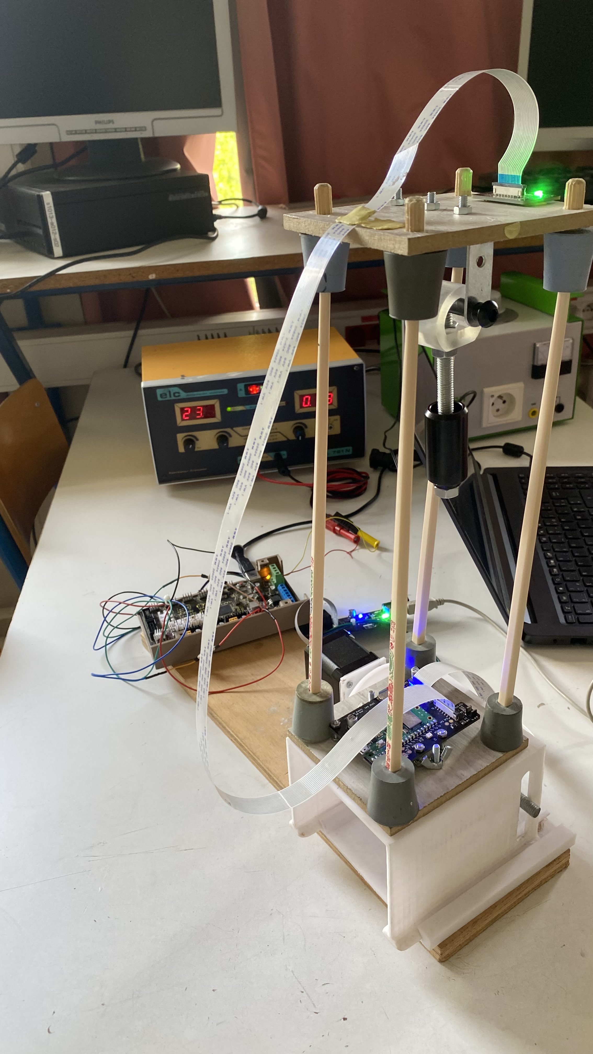
Beamer/Image/Montage complet propre.jpg
