Docredstein/TIPE_TMD/Beamer/Image/Montage excentrique originel.png

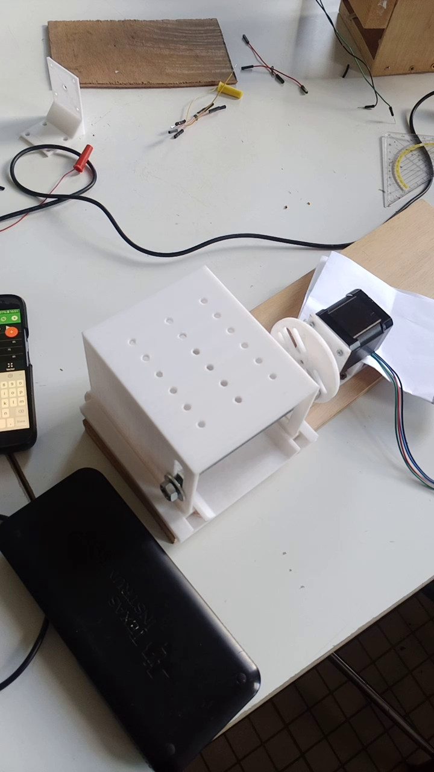
Beamer/Image/Montage excentrique originel.png
