Docredstein/TIPE_TMD/Beamer/Image/Montage masse réglable.jpg

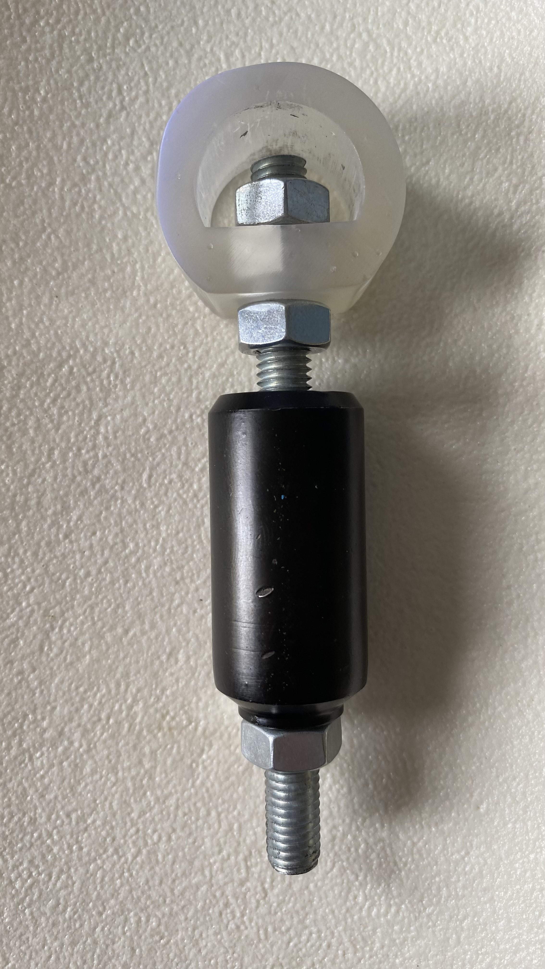
Beamer/Image/Montage masse réglable.jpg
