Docredstein/TIPE_TMD/Circuit imprimé/assemblage/assemblage.png

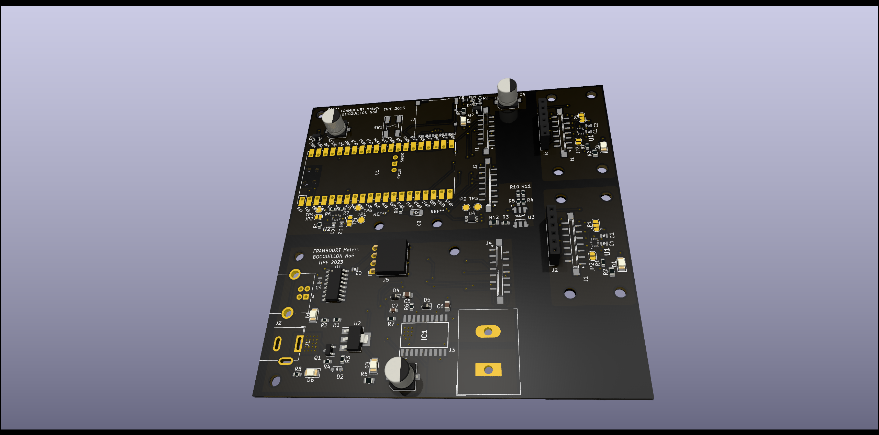
Circuit imprimé/assemblage/assemblage.png
