Docredstein/TIPE_TMD/Circuit imprimé/assemblage/assemblage_back.png

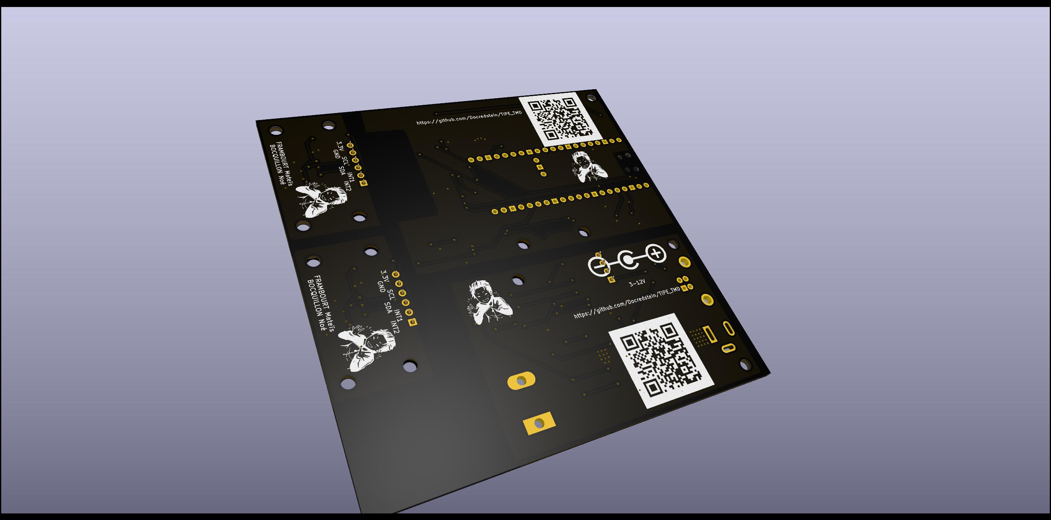
Circuit imprimé/assemblage/assemblage_back.png
