Docredstein/TIPE_TMD/Analyse/Cleaned/pendule 1 masse au plus bas test bof/1 hz biss.csv

1.124008584000000000e+09 | -5.367617027067895918e+01 | 8.043329200060487238e+00 | 1.989880840768250891e+00 | -2.452347588084076691e+01 | 2.033678750793890799e+02 | nan
1.124015574000000000e+09 | -4.672217027067895856e+01 | 7.555329200060487693e+00 | 2.477880840768307280e+00 | -2.427947588084076713e+01 | 2.001958750793890829e+02 | nan
1.124020845000000000e+09 | -4.672217027067895856e+01 | 7.555329200060487693e+00 | 2.477880840768307280e+00 | -2.318147588084076816e+01 | 1.960478750793890867e+02 | nan
1.124028808000000000e+09 | -3.989017027067896493e+01 | 6.335329200060488830e+00 | 2.111880840768321832e+00 | -2.318147588084076816e+01 | 1.960478750793890867e+02 | nan
1.124035045000000000e+09 | -3.610817027067896134e+01 | 3.041329200060488347e+00 | 1.989880840768250891e+00 | -2.110747588084076654e+01 | 1.899478750793890640e+02 | nan
1.124041171000000000e+09 | -3.610817027067896134e+01 | 3.041329200060488347e+00 | 1.989880840768250891e+00 | -1.830147588084076560e+01 | 1.840918750793890695e+02 | nan
1.124046435000000000e+09 | -3.403417027067895617e+01 | 4.749329200060486755e+00 | -6.941191592317181858e-01 | -1.830147588084076560e+01 | 1.840918750793890695e+02 | nan
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
