Docredstein/TIPE_TMD/Analyse/Cleaned/pendule 1 masse au plus bas test bof/1.5Hz.csv

1.780262039000000000e+09 | 4.118230688325326128e-01 | 1.418034357835704640e-01 | -4.612247282925636682e-01 | -2.447798761248101140e+00 | 9.714233960500173737e-01 | 1.419312562814184275e+00
1.780269440000000000e+09 | 4.118230688325326128e-01 | 1.418034357835704640e-01 | -4.612247282925636682e-01 | -2.447798761248101140e+00 | 9.714233960500173737e-01 | 1.541312562814141529e+00
1.780274259000000000e+09 | 4.118230688325326128e-01 | 1.418034357835704640e-01 | -4.612247282925636682e-01 | -2.447798761248101140e+00 | 9.714233960500173737e-01 | 1.541312562814141529e+00
1.780279906000000000e+09 | 4.118230688325326128e-01 | 1.418034357835704640e-01 | -4.612247282925636682e-01 | -2.447798761248101140e+00 | 9.714233960500173737e-01 | 1.419312562814184275e+00
1.780285542000000000e+09 | 4.118230688325326128e-01 | 1.418034357835704640e-01 | -4.612247282925636682e-01 | -2.447798761248101140e+00 | 9.714233960500173737e-01 | 1.419312562814184275e+00
1.780292100000000000e+09 | 2.898230688325327264e-01 | 1.980343578357057766e-02 | -4.612247282925636682e-01 | -2.447798761248101140e+00 | 9.714233960500173737e-01 | 1.419312562814184275e+00
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
