Docredstein/TIPE_TMD/Analyse/Cleaned/pendule 1 masse au plus bas test bof/1.5hz bis.csv

1.124008584000000000e+09 | -5.377507522123893580e+01 | 7.877970032180211746e+00 | 1.565699316170594102e+00 | -2.458942880128720887e+01 | 2.028735758145615478e+02 | nan
1.124015574000000000e+09 | -4.682107522123894228e+01 | 7.389970032180212201e+00 | 2.053699316170650491e+00 | -2.434542880128720910e+01 | 1.997015758145615507e+02 | nan
1.124020845000000000e+09 | -4.682107522123894228e+01 | 7.389970032180212201e+00 | 2.053699316170650491e+00 | -2.324742880128721012e+01 | 1.955535758145615546e+02 | nan
1.124028808000000000e+09 | -3.998907522123893443e+01 | 6.169970032180213337e+00 | 1.687699316170665043e+00 | -2.324742880128721012e+01 | 1.955535758145615546e+02 | nan
1.124035045000000000e+09 | -3.620707522123893796e+01 | 2.875970032180212854e+00 | 1.565699316170594102e+00 | -2.117342880128720850e+01 | 1.894535758145615318e+02 | nan
1.124041171000000000e+09 | -3.620707522123893796e+01 | 2.875970032180212854e+00 | 1.565699316170594102e+00 | -1.836742880128720756e+01 | 1.835975758145615373e+02 | nan
1.124046435000000000e+09 | -3.413307522123893989e+01 | 4.583970032180211263e+00 | -1.118300683829374975e+00 | -1.836742880128720756e+01 | 1.835975758145615373e+02 | nan
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
