Docredstein/TIPE_TMD/Analyse/Cleaned/pendule 1 masse au plus bas test bof/1.7 hz bis ( bof).csv

1.281872260000000000e+09 | -4.365756689995880180e+00 | -2.365890901605602892e+00 | 4.522387813915429433e-01 | -2.704693289419514812e+00 | -1.370679291889665308e+00 | 4.070566282420827520e+00
1.281877985000000000e+09 | -4.365756689995880180e+00 | -2.487890901605602778e+00 | 4.522387813915429433e-01 | -2.704693289419514812e+00 | -1.370679291889665308e+00 | 4.070566282420827520e+00
1.281883721000000000e+09 | -4.365756689995880180e+00 | -2.487890901605602778e+00 | 4.522387813915429433e-01 | -2.704693289419514812e+00 | -1.370679291889665308e+00 | 4.070566282420827520e+00
1.281890356000000000e+09 | -4.365756689995880180e+00 | -2.487890901605602778e+00 | 4.522387813915429433e-01 | -2.704693289419514812e+00 | -1.370679291889665308e+00 | 4.070566282420827520e+00
1.281928974000000000e+09 | -4.365756689995880180e+00 | -2.853890901605602437e+00 | 5.742387813915001971e-01 | -2.826693289419514699e+00 | -1.370679291889665308e+00 | 4.070566282420827520e+00
1.281936583000000000e+09 | -4.365756689995880180e+00 | -2.853890901605602437e+00 | 5.742387813915001971e-01 | -2.826693289419514699e+00 | -1.370679291889665308e+00 | 4.070566282420827520e+00
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
