Docredstein/TIPE_TMD/Analyse/Image/pendule 1 masse au plus bas test bof/0.5hz.png

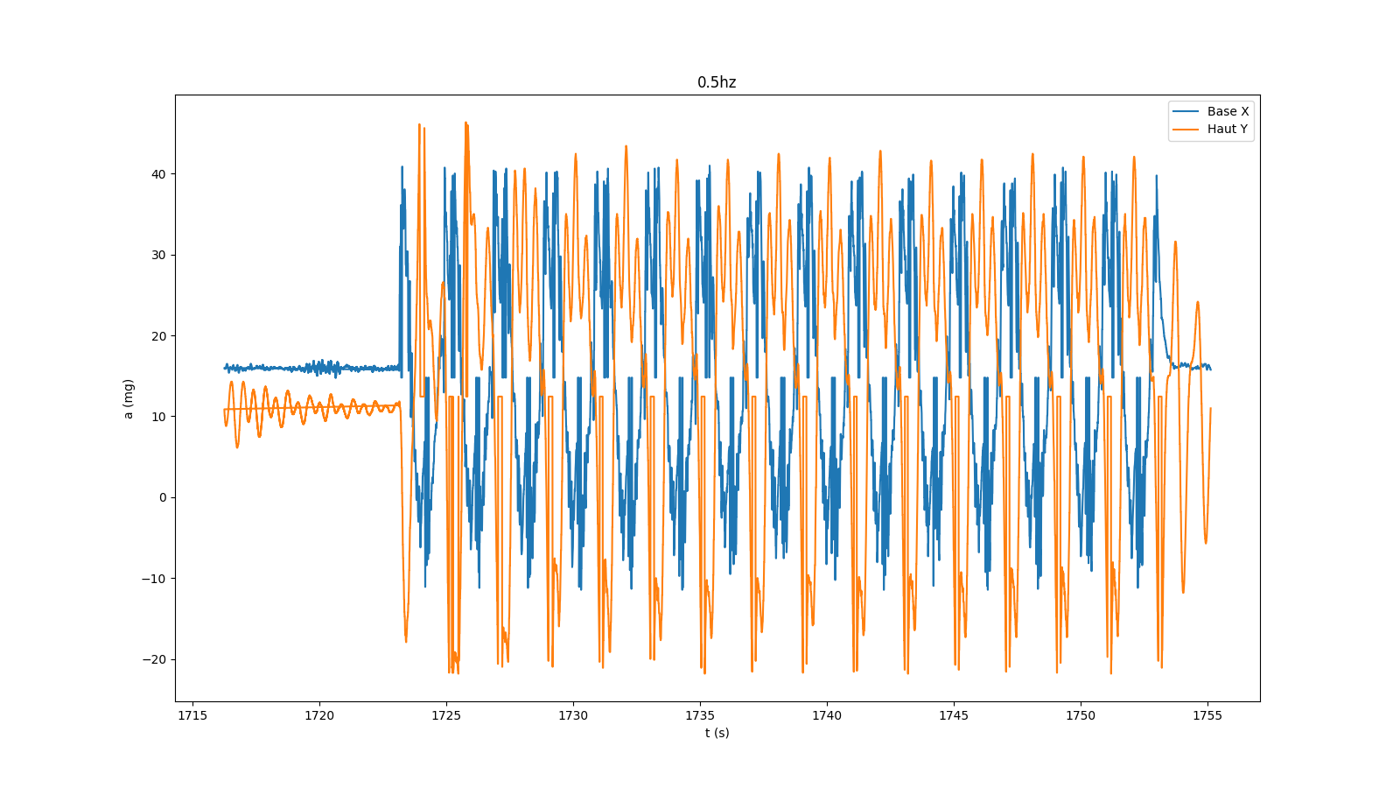
Analyse/Image/pendule 1 masse au plus bas test bof/0.5hz.png
