Docredstein/TIPE_TMD/Analyse/Image/pendule 1 masse au plus bas test bof/1 hz biss.png

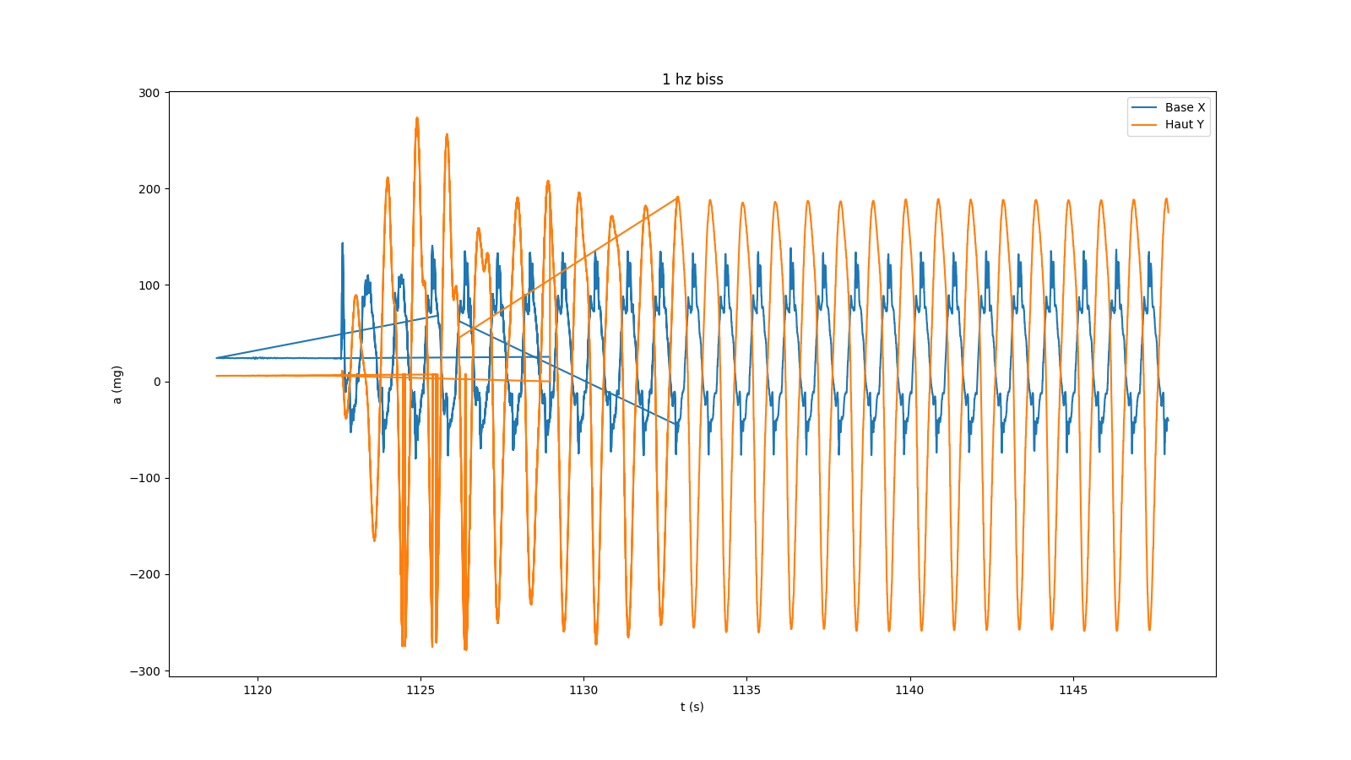
Analyse/Image/pendule 1 masse au plus bas test bof/1 hz biss.png
