Docredstein/TIPE_TMD/Analyse/Image/pendule 1 masse au plus bas test bof/1.5hz bis.png

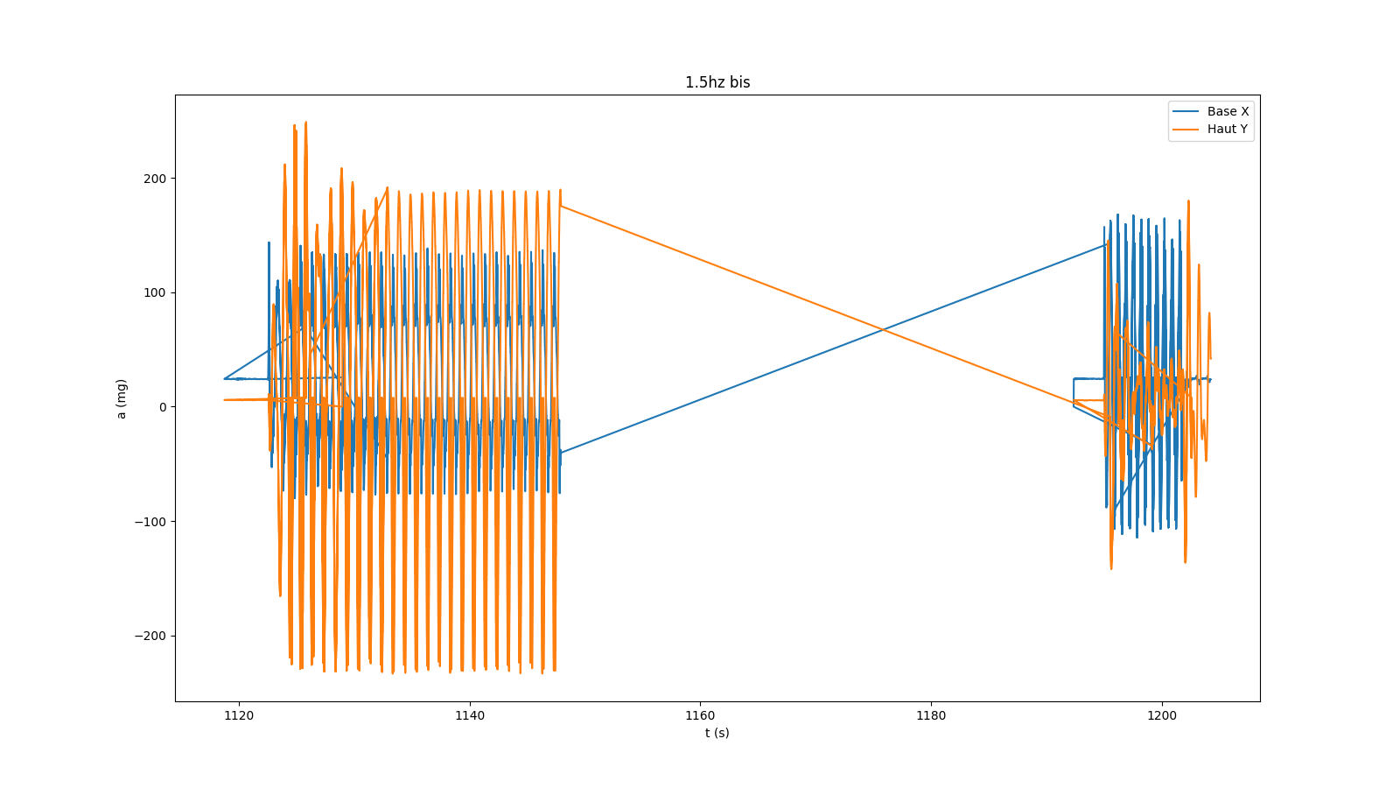
Analyse/Image/pendule 1 masse au plus bas test bof/1.5hz bis.png
