Docredstein/TIPE_TMD/Analyse/Image/pendule 1 masse au plus bas test bof/1.7 hz bis 2 (bof).png

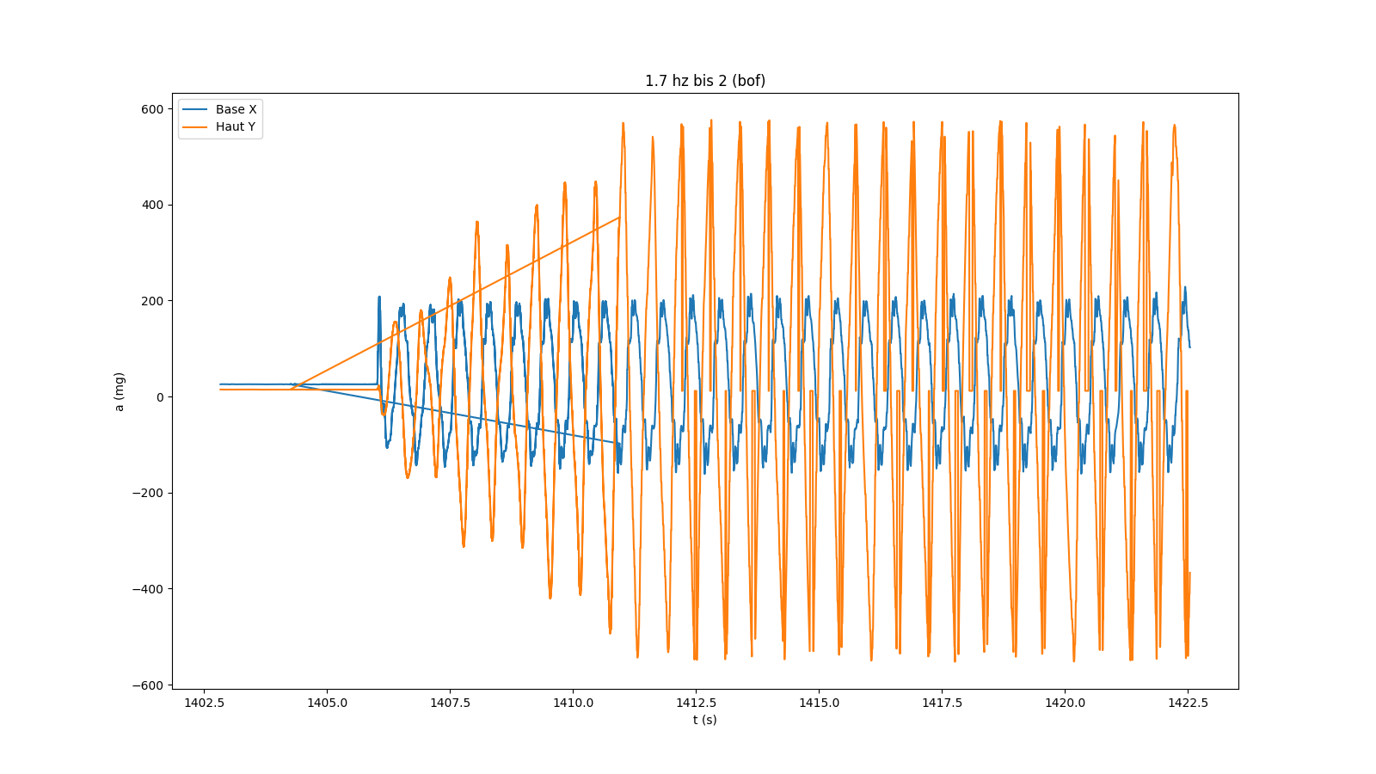
Analyse/Image/pendule 1 masse au plus bas test bof/1.7 hz bis 2 (bof).png
