Docredstein/TIPE_TMD/Analyse/Image/pendule 1 masse au plus bas test bof/1Hz.png

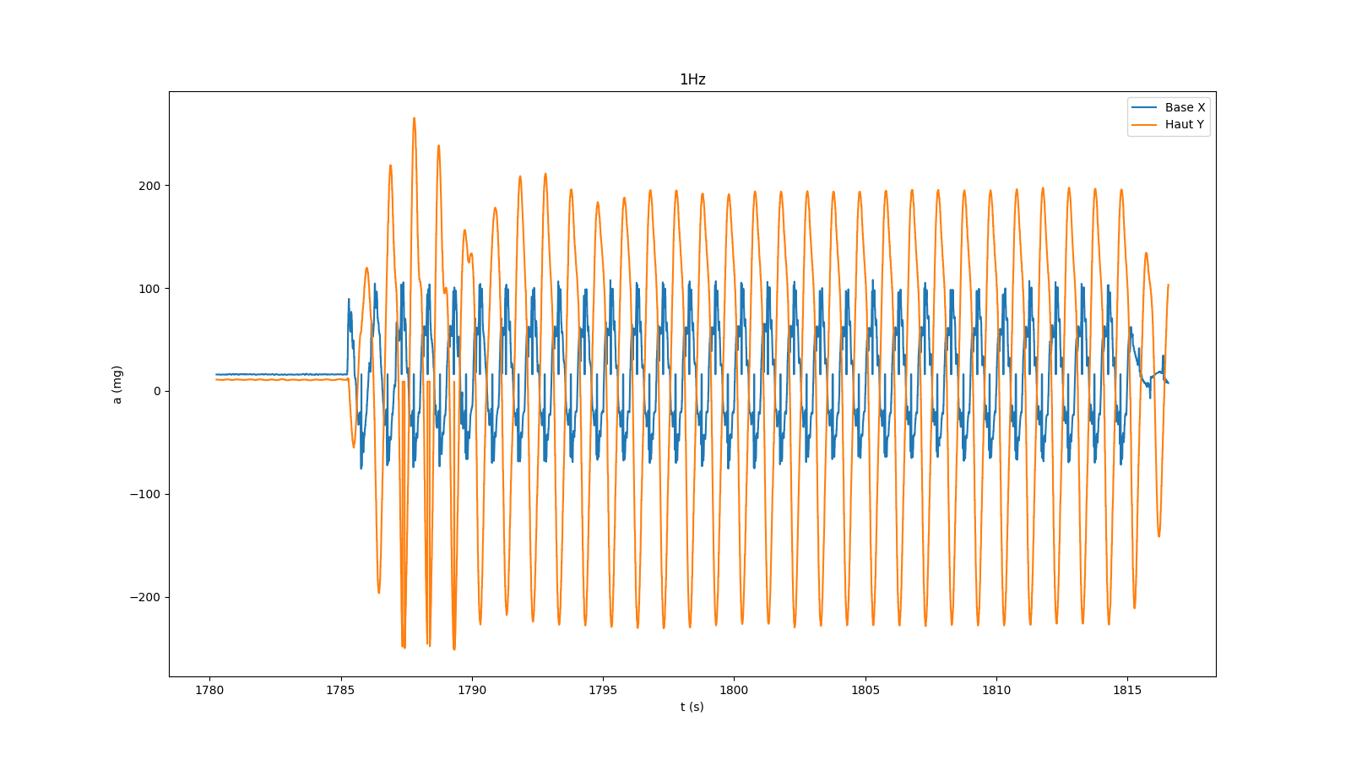
Analyse/Image/pendule 1 masse au plus bas test bof/1Hz.png
