Docredstein/TIPE_TMD/Analyse/Image/pendule_1_masse_au_plus_bas_test_bof.png

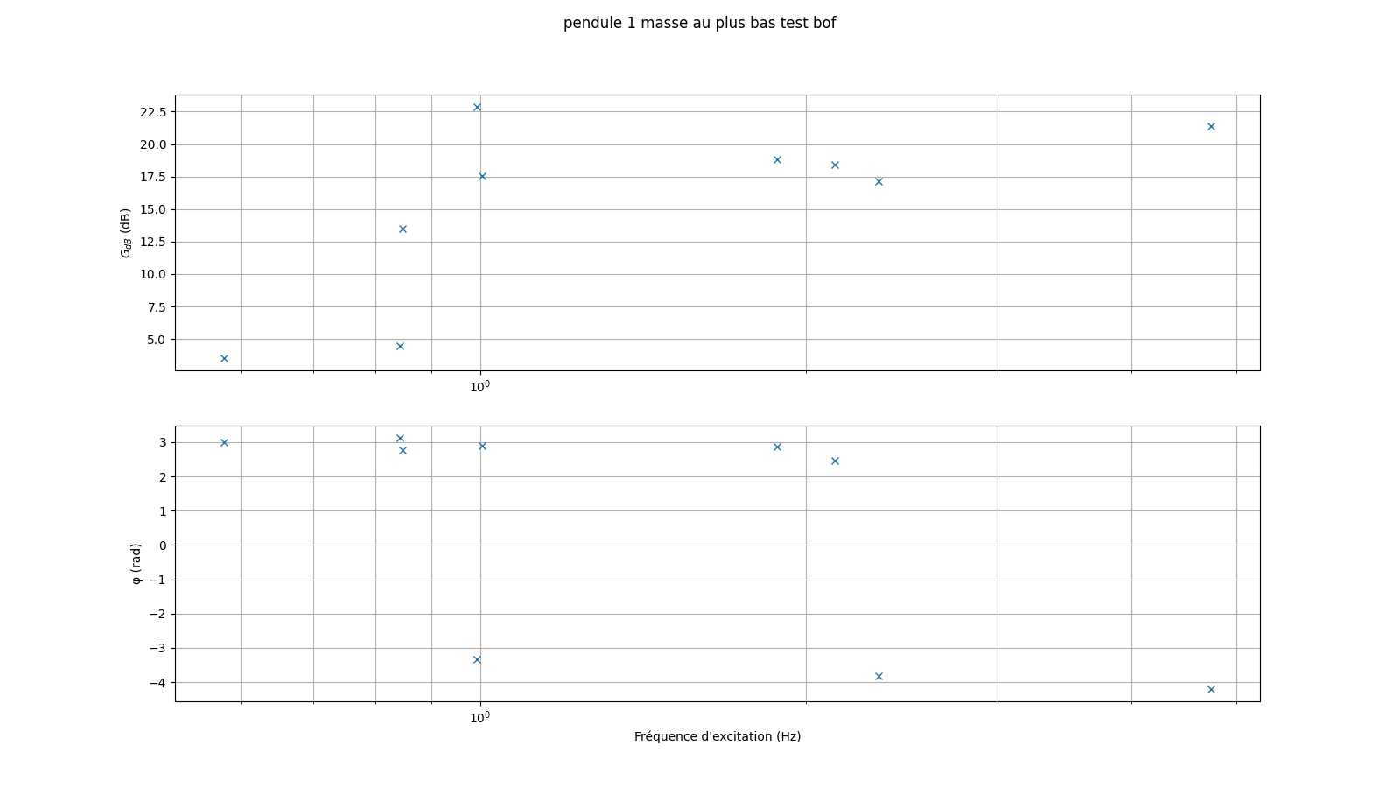
Analyse/Image/pendule_1_masse_au_plus_bas_test_bof.png
