Docredstein/TIPE_TMD/Beamer/Image/Test Carte bas.JPG

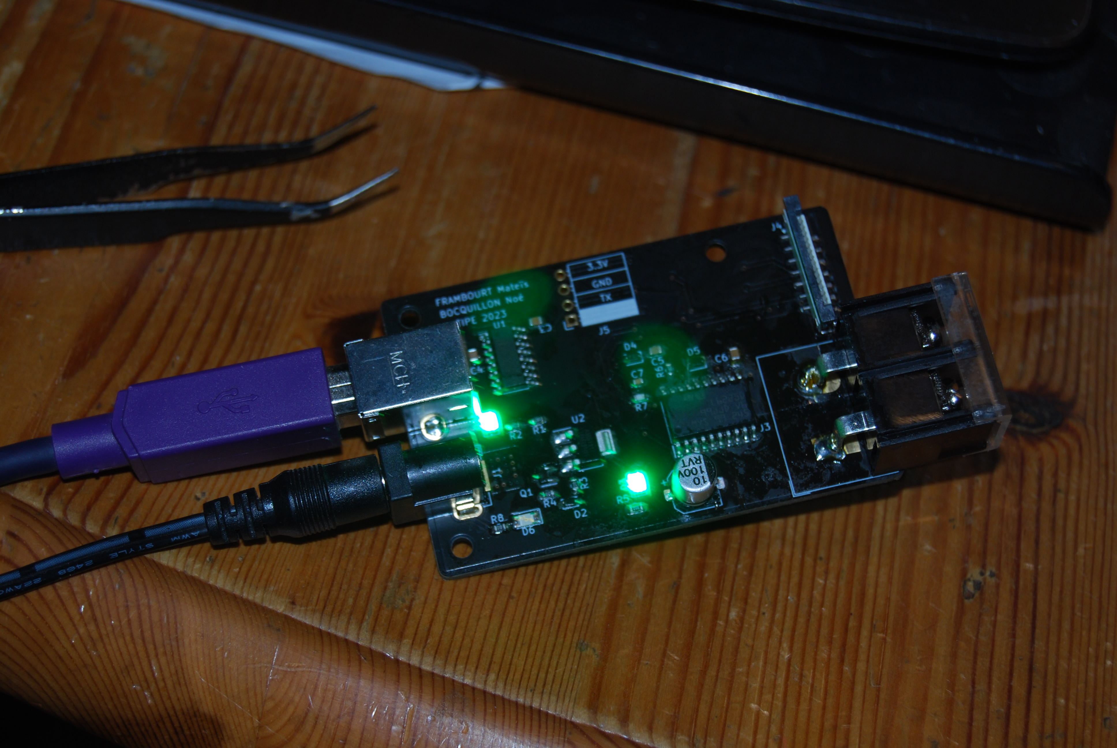
Beamer/Image/Test Carte bas.JPG
