Docredstein/TIPE_TMD/Analyse/Image/pendule 1 masse au plus bas test bof/1 hz biss._norme.pdf

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

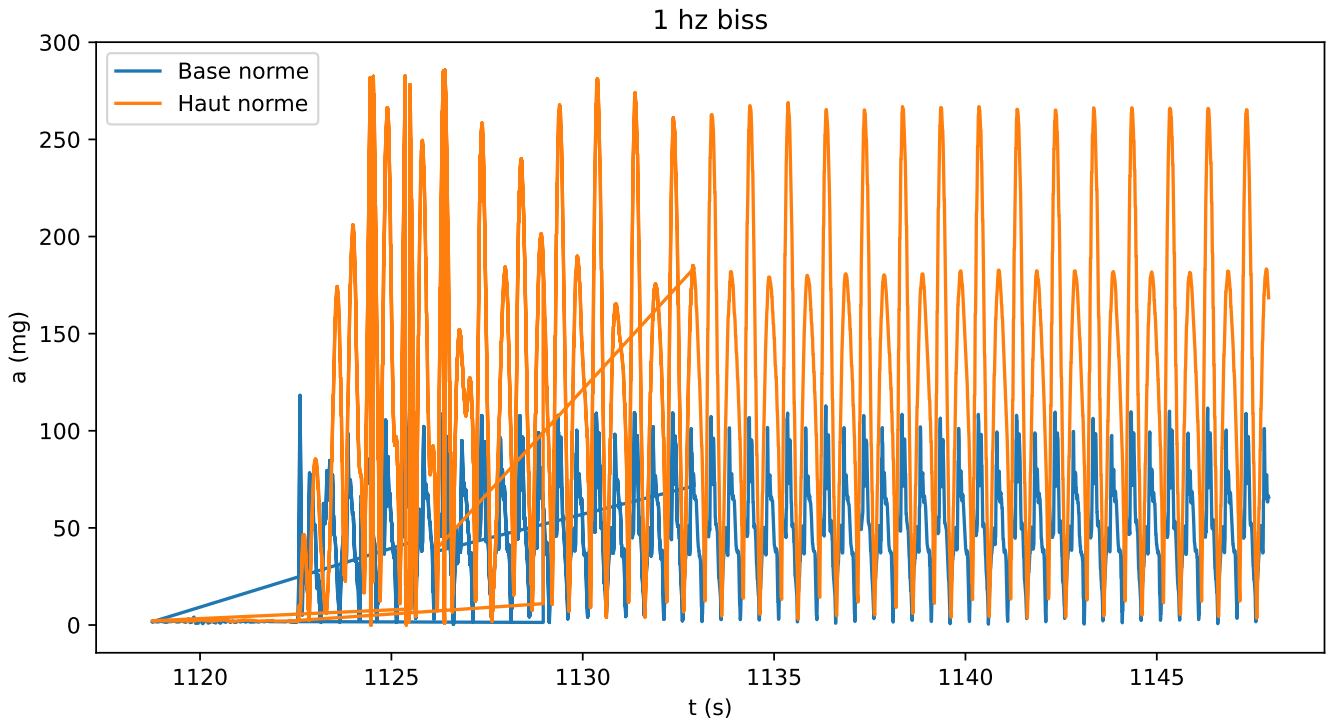
[picture p315: page 1]
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
