Docredstein/TIPE_TMD/expérience/immeuble/modèle rebondissante.pdf

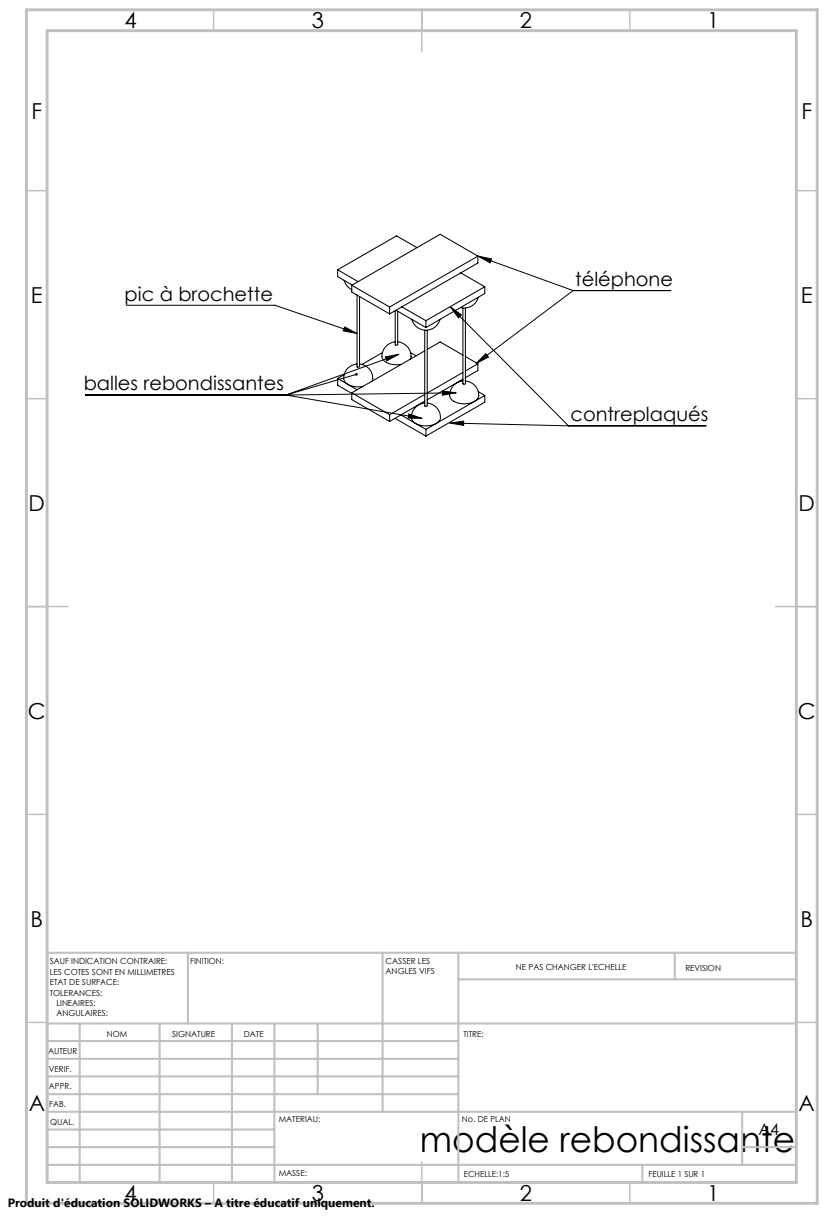
[picture p322: page 1]
pic à brochette; téléphone; balles rebondissantes; FINITION:; CASSER LES; ANGLES VIFS; NE PAS CHANGER L'ECHELLE; REVISION; ECHELLE:1:5; FEUILLE 1 SUR 1

SAUF INDICATION CONTRAIRE:
LES COTES SONT EN MILLIMETRES
ETAT DE SURFACE:
TOLERANCES:
LINEAIRES:
ANGULAIRES:

NOM | SIGNATURE | DATE | | | | TITRE:

AUTEUR
VERIF.
APPR.
FAB.
QUAL. | | | | MATERIAU: modèle rebondissante | No. DE PLAN | A4

Produit d'éducation SOLIDWORKS – A titre éducatif uniquement.
