Docredstein/TIPE_TMD/Analyse finale basse amplitude/Image/coup de vent/100g 5cm de l'axe.pdf

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

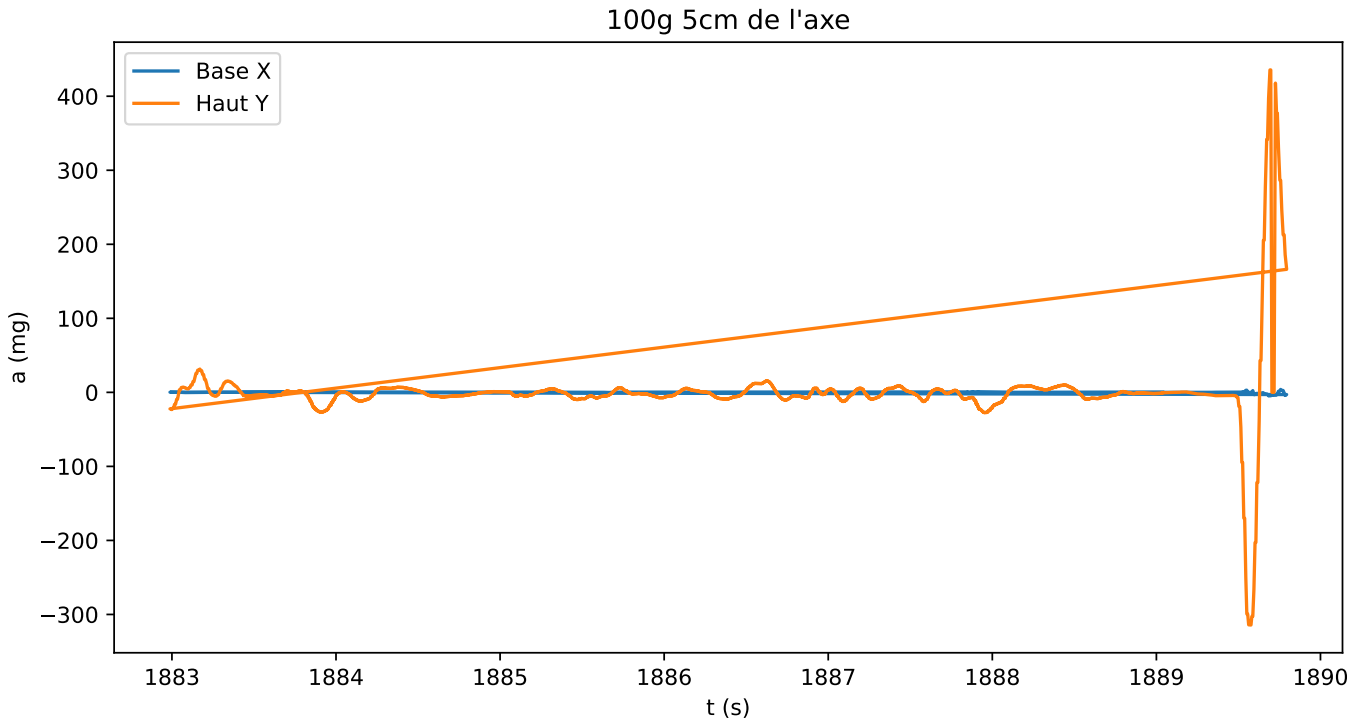
[picture p324: page 1]
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
