Docredstein/TIPE_TMD/Analyse finale basse amplitude/Image/coup de vent/sans pendule avec masse de 100g sur le toit.pdf

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

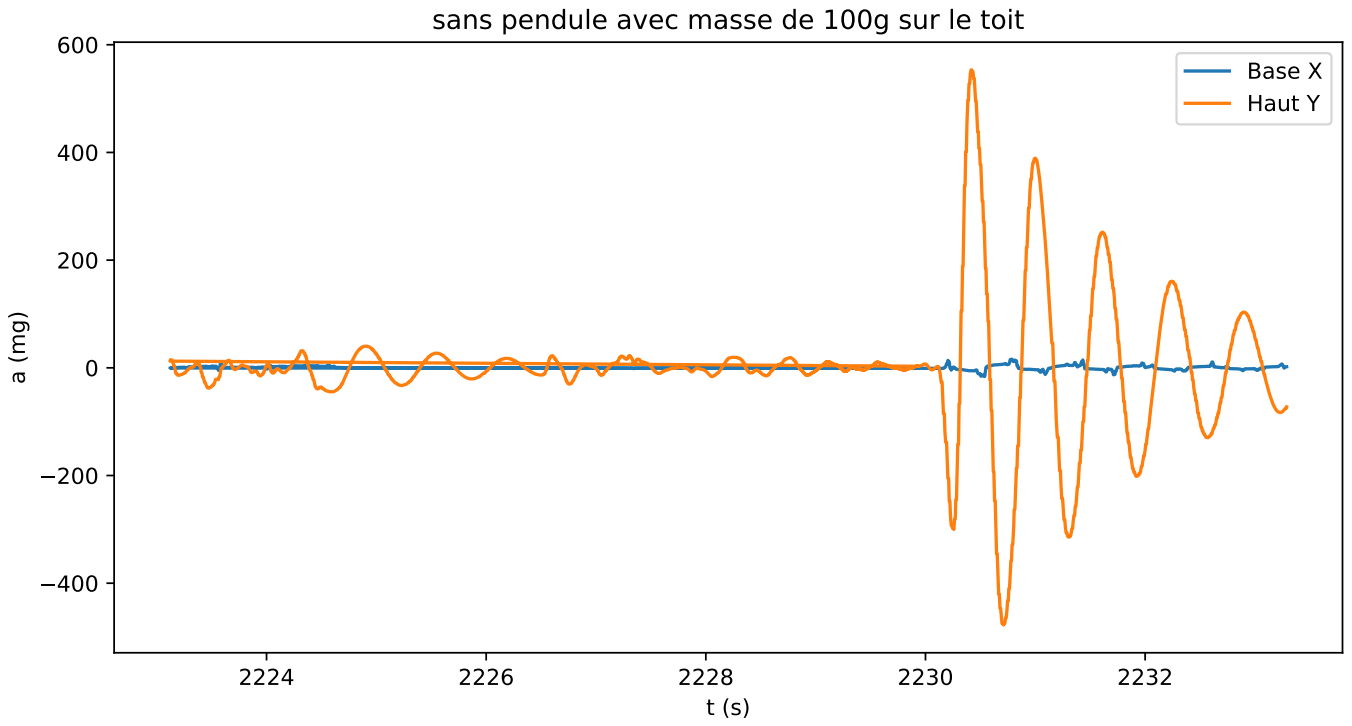
[picture p327: page 1]
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
