Docredstein/TIPE_TMD/Analyse finale basse amplitude/Image/masse en bas (9.4gcm) de  100g/2.3hz.pdf

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

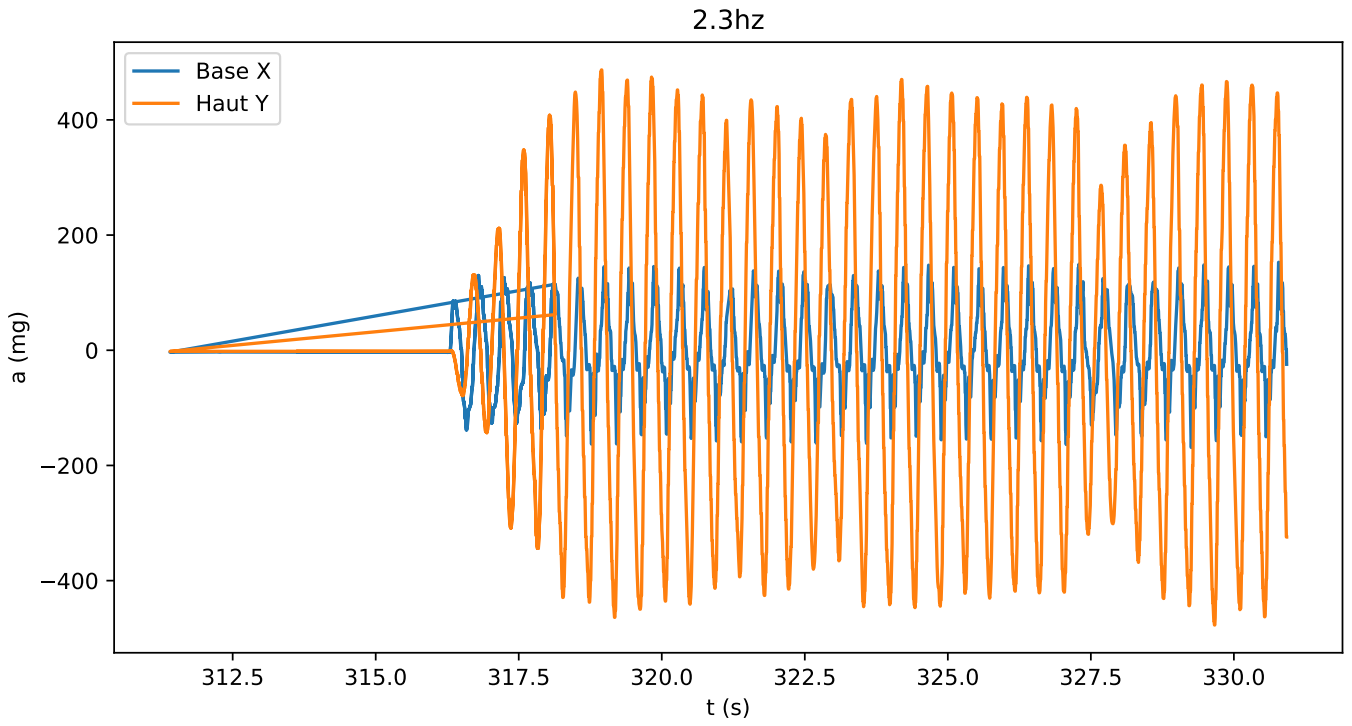
[picture p331: page 1]
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
