Docredstein/TIPE_TMD/Analyse finale basse amplitude/Image/masse à 3 cm de l'axe de 100g/2.5hz.pdf

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

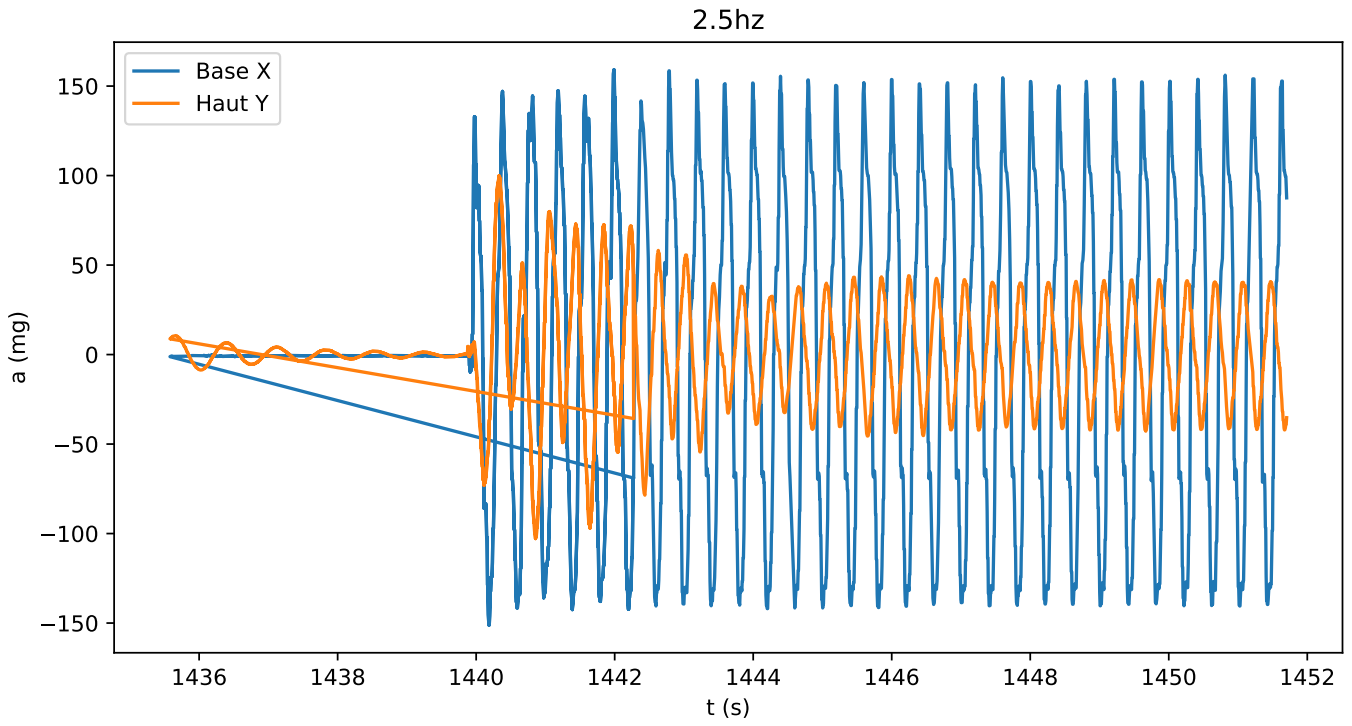
[picture p342: page 1]
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
