Docredstein/TIPE_TMD/Analyse finale basse amplitude/Image/masse à 5,5 cm de l'axe de 73,3 g/2.1 hz.pdf

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

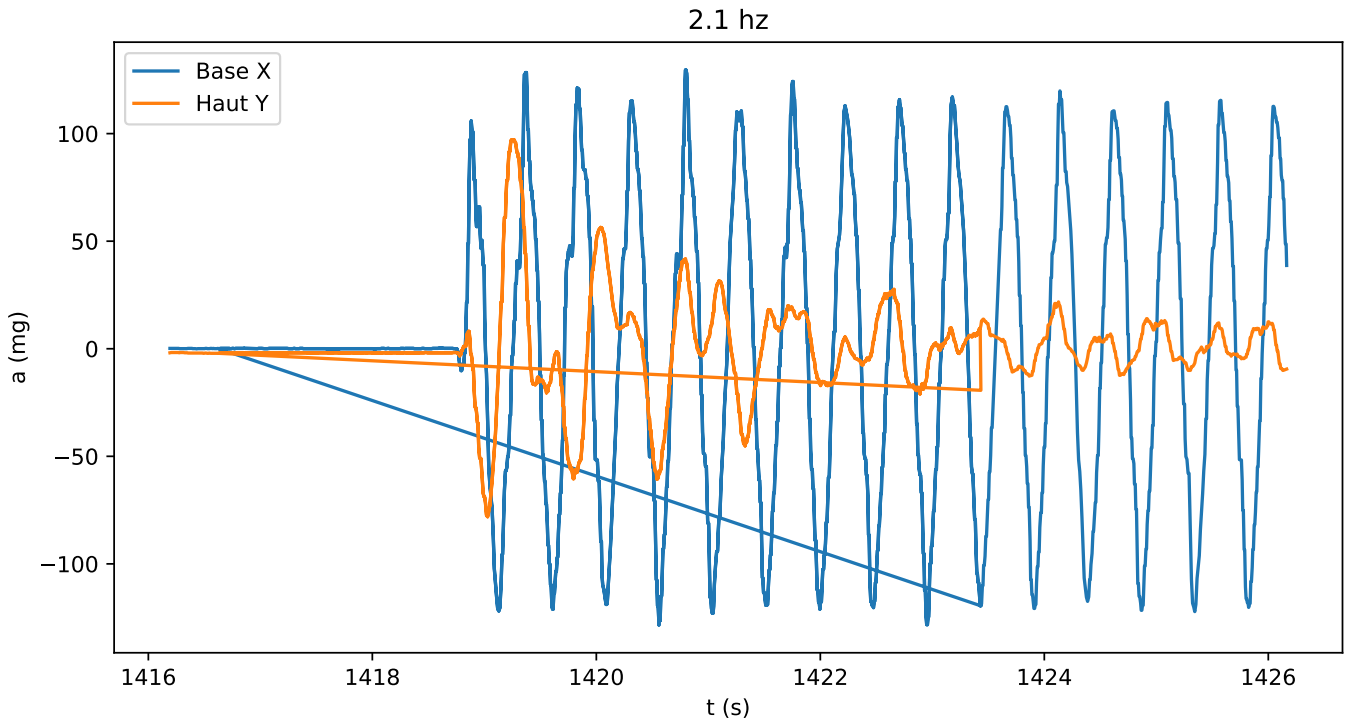
[picture p349: page 1]
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
